skif-ops/rs-zs-bpla/hardware/PCB_MAIN_IPC_CANDIDATE_FOOTPRINTS_REV_A.md

# PCB-MAIN project-controlled IPC candidates — Rev.A

Status: `ROUTING CANDIDATE CONTROLLED / ASSEMBLY DFM REQUIRED / NOT FOR MANUFACTURE`

This control removes workstation-library drift from the three package-only
PCB-MAIN instances. It does not claim that a component manufacturer supplied a
land pattern and it does not waive assembly-house DFM, stencil adaptation,
Review B, DRC or physical process validation.

## U2 — W25Q512JVFIQ package F

Winbond W25Q512JV Rev B is the package authority for the 16-pin 300 mil SOIC
with 1.27 mm pitch. Winbond does not publish a complete PCB/stencil pattern for
package F. The project therefore freezes the KiCad IPC gullwing candidate used
by the reviewed placement snapshot:

- project footprint: `Winbond_W25Q512JV_PackageF_IPC_Candidate`;
- pads 1–8 at X = -4.65 mm and pads 9–16 at X = +4.65 mm;
- pad pitch 1.27 mm, pad size 2.05 x 0.60 mm, R0.15 corners;
- copper, mask and nominal paste are coextensive in the candidate;
- source disposition: `PROJECT_IPC_W25Q512JV_F_KICAD_GULLWING_ASSEMBLER_DFM_REQUIRED`.

Before fabrication release, the selected assembler must check heel/toe/side
allowance against the ordered package tolerance, choose solder-mask expansion
and approve the stencil aperture for the actual paste and stencil thickness.

## U25/U26 — TPD2EUSB30DRTR package DRT0003A

TI `MPDS340` is the package-outline authority. The official TPD2EUSB30 product
data identifies the active-production DRT/SOT-9X3 orderable and requires a
low-stub flow-through USB layout, but the package drawing does not publish a
complete PCB/stencil pattern. The project freezes the reviewed KiCad DRT-3
candidate:

- project footprint: `TI_DRT0003A_IPC_Candidate`;
- pads 1/2 at (-0.35, +0.425)/(+0.35, +0.425) mm;
- ground pad 3 at (0, -0.425) mm;
- all three pads 0.30 x 0.30 mm with R0.075 corners;
- copper, mask and nominal paste are coextensive in the candidate;
- source disposition: `PROJECT_IPC_TI_DRT0003A_KICAD_DRT3_ASSEMBLER_DFM_REQUIRED`.

Before fabrication release, the selected assembler must approve mask and
stencil rules at its minimum feature capability. Review B must additionally
confirm direct flow-through placement, no branch stub, continuous reference
plane and post-route USB differential-impedance/SI evidence.

## Reproducibility and release interlock

The two project files are generated by
`tools/generate_pcb_main_manufacturer_footprints_rev_a.py` and materialized into
the native board by
`tools/materialize_pcb_main_manufacturer_footprints_rev_a.py`. The independent
layout audit checks every pad coordinate, size, layer and status. Any geometry,
MPN, assembler process or USB routing change reopens this control.
