skif-ops/rs-zs-bpla/hardware/PCB_PWR_FOOTPRINT_AUTHORITY_REV_A.md

# Дионея EVT-PRE-20 Rev.A — PCB-PWR footprint authority

Status: `J1/U1/U2/Q1/RSH1/U3/U4/L1/L2/U5 MANUFACTURER LAND/HOLE/STENCIL VERIFIED / TP1-TP10 PROJECT DFT GEOMETRY VERIFIED / LAYOUT USE AUTHORIZED / NOT FOR MANUFACTURE`
Date: 2026-09-12
Board: `PCB-PWR`

## Q1 — Texas Instruments CSD18540Q5B

Controlled footprint: `DioneyaPWR:CSD18540Q5B_DNK`

Primary source: TI CSD18540Q5B data sheet SLPS488B Rev.B,
`https://www.ti.com/lit/ds/symlink/csd18540q5b.pdf`, retrieved SHA-256
`2e43c4a2ac82af8a089be0a9e413282326f8d7857254ac07390b458deca854e0`.

The footprint implements section 7.2 Recommended PCB Pattern and section 7.3
Recommended Stencil Pattern. The drawing is interpreted as the PCB copper view shown
by TI: pins 1–4 are the four right-side pads and pins 5–8 are the contiguous drain
land on the left. This agrees with the data-sheet top-view electrical diagram:
pins 1–3 SOURCE, pin 4 GATE, and pins 5–8 DRAIN.

### Copper authority

| Feature | Frozen geometry, mm |
|---|---:|
| Overall X extent | `-3.456 … +3.456` |
| Overall Y extent | `-2.260 … +2.260` |
| Pads 1–4 | `1.372 × 0.710`, pitch `1.270`, center X `+2.770` |
| Drain land overall | `4.440 × 4.520` envelope |
| Drain base | X `-2.866 … +0.984` |
| Drain lead tabs | `0.590 × 0.710`, pitch `1.270`, left edge `-3.456` |

The contiguous drain land is partitioned into touching same-net KiCad pads so all four
electrical numbers 5–8 remain present without changing the manufacturer copper union.

### Stencil authority

| Aperture group | Count | Size, mm | Placement |
|---|---:|---:|---|
| Drain lead edge | 4 | `0.766 × 0.508` | pitch `1.270` |
| Drain center | 8 | `1.294 × 0.746` | two columns; X gap `0.350`, Y gap `0.300` |
| Pins 1–4 | 4 | `1.072 × 0.562` | pitch `1.270` |

All sixteen paste apertures are explicit paste-only pads. Electrical copper pads carry
no implicit full-area paste opening, preventing accidental loss of TI's segmented
stencil pattern.

## U1 - Texas Instruments LM74700QDBVRQ1

Controlled footprint: `DioneyaPWR:TI_DBV0006A_SOT23-6`

Primary source: TI LM74700-Q1 data sheet SNOSD17G Rev.G, package drawing
DBV0006A `4214840/G` dated 08/2024, PDF pages 33-35,
`https://www.ti.com/lit/ds/symlink/lm74700-q1.pdf`, retrieved SHA-256
`e16b3a8c0023201fafa5825436f5f2dd6f885b92b84e65602b3f50d741c58b6f`.

The six copper lands are `1.10 x 0.60 mm` roundrects with `R0.05`, `0.95 mm`
pitch within each three-pad side and `2.60 mm` row-center separation. The preferred
non-solder-mask-defined treatment is implemented with `0.07 mm` mask expansion.
The drawing's stencil design uses the same `1.10 x 0.60 mm` apertures for a
`0.125 mm` stencil, so copper pads retain `F.Paste` directly.

## U2 - Texas Instruments INA226AIDGSR

Controlled footprint: `DioneyaPWR:TI_DGS0010A_VSSOP10`

Primary source: TI INA226 data sheet SBOS547C Rev.C, package drawing DGS0010A
`4221984/A` dated 05/2015, PDF pages 38-40,
`https://www.ti.com/lit/ds/symlink/ina226.pdf`, retrieved SHA-256
`c9b67f886d4a5241a5e070723f7b61867409eeb27eed768b9cdd9cb17e03ca2d`.

The ten copper lands are `1.45 x 0.30 mm` roundrects with `R0.05`, `0.50 mm`
pitch and `4.40 mm` row-center separation. The preferred non-solder-mask-defined
treatment is implemented with `0.05 mm` mask expansion. The drawing's stencil
design uses equal `1.45 x 0.30 mm` apertures for a `0.125 mm` stencil.

## U5 - Texas Instruments TPS7A2018PDBVR

Controlled footprint: `DioneyaMain:TI_DBV0005A_SOT23-5` (shared audited library)

Primary source: TI TPS7A20 data sheet SBVS338H Rev.H, package drawing DBV0005A
`4214839/K` dated 08/2024, PDF pages 56-58,
`https://www.ti.com/lit/ds/symlink/tps7a20.pdf`, retrieved SHA-256
`663a9ff5bca608643e711652cba00e7b8bf955c0993a9b86fa108d24d58b8ddc`.

The five lands use the same `1.10 x 0.60 mm`, `R0.05`, `0.95 mm` pitch and
`2.60 mm` row-center geometry already controlled for PCB-MAIN. PCB-PWR reuses that
single project footprint and independently audits its geometry and U5 binding.

## U3/U4 — Texas Instruments LMR604403SRAKR

Controlled footprint: `DioneyaPWR:LMR60440_RAK0009A`

Primary source: TI LMR60440 data sheet SNAS877, package drawing RAK0009A
`4229353/J` dated 04/2025, pages 35–37,
`https://www.ti.com/lit/ds/symlink/lmr60440.pdf`, retrieved SHA-256
`d2feebeb32432de6f7d7da1e45d0d7dcad01f0ddd14fc1a403941efb2c0387db`.

The footprint implements the drawing's `EXAMPLE BOARD LAYOUT` and `EXAMPLE
STENCIL DESIGN`. Repeated touching KiCad pads with the same electrical number form
the asymmetric L-shaped lands for pins 1, 3, 5 and 8 without altering the specified
copper union. Pin 2 uses the drawing's solder-mask-defined thermal-land treatment.

### Copper and solder-mask authority

| Feature | Frozen geometry, mm |
|---|---:|
| Pin 1 / pin 3 L-land | `0.600 × 0.345` plus `0.250 × 0.695`; centers X `-0.900/-0.725`, Y `±0.9275/±1.1025` |
| Pin 9 / pin 4 | `0.250 × 0.650`; center X `-0.075`, Y `-1.125/+1.125` |
| Pin 8 / pin 5 L-land | `0.300 × 0.550` plus `0.700 × 0.200`; centers X `+0.700/+0.900`, Y `∓1.175/∓1.000` |
| Pin 7 / pin 6 | `0.650 × 0.250`; center X `+0.875`, Y `-0.525/+0.525` |
| Pin 2 metal under mask | `2.500 × 0.550`; center `0,0` |
| Pin 2 mask opening | controlled stepped polygon, X `-1.200 … +1.200`; left height `0.450`, right height `0.300` |
| Other mask openings | explicit `0.050` expansion around copper |

### Stencil authority

| Aperture group | Count | Geometry, mm |
|---|---:|---:|
| Pin 1 / pin 3 L-land | 4 | `0.560 × 0.345` and `0.210 × 0.695` per L-land |
| Pin 2 thermal land | 2 | `1.100 × 0.410` and `1.100 × 0.300` |
| Pins 4–9 other than L-land split portions | implicit per the TI stencil outline | same as controlled copper pad |

The controlled footprint contains 13 numbered copper primitives, one explicit
paste-free thermal copper land, one custom mask aperture and six explicit paste-only
apertures: 20 KiCad pad/aperture objects in total. Optional thermal vias shown by TI
are deliberately excluded until placement and stack-up are fixed in PCB-PWR Review B.

## J1 - Molex 43045-0213

Controlled footprint: `DioneyaPWR:Molex_43045-0213_MicroFit-2_Vertical`

Primary source: Molex customer drawing SD-43045-005 Rev.G1 dated 2016-08-23,
`https://www.molex.com/content/dam/molex/molex-dot-com/products/automated/en-us/salesdrawingpdf/430/43045/430450213_sd.pdf`,
retrieved SHA-256
`85db6fbcbbd05643bfebded1b14e02911930151d0234b130d3711ee5fde78ec7`.

The exact orderable 43045-0213 is the two-circuit, vertical, through-hole,
gold-contact member of finish column B. The component-side hole field is:

| Feature | Frozen geometry, mm |
|---|---:|
| Circuit 1 | center `(0, 3.00)`, drill `1.02` |
| Circuit 2 | center `(0, 0)`, drill `1.02` |
| Possible polarization pegs | centers `(-3.00, 0)` and `(+3.00, 0)`, NPTH drill `0.94` |
| Contact copper lands | project annulus `1.50` diameter around the manufacturer drill |

Both peg holes are mandatory because Molex note 2 permits assemblies with either one
or both pegs. The manufacturer drawing controls the hole field and 1.57 mm recommended
board thickness. The 1.50 mm contact land diameter is the project fabrication rule,
not a Molex-specified annulus. Final connector orientation, service clearance and
pull/thermal test remain under `DIM-003` and Review B.

## RSH1 - Vishay Dale WSK2512R0100FEA

Controlled footprint: `DioneyaPWR:Vishay_WSK2512_4T_T1.19mm`

Primary source: Vishay WSK2512 data sheet document 30108 Rev. 11-Dec-2023,
`https://www.vishay.com/doc/?30108=`, retrieved SHA-256
`2ee8a9067539bd2cabb08845219bac55d506b1ca892a2dbaeed343dd1ed10cff`.

The selected 10 mOhm part is a true four-terminal, 1 W, 1%, +/-35 ppm/C
Power Metal Strip shunt. The footprint implements the current land-pattern row for
0.005...0.2 Ohm: `a=2.29`, `b=3.30`, `c=0.76`, `d=0.51`, `e=1.70`, `l=3.68 mm`.

| Project pad | Role | Center, mm | Size, mm |
|---|---|---:|---:|
| 1 | source current | `(-2.985, -0.635)` | `2.29 x 2.03` |
| 2 | load current | `(+2.985, +0.635)` | `2.29 x 2.03` |
| 3 | source Kelvin sense | `(-3.280, +1.270)` | `1.70 x 0.76` |
| 4 | load Kelvin sense | `(+3.280, -1.270)` | `1.70 x 0.76` |

At 5 A the shunt produces 50 mV and dissipates 0.25 W, so the 1 W rating provides
the required 4x nominal power margin. Sense traces must leave pads 3/4 independently;
Kelvin routing, copper current density, +70 C temperature rise and reference-meter
calibration remain Review-B controls.

## L1/L2 - Coilcraft XAL7030-472MEC

Controlled footprint: `DioneyaPWR:Coilcraft_XAL7030_472`

Primary source: Coilcraft XAL7030 data sheet document 863, document 863-2 revised
02/25/26, `https://www.coilcraft.com/pdfs/xal7030.pdf`, retrieved SHA-256
`c323552b4c1acd5ad94d13c32783d1d7db3f86ab70a1c58431673aebb96be9f6`.

The selected AEC-Q200 shielded inductor is 4.7 uH +/-20%, DCR 26.1 mOhm typical /
30.0 mOhm maximum, Isat 10.1 A and Irms 6.9 A for 20 C rise. For dash number
`-472`, Coilcraft specifies a 1.40 mm terminal and a 1.58 mm land-pattern width.
The recommended land pattern is two `1.58 x 6.50 mm` pads with `2.94 mm` inner gap,
giving centers at `x=+/-2.26 mm`.

Project pad 1 is the marked start/short lead and is bound to each LMR60440 SW node,
following Coilcraft's lowest-EMI orientation guidance. At 14.6 V / 400 kHz, the
calculated 4 A full-load peaks are about 4.75 A (3.8 V rail) and 4.68 A (3.3 V rail),
both below the 10.1 A saturation rating. Maximum-DCR winding loss is 0.48 W at 4 A;
placement, hot-loop geometry, +70 C thermal evidence, load-step and EMI remain open.

## TP1-TP10 - project DFT probe target

Controlled footprint: `DioneyaPWR:TestPoint_DFT_1.7mm_NoPaste`

Primary source: project PCB-PWR DFT authority. The footprint contains one circular
`1.70 mm` copper target with `0.20 mm` radial solder-mask expansion, producing a
`2.10 mm` opening. It deliberately has no paste aperture and is excluded from BOM and
pick-and-place outputs. The ten schematic instances and their nets are controlled by
`hardware/PCB_PWR_PASSIVE_AUTHORITY_REV_A.csv`; final coordinates, fixture access and
probe-wear validation remain layout/Review-B controls.

## Remaining controls

- TI does not define a Q1 solder-mask expansion in the cited figures; its final mask
  rule remains an assembly-house/DFM control. U3/U4 mask geometry is controlled by
  drawing `4229353/J`.
- U1/U2/U5 use the preferred NSMD option at the maximum expansion shown by their TI
  package drawings. Final solder-mask registration and stencil process capability
  remain assembly-house/DFM controls.
- Drain thermal spreading, via field, current density, gate-loop placement and SOA are
  PCB-PWR layout/Review-B controls.
- J1/U1/U2/Q1/RSH1/U3/U4/L1/L2/U5 and TP1-TP10 placement is not authorized until
  `PCB-PWR.kicad_pcb` is created from the reviewed board outline and mechanical authority.
- Manufacturing release remains blocked until layout DRC, thermal/fault evidence, DFM
  and both review gates pass.
