skif-ops/rs-zs-bpla/hardware/ENVIRONMENT_REV_A.md

# Дионея EVT-PRE-20 Rev.A — environmental baseline

Статус: `LOCKED OPERATING RANGE / TEST EVIDENCE PENDING`
Основание: `DEC-019`.

## 1. Температурный диапазон

- Рабочая температура окружающей среды станции: **−40…+70 °C**.
- Проектный минимальный диапазон хранения изделия: **−40…+70 °C** до уточнения паспортных ограничений конкретной батареи, герметиков, мембран и литейного материала.
- Электронные компоненты, разъёмы и кабельные сборки, находящиеся в температуре корпуса, должны иметь паспортный рабочий диапазон не уже **−40…+85 °C**.
- Компонент с нижней границей выше −40 °C или верхней границей ниже +85 °C не допускается в Rev.A без формального waiver с тепловым/изоляционным обоснованием и отдельным решением.

## 2. Горячий режим +70 °C

Испытание проводится на собранной станции в репрезентативном корпусе при +70 °C ambient. Проверяется worst-case realistic load:

- BG95 передача данных и reconnect/burst;
- GNSS/PPS;
- LoRa профиль RU868;
- BLE service/OTA window;
- запись/чтение NOR и microSD;
- четыре акустических канала, DSP и классификация;
- работа DC/DC PCB-PWR.

Для каждого тепловыделяющего узла фиксируются ambient, case/board temperature, ток, напряжение и оценка junction temperature. Нельзя считать компонент прошедшим только потому, что его datasheet имеет +85 °C предел: необходимо доказать отсутствие превышения внутреннего температурного предела с учетом self-heating.

## 3. Холодный режим −40 °C

После стабилизации изделия при −40 °C проверяются:

- cold boot и повторные power cycles;
- программирование T5838 AAD через `AAD_CFG/THSEL`, AAD wake и переход в полный PDM capture;
- GNSS cold start/PPS и time-trust;
- cellular attach/recovery, если RF fixture позволяет;
- LoRa;
- BLE commissioning;
- NOR/microSD;
- USB service/recovery;
- разъёмы, кабели и отсутствие хрупкого разрушения/потери контакта.

## 4. LiFePO4

Рабочий диапазон станции −40…+70 °C **не означает разрешение заряда LiFePO4 при отрицательной температуре**.

- При температуре элемента ниже 0 °C заряд запрещен по baseline EVT-PRE-20.
- Исключение допускается только для утвержденной батарейной системы с документированным heater/low-temperature charging algorithm и отдельным EVT.
- Разряд/питание станции при низкой температуре допускается только в пределах datasheet выбранной батареи/BMS.
- Температура для charge inhibit должна относиться к элементу/батарейному пакету, а не только к воздуху внутри корпуса.

## 5. Разъемы и кабели

- JST GH MIC connector исключен из Rev.A из-за несоответствия нижней температурной границе проекта.
- Первоначальный 5-contact Pico-Lock также superseded после выявления обязательного T5838 `THSEL` one-wire AAD configuration input.
- MIC Rev.A: Molex Pico-Lock 1.50 mm, **6 circuits**: header `5040500691`, housing `5040510601`, terminal `5040520098`, nominal operating range −40…+105 °C.
- MIC pin 5 = `MIC_WAKE`; pin 6 = shared `AAD_CFG/THSEL`.
- MAIN↔PWR Micro-Fit 3.0 остается допустимым по температуре, но требует pull/current/thermal validation.
- U.FL и готовые coax assemblies выпускаются только после проверки температурного диапазона **всей кабельной сборки**, не только board receptacle.

## 6. Механика и корпуса

Для vacuum casting, 3D-print fallback и будущего injection-molding source package отдельно подтверждаются при −40/+70 °C:

- отсутствие растрескивания, коробления и потери preload;
- работоспособность резьбовых вставок и крепежа;
- сохранение IP-уплотнения и вентиляционной мембраны;
- отсутствие блокировки акустических портов/мембран;
- отсутствие недопустимого изменения RF characteristics;
- кабельные вводы и strain relief.

Материал корпуса нельзя выпустить по одной комнатной FAI-проверке.

## 7. Release gate

Environmental gate считается закрытым только когда:

1. BOM/AVL не содержит деталей с неподходящим температурным диапазоном;
2. `EVT-ENV-COLD`, `EVT-ENV-HOT`, `EVT-ENV-CYCLE`, `EVT-ENV-BATT-COLD` имеют PASS;
3. thermal report содержит реальные температуры и режимы нагрузки;
4. холодный отчет содержит cold-start, `AAD_CFG/THSEL`, WAKE и connector/harness evidence;
5. выбранная батарея/BMS/MPPT имеет подтвержденные температурные правила;
6. изменение компонента, корпуса, кабеля или firmware power profile, влияющее на температуру, инициирует соответствующий retest.
