skif-ops/rs-zs-bpla/hardware/reviews/PCB_MAIN_HIERARCHY_REVIEW_REV_A.md

# PCB-MAIN Rev.A human-readable hierarchy review

Status: `ACCEPTED HIERARCHY ONLY / NOT FOR ROUTING OR MANUFACTURE`

## 1. Scope

This subgate reviews schematic presentation and exact electrical equivalence only.
It does not reopen the signed PCB-MAIN Review A pin/net decision and cannot
authorize PCB routing, fabrication, assembly, Review B or manufacturing release.

Permitted reviewer decision: `ACCEPT_HIERARCHY_ONLY` or `REJECT_HIERARCHY`.

## 2. Controlled candidate

- Pages: 10 A2 landscape sheets — one system overview and nine functional sheets.
- Symbols: 248 total; 247 have physical PCB footprints and `U12` is the logical card.
- PCB pads: 1,066 logical pad numbers and 1,077 physical pad occurrences; seven
  repeated shell-pad numbers on `J6` through `J12` account for 11 additional
  physical occurrences.
- Authority pins: 1,074 total; 905 connected and 169 explicit NC.
- Explicit child-sheet wire stubs: 905.
- Cross-sheet nets: 75 with 168 hierarchical-label participations.
- Root-sheet connection wires: 168.
- Total controlled wire segments: 1,073.
- Pin/net semantic SHA-256:
  `d320bdd98712a65f9736bd520a8f9197d4f53fedb4be3b798086810e7a8f4bf6`.
- Reviewed source commit:
  `9aceca9531f0b9c18679bee1a8050ae7cd94308a` (tree
  `f77848562f0f2c0ff4965ff8474b582cf49b6885`).
- PCB Native Gate
  [#35136239933](https://github.com/skif-ops/rs-zs-bpla/actions/runs/35136239933):
  KiCad `9.0.9`, zero ERC violations on all 10 sheets. Evidence artifact
  [10462359549](https://github.com/skif-ops/rs-zs-bpla/actions/runs/35136239933/artifacts/10462359549),
  ZIP SHA-256
  `8839e26a79f17da3deb342e9e4c5009f4b7eb365a0f04c4cb526f7e5051bc697`.
- ERC JSON SHA-256:
  `d4dc32aa136be917106a4211734ec9ff0e5db903a268a30b4cd4babb004df5c8`.
- Ten-page A2 landscape PDF SHA-256:
  `7e6ef20a989ec66c55b3e1a32de0a914b9e37a6e70cc5835d36f3260b65ff8d9`;
  pages `1/10` through `10/10` were visually checked in order with no clipping
  or visible duplicate root labels.
- CI [#35136240003](https://github.com/skif-ops/rs-zs-bpla/actions/runs/35136240003):
  `PASS` for the reviewed source commit.
- Routing authorized: `false`.
- Manufacturing release: `false`.

## 3. Functional sheets

1. Power entry and rail interface.
2. MCU clocks, reset and straps.
3. PDM audio, AAD and microphone harnesses.
4. GNSS timing, antenna and supervisor.
5. Cellular modem, dual SIM and recovery.
6. LoRa radio control and conducted RF.
7. BLE module, reset, DFU and SWD.
8. Storage, sensors, microSD and tamper.
9. USB service, debug and EOL fixture.

## 4. Machine controls

- [x] Deterministic regeneration of root and all nine child sheets.
- [x] Root-sheet spatial traversal controls KiCad PDF order as pages 1 through 10,
  with short title-block labels bounded inside the printable frame.
- [x] Exact RefDes allocation: every symbol appears once and only once.
- [x] Exact authority pin/net equivalence and explicit NC preservation.
- [x] Exact schematic-to-PCB pad/net comparison for every physical pad, including
  all 11 duplicated shell solder occurrences.
- [x] Release boundary keeps routing and manufacture prohibited.
- [x] Commit-bound KiCad 9 ERC: zero violations on all 10 sheets.
- [x] Commit-bound 10-page A2 schematic PDF archived and visually inspected.
- [x] Source commit SHA, tree SHA, artifact digest, ERC SHA-256 and PDF SHA-256 recorded.
- [x] Independent human hierarchy decision recorded.

## 5. Human review

Reviewer: `Скиф`

Date: `2026-09-16`

Source commit SHA: `9aceca9531f0b9c18679bee1a8050ae7cd94308a`

Reviewed PDF SHA-256: `7e6ef20a989ec66c55b3e1a32de0a914b9e37a6e70cc5835d36f3260b65ff8d9`

Decision: `ACCEPT_HIERARCHY_ONLY`

The decision accepts only the human-readable hierarchy and its exact electrical
equivalence to the retained Review-A pin/net authority. It does not authorize
routing, fabrication, assembly, Review B or manufacturing release.

## 6. Retained blockers

Routing, planes, numeric impedance geometry, native board DRC, STEP/enclosure
clearance, CAM comparison, fabricator stackup acceptance, assembler DFM/stencil
acceptance, Review B and physical EVT remain open.
