skif-ops/rs-zs-bpla/hardware/reviews/PCB_MIC_REVIEW_B_COPPER_RETURN_REV_A.md

# PCB-MIC Rev.A Review B copper-return and decoupling packet

Status: `ECO REQUIRED HISTORY PRESERVED / COPPER RETURN ACCEPTED / REVIEW B OPEN / NOT FOR MANUFACTURE`

This packet records the independent copper-return decision, preserves the baseline
evidence that caused the hold, and defines the bounded PCB-MIC copper ECO. Repeat
Review A is signed against the controlled ECO source and evidence, and the independent
copper-return subgate is accepted. This does not complete Review B or grant
manufacturing release.

## Controlled decision binding

| Item | Controlled value |
|---|---|
| Superseded signed Review-A commit | `3e215e26e0d4cb160b309de3d3fd5a3145a756bf` |
| Superseded native PCB SHA-256 | `aecd1a374b5f66d32a5ae056eb4ad452d68e2a2391e65f6068acc8cad37f2295` |
| Copper decision evidence commit | `cb69c0bbc1457b498ee4f44ee7da1d566033c23f` |
| PCB Native Gate | [run #158](https://github.com/skif-ops/rs-zs-bpla/actions/runs/34840246015) |
| CI | [run #428](https://github.com/skif-ops/rs-zs-bpla/actions/runs/34840245983) |
| Artifact | ID `10345408977`, SHA-256 `f535c183a3feda6b4e2d38a636987b30aacaa0767103bec39379fbf042d95664` |
| Independent measurement | `tools/audit_pcb_mic_copper_return_rev_a.py` |
| Reviewer | `Скиф` |
| Date | `14.09.2026` |
| Decision | `ECO_REQUIRED` |

The decision evidence verified all 62 manifest entries, 10 controlled source hashes
and 27 PCB-MIC output hashes. The vector F.Cu and B.Cu drawings were board-sized,
distinct and bound to the source hash above.

## Baseline blocking finding PCB-MIC-RB-CU-001

The signed baseline source contained a B.Cu GND zone named
`PCB_MIC_BCU_GND_REFERENCE` with zero cached filled polygons. Its KiCad 9.0.9 B.Cu
Gerber contained zero GND regions and only the five explicit GND conductor draws.
The emitted fabrication copper therefore used the long explicit backbone, not the
named zone.

| Baseline routed path | Trace length | Vias | Minimum width |
|---|---:|---:|---:|
| C1.1 to MK1.7 local VDD leg | 1.658011 mm | 0 | 0.300 mm |
| C1.2 to MK1.2 explicit GND return | 22.248973 mm | 2 | 0.160 mm |
| Complete decoupling loop | 23.906984 mm | 2 return vias | 0.160 mm |

Disposition recorded by the reviewer: `ECO_REQUIRED`.

- [x] Inspect the commit-bound F.Cu/B.Cu drawings and machine topology report.
- [x] Confirm that the absent B.Cu region is not intended fabrication copper.
- [x] Reject implicit acceptance based only on zero DRC or connectivity.
- [x] Select `ECO_REQUIRED` and reopen Review A for changed PCB bytes.

## Bounded ECO candidate

The ECO preserves placement, schematic, mechanical outline, holes, component set,
net assignments, via count and signal routing. It changes only the controlled GND
copper model:

1. Remove the non-materialized B.Cu zone from the native board and production generator.
2. Remove the remote B.Cu C1 branch from `(15.25, 13.25)` to `(9.00, 13.25)`.
3. Add one explicit 0.50 mm B.Cu local return from the C1 GND via at
   `(15.25, 13.25)` directly to the microphone-return via at `(15.00, 16.65)`.
4. Generate the board directly with `tools/generate_pcb_mic_clean_rev_a.py`; the
   obsolete zone-fill bypass wrapper is removed.

The local standard-library audit produces these candidate measurements before the
commit-bound KiCad run:

| ECO candidate routed path | Trace length | Vias | Layer length |
|---|---:|---:|---|
| J1.1 to C1.1 supply feed | 15.369931 mm | 2 | F.Cu 3.984774 mm; B.Cu 11.385157 mm |
| C1.1 to MK1.7 local VDD leg | 1.658011 mm | 0 | F.Cu 1.658011 mm |
| C1.2 to MK1.2 explicit GND return | 7.108150 mm | 2 | F.Cu 3.698972 mm; B.Cu 3.409178 mm |
| Complete decoupling loop | 8.766161 mm | 2 return vias | Reduction 15.140823 mm |
| J1.2 to MK1.2 connector return | 28.303419 mm | 2 | F.Cu 3.953418 mm; B.Cu 24.350001 mm |

Geometry checks calculate at least `0.802865 mm` copper-edge clearance from the new
segment to other-net B.Cu copper, against the project `0.2 mm` clearance, and
`2.35 mm` from the new segment edge to the acoustic-hole edge. KiCad 9 DRC and CAM
remain mandatory independent controls.

The project still has no frozen normative maximum for the decoupling loop. These
measurements prove the bounded topology change and regression, but cannot self-sign
Review A or Review B.

## ECO candidate commit-bound evidence

| Item | Controlled value |
|---|---|
| Design commit | `159068f2743904fc366a4a65ede5fee829797ed2` |
| Native PCB SHA-256 | `a292a6ec2be555519a4fcc44f3d6cfdf0bc38a7f214caff6e71786942e3e4031` |
| PCB Native Gate | [run #160](https://github.com/skif-ops/rs-zs-bpla/actions/runs/34850294515), `success` |
| CI | [run #430](https://github.com/skif-ops/rs-zs-bpla/actions/runs/34850294478), `success` |
| Artifact | [ID 10350416547](https://github.com/skif-ops/rs-zs-bpla/actions/runs/34850294515/artifacts/10350416547) |
| Artifact SHA-256 | `cc32b9f7327d9c1c8870c68f70419f96aa83b412973b2d7cde9ded711fb9f31d` |
| KiCad 9.0.9 | ERC `0`; DRC `0`; unrouted `0`; schematic parity `0` |
| Archive verification | 62 manifest entries; 12 controlled source hashes; 27 PCB-MIC output hashes |
| Review-B preflight SHA-256 | `5b5b392aa2c16c731d51a04531d82205e2bb83e12d73b43e8dacf58c647502b6` |
| Copper audit SHA-256 | `05fd68dcfe1f7f65df306e30772ffb253ee4f0cb5b56df00e03020d9e4d1c6b9` |
| F.Cu / B.Cu SVG SHA-256 | `49d0cc972078861b5e790788bc9c36c6c84cf1ab98eec70e93949be74253a20c` / `71f6100685f32c91a9eff8ff784ce6a5e1735044282ce4d80691b32101bfe3ed` |

Independent archive verification matched the GitHub artifact digest, all manifest
entries and both nested source/output hash sets. Regenerating the Review-B preflight
from the extracted artifact produced byte-identical JSON. The B.Cu Gerber contains
zero GND regions and five explicit GND draws, matching the explicit-routing-only
source model.

## Repeat Review A signature

| Item | Controlled value |
|---|---|
| Reviewer | `Скиф` |
| Date | `14.09.2026` |
| Decision | `PASS` |
| Reviewed controlled evidence commit | `e17a86bc78ba979f74c5549b378e94f7f3447fe4` |
| Approved native PCB SHA-256 | `a292a6ec2be555519a4fcc44f3d6cfdf0bc38a7f214caff6e71786942e3e4031` |
| PCB Native Gate | [run #161](https://github.com/skif-ops/rs-zs-bpla/actions/runs/34851983013), `success` |
| CI | [run #431](https://github.com/skif-ops/rs-zs-bpla/actions/runs/34851982915), `success` |
| Artifact | [ID 10350269024](https://github.com/skif-ops/rs-zs-bpla/actions/runs/34851983013/artifacts/10350269024) |
| Artifact SHA-256 | `c54b6669b40fa4de3cd3b0515e4bdb742d90f4ab6f40a789eb1f7bb82dfd19ba` |

The repeat signature accepts the bounded PCB source for Review A. The independent
Review-B copper-return acceptance is recorded below; all other Review-B and external
manufacturing gates remain open.

## Copper-return decision-input evidence

| Item | Controlled value |
|---|---|
| Decision-input evidence commit | `7aeec13aa0c7ba1b3cd9095b800c6d08755912a3` |
| PCB Native Gate | [run #163](https://github.com/skif-ops/rs-zs-bpla/actions/runs/34873892890), `success` |
| CI | [run #433](https://github.com/skif-ops/rs-zs-bpla/actions/runs/34873892866), `success` |
| Artifact | [ID 10360925100](https://github.com/skif-ops/rs-zs-bpla/actions/runs/34873892890/artifacts/10360925100) |
| Artifact SHA-256 | `1986effdd10fdef86d97ffecb139dd7beea13ff699adeff8f481440e74630321` |
| Manifest / source / output verification | `62 / 12 / 27`, no mismatch |
| Review-B preflight | `PASS_INTERNAL_CAM_PREFLIGHT_REVIEW_B_REMAINS_OPEN` |
| Copper disposition | `READY_FOR_INDEPENDENT_HUMAN_COPPER_RETURN_REVIEW` |
| Review-B preflight SHA-256 | `48eb46975dfb5d474332aed3348eb48a001e6d828eb451316673cd1c9e584173` |
| Copper audit SHA-256 | `1641b5eb173698febd57b074d6e2f9dfc85418dadbdae6ca5e59e67e500befd7` |
| Manifest SHA-256 | `696fc45c6982c45780912e2e310882e21d863ff3624d6b2304b74b03a4b7e635` |
| F.Cu / B.Cu SVG SHA-256 | `5e4116ccb976c16d610fbf0d4dc0488836e7b5f91157bdb6560fd55c259f4994` / `3967d710d9523a33bd513ce7bef4799289ddbecda6d2663deedfce7a3cef1f07` |

The direct return is explicit in both source and CAM, the return is reduced by
`15.140823 mm`, the local B.Cu segment is `0.50 mm` wide, other-net copper-edge
clearance is `0.802865 mm` against the `0.2 mm` project rule, and KiCad 9.0.9 reports
zero ERC, DRC, unrouted or schematic-parity findings. Reviewer `Скиф` accepted this
bounded copper-return subgate on `14.09.2026` with decision `ACCEPT_COPPER_RETURN`.

## Post-acceptance commit-bound evidence

| Item | Controlled value |
|---|---|
| Acceptance-state commit | `8aa4a3d21b55956625db643e22436f248f75b258` |
| PCB Native Gate | [run #164](https://github.com/skif-ops/rs-zs-bpla/actions/runs/34878120514), `success` |
| CI | [run #434](https://github.com/skif-ops/rs-zs-bpla/actions/runs/34878120579), `success` |
| Artifact | [ID 10361911939](https://github.com/skif-ops/rs-zs-bpla/actions/runs/34878120514/artifacts/10361911939) |
| Artifact SHA-256 | `960f84ff068ddf881f01008a6844bfbbf7ed8b7f3e1720b73e6dadae11ee863e` |
| Manifest / source / output verification | `62 / 12 / 27`, no mismatch |
| Manifest SHA-256 | `9f8e9c59d60970419370eeb29c2a9d4bb9549a43d2e8a1ea2db28ce482950e59` |
| Review-B preflight SHA-256 | `808779c6957ed8599d5226a94c48a54991806264392509fa1938b48f27056de6` |
| Copper audit SHA-256 | `9fee77cc7ac5f697f32234072cdc74a2e7c9cda5ccd954bd53ed64ea386e6ab0` |
| F.Cu / B.Cu SVG SHA-256 | `a77ce3b8b3cf09f771284acd68c3accc9b9744e5720af8447927fa128c4e0cc1` / `0020c178abf814ec712cd40bb7dfd7e1e30db928ae6ad373153649b8905830ac` |
| Copper disposition | `PASS_HUMAN_ACCEPTED_COPPER_RETURN_SUBGATE_REVIEW_B_REMAINS_OPEN` |

The extracted archive was independently hashed, and regenerating both JSON audits
from it produced byte-identical results. This evidence confirms the recorded copper
acceptance state only. Panelization, DFM, acoustic-stack, physical-EVT, final Review B
and manufacturing release remain open.

## Required next gates

- [x] Commit and push the ECO candidate as one controlled source set.
- [x] KiCad 9 ERC and DRC pass with zero violations and zero unrouted items.
- [x] Commit-bound Gerber confirms explicit-routing-only B.Cu copper with zero GND regions.
- [x] Updated copper SVGs, topology JSON, CAM reports and SHA-256 manifest are archived.
- [x] Repeat Review A is signed against the ECO candidate commit and its archived evidence.
- [x] Repeat the independent copper-return decision within Review B after Review A closes.
- [ ] Complete the remaining panelization, DFM, acoustic-stack and physical-EVT gates.

## Initial ECO decision signature

- Reviewer: `Скиф`
- Date: `14.09.2026`
- Reviewed evidence commit: `cb69c0bbc1457b498ee4f44ee7da1d566033c23f`
- Workflow and artifact: PCB Native Gate `34840246015`, artifact `10345408977`
- Disposition: `ECO_REQUIRED`
- New Review A complete: `true`, signed separately against commit `e17a86bc78ba979f74c5549b378e94f7f3447fe4`
- Review B complete: `false`
- Manufacturing release: `false`

## Copper-return subgate acceptance signature

- Reviewer: `Скиф`
- Date: `14.09.2026`
- Reviewed evidence commit: `7aeec13aa0c7ba1b3cd9095b800c6d08755912a3`
- Approved native PCB SHA-256: `a292a6ec2be555519a4fcc44f3d6cfdf0bc38a7f214caff6e71786942e3e4031`
- Workflow and artifact: PCB Native Gate `34873892890`, artifact `10360925100`
- Disposition: `ACCEPT_COPPER_RETURN`
- Approval scope: `PCB_MIC_REVIEW_B_COPPER_RETURN_SUBGATE_ONLY`
- Copper-return subgate complete: `true`
- Review B complete: `false`
- Manufacturing release: `false`
