skif-ops/rs-zs-bpla/mechanics/3d_print/DESIGN_RULES.md

# Корпус 3D-print - правила проектирования

Статус: `DRAFT / CAD BLOCKED BY OPEN DIMENSIONS`

- Материал-кандидат: ASA или подтверждённый UV-stable PC/ASA; PLA/PETG не являются автоматическим outdoor release.
- Детали должны помещаться в утверждённый профиль FlashForge Adventurer 5M Pro без неуправляемого масштабирования.
- Стенки-кандидаты 3.0 мм, локально усиливаются рёбрами; окончательно после печати, падения и IP test.
- Наружные резьбы не печатаются как единственное сервисное соединение: применяются термовставки/закладные и нержавеющий крепёж.
- Уплотнение service cover выполняется сменной EPDM/silicone gasket в непрерывном пазу.
- Ориентация печати, supports, seam и shrink compensation фиксируются в 3MF/profile и не остаются на усмотрение оператора.
- Mic pod имеет сменную мембрану, water trap и одинаковый акустический путь для всех четырёх каналов.
- Каждая деталь получает part number, material, revision, mass, print time, orientation и post-processing.

Поставочный комплект: parametric source, STEP, STL, 3MF, printer profile, drawing, assembly BOM, print matrix, inspection form и контрольный STL mesh report.
