skif-ops/rs-zs-bpla/mechanics/injection_molding/DESIGN_RULES.md

# Корпус injection molding - правила проектирования

Статус: `DRAFT / TOOLING NOT AUTHORIZED`

- Конструкция отдельна от 3D-print/vacuum casting и выпускается только после DFM производителя пресс-формы.
- Материал-кандидат: UV-stabilized PC/ASA; exact grade, shrink и colour masterbatch замораживаются вместе.
- Номинальная стенка-кандидат 2.5-3.0 мм, по возможности равномерная; ribs и bosses проектируются как доля основной стенки для снижения sink/warp.
- Draft-кандидат не менее 1.5 degree на нетекстурированных поверхностях; texture требует дополнительного draft по DFM.
- Parting line, gates, ejectors, slides, replaceable inserts и steel-safe dimensions явно показаны в tool drawing.
- Gasket land и acoustic membrane seats не располагаются на неконтролируемой parting flash.
- Tool ownership, cavity count, tool steel, guaranteed shots, maintenance, sampling и change control включаются в контракт.
- T0/T1 samples проходят CMM, material confirmation, assembly, IP, UV/climate, RF и acoustic verification до запуска партии.

Поставочный комплект: parametric CAD, STEP, 2D drawing with GD&T, mold-flow/DFM report, tool specification, control plan, first article report и отдельный корпусной BOM.
