skif-ops/rs-zs-bpla/mechanics/vacuum_casting/DESIGN_RULES.md

# Корпус vacuum casting - правила проектирования

Статус: `DRAFT / CAD BLOCKED BY OPEN DIMENSIONS`

- Конструкция отдельна от FDM и injection molding; master и parting line проектируются под силиконовую форму.
- Материал-кандидат: outdoor polyurethane с подтверждёнными UV, temperature, water absorption и dielectric properties.
- Усадка, draft, feed gates, vents и допустимое число отливок задаются конкретным поставщиком и вносятся в drawing.
- Резьбовые и силовые зоны используют закладные; их фиксация и pull-out проверяются на образце.
- Gasket land, sealing pressure и flatness контролируются после полной post-cure.
- Pigment/coating не должен закрывать маркировку, акустические порты и RF зоны.
- Первый master и первые три отливки проходят размерный отчёт, сборку, IP и acoustic channel match.

Поставочный комплект: master STEP, split/parting drawing, material datasheet, shrink table, inserts, trimming jig, inspection drawing, sample report и отдельный корпусной BOM.
