skif-ops/rs-zs-bpla/releases/evt-pre-20/2026-10-02-rev-d5/Заказ_плат_и_монтаж/03_PCB_MAIN_заказ_с_DFM/01_Изготовление_платы/Сверловка_Excellon/drill_report.txt

Drill report for PCB-MAIN_8L_COMPLETE_105_CANDIDATE_REV_B.kicad_pcb
Created on 2026-09-29T22:29:41

Copper Layer Stackup:
    =============================================================
    L1 :  F.Cu                      front
    L2 :  In1.Cu                    in1
    L3 :  In2.Cu                    in2
    L4 :  In3.Cu                    in3
    L5 :  In4.Cu                    in4
    L6 :  In5.Cu                    in5
    L7 :  In6.Cu                    in6
    L8 :  B.Cu                      back

Drill file 'PCB-MAIN_8L_COMPLETE_105_CANDIDATE_REV_B-PTH.drl' contains
    plated through holes:
    =============================================================
    T1  0.150mm  0.0059"  (274 holes))
    T2  0.300mm  0.0118"  (579 holes))
    T3  0.600mm  0.0236"  (4 holes)  (with 4 slots)
    T4  1.020mm  0.0402"  (12 holes))

    Total plated holes count 869

Drill file 'PCB-MAIN_8L_COMPLETE_105_CANDIDATE_REV_B-NPTH.drl' contains
    unplated through holes:
    =============================================================
    T1  0.650mm  0.0256"  (2 holes))
    T2  1.200mm  0.0472"  (12 holes))
    T3  3.000mm  0.1181"  (2 holes))
    T4  3.200mm  0.1260"  (4 holes))

    Total unplated holes count 20
