skif-ops/rs-zs-bpla/docs/evt-mb/РКД_07_Карта_выводов_WeAct_STM32U585CIU6_v0_7.docx

КАРТА ВЫВОДОВ И ИНТЕРФЕЙСОВ

ЗС-БПЛА.007
Редакция 0.7

Статус: OPEN
РС «Дионея» - EVT-MB
2026

Управляемая копия. Аппаратные результаты не считаются выполненными до заполнения протоколов.

# 1 Область действия

Карта относится только к WeAct STM32U585CIU6 для EVT-MB. Серийная STM32U585VIT6Q получает отдельный BSP и отдельную карту после EVT.

# 2 Выводы MCU

Сигнал | Периферия | Pin | AF | Назначение | Условие
MIC_BCLK | SAI1_A | PA8 | AF13 | 4× I2S BCLK | 22–33 Ω у MCU; общий такт
MIC_WS | SAI1_A | PA9 | AF13 | 4× I2S WS | общая кадровая синхронизация
MIC_PAIR_A | SAI1_A | PA10 | AF13 | MIC1+MIC2 DATA | L/R противоположны
MIC_PAIR_B | SAI1_B | PB5 | AF13 | MIC3+MIC4 DATA | L/R противоположны
BG95_TX | USART1_TX | PB6 | AF7 | BG95 MAIN_RXD | через 3,3/1,8 В translator, если EVB не согласует
BG95_RX | USART1_RX | PB7 | AF7 | BG95 MAIN_TXD | через translator
BG95_PWRKEY | GPIO out | PB1 | OD | BG95 PWRKEY | транзистор/open-drain
BG95_RESET_N | GPIO out | PB4 | OD | BG95 RESET | транзистор/open-drain
BG95_STATUS | GPIO in | PB15 | input | BG95 STATUS | проверить домен уровня
BG95_DTR | GPIO out | PB12 | output | BG95 DTR | сон/пробуждение
GNSS_TX | USART2_TX | PA2 | AF7 | GNSS RXD | 3,3 В
GNSS_RX | USART2_RX | PA3 | AF7 | GNSS TXD | 3,3 В
GNSS_PPS | TIM2_CH2 | PB3 | AF1 | GNSS 1PPS | аппаратный input capture
BLE_TX | USART3_TX | PB10 | AF7 | BLE RXD | 3,3 В
BLE_RX | USART3_RX | PB11 | AF7 | BLE TXD | 3,3 В
SPI1_SCK | SPI1 | PA5 | AF5 | SX1262+microSD | ≤8 МГц EVT; общий bus
SPI1_MISO | SPI1 | PA6 | AF5 | SX1262+microSD | общий bus
SPI1_MOSI | SPI1 | PA7 | AF5 | SX1262+microSD | общий bus
LORA_NSS | GPIO out | PB0 | output | SX1262 NSS | отдельный CS
LORA_DIO1 | GPIO EXTI | PB2 | input | SX1262 DIO1 | IRQ
LORA_BUSY | GPIO in | PB8 | input | SX1262 BUSY | timeout обязателен
LORA_RESET | GPIO out | PB9 | output | SX1262 NRESET | активный 0
SD_NSS | GPIO out | PA4 | output | microSD CS | FAT32, карта 32 ГБ
I2C_SCL | I2C2 | PB13 | AF4 | INA226+температура | pull-up 3,3 В
I2C_SDA | I2C2 | PB14 | AF4 | INA226+температура | pull-up 3,3 В
SWDIO | SWD | PA13 | AF0 | ST-Link | не переназначать
SWCLK | SWD | PA14 | AF0 | ST-Link | не переназначать

# 3 Зарезервированные выводы

- PA0 - USER KEY платы; PC13 - USER LED.
- PA11/PA12 - USB FS service/DFU.
- PA13/PA14 - SWD; NRST и VTref всегда доступны.
- USART1 hardware flow control не используется; modem получает AT+IFC=0.

# 4 CubeMX freeze

Периферия | Режим | Параметры
SAI1_A | Master RX | 32 kHz; stereo; 32-bit slot; 24-bit data; DMA circular
SAI1_B | Synchronous Slave RX | sync SAI1_A; identical frame; DMA circular
TIM2 CH2 | Input capture | PB3 rising edge; 32-bit counter
USART1 | Async | 115200 8N1; no flow control; RX circular/IDLE
USART2 | Async | 9600 8N1; RX circular/IDLE
USART3 | Async | 115200 8N1
SPI1 | Full duplex master | mode 0; ≤8 MHz; DMA optional
I2C2 | I2C | 400 kHz; external pull-ups

# Источники и проверка

STM32U585 datasheet AF tables: https://www.st.com/resource/en/datasheet/stm32u585ai.pdf

WeAct board files: https://github.com/WeActStudio/WeActStudio.STM32U585Cx_CoreBoard

ЗС-БПЛА.007 · 0.7 · OPEN
