skif-ops/rs-zs-bpla/releases/evt-pre-20/2026-10-02-rev-d5/Программа_EVT_и_Мухоед/01_Программы_и_формы/Форма_сводного_отчета_EVT.docx

# Форма сводного отчета EVT PRE 20

Дионея · EVT-PRE-20 · 30 сентября 2026 года · Rev D · комплект для закупки, производства и EVT

Форма заполняется после фактических испытаний первого лота. Поля без первичного измерения остаются NOT RUN. Никакие приведённые в программе планы не переносятся в итоговый PASS автоматически.

## Конфигурация

Номер лота: __________. Дата начала и окончания: __________. Ответственный: __________. Ревизии PCB-MAIN, PCB-PWR, PCB-MIC и печатного корпуса: __________. Фактические стеки и ответ фабрики по 76/76 POFV: __________. Хеши firmware, серверной модели и манифеста файлов: __________.

Серийные номера 20 изделий и назначения опытных/разрушающих образцов приводятся в электронном реестре. Любое отступление от BOM, жгута, корпуса и профиля RU868 указывается отдельной записью ECO или deviation.

## Результаты

Сводка EOL: проверено ___ из 20; PASS ___; FAIL ___; NOT RUN ___. Сводка EVT по P0: проверено ___; PASS ___; CONDITIONAL ___; FAIL ___; NOT RUN ___. Ссылки на сырые логи и SHA-256: __________.

Питание, RB40, MPPT и солнечная панель: __________. Четыре PDM канала и порт PCB-MIC: __________. Три антенных тракта и PCB-MAIN RF без контролируемого импеданса: __________. GNSS/PPS и локализация: __________. LTE/TLS, RU868, BLE и store-and-forward: __________. Температура, влажность, IP, вибрация и акустика: __________.

## Отклонения и решение

Открытые blocker/critical: __________. Принятые CONDITIONAL отклонения, владелец и срок: __________. Нерешённые входные данные заказчика: __________. Повтор критических проверок после стресса: __________.

Итоговое решение независимого проверяющего: PASS / CONDITIONAL / FAIL / NOT RUN. Имя, дата, подпись и ссылка на полный evidence manifest: __________.
