skif-ops/rs-zs-bpla/releases/evt-pre-20/2026-10-02-rev-d5/Заказ_плат_и_монтаж/00_Условия_передачи/Опись_и_статус_комплекта.docx

# Опись и статус производственного комплекта EVT-PRE-20

Дионея · EVT-PRE-20 · 30 сентября 2026 года · Rev D

Финальный комплект Rev D для закупки, изготовления плат, монтажа и сборки опытной партии.

## Статус плат

PCB-MAIN: разводка завершена, DRC 0, unconnected 0, ERC 0; выпуск зависит от DFM и подтверждения фабричного stack ID.

PCB-PWR: заказ разрешён заказчиком с обязательной заводской проверкой стека и переходных отверстий.

PCB-MIC Rev B: плата технически принята Review B, DRC/ERC/unconnected 0/0/0, SHA-256 c57cebbb3886247166551fd242fa51350bc9be7fee6299e63e7eaac60518d518. По требованию заказчика все 80 PCBA изготавливаются без паузы; образец выбирается из готовой партии для контроля порта и PDM.

## Состав

Архив плат содержит Gerber, отдельную сверловку, IPC-356, координаты, BOM, KiCad-исходники, PDF схемы/сборки и задания. Полный архив дополнительно содержит закупочную книгу для 41 станции, документы сборки, предварительные модели корпусов, технический проект и отдельные архивы.

Программа EVT и материалы дообучения «Мухоеда» находятся в отдельном архиве. Полный пакет Review B PCB-MIC находится в отдельном архиве и не входит в производственный архив.

## Ограничения первого выпуска

Первая партия корпусов – 20 комплектов 3D-печати; модели предварительные и требуют примерки. Литьевые файлы являются исходными кандидатами для DFM оснастки.

Оценочные цены взяты из ведомости v.02 и не являются коммерческим предложением. Недетализированная сумма около 4 млн ₽ исключена. Перед закупкой получить текущие котировки.

Физические акустические, климатические, RF и корпусные проверки выполняются на собранных изделиях по программе EVT и не блокируют передачу утверждённых файлов фабрике.
