skif-ops/rs-zs-bpla/releases/evt-pre-20/2026-10-02-rev-d5/Заказ_плат_и_монтаж/01_PCB_PWR_заводская_проверка_и_заказ/PCB-PWR_parity_disposition.docx

# PCB-PWR Rev E – диспозиция диагностики схемы

Дионея · EVT-PRE-20 · 30 сентября 2026 года · Rev D

Документ фиксирует разбор 251 диагностического сообщения и производственную трактовку BOM/DNP для Rev D. Физических расхождений связности не обнаружено.

## Итог проверки

171 сообщение относится к разной записи иерархических имён одной и той же цепи; одно сообщение относится к ожидаемому NC выводу U5. Эти записи не меняют связность.

62 сообщения относятся к пустому полю Datasheet на плате; 10 – к различию подробного Value схемы и короткого значения платы. Точные производственные MPN заданы в PCB-PWR_BOM_PCBA.csv и книге BOM XLSX.

Семь сообщений exclude_from_BOM относятся к пяти DNP резисторам и трём медным net tie; часть сообщений объединена по группам. Их производственная диспозиция дана отдельным CSV.

## Правила монтажа

Установить 44 позиции из PCB-PWR_BOM_PCBA.csv по PCB-PWR_pos.csv и двуязычной сборочной схеме. R5, R9, R13, R14 и R15 не устанавливать и не закупать как детали.

NT1, NT2 и NT3 являются рисунком меди платы; отдельные перемычки или компоненты не устанавливаются и не закупаются. TP1–TP10 и H1–H4 также являются элементами печатной платы.

D1 применять как Littelfuse SMBJ18A, однонаправленный TVS. Физическая проверка импульсного режима выполняется в EVT и не разрешает замену MPN без ECO.

## Статус

Диагностика schematic parity закрыта диспозицией для передачи в производство. Фабричный DFM, фактический stack ID, контроль первого изделия и последующие электрические/тепловые испытания выполняются по заданию на платы.

EN: schematic parity diagnostics are dispositioned for manufacturing handoff. Use the exact PCBA BOM, DNP list, position file and bilingual assembly drawing. Fabricator DFM, stack confirmation and post-lot sample tests remain mandatory production controls.
