skif-ops/rs-zs-bpla/releases/evt-pre-20/2026-10-02-rev-d5/Основной_пакет/00_Опись_и_статус/Контроль_финального_выпуска.docx

# Контроль финального выпуска EVT-PRE-20 Rev D

Дионея · EVT-PRE-20 · 30 сентября 2026 года · Rev D

Контрольный лист фиксирует состояние перед передачей закупке и производству.

## Выполнено

PCB-MAIN: DRC 0, незавершённые соединения 0, ERC 0; машинные файлы и исходники включены.

PCB-MIC Rev B: исправлены метки сверления и кольцо MK1, DRC/ERC/unconnected 0/0/0, точные MPN, отдельные PTH/NPTH. Техническое решение Review B подписано; его условие о паузе после первого изделия изменено заказчиком в извещении о единой партии.

PCB-PWR: файлы заказа и DFM включены. Производственный BOM в XLSX/CSV и закупочная сводка для 41 станции включены. Документы и PDF-инструкции для людей выпущены на русском и английском, где это требуется для фабрики.

## Контроль заказа

PCB-MAIN 22, PCB-PWR 22 и PCB-MIC 80 PCBA заказываются и изготавливаются полными партиями без паузы. После изготовления выбрать образцы для углублённого контроля в соответствии с извещением. До панели получить официальный stack ID, DFM и подтверждение 76 POFV PCB-MAIN. Любое изменение файлов оформить ECO.

Корпуса и литьевые модели предварительные; выполнить first article fit, проверку прочности, герметизации и акустики до размножения.

## Решение

Комплект Rev D разрешён к передаче на закупку и производство в указанных управляемых границах. Rev C изъять из обращения.
