skif-ops/rs-zs-bpla/releases/evt-pre-20/2026-10-02-rev-d5/Заказ_плат_и_монтаж/03_PCB_MAIN_заказ_с_DFM/01_Изготовление_платы/PCB-MAIN_Официальная_проверка_JLCPCB_RU_EN.docx

# PCB-MAIN Rev B – проверка по официальным данным JLCPCB

EVT-PRE-20 · 30.09.2026 · плата SHA-256 f828fc6b30afbd64ed67afbee9ed7a5f5cdb9c47c1112722c5a0fe315268665f

# Вывод

Опубликованные возможности JLCPCB покрывают заказной базис: 8 слоёв, 1,6 мм, FR-4, ENIG, 1 oz наружной и 0,5 oz внутренней меди, переходы 0,15/0,25 мм, эпоксидное заполнение с медной крышкой. Это проверка возможностей, а не утверждённый производственный файл конкретного заказа.

# Переходы

На плате 853 перехода. В исходном KiCad 74 помечены filling=yes и capping=yes: 57 внутри SMD-площадок и 17 вне их. Заказной CSV содержит 76 точек: к этим 74 добавлены C6.1 (X41,75 Y30,40) и D11.1 (X80,01 Y20,50), частично попадающие в окна пасты. Для двух добавленных точек также требуется заполнение эпоксидом и медное закрытие. Сверло этих двух переходов 0,15 мм, диаметр 0,25 мм. Выбирать обработку только по диаметру нельзя.

# Порядок заказа

Выбрать 8 слоёв, 1,6 мм, ENIG, наружная медь 1 oz, внутренняя 0,5 oz.

Выбрать опцию минимального перехода 0,15/0,25 мм и процесс POFV: эпоксидное заполнение с медной крышкой.

Передать фабрике заказные CSV и карту 76 переходов. Из них 74 имеют признаки в исходной плате, а C6.1 и D11.1 заданы как CAM-дополнение. Фабрика подтверждает обработку 76 из 76 точек до запуска панели; одно лишь закрытие маской не допускается. При невозможности выборочного POFV изменение согласовать через ECO.

Выбрать стек JLC08161H-3313, если он доступен в заказе, и проверить его действующие толщины/параметры в карточке заказа; при замене стека фиксировать ECO.

Запросить подтверждение производственных файлов до запуска панели и оформить замечания DFM через ECO.

# Границы заключения

JLC08161H-3313 является примером, а не утверждённым стеком заказа. Для EVT сохраняется текущая трассировка без заказа контролируемого импеданса и цели 50 Ом. Фактический стек записывается при DFM. Все 22 PCBA изготавливаются без паузы; два образца из партии проходят ВЧ-испытания. Файлы фабрики проверяются до запуска панели.

EN: JLCPCB publishes the required board and filled-via capabilities. Confirm 76/76 vias before panel release. The EVT PCB stays as routed; controlled impedance and a 50-ohm target are not ordered. Record the chosen stack. Make all 22 PCBAs without a pause; sample two from the completed lot for RF tests. Deviations require lot disposition and ECO.

# Официальные источники / Official sources

Возможности плат (https://jlcpcb.com/capabilities/pcb-capabilities/) | Стек (https://jlcpcb.com/help/article/multi-layer-pcb-standard-laminated-structures) | Переходные отверстия (https://jlcpcb.com/help/article/pcb-via-covering) | 8 слоёв (https://jlcpcb.com/blog/multilayer-pcb-design-guidelines)
