skif-ops/rs-zs-bpla/releases/evt-pre-20/2026-10-02-rev-d5/Заказ_жгутов_и_кабелей/Антенные_тракты_RU_EN.pdf

# Антенные тракты EVT-PRE-20 Rev D / Antenna paths

22 комплекта / sets · 66 CAB.0243 · по 22 антенны каждого типа / 22 antennas of each type

AA.166.A.301111 · SMA(M) · active GNSS · IP67

TI.89.B.2111W · SMA(M) · 860–930 MHz · IP67

### Не менять местами J8/J9/J10 · Do not interchange J8/J9/J10

100%: continuity, no short, connector retention, bulkhead seal, labels, bend radius; then installed VSWR/sensitivity/coexistence tests.

100%: проводимость, отсутствие КЗ, фиксация разъёмов, уплотнение bulkhead, маркировка, радиус изгиба; затем VSWR/чувствительность/coexistence.
