skif-ops/rs-zs-bpla/releases/evt-pre-20/2026-10-02-rev-d5/Заказ_жгутов_и_кабелей/Чертеж_и_распайка_жгутов_RU_EN.pdf

# EVT-PRE-20 Rev D — чертёж и заказ жгутов / Harness drawing and order

Заказ / Order: 22 полных комплекта / complete sets · 30.09.2026 · DIO-HARNESS-SET-EVT-D

# 1. Состав заказа / Order scope

Жгут / Harness | Кол-во / Qty | Цепей / Circuits | Нарезка / Cut | Окончание A / End A | Окончание B / End B
H-MIC1…H-MIC4 | 88 | 6 | 275 ±5 мм | Molex 5040510601 + 5040520098 | Molex 5040510601 + 5040520098
H-MAIN-PWR | 22 | 12 | 440 ±5 мм | Molex 430251200 | Molex 430251200
H-BAT-PWR | 22 | 2 | 330 ±5 мм | TE 8-34114-1 M8 | Molex 430250200 + 430300038

# 2. Обязательные правила / Mandatory rules

Собрать один полный первый комплект, зафиксировать высоту обжима и разрушающее усилие для каждого типа контакта, выполнить 100% проверку распайки, полярности, отсутствия межцепных коротких замыканий и сопротивления. Остальные 21 комплект выпускать после PASS первого комплекта. Build one complete first article, record crimp height and destructive pull for each terminal type, then perform 100% pin-to-pin, polarity, cross-short and resistance testing. Release the remaining 21 sets after first-article PASS.

Предел сопротивления: MIC и MAIN-PWR ≤0,15 Ом на проводник; BAT-PWR ≤0,10 Ом. Маркировать оба конца уникальным Harness_ID и обозначением стороны. Замена провода, контакта, корпуса, цвета или перестановка полостей допускается только по ECO. Resistance limit: MIC and MAIN-PWR ≤0.15 ohm per conductor; BAT-PWR ≤0.10 ohm. Label both ends with Harness_ID and end designation. Wire, terminal, housing, colour or cavity changes require an ECO.

В комплект поставки включить: протокол первого изделия, ведомость партий провода и контактов, применённую оснастку, результаты 100% теста и упаковочный лист. Delivery records: first-article report, wire/terminal lots, tooling identification, 100% test results and packing list.

# 3. MIC: распайка 24 цепей / 24-circuit pinout

ID | Откуда / From | Куда / To | Цепь / Net | Провод / Wire | Цвет / Colour | L, мм | Контакты / Terminals
MIC1-01 | PCB-MAIN J_MIC1_MATING_5040510601:1 | PCB-MIC1 J1_MATING_5040510601:1 | 1V8_MIC | AWG24_TE_55A0111-24_OD0P94MM | RED | 275 ±5 | 5040520098 / 5040520098
MIC1-02 | PCB-MAIN J_MIC1_MATING_5040510601:2 | PCB-MIC1 J1_MATING_5040510601:2 | GND | AWG24_TE_55A0111-24_OD0P94MM | BLACK | 275 ±5 | 5040520098 / 5040520098
MIC1-03 | PCB-MAIN J_MIC1_MATING_5040510601:3 | PCB-MIC1 J1_MATING_5040510601:3 | PDM_CLK | AWG24_TE_55A0111-24_OD0P94MM | WHITE | 275 ±5 | 5040520098 / 5040520098
MIC1-04 | PCB-MAIN J_MIC1_MATING_5040510601:4 | PCB-MIC1 J1_MATING_5040510601:4 | PDM_DATA1 | AWG24_TE_55A0111-24_OD0P94MM | BLUE | 275 ±5 | 5040520098 / 5040520098
MIC1-05 | PCB-MAIN J_MIC1_MATING_5040510601:5 | PCB-MIC1 J1_MATING_5040510601:5 | MIC_WAKE1 | AWG24_TE_55A0111-24_OD0P94MM | VIOLET | 275 ±5 | 5040520098 / 5040520098
MIC1-06 | PCB-MAIN J_MIC1_MATING_5040510601:6 | PCB-MIC1 J1_MATING_5040510601:6 | AAD_CFG | AWG24_TE_55A0111-24_OD0P94MM | GREY | 275 ±5 | 5040520098 / 5040520098
MIC2-01 | PCB-MAIN J_MIC2_MATING_5040510601:1 | PCB-MIC2 J1_MATING_5040510601:1 | 1V8_MIC | AWG24_TE_55A0111-24_OD0P94MM | RED | 275 ±5 | 5040520098 / 5040520098
MIC2-02 | PCB-MAIN J_MIC2_MATING_5040510601:2 | PCB-MIC2 J1_MATING_5040510601:2 | GND | AWG24_TE_55A0111-24_OD0P94MM | BLACK | 275 ±5 | 5040520098 / 5040520098
MIC2-03 | PCB-MAIN J_MIC2_MATING_5040510601:3 | PCB-MIC2 J1_MATING_5040510601:3 | PDM_CLK | AWG24_TE_55A0111-24_OD0P94MM | WHITE | 275 ±5 | 5040520098 / 5040520098
MIC2-04 | PCB-MAIN J_MIC2_MATING_5040510601:4 | PCB-MIC2 J1_MATING_5040510601:4 | PDM_DATA2 | AWG24_TE_55A0111-24_OD0P94MM | YELLOW | 275 ±5 | 5040520098 / 5040520098
MIC2-05 | PCB-MAIN J_MIC2_MATING_5040510601:5 | PCB-MIC2 J1_MATING_5040510601:5 | MIC_WAKE2 | AWG24_TE_55A0111-24_OD0P94MM | VIOLET | 275 ±5 | 5040520098 / 5040520098
MIC2-06 | PCB-MAIN J_MIC2_MATING_5040510601:6 | PCB-MIC2 J1_MATING_5040510601:6 | AAD_CFG | AWG24_TE_55A0111-24_OD0P94MM | GREY | 275 ±5 | 5040520098 / 5040520098
MIC3-01 | PCB-MAIN J_MIC3_MATING_5040510601:1 | PCB-MIC3 J1_MATING_5040510601:1 | 1V8_MIC | AWG24_TE_55A0111-24_OD0P94MM | RED | 275 ±5 | 5040520098 / 5040520098
MIC3-02 | PCB-MAIN J_MIC3_MATING_5040510601:2 | PCB-MIC3 J1_MATING_5040510601:2 | GND | AWG24_TE_55A0111-24_OD0P94MM | BLACK | 275 ±5 | 5040520098 / 5040520098
MIC3-03 | PCB-MAIN J_MIC3_MATING_5040510601:3 | PCB-MIC3 J1_MATING_5040510601:3 | PDM_CLK | AWG24_TE_55A0111-24_OD0P94MM | WHITE | 275 ±5 | 5040520098 / 5040520098
MIC3-04 | PCB-MAIN J_MIC3_MATING_5040510601:4 | PCB-MIC3 J1_MATING_5040510601:4 | PDM_DATA3 | AWG24_TE_55A0111-24_OD0P94MM | GREEN | 275 ±5 | 5040520098 / 5040520098
MIC3-05 | PCB-MAIN J_MIC3_MATING_5040510601:5 | PCB-MIC3 J1_MATING_5040510601:5 | MIC_WAKE3 | AWG24_TE_55A0111-24_OD0P94MM | VIOLET | 275 ±5 | 5040520098 / 5040520098
MIC3-06 | PCB-MAIN J_MIC3_MATING_5040510601:6 | PCB-MIC3 J1_MATING_5040510601:6 | AAD_CFG | AWG24_TE_55A0111-24_OD0P94MM | GREY | 275 ±5 | 5040520098 / 5040520098
MIC4-01 | PCB-MAIN J_MIC4_MATING_5040510601:1 | PCB-MIC4 J1_MATING_5040510601:1 | 1V8_MIC | AWG24_TE_55A0111-24_OD0P94MM | RED | 275 ±5 | 5040520098 / 5040520098
MIC4-02 | PCB-MAIN J_MIC4_MATING_5040510601:2 | PCB-MIC4 J1_MATING_5040510601:2 | GND | AWG24_TE_55A0111-24_OD0P94MM | BLACK | 275 ±5 | 5040520098 / 5040520098
MIC4-03 | PCB-MAIN J_MIC4_MATING_5040510601:3 | PCB-MIC4 J1_MATING_5040510601:3 | PDM_CLK | AWG24_TE_55A0111-24_OD0P94MM | WHITE | 275 ±5 | 5040520098 / 5040520098
MIC4-04 | PCB-MAIN J_MIC4_MATING_5040510601:4 | PCB-MIC4 J1_MATING_5040510601:4 | PDM_DATA4 | AWG24_TE_55A0111-24_OD0P94MM | ORANGE | 275 ±5 | 5040520098 / 5040520098
MIC4-05 | PCB-MAIN J_MIC4_MATING_5040510601:5 | PCB-MIC4 J1_MATING_5040510601:5 | MIC_WAKE4 | AWG24_TE_55A0111-24_OD0P94MM | VIOLET | 275 ±5 | 5040520098 / 5040520098
MIC4-06 | PCB-MAIN J_MIC4_MATING_5040510601:6 | PCB-MIC4 J1_MATING_5040510601:6 | AAD_CFG | AWG24_TE_55A0111-24_OD0P94MM | GREY | 275 ±5 | 5040520098 / 5040520098

# 4. MAIN-PWR и BAT-PWR: распайка 14 цепей / 14-circuit pinout

ID | Откуда / From | Куда / To | Цепь / Net | Провод / Wire | Цвет / Colour | L, мм | Контакты / Terminals
PWR-01 | PCB-PWR J_MAIN_PWR_MATING_430251200:1 | PCB-MAIN J_PWR_MATING_430251200:1 | 3V8_MODEM | AWG18_TE_55A0111-18_OD1P52MM | RED | 440 ±5 | 430300038 / 430300038
PWR-02 | PCB-PWR J_MAIN_PWR_MATING_430251200:2 | PCB-MAIN J_PWR_MATING_430251200:2 | GND_MODEM | AWG18_TE_55A0111-18_OD1P52MM | BLACK | 440 ±5 | 430300038 / 430300038
PWR-03 | PCB-PWR J_MAIN_PWR_MATING_430251200:3 | PCB-MAIN J_PWR_MATING_430251200:3 | 3V3_DIGITAL | AWG18_TE_55A0111-18_OD1P52MM | ORANGE | 440 ±5 | 430300038 / 430300038
PWR-04 | PCB-PWR J_MAIN_PWR_MATING_430251200:4 | PCB-MAIN J_PWR_MATING_430251200:4 | GND_DIGITAL | AWG18_TE_55A0111-18_OD1P52MM | BLACK_WHITE | 440 ±5 | 430300038 / 430300038
PWR-05 | PCB-PWR J_MAIN_PWR_MATING_430251200:5 | PCB-MAIN J_PWR_MATING_430251200:5 | 1V8_MIC | AWG18_TE_55A0111-18_OD1P52MM | BROWN | 440 ±5 | 430300038 / 430300038
PWR-06 | PCB-PWR J_MAIN_PWR_MATING_430251200:6 | PCB-MAIN J_PWR_MATING_430251200:6 | GND_MIC | AWG18_TE_55A0111-18_OD1P52MM | BLACK_BLUE | 440 ±5 | 430300038 / 430300038
PWR-07 | PCB-PWR J_MAIN_PWR_MATING_430251200:7 | PCB-MAIN J_PWR_MATING_430251200:7 | PWR_GOOD | AWG22_ALPHA_3051_OD1P575MM | WHITE | 440 ±5 | 430300001 / 430300001
PWR-08 | PCB-PWR J_MAIN_PWR_MATING_430251200:8 | PCB-MAIN J_PWR_MATING_430251200:8 | FAULT | AWG22_ALPHA_3051_OD1P575MM | YELLOW | 440 ±5 | 430300001 / 430300001
PWR-09 | PCB-PWR J_MAIN_PWR_MATING_430251200:9 | PCB-MAIN J_PWR_MATING_430251200:9 | EN_MODEM | AWG22_ALPHA_3051_OD1P575MM | GREEN | 440 ±5 | 430300001 / 430300001
PWR-10 | PCB-PWR J_MAIN_PWR_MATING_430251200:10 | PCB-MAIN J_PWR_MATING_430251200:10 | EN_AUX | AWG22_ALPHA_3051_OD1P575MM | BLUE | 440 ±5 | 430300001 / 430300001
PWR-11 | PCB-PWR J_MAIN_PWR_MATING_430251200:11 | PCB-MAIN J_PWR_MATING_430251200:11 | I2C2_SCL | AWG22_ALPHA_3051_OD1P575MM | VIOLET | 440 ±5 | 430300001 / 430300001
PWR-12 | PCB-PWR J_MAIN_PWR_MATING_430251200:12 | PCB-MAIN J_PWR_MATING_430251200:12 | I2C2_SDA | AWG22_ALPHA_3051_OD1P575MM | GREY | 440 ±5 | 430300001 / 430300001
BAT-01 | SYSTEM-BAT1 RELION_RB40_M8_POSITIVE:+ | PCB-PWR J_PWR_IN_MATING_430250200:1 | VBAT_PLUS | AWG18_TE_55A0111-18_OD1P52MM | RED | 330 ±5 | TE_8-34114-1_M8 / 430300038
BAT-02 | SYSTEM-BAT1 RELION_RB40_M8_NEGATIVE:- | PCB-PWR J_PWR_IN_MATING_430250200:2 | VBAT_MINUS | AWG18_TE_55A0111-18_OD1P52MM | BLACK | 330 ±5 | TE_8-34114-1_M8 / 430300038

После сборки станции проверить установленную трассу, разгрузку натяжения, PDM/AAD, I²C 100 кГц, падение напряжения и нагрев. After station assembly verify installed routing, strain relief, PDM/AAD, 100 kHz I²C, voltage drop and temperature rise.
