skif-ops/rs-zs-bpla/releases/evt-pre-20/2026-10-02-rev-d5/Основной_пакет/02_Сборка_станций/Корпус_PCB_MAIN_Rev_B_сборка_RU_EN.pdf

# Корпус PCB-MAIN Rev B. Сборка и маркировка

### PCB-MAIN Rev B faceted enclosure. Assembly and marking

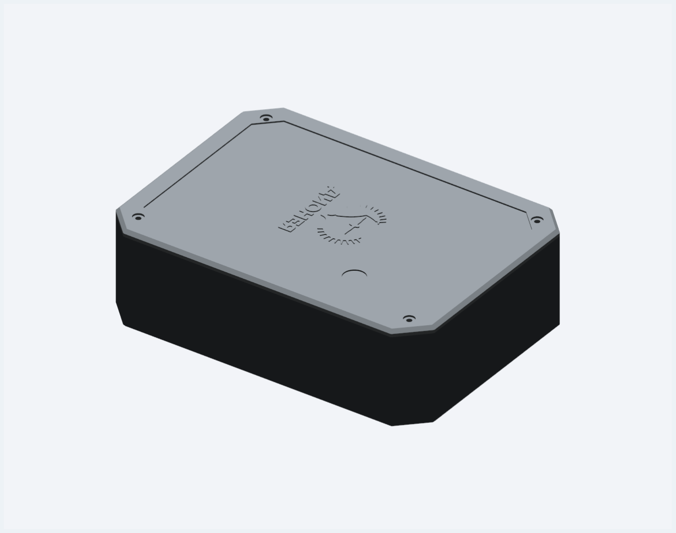
[picture p6: figure]

Фактический CAD по STEP/STL, рельеф утверждённого логотипа

Actual STEP/STL view with approved logo relief

Основание DIO-3DP-UP-001B_body, крышка DIO-3DP-UP-001B_lid.
Body DIO-3DP-UP-001B_body, cover DIO-3DP-UP-001B_lid.

Внешний габарит 200 × 145 × 59 мм. Углы срезаны на 16 мм, кромка крышки скошена на 2 мм.
Outer envelope 200 × 145 × 59 mm. Corners clipped by 16 mm; cover edge bevel is 2 mm.

Логотип из утверждённого DIONEYA_LOGO_STACKED_MONO_RELIEF_REV_A.svg: ширина 48 мм, рельеф 0,6 мм. Цветной SVG приложен для стойкой маркировки.
Approved stacked logo: 48 mm wide, 0.6 mm raised relief. Colour SVG is supplied for durable marking.

Круглая ниша Ø13 на крышке глухая и пока не является индикатором. Не сверлить её без отдельного задания.
The 13 mm circular seat is blind and is not an active indicator. Do not drill without a separate instruction.

Четыре отверстия крышки Ø3,2; резьбовые вставки и длину винтов М3 выбрать после первой примерки.

Four 3.2 mm cover clearances; select M3 inserts and screw length after first fit.

Печатать опытно из ASA или подтверждённого PC/ASA. Прокладка, кабельные вводы, антенны и мачтовый кронштейн требуют примерки.
Trial print in ASA or qualified PC/ASA. Gasket, cable glands, antennas and mast bracket require fit checks.

PCB-MAIN и жгуты сохраняют прежнюю геометрию и длины.

PCB-MAIN and harness geometry and lengths remain unchanged.

Контроль / Checks: плата и разъёмы, доступ к SIM/USB/SD, четыре винта, непрерывное уплотнение, вода/IP, кронштейн и окраска логотипа.

Check real PCBA and connectors, SIM/USB/SD access, four screws, continuous seal, water/IP, bracket and logo marking durability.

Статус: предварительная модель для опытной печати и примерки. Литьевые STEP не являются заданием на пресс-форму.

Status: trial print and fit model. Casting STEP files are not a released mold tooling specification.
