skif-ops/rs-zs-bpla/releases/evt-pre-20/2026-10-02-rev-d5/Заказ_плат_и_монтаж/00_Условия_передачи/ИЗВЕЩЕНИЕ_ПО_ЕДИНОЙ_ПАРТИИ_RU_EN.pdf

Извещение к заказу EVT-PRE-20 Rev D / Rev D order clarification
Дата: | 30.09.2026. | Документ | распространяется | на | переданный
производственный пакет Rev D и уточняет порядок заказа PCB-MAIN, PCB-PWR и PCB-MIC по требованию заказчика.
Решение по объёму и последовательности
Весь объём заказывается сразу: PCB-MAIN 22 PCBA, PCB-PWR 22 PCBA, PCB-MIC 80 PCBA. Изготовление и монтаж каждой партии выполняются без технологической паузы после первых образцов. Формулировки Rev D «сначала 2, затем 20» и «сначала 1, затем 79» в части очередности заменяются этим извещением. Количества, Gerber, сверловка, BOM и координаты не меняются. PCB-MAIN остаётся в текущей трассировке. Для этой партии не заказываются контролируемый импеданс и гарантия 50 Ом. До запуска панели фабрика подтверждает выбранный стек, DFM и эпоксидное заполнение с медным закрытием всех 76 переходов по заказному CSV, включая C6.1 и D11.1.
Невозможность | выполнить | это | требование | или | иное | изменение
производственных файлов требует остановки запуска панели и ECO.
После изготовления из партии выбирают для углублённого контроля два PCB-MAIN, два PCB-PWR и одну PCB-MIC или одну панель. Контроль не является условием запуска остальных плат: вся партия уже изготовлена. При дефекте затронутую партию изолируют, определяют объём проверки и доработки; изменение конструкции оформляют ECO. Условие подписанного Review B PCB-MIC о паузе после первого образца заменено требованием заказчика только в части очередности. Новая подпись технического Review B этим извещением не создаётся.
English order instruction
Place the full order at once: 22 PCB-MAIN, 22 PCB-PWR and 80 PCB-MIC PCBAs. Fabricate and assemble each complete lot without pausing after first articles. Earlier Rev D instructions to make 2 then 20, or 1 then 79, are superseded only for production sequencing. Quantities and manufacturing files remain unchanged. PCB-MAIN stays as routed. Do not order controlled impedance or a guaranteed 50-ohm target for this EVT lot. Before panel release, confirm the selected stack, DFM and epoxy filling with copper capping of all 76 vias in the order CSV, including C6.1 and D11.1. If this cannot be achieved, stop panel release and request an ECO.
After fabrication, select two PCB-MAIN, two PCB-PWR and one PCB-MIC or one panel for enhanced inspection and EVT tests. These checks do not gate fabrication of the rest of the lot. Quarantine and disposition any affected lot if defects are found. The signed PCB-MIC Review B first-article pause is superseded by the customer schedule only; this notice is not a new technical review signature.
