skif-ops/rs-zs-bpla/releases/evt-pre-20/2026-10-02-rev-d5/Ревью_PCB_MIC_отдельно/03_Исправленный_CAM/PCB-MIC_сборка_и_акустический_контроль_RU_EN.pdf

# PCB-MIC Rev B — сборка / assembly

EVT-PRE-20 · 30.09.2026 · управляемый выпуск первого изделия / controlled first-article release

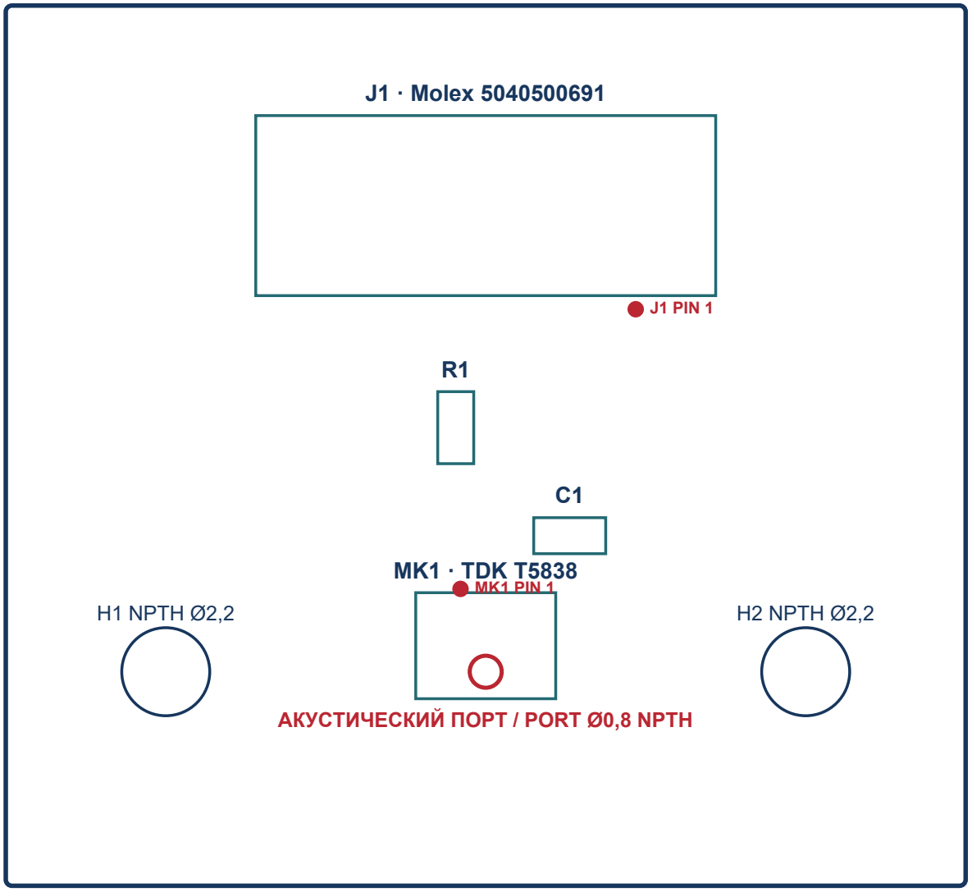
[picture p14: figure]
MK1 · TDK T5838; J1 · Molex 5040500691; H1 NPTH Ø2,2; H2 NPTH Ø2,2; АКУСТИЧЕСКИЙ ПОРТ / PORT Ø0,8 NPTH; J1 PIN 1; MK1 PIN 1

Вид сверху / Top view; Y направлена вниз / Y axis points down Плата / Board: 24 × 22 × 1,0 мм; 2 слоя / layers; 35 мкм / µm; ENIG

1. Установить MK1, J1, C1 и R1 на верхней стороне.

Fit MK1, J1, C1 and R1 on the top side.

2. Проверить pin 1 MK1 и J1 по красным меткам.

Verify MK1 and J1 pin 1 against the red marks.

3. Не наносить пасту, клей или покрытие в порт Ø0,8.

Keep paste, adhesive and coating clear of the Ø0.8 bore.

4. Трафарет MK1: четыре дуги по TDK Fig. 33.

MK1 stencil: four arcs per TDK Figure 33.

5. Первое изделие/панель: AOI или микроскоп + PDM тест.

First board/panel: AOI or microscope inspection plus PDM test.

6. Продолжить остальные 79 PCBA после приёмки первого.

Release the remaining 79 PCBAs after first-article acceptance.

7. Панелизацию выполнять без изгиба зоны MK1.

Panelize and depanel without bending the MK1 area.

СТАТУС / STATUS: REVIEW B ACCEPT · CONTROLLED FIRST ARTICLE · 80 PCBA

Плата / Board SHA-256: c57cebbb3886247166551fd242fa51350bc9be7fee6299e63e7eaac60518d518

Изменение CAM, стека, посадочных мест или трафарета только через ECO / CAM, stack, footprint or stencil changes require ECO.
