skif-ops/rs-zs-bpla/releases/evt-pre-20/2026-10-02-rev-d5/Основной_пакет/02_Сборка_станций/Машинные_таблицы/HARNESS_LOGICAL_PINOUT_REV_A.csv

Interface | Connector_Ref | Pin | Net | Direction_at_MAIN | Nominal_voltage | Current_class | Wire_rule | Shield_pair_rule | Keying_requirement | Release_status | Notes
MIC1 | J_MIC1 | 1 | 1V8_MIC | OUT | 1.8V | LOW | AWG28_or_larger | Route_with_GND | KEYED | LOGICAL_FROZEN | Same 6-pin physical order on all MIC connectors
MIC1 | J_MIC1 | 2 | GND | RETURN | 0V | LOW | AWG28_or_larger | Return_for_1V8_PDM_WAKE_CFG | KEYED | LOGICAL_FROZEN
MIC1 | J_MIC1 | 3 | PDM_CLK | OUT | 1.8V_logic | LOW | AWG28_or_larger | Twist_or_pair_with_GND_if_harness_long | KEYED | LOGICAL_FROZEN | Series damping footprint at source
MIC1 | J_MIC1 | 4 | PDM_DATA1 | IN | 1.8V_logic | LOW | AWG28_or_larger | Twist_or_pair_with_GND_if_harness_long | KEYED | LOGICAL_FROZEN
AAD_WAKE1 | J_MIC1 | 5 | MIC_WAKE1 | IN | 1.8V_logic | LOW | AWG28_or_larger | Route_with_GND_avoid_PDM_clk_crosstalk | KEYED | LOGICAL_FROZEN | T5838 AAD WAKE output preserved for low-power acoustic wake
AAD_CFG1 | J_MIC1 | 6 | AAD_CFG | OUT | 1.8V_one_wire | LOW | AWG28_or_larger | Route_with_GND_avoid_PDM_clk_crosstalk | KEYED | LOGICAL_FROZEN | Common T5838 THSEL one-wire configuration bus; same write applied to all four microphones
MIC2 | J_MIC2 | 1 | 1V8_MIC | OUT | 1.8V | LOW | AWG28_or_larger | Route_with_GND | KEYED | LOGICAL_FROZEN
MIC2 | J_MIC2 | 2 | GND | RETURN | 0V | LOW | AWG28_or_larger | Return_for_1V8_PDM_WAKE_CFG | KEYED | LOGICAL_FROZEN
MIC2 | J_MIC2 | 3 | PDM_CLK | OUT | 1.8V_logic | LOW | AWG28_or_larger | Twist_or_pair_with_GND_if_harness_long | KEYED | LOGICAL_FROZEN
MIC2 | J_MIC2 | 4 | PDM_DATA2 | IN | 1.8V_logic | LOW | AWG28_or_larger | Twist_or_pair_with_GND_if_harness_long | KEYED | LOGICAL_FROZEN
AAD_WAKE2 | J_MIC2 | 5 | MIC_WAKE2 | IN | 1.8V_logic | LOW | AWG28_or_larger | Route_with_GND_avoid_PDM_clk_crosstalk | KEYED | LOGICAL_FROZEN | T5838 AAD WAKE output
AAD_CFG2 | J_MIC2 | 6 | AAD_CFG | OUT | 1.8V_one_wire | LOW | AWG28_or_larger | Route_with_GND_avoid_PDM_clk_crosstalk | KEYED | LOGICAL_FROZEN | Common T5838 THSEL one-wire configuration bus
MIC3 | J_MIC3 | 1 | 1V8_MIC | OUT | 1.8V | LOW | AWG28_or_larger | Route_with_GND | KEYED | LOGICAL_FROZEN
MIC3 | J_MIC3 | 2 | GND | RETURN | 0V | LOW | AWG28_or_larger | Return_for_1V8_PDM_WAKE_CFG | KEYED | LOGICAL_FROZEN
MIC3 | J_MIC3 | 3 | PDM_CLK | OUT | 1.8V_logic | LOW | AWG28_or_larger | Twist_or_pair_with_GND_if_harness_long | KEYED | LOGICAL_FROZEN
MIC3 | J_MIC3 | 4 | PDM_DATA3 | IN | 1.8V_logic | LOW | AWG28_or_larger | Twist_or_pair_with_GND_if_harness_long | KEYED | LOGICAL_FROZEN
AAD_WAKE3 | J_MIC3 | 5 | MIC_WAKE3 | IN | 1.8V_logic | LOW | AWG28_or_larger | Route_with_GND_avoid_PDM_clk_crosstalk | KEYED | LOGICAL_FROZEN | T5838 AAD WAKE output
AAD_CFG3 | J_MIC3 | 6 | AAD_CFG | OUT | 1.8V_one_wire | LOW | AWG28_or_larger | Route_with_GND_avoid_PDM_clk_crosstalk | KEYED | LOGICAL_FROZEN | Common T5838 THSEL one-wire configuration bus
MIC4 | J_MIC4 | 1 | 1V8_MIC | OUT | 1.8V | LOW | AWG28_or_larger | Route_with_GND | KEYED | LOGICAL_FROZEN
MIC4 | J_MIC4 | 2 | GND | RETURN | 0V | LOW | AWG28_or_larger | Return_for_1V8_PDM_WAKE_CFG | KEYED | LOGICAL_FROZEN
MIC4 | J_MIC4 | 3 | PDM_CLK | OUT | 1.8V_logic | LOW | AWG28_or_larger | Twist_or_pair_with_GND_if_harness_long | KEYED | LOGICAL_FROZEN
MIC4 | J_MIC4 | 4 | PDM_DATA4 | IN | 1.8V_logic | LOW | AWG28_or_larger | Twist_or_pair_with_GND_if_harness_long | KEYED | LOGICAL_FROZEN
AAD_WAKE4 | J_MIC4 | 5 | MIC_WAKE4 | IN | 1.8V_logic | LOW | AWG28_or_larger | Route_with_GND_avoid_PDM_clk_crosstalk | KEYED | LOGICAL_FROZEN | T5838 AAD WAKE output
AAD_CFG4 | J_MIC4 | 6 | AAD_CFG | OUT | 1.8V_one_wire | LOW | AWG28_or_larger | Route_with_GND_avoid_PDM_clk_crosstalk | KEYED | LOGICAL_FROZEN | Common T5838 THSEL one-wire configuration bus
MAIN_PWR | J_PWR1 | 1 | 3V8_MODEM | IN | 3.8V | HIGH | AWG18_0.75mm2_Molex430300038 | Dedicated_return_pin_2 | KEYED_LATCH | LOGICAL_FROZEN | Exact selected Micro-Fit power terminal; validate burst current and harness temperature
MAIN_PWR | J_PWR1 | 2 | GND_MODEM | RETURN | 0V | HIGH | AWG18_0.75mm2_Molex430300038 | Dedicated_return_for_3V8 | KEYED_LATCH | LOGICAL_FROZEN | Exact selected Micro-Fit power terminal
MAIN_PWR | J_PWR1 | 3 | 3V3_DIGITAL | IN | 3.3V | MEDIUM | AWG18_0.75mm2_Molex430300038 | Dedicated_return_pin_4 | KEYED_LATCH | LOGICAL_FROZEN | Exact selected Micro-Fit power terminal; conservative common harness standard
MAIN_PWR | J_PWR1 | 4 | GND_DIGITAL | RETURN | 0V | MEDIUM | AWG18_0.75mm2_Molex430300038 | Dedicated_return_for_3V3 | KEYED_LATCH | LOGICAL_FROZEN | Exact selected Micro-Fit power terminal
MAIN_PWR | J_PWR1 | 5 | 1V8_MIC | IN | 1.8V | LOW | AWG18_0.75mm2_Molex430300038 | Dedicated_return_pin_6 | KEYED_LATCH | LOGICAL_FROZEN | Remain powered while T5838 AAD monitoring is armed; exact selected Micro-Fit power terminal
MAIN_PWR | J_PWR1 | 6 | GND_MIC | RETURN | 0V | LOW | AWG18_0.75mm2_Molex430300038 | Dedicated_return_for_1V8 | KEYED_LATCH | LOGICAL_FROZEN | Exact selected Micro-Fit power terminal
MAIN_PWR | J_PWR1 | 7 | PWR_GOOD | IN | 3.3V_logic | LOW | AWG20_to_24_Molex430300001 | Pair_with_logic_ground_if_needed | KEYED_LATCH | LOGICAL_FROZEN | Control terminal 430300001; power-side output to MAIN
MAIN_PWR | J_PWR1 | 8 | FAULT | IN | 3.3V_logic | LOW | AWG20_to_24_Molex430300001 | Pair_with_logic_ground_if_needed | KEYED_LATCH | LOGICAL_FROZEN | Control terminal 430300001; aggregate power-side fault/alert output to MAIN
MAIN_PWR | J_PWR1 | 9 | EN_MODEM | OUT | 3.3V_logic | LOW | AWG20_to_24_Molex430300001 | Pair_with_logic_ground_if_needed | KEYED_LATCH | LOGICAL_FROZEN | Control terminal 430300001; default safe OFF
MAIN_PWR | J_PWR1 | 10 | EN_AUX | OUT | 3.3V_logic | LOW | AWG20_to_24_Molex430300001 | Pair_with_logic_ground_if_needed | KEYED_LATCH | LOGICAL_FROZEN | Control terminal 430300001; controls auxiliary rails policy while AAD requires 1V8_MIC available
MAIN_PWR | J_PWR1 | 11 | I2C2_SCL | BIDIR_OD | 3.3V_logic | LOW | AWG20_to_24_Molex430300001 | Route_with_GND_DIGITAL_keep_short | KEYED_LATCH | LOGICAL_FROZEN | 100 kHz Rev.A power/sensor I2C; pull-ups are on PCB-MAIN; INA226 is on PCB-PWR
MAIN_PWR | J_PWR1 | 12 | I2C2_SDA | BIDIR_OD | 3.3V_logic | LOW | AWG20_to_24_Molex430300001 | Route_with_GND_DIGITAL_keep_short | KEYED_LATCH | LOGICAL_FROZEN | 100 kHz Rev.A power/sensor I2C; pull-ups are on PCB-MAIN; INA226 address 0x40
SWD | J_SWD | 1 | VTREF | IN | 3.3V | LOW | Fixture_pogo_or_AWG28 | No_shield | KEYED_OR_FIXTURE | LOGICAL_FROZEN
SWD | J_SWD | 2 | SWDIO | BIDIR | 3.3V_logic | LOW | Fixture_pogo_or_AWG28 | Short | KEYED_OR_FIXTURE | LOGICAL_FROZEN
SWD | J_SWD | 3 | SWCLK | IN | 3.3V_logic | LOW | Fixture_pogo_or_AWG28 | Short | KEYED_OR_FIXTURE | LOGICAL_FROZEN
SWD | J_SWD | 4 | NRST | IN | 3.3V_logic | LOW | Fixture_pogo_or_AWG28 | Short | KEYED_OR_FIXTURE | LOGICAL_FROZEN
SWD | J_SWD | 5 | GND | RETURN | 0V | LOW | Fixture_pogo_or_AWG28 | Reference | KEYED_OR_FIXTURE | LOGICAL_FROZEN
PWR_INPUT | J_PWR1_IN | 1 | VBAT_PLUS | IN | 10.0_to_14.6V_provisional | HIGH | AWG18_0.75mm2_Molex430300038 | Dedicated_return_pin_2 | KEYED_HIGH_CURRENT | LOGICAL_FROZEN | Selected Micro-Fit terminal is 18 AWG only; 5 A capture envelope and final thermal/fault review required
PWR_INPUT | J_PWR1_IN | 2 | VBAT_MINUS | RETURN | 0V | HIGH | AWG18_0.75mm2_Molex430300038 | Dedicated_return_for_VBAT | KEYED_HIGH_CURRENT | LOGICAL_FROZEN | Selected Micro-Fit terminal is 18 AWG only; final connector thermal test required
