skif-ops/rs-zs-bpla/releases/presentation/v0.3/README.md

# Презентация проекта «Дионея» v0.3

В презентации добавлена схема размещения станций вдоль дороги наряду с круговым объектом, применена зелёно-бирюзовая цветовая модель, добавлен утверждённый логотип и уточнён статус EVT-MB.

Восстановление файла:

```bash
../../reassemble.sh parts Дионея_презентация_проекта_v0_3.pptx
sha256sum -c PRESENTATION_SHA256.txt
```
