skif-ops/rs-zs-bpla/releases/audio/2026-09-07/README.md

# Диагностический прогон «Мухоеда», 07.09.2026

Во всех трех исходных записях присутствие БПЛА подтверждено пользователем.

- результат детекции: 3/3 TRUE_POSITIVE;
- положительные окна: 15/15;
- первое решение: не позднее 2,0 с;
- operational type: UNKNOWN во всех трех случаях;
- набор не содержит отрицательных записей, поэтому FAR по нему не оценивается.

Архив разделен на шестнадцать бинарных частей. Ожидаемый SHA-256 восстановленного ZIP: `84b9ad6cead103ce19abc94ca49f222ac863133113549e228708a70ab1364466`.
