skif-ops/rs-zs-bpla/releases/evt/v0.7/README.md

# Полный EVT, gate 3+1 v0.7

Этот комплект относится к полноценному EVT изделия и не заменяет макетный комплект EVT-MB.

- архив: `РС_ЗС-БПЛА_EVT_gate_3plus1_v0_7.zip`;
- SHA-256: `37eaee4e85e8f12f26da3fbd3a7c40d4cda19c9192dca2e5bb30963435747e6c`;
- размер: 381675 байт;
- статус: OPEN;
- аппаратный EVT не выполнен.
