skif-ops/rs-zs-bpla/android/REQUIREMENTS_v0_1.md

# Android commissioning app - требования v0.1

Статус: `DRAFT / OPEN`

## Функциональные требования

- AND-F-001: обнаруживать только станции в физически активированном service mode.
- AND-F-002: связывать BLE identity с QR/serial до чтения или изменения конфигурации.
- AND-F-003: показывать serial, station_id, HW revision, FW/bootloader version и region.
- AND-F-004: настраивать APN, порядок RAT, roaming policy, MQTT/HTTPS endpoint и CA reference.
- AND-F-005: проверять формат адресов, диапазоны и обязательные поля до записи.
- AND-F-006: применять конфигурацию атомарно, считывать обратно и сравнивать hash/version.
- AND-F-007: запускать self-test питания, GNSS/PPS, cellular attach/TLS, LoRa receive-only, storage и microphones.
- AND-F-008: импортировать offline OTA bundle, не изменяя его содержимое.
- AND-F-009: проверять совместимость HW, anti-rollback, hash и цифровую подпись до передачи.
- AND-F-010: поддерживать resume OTA после обрыва BLE и экрана/процесса приложения.
- AND-F-011: показывать A/B trial, confirmation и rollback reason.
- AND-F-012: экспортировать redacted diagnostic report и commissioning record.
- AND-F-013: не позволять пользователю менять manufacturing region RU868/EU868.
- AND-F-014: выдавать пошаговую инструкцию USB-C recovery без хранения recovery secrets.
- AND-F-015: показывать наличие SIM1/SIM2, redacted ICCID, активный слот, оператора, RAT и результат последнего attach.
- AND-F-016: настраивать упорядоченные публичные APN profiles и preferred SIM slot без экспорта PIN/PUK/APN password; private APN для EVT-PRE-20 отклонять.
- AND-F-017: разрешать ручное переключение SIM/APN только авторизованной роли, с явным предупреждением о разрыве связи и сохранением audit record.
- AND-F-018: показывать причину автоматического failover, предыдущий и новый профиль, число попыток и состояние store-and-forward.
- AND-F-019: иметь обязательный шаг `Координаты установки` до перевода EVT-PRE-20 в FIELD_READY.
- AND-F-020: поддерживать четыре источника координат установки: ручной ввод, location телефона через стандартный Android framework API, текущий GNSS fix станции и заранее известные/геодезические координаты.
- AND-F-021: не требовать Google Play Services для получения координат телефона; ручной ввод всегда доступен.
- AND-F-022: валидировать latitude, longitude, altitude MSL, declared accuracy и source до записи.
- AND-F-023: показывать одновременно устанавливаемые координаты, текущий GNSS станции и горизонтальное расхождение между ними.
- AND-F-024: записывать `installation_position` и `position_trust_policy` атомарно через authenticated BLE, затем выполнять read-back и сравнение version/hash.
- AND-F-025: после подтверждения блокировать координаты установки; изменение допускается только в новом физическом service mode авторизованной ролью и создаёт audit record.
- AND-F-026: показывать GNSS integrity: fix, satellites, HDOP/accuracy, jam, spoof detector state, position delta, position trust, time trust и PPS/holdover state.
- AND-F-027: при GNSS drift/spoofing явно показывать, что сервер и станция продолжают использовать `Установленные координаты`, а GNSS position считается диагностическим.
- AND-F-028: commissioning record должен содержать serial, installation coordinates, altitude, accuracy, source, configuration version/hash, HW/FW/app versions и факт coordinate lock без секретных данных.
- AND-F-029: не предоставлять удалённый/обычный UI-путь изменения installation coordinates вне физического service mode.
- AND-F-030: после изменения координат требовать повторный position/GNSS/PPS self-test и только затем снимать `REVALIDATION_REQUIRED`.

## Нефункциональные требования

- AND-N-001: работа без Google Play Services.
- AND-N-002: работа без интернета после загрузки APK и OTA bundle.
- AND-N-003: интерфейс на русском; английская локализация обязательна до China factory use.
- AND-N-004: поддержка arm64-v8a, кандидат minimum Android 9.
- AND-N-005: отсутствие analytics, advertising SDK и скрытой телеметрии.
- AND-N-006: reproducible release build, dependency lock, SBOM и SHA-256.
- AND-N-007: APK подписывается отдельным Android release key; firmware signing key не используется.
- AND-N-008: crash/log export не содержит PIN, APN password, TLS private key, QR secret, полного ICCID/IMSI.
- AND-N-009: critical actions требуют явного подтверждения и отображают station serial.
- AND-N-010: все ошибки имеют recoverable state или понятный переход к USB-C recovery.
- AND-N-011: приложение не должно требовать интернет-карты для commissioning координат; отображение карты может быть добавлено позже как необязательная функция.
- AND-N-012: при использовании location телефона приложение запрашивает только необходимое runtime permission и не сохраняет историю перемещений оператора.

## Не входит в первую версию

- постоянная онлайн-карта объектов и постоянный мониторинг;
- облачная учётная запись пользователя;
- изменение классификационных моделей отдельно от подписанного release bundle;
- доступ к API оператора;
- одновременная работа двух SIM;
- ручная установка RF frequency/power;
- извлечение private keys станции;
- Wi-Fi/BSSID geolocation как резерв координат станции.

## Gate

Требования получают `LOCKED` после утверждения UX двух ролей, GATT prototype, security review, проверки минимум на трёх смартфонах включая устройство Huawei без GMS и совместного теста с target firmware.

Для EVT-PRE-20 обязательны отдельные acceptance tests: manual/phone/station-GNSS coordinate commissioning, invalid-coordinate rejection, read-back/hash/lock, power-cycle retention, GNSS drift indication, spoof/jam display, revalidation after coordinate change и подтверждение того, что effective station position не изменяется вслед за GNSS drift.

## Host evidence

Для AND-F-006/022/024/025 реализован Kotlin domain contract: те же 58 bytes и
SHA-256 known-answer, что в portable firmware, uint32 version bound, monotonic
recommission, installer/default-policy и service-engineer/custom-policy,
сравнение всех read-back полей, storage generation, hash и audit committed.
QG-1/QG-2 и JVM unit tests не закрывают BLE UUID/pairing/GATT, физическое
10-минутное окно или совместный тест со станцией.
