skif-ops/rs-zs-bpla/hardware/DUAL_SIM_SINGLE_STANDBY.md

# Дионея EVT-PRE-20 - Dual SIM Single Standby

Статус: `ELECTRICAL AUTHORITY CONTROLLED / PCB REVIEW A NOT STARTED / NOT FOR MANUFACTURE`

Точная машинная карта выводов и безопасных состояний: `hardware/PCB_MAIN_DUAL_SIM_PIN_AUTHORITY_REV_A.csv`. Обоснование и первичные документы: `hardware/PCB_MAIN_DUAL_SIM_AUTHORITY_REV_A.md`.

## 1. Принятое решение

`PCB-MAIN` содержит два физических nano-SIM разъёма и один модем Quectel BG95-M3-класса. Одновременно к модему подключается только один слот. Переключение выполняется внешним 2:1 мультиплексором под управлением STM32U585.

Пилотные кандидаты: МТС, МегаФон, Билайн, T2/Tele2 и SIM, предоставленная оператором ГЛОНАСС. Для каждой установленной SIM в профиле фиксируются ICCID, фактический сотовый оператор и публичный APN. Тариф не является входом или критерием EVT.

## 2. Ограничение BG95

BG95 предоставляет один внешний 1.8 В USIM-интерфейс: `USIM_VDD`, `USIM_RST`, `USIM_CLK`, `USIM_DATA`, `USIM_GND` и `USIM_DET`. Поэтому две карты не могут работать одновременно. Режим проекта: `Dual SIM Single Standby`.

Опциональная eSIM BG95 и внешняя SIM также не используются одновременно. Для EVT-PRE-20 базовая комплектация использует два физических nano-SIM слота. Посадочное место eSIM не включается автоматически и требует отдельного ECN.

## 3. Зафиксированная электрическая схема

| Узел | Решение | Статус |
|---|---|---|
| SIM1 | J6, TE `2336582-1`, 4FF push-push, отдельный `SIM1_DET` | TECHNICALLY_SELECTED_PROCUREMENT_RISK |
| SIM2 | J7, TE `2336582-1`, 4FF push-push, отдельный `SIM2_DET` | TECHNICALLY_SELECTED_PROCUREMENT_RISK |
| U13 | TI `TS3A27518EPWR`, TSSOP-24, 6-канальный 2:1 двунаправленный мультиплексор | SELECTED_PENDING_USIM_SI_SAMPLE |
| Управление | `SIM_MUX_SEL` напрямую; `SIM_MUX_EN` через Q3 `MMBT3904,215` на active-HIGH High-Z U13 EN | ELECTRICALLY_LOCKED |
| Интерфейс | 1.8 В; три канала U13 параллельно коммутируют VDD, остальные каналы коммутируют RST, CLK и DATA | ELECTRICALLY_LOCKED |
| ESD | U14/U15 `ESDALC6V1-5P6`, по пять защищённых линий на слот | SELECTED_PENDING_ESD_SI_SAMPLE |

U13 питается от `3V3_DIGITAL`. При таком питании гарантированный максимум сопротивления одного канала равен 7.6 Ом, а трёх параллельных VDD-каналов не более 2.54 Ом. До Review A обязательны измерение напряжения на контакте C1, проверка утечки, ёмкости, фронтов CLK/DATA и поведения при сбросе и отключении модема.

U13 EN имеет 47 кОм к `3V3_DIGITAL`. Q3 только по явной команде `SIM_MUX_EN=HIGH` тянет EN в LOW и включает выбранный слот. Сброс MCU, brownout или `SIM_MUX_EN=LOW` оставляют U13 в High-Z.

## 4. Правила разводки

- оба SIM-разъёма и U13 размещаются максимально близко к BG95;
- длина каждого пути от BG95 до карты не превышает 200 мм и должна быть существенно меньше при фактической компоновке;
- CLK, DATA и RST разводятся вдали от cellular RF, LoRa, DC/DC и силовых петель;
- VDD и GND имеют ширину не менее 0.5 мм до уточнения токов и stackup;
- у каждого слота устанавливаются 100 нФ между VDD и `GND_MODEM`, U14/U15 у разъёма, заполненные 0 Ом последовательные tuning-позиции и DNP-позиции 33 пФ на RST/CLK/DATA;
- `SIM1_DET` и `SIM2_DET` идут на отдельные MCU GPIO и не объединяются;
- каждый DET имеет 10 кОм pull-up к `3V3_DIGITAL`, 10 нФ к `GND_MODEM` и firmware debounce не менее 20 ms;
- доступ к картам допускается только под сервисной крышкой;
- замена SIM при работающем изделии запрещена эксплуатационной инструкцией.

## 5. Безопасное переключение

1. Запретить новые сетевые транзакции и сохранить очередь событий.
2. Закрыть MQTT/HTTPS, выполнить detach и штатно выключить BG95.
3. Дождаться `CELL_STATUS=LOW`, установить `SIM_MUX_EN=LOW`, проверить `U13_EN_N=HIGH` и отключить `EN_MODEM`.
4. Установить `SIM_MUX_SEL` при U13 High-Z.
5. Включить `EN_MODEM`, дождаться стабильного `PWR_GOOD` и выдержать не менее 30 мс.
6. Установить `SIM_MUX_EN=HIGH`, проверить `U13_EN_N=LOW`, затем подать 700 мс PWRKEY pulse.
7. Дождаться `CELL_STATUS=HIGH`, считать ICCID и сверить его с разрешённым профилем слота.
8. Выполнить attach, DNS и TLS-проверку endpoint.
9. Возобновить передачу очереди с прежними `event_id` и sequence.

Переключение без полного штатного выключения модема является ошибкой. При brownout активный слот считается неизвестным до повторного чтения ICCID.

## 6. Public APN

В пилотной партии разрешены только профили `PUBLIC`: обычный публичный APN, исходящий MQTT/TLS или HTTPS/TLS и работа за CGNAT. Для каждой SIM хранится упорядоченный набор разрешённых публичных профилей.

Private APN не настраивается, не выбирается автоматически и не входит в испытания EVT-PRE-20. Его возможное добавление после пилота требует отдельного решения, изменения требований и регрессионных испытаний. APN-пароли, PIN/PUK и TLS private keys не хранятся в Git.

## 7. Failover

Failover допускается по причинам: attach timeout, ошибка PDP context, DNS, TLS, длительная потеря канала или команда авторизованного оператора. Циклическое переключение ограничивается числом попыток и минимальным временем удержания профиля, чтобы исключить дребезг между сетями.

Приоритет по умолчанию задаётся при provisioning отдельно для каждой станции. Автоматический выбор по имени оператора без сверки ICCID и разрешённого профиля запрещён.

Точные RefDes, заказные MPN, population и физические цепи всех пассивных компонентов dual-SIM зафиксированы `MAIN-AUTH-010`; механика и южная сервисная ориентация J6/J7 зафиксированы `MAIN-AUTH-011`. Проверка посадки крышки и карт остаётся физическим блокером.

## 8. Обязательные проверки

- ESD и signal integrity обоих слотов;
- холодный старт и 100 циклов переключения SIM1/SIM2;
- корректность ICCID и slot mapping;
- отсутствие повреждения SIM при отказе питания в каждой фазе переключения;
- attach с тестовой SIM каждого заявленного оператора;
- публичный APN каждой установленной SIM, MQTT/TLS и HTTPS/TLS;
- отклонение попытки настроить или активировать private APN;
- восстановление store-and-forward без потери и неконтролируемых дублей;
- потребление в active, sleep, PSM и при отключённом мультиплексоре;
- невозможность переключения без авторизации через BLE или сервер.

## 9. Первичные источники

- Quectel BG95 Series Hardware Design V1.6, раздел 3.9: https://forums.quectel.com/uploads/short-url/uBwfe2DevTKvtaEsvNDChHNrMER.pdf
- Quectel BG95 product page: https://www.quectel.com/product/lpwa-bg95-cat-m1-cat-nb2-egprs-series/
- TI TS3A27518E: https://www.ti.com/lit/ds/symlink/ts3a27518e.pdf
- ST ESDALC6V1-5P6: https://www.st.com/resource/en/datasheet/esdalc6v1-5p6.pdf
- TE 2336582-1: https://www.te.com/en/product-2336582-1.html
