skif-ops/rs-zs-bpla/BRANCHING.md

# Правила ветвления проекта

## main

Содержит только срез, прошедший локальные проверки и CI. Прямые экспериментальные изменения сюда не вносятся. Текущий статус аппаратной части сохраняется OPEN, пока не выполнены физические испытания.

## develop

Интеграционная ветка. В ней объединяются проверенные feature-ветки, актуальный сервер «Мухоед», целевые профили станции, аппаратные таблицы, механические исходники, манифесты и проверочные результаты.

## evt

Ветка полного EVT изделия. Она не является инструкцией по сборке макетной станции. В нее входят общая программа испытаний, методики, формы протоколов и материалы gate для архитектуры 3+1.

## evt-mb

Ветка макетного EVT. Зафиксированы WeAct STM32U585CIU6, паяная перфоплата, разъемные жгуты, одна станция и один сервер для первого стендового этапа, развертывание Windows 11 и Ubuntu 24.04, а также сопряжение с «Мухоедом».

## evt-pre-20

Ветка предсерийного EVT на 20 станций с собственными PCB, отдельной конфигурационной
базой, производственным маршрутом и доказательствами испытаний. Поставочные материалы
и runtime-маркировка `evt-mb` сюда не переносятся.

## Продвижение изменений

1. Feature-ветка проверяется самостоятельно.
2. Изменение включается в `develop`.
3. Для `develop` должны завершиться CI и проверка манифестов.
4. Проверенный SHA продвигается в `main` без изменения дерева.
5. EVT-ветки получают только материалы своей конфигурации.
6. Между `evt-pre-20` и `evt-mb` запрещены merge, cherry-pick и копирование release/evidence.
7. Общие проверенные изменения разрешено отдельно продвигать в `develop` и `main`.

Начиная с `DIONEA-INTEGRATION-v0.8`, снят временный запрет на обновление `develop` и
`main`. После двойного контроля обе ветки должны указывать на один проверенный SHA.
Это разрешение не отменяет изоляцию поставочных материалов `evt-pre-20` и `evt-mb`.
