skif-ops/rs-zs-bpla/protocols/PROTOCOL_VERSIONING.md

# Версионирование протоколов EVT-PRE-20

Статус: `DRAFT / OPEN`

Чтобы исключить прежнюю неоднозначность, используются независимые версии:

| Объект | Текущая версия | Значение |
|---|---:|---|
| Station-server interface release | 1.5 | Detection schema 4 и защищённый cellular heartbeat |
| MQTT namespace | v1 | Первый сегмент topic `zs/v1/...` |
| Detection compact CBOR `schema_ver` | 4 | Значение ключа 0 внутри detection payload |
| Message type detection | 2 | Значение ключа 1 внутри compact CBOR |
| Heartbeat compact CBOR schema | 1 | Полная LTE cellular telemetry через mTLS status topic |
| Message type heartbeat | 3 | Значение ключа 1 внутри compact heartbeat |
| LoRa regional profile | v0.1 | RU868 для всех 20 пилотных изделий; EU868 future template; TX disabled до RF gate |
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
