skif-ops/rs-zs-bpla/releases/evt-pre-20/2026-10-02-rev-d5/Основной_пакет/03_Корпуса_для_3D_печати_ПРЕДВАРИТЕЛЬНО/DIO-3DP-AH-001C_вид_сборки.png

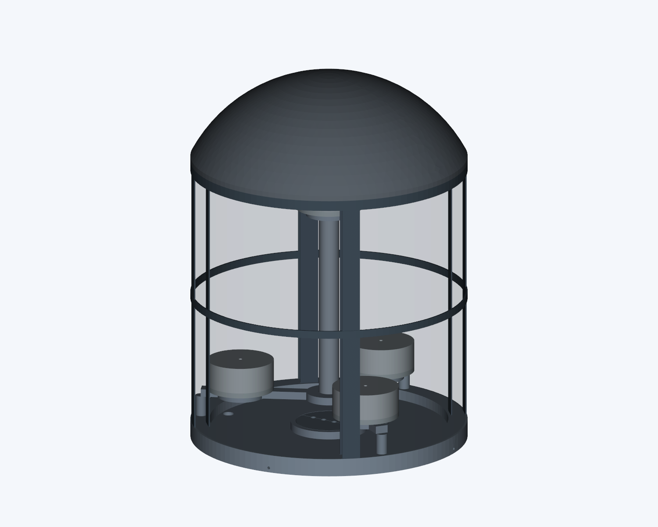
releases/evt-pre-20/2026-10-02-rev-d5/Основной_пакет/03_Корпуса_для_3D_печати_ПРЕДВАРИТЕЛЬНО/DIO-3DP-AH-001C_вид_сборки.png
