skif-ops/rs-zs-bpla/releases/evt-pre-20/2026-10-02-rev-d5/Основной_пакет/03_Корпуса_для_3D_печати_ПРЕДВАРИТЕЛЬНО/Кассета_питания_RevB/Обзор_кабельных_выходов.png

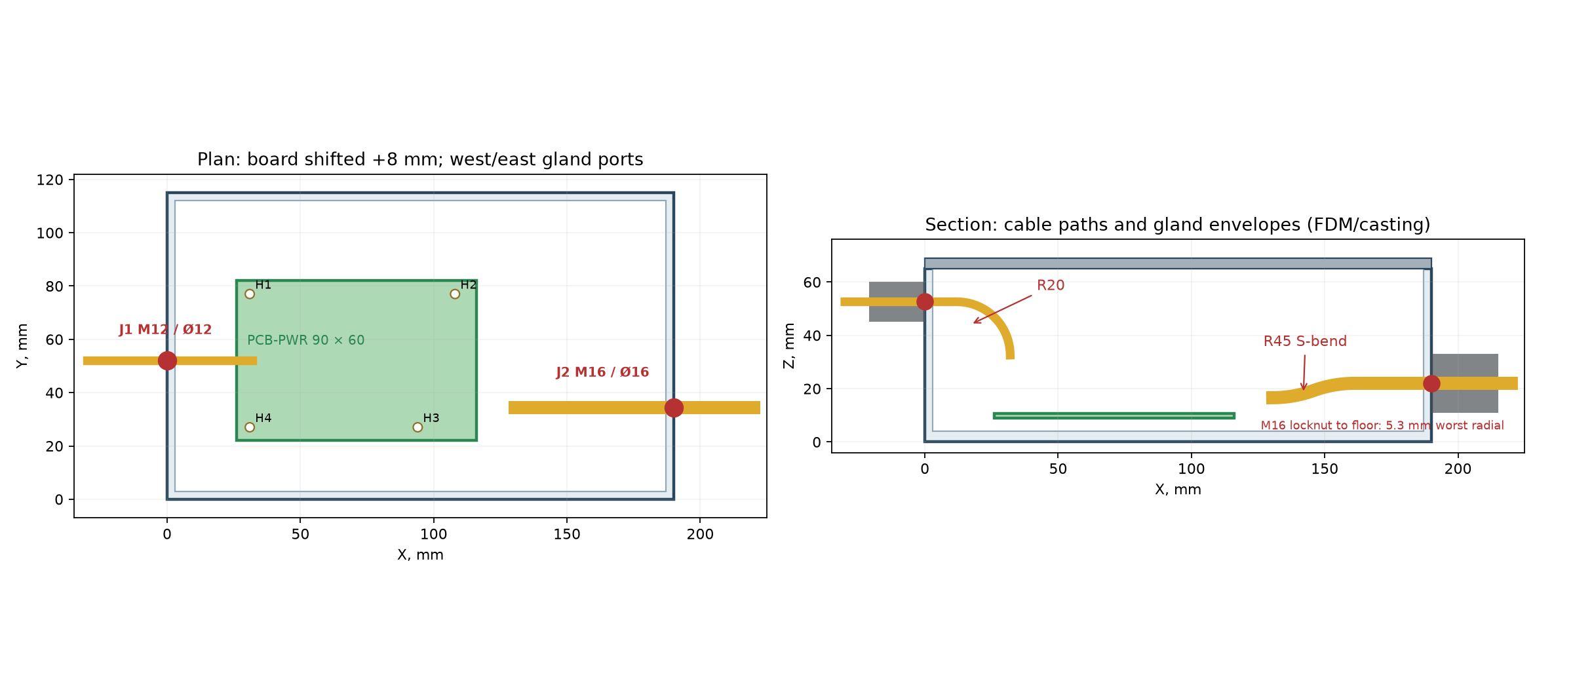
releases/evt-pre-20/2026-10-02-rev-d5/Основной_пакет/03_Корпуса_для_3D_печати_ПРЕДВАРИТЕЛЬНО/Кассета_питания_RevB/Обзор_кабельных_выходов.png
