skif-ops/rs-zs-bpla/releases/evt-pre-20/2026-10-02-rev-d5/Ревью_PCB_MIC_отдельно/02_Доказательства/codex-clipboard-370e5946-3556-494c-8a48-b7f516b0b44b.png

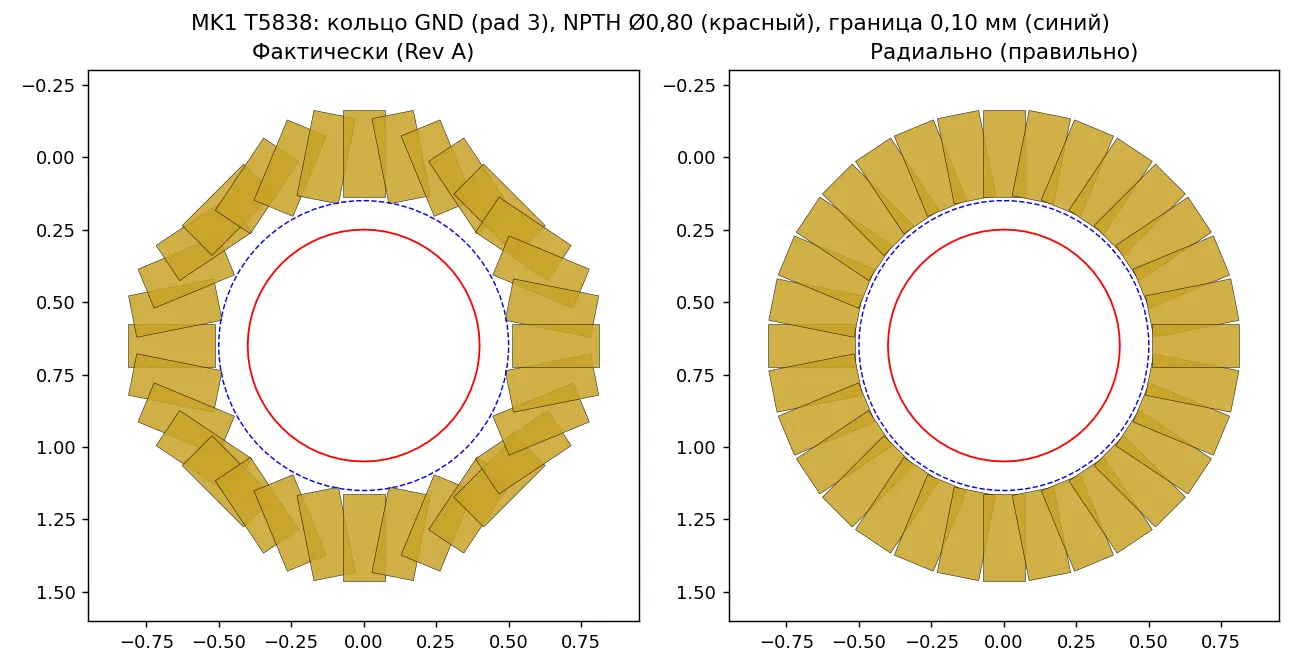
releases/evt-pre-20/2026-10-02-rev-d5/Ревью_PCB_MIC_отдельно/02_Доказательства/codex-clipboard-370e5946-3556-494c-8a48-b7f516b0b44b.png
