skif-ops/rs-zs-bpla/releases/evt-pre-20/2026-10-02-rev-d5/Ревью_PCB_MIC_отдельно/02_Доказательства/codex-clipboard-afec90b2-4388-4d98-b8fb-1a1b455c8d56.png

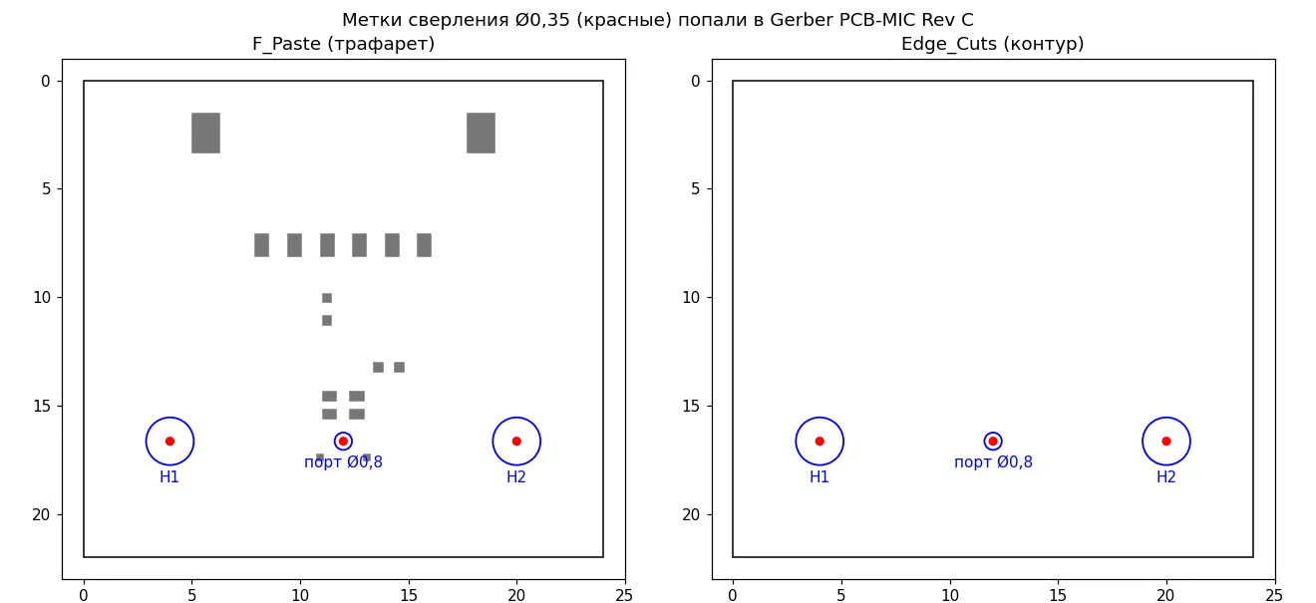
releases/evt-pre-20/2026-10-02-rev-d5/Ревью_PCB_MIC_отдельно/02_Доказательства/codex-clipboard-afec90b2-4388-4d98-b8fb-1a1b455c8d56.png
