skif-ops/rs-zs-bpla/hardware/MAIN_COMPONENT_FREEZE_REV_A.csv

RefDes | Assembly | Function | Manufacturer | MPN | Package_or_Module | Temperature_C | Qty_per_station | Status | Release_Blockers | Evidence | Notes
U1 | PCB-MAIN | Main secure MCU | STMicroelectronics | STM32U585VIT6Q | LQFP100_14x14 | -40..85 exact selected part | 1 | SELECTED_PENDING_TARGET_SAMPLE | CubeMX exact-package IOC; target build; sample verification | ST STM32U585VIT6Q exact product page + DS13086 Rev10 + project pin map | Exact orderable Q part is specified to +85 C and is compatible with DEC-019 -40..+70 C ambient; do not assume family +125 C applies to this MPN
U2 | PCB-MAIN | 64 MB QSPI NOR | Winbond | W25Q512JVFIQ | SOIC-16_300mil | -40..85 | 1 | SELECTED_PENDING_SAMPLE | availability/endurance/power-loss test | Winbond W25Q512JV product guide and datasheet; industrial I suffix | Alternative only after footprint/driver review; exact FI-package land pattern remains mandatory
U3 | PCB-MAIN | Accelerometer | STMicroelectronics | LIS2DW12TR | LGA-12_2x2mm | -40..85 | 1 | SELECTED_PENDING_SAMPLE | orientation/self-test verification | ST LIS2DW12 product page and DS11811 | Orientation marked on assembly drawing
U4 | PCB-MAIN | Temperature sensor | STMicroelectronics | STTS22HTR | UDFN-6L_2x2mm | -40..125 | 1 | SELECTED_PENDING_ASSEMBLY_REVIEW | CM UDFN yield; exposed-pad land pattern; thermal response validation | ST STTS22H product page and DS12606 | Corrects the superseded WLCSP-4 description; exact orderable tape-and-reel MPN is STTS22HTR
U7 | PCB-MAIN | T5838 PDM and AAD_CFG 1.8V/3.3V level translator | Texas Instruments | SN74AXC8T245PWR | TSSOP-24 | -40..125 | 1 | SELECTED_PENDING_SI_AAD_SAMPLE | PDM skew and final-harness SI; PDM_CLK source termination; THSEL one-wire fanout/timing; measured S0 current | TI SCES875C RevC + TDK T5838 DS-000383 v1.2 | VCCA=1V8_MIC and VCCB=3V3_DIGITAL; DIR1 high maps four PDM data channels A-to-B; DIR2 low maps PDM_CLK and AAD_CFG B-to-A; OE low; B7/B8 grounded and A7/A8 NC; exact map in PCB_MAIN_AUDIO_LOGIC_PIN_AUTHORITY_REV_A.csv
U8 | PCB-MAIN | Cellular Cat-M1/NB2/EGPRS module | Quectel | BG95-M3 | LGA-102_23.6x19.9mm | -35..75 operating; -40..85 extended | 1 | SELECTED_PENDING_INCOMING_ID_AND_POST_ASSEMBLY_EVT | ordered module marking and firmware identity at incoming inspection; operator attach; LTE and EGPRS burst; certification; cold-limit qualification | Quectel BG95 Series Hardware Design v1.6 | Exact BG95-M3 hardware identity and all 102 pads are frozen in PCB_MAIN_CELLULAR_PIN_AUTHORITY_REV_A.csv; firmware identity is recorded at incoming inspection; operator/SIM and burst PASS remain NOT_RUN until assembled-station EVT; -40 C remains an extended-range qualification item
U9 | PCB-MAIN | Independent GNSS/PPS | u-blox | MAX-M10S-00B | LCC-18_9.7x10.1mm | -40..85 | 1 | SELECTED_PENDING_GNSS_RF_TIMING_SAMPLE | active antenna and cable; SAW/coexistence; supervisor fault response; PPS and holdover | u-blox UBX-20035208 R08 + UBX-20053088 R05 | Mass-production global ordering code; 3V3 VCC/V_IO; V_BCKP NC; 18-pad and J9 electrical map in PCB_MAIN_GNSS_PIN_AUTHORITY_REV_A.csv; configured installation coordinates remain authoritative
U10 | PCB-MAIN | LoRa RU868 module | Ebyte | E22-900M22S | SMD_20x14_22P_1.27mm | -40..85 | 1 | SELECTED_PENDING_CASTELLATED_OPTION_RF_REGULATORY | supplier confirmation of castellated ANT option with no fitted module IPEX; RU868 conducted/radiated test; current; supply availability | Ebyte E22-M user manual v1.2 2026-02-06 | All 20 EVT-PRE-20 units provision RU868; separate TXEN/RXEN controls and all 22 pads are fixed in PCB_MAIN_LORA_PIN_AUTHORITY_REV_A.csv
U11 | PCB-MAIN | BLE commissioning diagnostics OTA | Raytac | MDBT50Q-P1MV2 | nRF52840_SMD_10.5x15.5_61P_PCB_antenna | -40..85 | 1 | SELECTED_PENDING_ENCLOSURE_RF | 2.4 GHz enclosure range; SWD/DFU/reset firmware and evidence | Raytac MDBT50Q-P1MV2 Version L + Footprint Design Guide 230606 | All 61 pads and dedicated four-contact nRF SWD map are fixed in PCB_MAIN_BLE_PIN_AUTHORITY_REV_A.csv; Wi-Fi intentionally absent; U1MV2 u.FL variant is RF fallback only after explicit review
U12 | PCB-MAIN | Industrial removable storage | Kingston | SDCIT2/32GB | microSD_card_8_contact | -40..85 | 1 | SELECTED_PENDING_SAMPLE_ENDURANCE | authorized-channel procurement; CID/capacity; full write/read; temperature and power-loss sample | Kingston Industrial microSD SDCIT2 official product data | Exact card contacts and J12 socket pairing are fixed in PCB_MAIN_CONNECTOR_FIXTURE_PIN_AUTHORITY_REV_A.csv; pSLC mode industrial card; consumer substitution prohibited without authority review
U13 | PCB-MAIN | Dual-SIM single-standby analog mux | Texas Instruments | TS3A27518EPWR | TSSOP-24_PW | -40..85 | 1 | SELECTED_PENDING_USIM_SI_SAMPLE | selected-card VDD minimum; CLK/DATA edge integrity; leakage and reset isolation | TI SCDS260F RevF + Quectel BG95 Hardware Design v1.6 | VCC=3V3_DIGITAL; three parallel channels switch USIM_VDD; RST CLK DATA use the remaining channels; IN1/IN2 tied; active-HIGH EN defaults disabled through Q3; exact map in PCB_MAIN_DUAL_SIM_PIN_AUTHORITY_REV_A.csv
U14 | PCB-MAIN | SIM1 five-line low-capacitance ESD | STMicroelectronics | ESDALC6V1-5P6 | SOT666_1.6x1.6mm | -40..125 | 1 | SELECTED_PENDING_SIM_ESD_SI_SAMPLE | connector-side layout; capacitance and CLK/DATA integrity; ESD sample | ST ESDALC6V1-5P6 Rev3 | Pin 2 GND; five protected lines are SIM1 VDD RST CLK DATA and DET; exact map in PCB_MAIN_DUAL_SIM_PIN_AUTHORITY_REV_A.csv
U15 | PCB-MAIN | SIM2 five-line low-capacitance ESD | STMicroelectronics | ESDALC6V1-5P6 | SOT666_1.6x1.6mm | -40..125 | 1 | SELECTED_PENDING_SIM_ESD_SI_SAMPLE | connector-side layout; capacitance and CLK/DATA integrity; ESD sample | ST ESDALC6V1-5P6 Rev3 | Pin 2 GND; five protected lines are SIM2 VDD RST CLK DATA and DET; exact map in PCB_MAIN_DUAL_SIM_PIN_AUTHORITY_REV_A.csv
U16 | PCB-MAIN | BG95 UART/status 1.8V/3.3V translator | Texas Instruments | SN74AXC8T245PWR | TSSOP-24 | -40..125 | 1 | SELECTED_PENDING_UART_POWER_SAMPLE | UART/RI/STATUS timing; partial-power isolation; burst ground-offset margin; measured current | TI SCES875C RevC + Quectel BG95 Hardware Design v1.6 | VCCA=BG95 VDD_EXT and VCCB=3V3_DIGITAL; DIR1 high maps TXD STATUS RI A-to-B; DIR2 low maps RXD DTR B-to-A; OE low; exact map in PCB_MAIN_CELLULAR_PIN_AUTHORITY_REV_A.csv
U17 | PCB-MAIN | T5838 four-channel AAD WAKE OR aggregation | Texas Instruments | SN74LVC32APWR | TSSOP-14 | -40..125 | 1 | SELECTED_PENDING_AAD_WAKE_TEST | quiescent-current measurement; individual and aggregate wake latency; false-wake and open-harness tests | TI SCAS286U RevU + TDK T5838 DS-000383 v1.2 | Powered at 1V8_MIC; gates 1 and 2 form pairwise ORs and gate 3 forms aggregate; four inputs use 100 kOhm pull-downs; gate 4 inputs grounded and output NC; exact map in PCB_MAIN_AUDIO_LOGIC_PIN_AUTHORITY_REV_A.csv
U18 | PCB-MAIN | T5838 aggregated WAKE 1.8V-to-3.3V translator | Texas Instruments | SN74AXC1T45DRLR | SOT-5X3_6 | -40..125 | 1 | SELECTED_PENDING_AAD_WAKE_TEST | wake edge and Stop-mode latency; partial-power test; quiescent-current measurement | TI SCES882E RevE | VCCA=1V8_MIC and VCCB=3V3_DIGITAL; DIR tied high for A-to-B; output drives STM32 PA8 MIC_WAKE with 100 kOhm pull-down; exact map in PCB_MAIN_AUDIO_LOGIC_PIN_AUTHORITY_REV_A.csv
Q1 | PCB-MAIN | BG95 PWRKEY open-collector driver | Nexperia | MMBT3904,215 | SOT23 | -65..150 | 1 | SELECTED_PENDING_CONTROL_TIMING_SAMPLE | 500-1000 ms pulse; collector-low margin; cold-start and shutdown timing | Nexperia MMBT3904 v5 + Quectel BG95 Hardware Design v1.6 | 4.7 kOhm base series and 47 kOhm base-emitter pull-down; collector to U8 PWRKEY; exact map in PCB_MAIN_CELLULAR_PIN_AUTHORITY_REV_A.csv
Q2 | PCB-MAIN | BG95 RESET_N open-collector driver | Nexperia | MMBT3904,215 | SOT23 | -65..150 | 1 | SELECTED_PENDING_CONTROL_TIMING_SAMPLE | 2-3.8 s reset pulse; collector-low margin; reset recovery and mutual exclusion | Nexperia MMBT3904 v5 + Quectel BG95 Hardware Design v1.6 | 4.7 kOhm base series and 47 kOhm base-emitter pull-down; collector to U8 RESET_N; exact map in PCB_MAIN_CELLULAR_PIN_AUTHORITY_REV_A.csv
Q3 | PCB-MAIN | Dual-SIM mux boot-safe enable inverter | Nexperia | MMBT3904,215 | SOT23 | -65..150 | 1 | SELECTED_PENDING_SIM_SAFE_STATE_SAMPLE | reset and brownout High-Z behavior; U13 EN low margin; 100 slot-change cycles | Nexperia MMBT3904 v5 + TI SCDS260F RevF | 10 kOhm base series and 100 kOhm base-emitter pull-down; collector drives U13 active-HIGH EN against 47 kOhm pull-up; exact map in PCB_MAIN_DUAL_SIM_PIN_AUTHORITY_REV_A.csv
X1 | PCB-MAIN | 32.768 kHz low-frequency reference | SiTime | SiT1552AI-JE-DCC-32.768D | CSP-4_1.5x0.8mm | -40..85 | 1 | SELECTED_PENDING_LSE_BYPASS_REVIEW | CubeMX LSE bypass wiring; holdover drift measurement | SiTime exact-orderable product page and SiT1552 datasheet | No external HSE in Rev.A
