skif-ops/rs-zs-bpla/releases/evt-pre-20/2026-10-02-rev-d5/Заказ_плат_и_монтаж/00_Условия_передачи/BOM_плат_без_цен_RevB.csv

Procurement_ID | Assemblies | Item_IDs | RefDes | Category | Manufacturer | MPN | Package | Value | Variant | Population | Qty_per_station | Qty_EVT20 | Spares_EVT20 | Procure_qty_EVT20 | Base_qty_program_41 | Spares_two_EVT20 | Procure_qty_program_41 | Procurement_track | Status | Incoming_control
PR-001 | PCB-MAIN | ASM-MAIN | - | PCBA | Dioneya controlled design | DIO-ASM-MAIN-REV-B | 8-layer PCB-MAIN Rev B PCBA; fab DFM stack and via-in-pad approval pending |  | COMMON | N/A | 1 | 20 | 2 | 22 | 41 | 4 | 45 | PRIMARY_FULL_PCBA | CONTROLLED_INTERNAL_ARTICLE_CUSTOMER_EMS_SELECTION_PENDING | AOI plus X-ray where hidden joints plus functional test
PR-002 | PCB-MIC | ASM-MIC | - | PCBA | Dioneya controlled design | DIO-ASM-MIC-REV-B | 2-layer PCB-MIC Rev B PCBA; 24x22x1.0 mm; ENIG; full lot 80 no pause; post-lot acoustic sample |  | COMMON | N/A | 4 | 80 | 0 | 80 | 164 | 4 | 168 | PRIMARY_FULL_PCBA | REVIEW_B_DESIGN_ACCEPT_CUSTOMER_FULL_LOT_NO_PAUSE | Order and build all 80 PCBAs without pause; post-lot sample AOI acoustic port MK1 and PDM; disposition affected lot if failed
PR-003 | PCB-PWR | ASM-PWR | - | PCBA | Dioneya controlled design | DIO-ASM-PWR-REV-A | assembled 4-layer power PCB build-to-print service scope; EVT DIM-003 Rev B 90x60x1.6 mm; H1-H4 per board datum, mechanical integration pending; outer 1 oz nominal; inner 1 oz nominal; ENIG; fab stack ID and DFM at customer checkout |  | COMMON | N/A | 1 | 20 | 2 | 22 | 41 | 4 | 45 | PRIMARY_FULL_PCBA | CONTROLLED_INTERNAL_ARTICLE_CUSTOMER_EMS_SELECTION_PENDING | AOI functional high-current thermal
PR-004 | SYSTEM | HARNESS | - | Harness | Dioneya controlled design | DIO-HARNESS-SET-REV-A | Controlled labeled station harness set Rev.A |  | COMMON | FITTED | 1 | 20 | 2 | 22 | 41 | 4 | 45 | COMMON_PROGRAM_PROCUREMENT | CONTROLLED_INTERNAL_ARTICLE_PHYSICAL_RELEASE_PENDING | 100 percent continuity polarity pull sample
PR-007 | SYSTEM | HSG-VC | HSG1 | Housing | Dioneya controlled design | DIO-HSG-VC-REV-A | Vacuum-cast polyurethane housing set build-to-print scope |  | VACUUM_CASTING_PRIMARY | N/A | 1 | 20 | 0 | 20 | 41 | 0 | 41 | COMMON_PROGRAM_PROCUREMENT | CONTROLLED_INTERNAL_ARTICLE_MECHANICAL_RELEASE_PENDING | FAI dimensions material cure finish inserts leak fit acoustic and RF checks
PR-011 | PCB-PWR | PWR-FUSE-01 | F1 | Protection | Littelfuse | 0451008.MRL | Nano2_451_6.1x2.69mm |  | COMMON | FITTED | 1 | 20 | 10 | 30 | 41 | 20 | 61 | COMMON_PROGRAM_PROCUREMENT | CANDIDATE_SELECTED_FOR_EVT_QUALIFICATION_NATIVE_VALUE_ECO_APPLIED_REPEAT_EVIDENCE_PASS_PHYSICAL_QUALIFICATION_PENDING | Marking continuity and controlled fault clearing
PR-012 | PCB-MAIN | J-SIM1 | J-SIM2 | J6 | J7 | SIM | TE Connectivity | 2336582-1 | Nano-SIM 4FF connector with DET |  | COMMON | FITTED | 2 | 40 | 10 | 50 | 82 | 20 | 102 | COMMON_PROGRAM_PROCUREMENT | TECHNICALLY_SELECTED_PROCUREMENT_RISK | Mating cycles card detect coplanarity and ESD
PR-013 | HARNESS-PWR-MAIN | H-PWR-MAIN | H_PWR_MAIN:A/B | Housing | Molex | 43025-1200 | Micro-Fit 3.0 12-circuit housing |  | COMMON | FITTED | 2 | 40 | 4 | 44 | 82 | 8 | 90 | COMMON_PROGRAM_PROCUREMENT | SELECTED_PENDING_MECHANICS_I2C_TEST | Marking MPN package orientation electrical functional sample
PR-014 | HARNESS-PWR-MAIN | T-PWR-MAIN-CTL | H_PWR_MAIN control contacts | Terminal | Molex | 43030-0001 | Micro-Fit female crimp terminal 20-24 AWG class |  | COMMON | FITTED | 12 | 240 | 12 | 252 | 492 | 24 | 516 | COMMON_PROGRAM_PROCUREMENT | SELECTED_PENDING_I2C_PULL_TEST | Marking MPN package orientation electrical functional sample
PR-015 | HARNESS-PWR-MAIN | T-PWR-MAIN-PWR | H_PWR_MAIN power contacts | Terminal | Molex | 43030-0038 | Micro-Fit female crimp terminal 18 AWG class |  | COMMON | FITTED | 12 | 240 | 12 | 252 | 492 | 24 | 516 | COMMON_PROGRAM_PROCUREMENT | SELECTED_PENDING_CURRENT_PULL_TEST | Marking MPN package orientation electrical functional sample
PR-016 | PCB-PWR | J-PWR-IN | J1 | Connector | Molex | 430450213 | 2 positions |  | COMMON | FITTED | 1 | 20 | 5 | 25 | 41 | 10 | 51 | COMMON_PROGRAM_PROCUREMENT | SELECTED_PENDING_MECHANICS | Marking MPN package orientation electrical functional sample
PR-017 | PCB-MAIN | PCB-PWR | J-PWR-MAIN | J-PWR-PWR | J2 | J_PWR1 | Connector | Molex | 430451202 | 12 positions |  | COMMON | FITTED | 2 | 40 | 10 | 50 | 82 | 20 | 102 | COMMON_PROGRAM_PROCUREMENT | MECHANICAL_AUTHORITY_FROZEN_PENDING_HARNESS_SI | SELECTED_ELECTRICAL_PENDING_MECHANICS | Marking dimensions latch mate continuity
PR-018 | PCB-MAIN | J-TAMPER | J13 | Connector | Molex | 5040500291 | Pico-Lock 1.50 mm 2-circuit right-angle SMT |  | COMMON | FITTED | 1 | 20 | 5 | 25 | 41 | 10 | 51 | COMMON_PROGRAM_PROCUREMENT | MECHANICAL_AUTHORITY_FROZEN_PENDING_PHYSICAL_TEST | Mating pull continuity cable-break and cover-open fault coverage
PR-019 | PCB-MAIN | PCB-MIC | J-MIC | J-MIC-MAIN | J_MIC1;J_MIC2;J_MIC3;J_MIC4 | PCB-MIC:J1 x4 | Connector | Molex | 5040500691 | Pico-Lock 1.50 mm 6-circuit right-angle SMT |  | COMMON | FITTED | 8 | 160 | 24 | 184 | 328 | 48 | 376 | COMMON_PROGRAM_PROCUREMENT | MECHANICAL_AUTHORITY_FROZEN_PENDING_SI_AAD | Marking MPN package orientation electrical functional sample | Mating pull test contact resistance continuity and temperature
PR-020 | HARNESS-MIC | H-MIC | H_MIC1:A/B;H_MIC2:A/B;H_MIC3:A/B;H_MIC4:A/B | Housing | Molex | 5040510601 | Pico-Lock 1.50 mm 6-circuit housing |  | COMMON | FITTED | 8 | 160 | 16 | 176 | 328 | 32 | 360 | COMMON_PROGRAM_PROCUREMENT | SELECTED_PENDING_HARNESS_LENGTH_PULL_TEST | Marking MPN package orientation electrical functional sample
PR-021 | HARNESS-MIC | T-MIC | H_MIC1..H_MIC4 contacts | Terminal | Molex | 5040520098 | Pico-Lock crimp terminal 28-24 AWG |  | COMMON | FITTED | 48 | 960 | 48 | 1008 | 1968 | 96 | 2064 | COMMON_PROGRAM_PROCUREMENT | SELECTED_PENDING_CRIMP_PULL_TEST | Marking MPN package orientation electrical functional sample
PR-022 | SYSTEM | ANT-GNSS | AE2 | Antenna | Taoglas | AA.166.A.301111 | IP67 magnetic 37.8x40.4x10 mm with 3 m RG174 SMA(M) |  | COMMON | FITTED | 1 | 20 | 2 | 22 | 41 | 4 | 45 | COMMON_PROGRAM_PROCUREMENT | CONTROLLED_EVT_PURCHASE_EXACT_MPN_VALIDATION_DURING_ASSEMBLY_EVT | Reconcile PO packing slip quantity and visible damage; verify connector cable route current at 3.3 V receiver sensitivity PPS mounting and coexistence during assembly EOL and EVT
PR-023 | PCB-MAIN | MAIN-010-FL1 | FL1 | SAW_Filter | Abracon | ABSES5AF-L100KM | 1109-5 | 1582.4 MHz wideband GNSS SAW | COMMON | FITTED | 1 | 20 | 0 | 20 | 41 | 0 | 41 | COMMON_PROGRAM_PROCUREMENT | SELECTED_PENDING_REVIEW_A | Marking MPN package orientation electrical functional sample
PR-024 | PCB-MAIN | U8 | U8 | Cellular | Quectel | BG95-M3 | LGA-102_23.6x19.9mm |  | COMMON | FITTED | 1 | 20 | 5 | 25 | 41 | 10 | 51 | COMMON_PROGRAM_PROCUREMENT | SELECTED_PENDING_INCOMING_ID_AND_POST_ASSEMBLY_EVT | IMEI label firmware RF conducted attach TLS
PR-025 | PCB-MAIN | MAIN-010-FB1 | FB1 | Ferrite_Bead | Murata | BLM31KN601SN1L | 1206 | 600 Ohm at 100 MHz | COMMON | FITTED | 1 | 20 | 0 | 20 | 41 | 0 | 41 | COMMON_PROGRAM_PROCUREMENT | SELECTED_PENDING_REVIEW_A | Marking MPN package orientation electrical functional sample
PR-026 | SYSTEM | RF-PIGTAIL | J8/J9/J10 cable | RF cable | Taoglas | CAB.0243 | 1.13 mm micro-coax 150 mm MHF I/U.FL-compatible R/A to waterproof SMA(F) bulkhead |  | COMMON | FITTED | 3 | 60 | 6 | 66 | 123 | 12 | 135 | COMMON_PROGRAM_PROCUREMENT | CONTROLLED_EVT_PURCHASE_EXACT_MPN_VALIDATION_DURING_ASSEMBLY_EVT | Reconcile PO packing slip quantity and visible damage; verify every installed cable continuity polarity length and route then mate retention bend seal torque temperature and VNA performance during assembly EOL and EVT
PR-027 | PCB-PWR | PWR-C-100N | C1;C2;C4;C6 | Passive | TDK | CGA2B3X7R1E104K050BB | 0402 | 100 nF 25 V X7R | COMMON | FITTED | 4 | 80 | 40 | 120 | 164 | 80 | 244 | COMMON_PROGRAM_PROCUREMENT | LOCKED_CANDIDATE_PENDING_DERATING | Marking MPN package orientation electrical functional sample
PR-028 | PCB-MIC | C-MIC | PCB-MIC:C1 x4 | Passive | TDK | CGA2B3X7R1E104K050BB | 0402 1005 metric | 100 nF 25 V X7R | COMMON | FITTED | 4 | 80 | 40 | 120 | 164 | 80 | 244 | COMMON_PROGRAM_PROCUREMENT | SELECTED_PENDING_SAMPLE | Value package reel label capacitance sample
PR-029 | PCB-PWR | PWR-C-LDO | C7;C8 | Passive | TDK | CGA3E1X7R1A225K080AC | 0603 | 2.2 uF 10 V X7R | COMMON | FITTED | 2 | 40 | 40 | 80 | 82 | 80 | 162 | COMMON_PROGRAM_PROCUREMENT | LOCKED_CANDIDATE_PENDING_DERATING | Marking MPN package orientation electrical functional sample
PR-030 | PCB-PWR | PWR-C-CIN-HF | C9;C20;C21 | Passive | TDK | CGA3E2X7R1H104K080AA | 0603 | 100 nF 50 V X7R | COMMON | FITTED | 3 | 60 | 40 | 100 | 123 | 80 | 203 | COMMON_PROGRAM_PROCUREMENT | CONTROLLED_CANDIDATE_PENDING_MULTIPLE_REVIEWS | Marking MPN package orientation electrical functional sample
PR-031 | PCB-PWR | PWR-COUT-3V3 | PWR-COUT-3V8 | C3;C14;C15;C16 | C5;C17;C18;C19 | Passive | TDK | CGA6P3X7R1E226M250AB | 1210 | 22 uF 25 V X7R | COMMON | FITTED | 8 | 160 | 80 | 240 | 328 | 160 | 488 | COMMON_PROGRAM_PROCUREMENT | LOCKED_CANDIDATE_PENDING_DERATING | Marking MPN package orientation electrical functional sample
PR-032 | PCB-PWR | PWR-C-INPUT | C10;C11;C12 | Passive | TDK | CGA6P3X7R1H475K250AB | 1210 | 4.7 uF 50 V X7R | COMMON | FITTED | 3 | 60 | 40 | 100 | 123 | 80 | 203 | COMMON_PROGRAM_PROCUREMENT | CONTROLLED_CANDIDATE_PENDING_MULTIPLE_REVIEWS | Marking MPN package orientation electrical functional sample
PR-033 | PCB-PWR | PWR-REV-FET | Q1 | Protection | Texas Instruments | CSD18540Q5B | VSON-CLIP 5x6 mm |  | COMMON | FITTED | 1 | 20 | 5 | 25 | 41 | 10 | 51 | COMMON_PROGRAM_PROCUREMENT | SELECTED_TECHNICALLY_PROCUREMENT_CHECK | Marking Rds thermal and reverse fault test
PR-034 | PCB-MAIN | U10 | U10 | LoRa | Ebyte | E22-900M22S | SMD_20x14_22P_1.27mm |  | RU868_PILOT | FITTED | 1 | 20 | 6 | 26 | 41 | 12 | 53 | COMMON_PROGRAM_PROCUREMENT | SELECTED_PENDING_CASTELLATED_OPTION_RF_REGULATORY | Marking antenna-interface option firmware conducted power sensitivity sleep current
PR-035 | PCB-PWR | PWR-C-BULK | C13 | Passive | Panasonic Industry | EEH-ZK1V101XP | SMD can 6.3x7.7 mm | 100 uF 35 V hybrid | COMMON | FITTED | 1 | 20 | 40 | 60 | 41 | 80 | 121 | COMMON_PROGRAM_PROCUREMENT | LOCKED_CANDIDATE_PACKAGE_REVIEW_PENDING | Marking MPN package orientation electrical functional sample
PR-036 | PCB-PWR | PWR-R-100K-01 | R1 | Passive | Panasonic Industry | ERA-2AEB104X | 0402 | 100 kOhm 0.1% | COMMON | FITTED | 1 | 20 | 40 | 60 | 41 | 80 | 121 | COMMON_PROGRAM_PROCUREMENT | LOCKED_CANDIDATE | Marking MPN package orientation electrical functional sample
PR-037 | PCB-PWR | PWR-R-35K7 | R2 | Passive | Panasonic Industry | ERA-2AEB3572X | 0402 | 35.7 kOhm 0.1% | COMMON | FITTED | 1 | 20 | 40 | 60 | 41 | 80 | 121 | COMMON_PROGRAM_PROCUREMENT | LOCKED_CANDIDATE | Marking MPN package orientation electrical functional sample
PR-038 | PCB-PWR | PWR-R-86K6 | R3;R7 | Passive | Panasonic Industry | ERA-2AEB8662X | 0402 | 86.6 kOhm 0.1% | COMMON | FITTED | 2 | 40 | 40 | 80 | 82 | 80 | 162 | COMMON_PROGRAM_PROCUREMENT | LOCKED_CANDIDATE | Marking MPN package orientation electrical functional sample
PR-040 | PCB-MAIN | MAIN-010-R103 | MAIN-010-R39 | MAIN-010-R40 | MAIN-010-R42 | MAIN-010-R43 | MAIN-010-R50 | MAIN-010-R51 | MAIN-010-R52 | MAIN-010-R53 | MAIN-010-R54 | MAIN-010-R55 | MAIN-010-R73 | R103 | R39 | R40 | R42 | R43 | R50 | R51 | R52 | R53 | R54 | R55 | R73 | Resistor | Panasonic | ERJ-2GE0R00X | 0402 | 0 Ohm | COMMON | FITTED | 12 | 240 | 0 | 240 | 492 | 0 | 492 | COMMON_PROGRAM_PROCUREMENT | SELECTED_PENDING_REVIEW_A | Marking MPN package orientation electrical functional sample
PR-042 | PCB-PWR | PWR-R-0R | R4;R8 | Passive | Panasonic Industry | ERJ-2GE0R00X | 0402 | 0 ohm | COMMON | FITTED | 2 | 40 | 40 | 80 | 82 | 80 | 162 | COMMON_PROGRAM_PROCUREMENT | LOCKED_FITTED | Marking MPN package orientation electrical functional sample
PR-043 | PCB-MIC | R-MIC | PCB-MIC:R1 x4 | Passive | Panasonic Industry | ERJ-2GE0R00X | 0402 1005 metric | 0 ohm | COMMON | FITTED | 4 | 80 | 40 | 120 | 164 | 80 | 244 | COMMON_PROGRAM_PROCUREMENT | SELECTED_POPULATED_BASELINE_PENDING_SI | Marking MPN package orientation electrical functional sample
PR-044 | PCB-MAIN | MAIN-010-R60 | MAIN-010-R61 | R60 | R61 | Resistor | Panasonic | ERJ-2GEJ104X | 0402 | 100 kOhm 5% 0.1 W | COMMON | FITTED | 2 | 40 | 0 | 40 | 82 | 0 | 82 | COMMON_PROGRAM_PROCUREMENT | SELECTED_PENDING_REVIEW_A | Marking MPN package orientation electrical functional sample
PR-045 | PCB-MAIN | MAIN-010-R59 | R59 | Resistor | Panasonic | ERJ-2GEJ561X | 0402 | 560 Ohm 5% 0.1 W | COMMON | FITTED | 1 | 20 | 0 | 20 | 41 | 0 | 41 | COMMON_PROGRAM_PROCUREMENT | SELECTED_PENDING_REVIEW_A | Marking MPN package orientation electrical functional sample
PR-046 | PCB-MAIN | MAIN-010-R100 | MAIN-010-R102 | MAIN-010-R38 | MAIN-010-R41 | MAIN-010-R95 | R100 | R102 | R38 | R41 | R95 | Resistor | Panasonic | ERJ-2RKF1001X | 0402 | 1 kOhm 1% | COMMON | FITTED | 5 | 100 | 0 | 100 | 205 | 0 | 205 | COMMON_PROGRAM_PROCUREMENT | SELECTED_PENDING_REVIEW_A | Marking MPN package orientation electrical functional sample
PR-047 | PCB-MAIN | MAIN-010-R1 | MAIN-010-R28 | MAIN-010-R30 | MAIN-010-R31 | MAIN-010-R46 | MAIN-010-R48 | MAIN-010-R49 | MAIN-010-R67 | MAIN-010-R68 | MAIN-010-R7 | MAIN-010-R76 | MAIN-010-R78 | MAIN-010-R85 | MAIN-010-R86 | MAIN-010-R87 | MAIN-010-R88 | MAIN-010-R89 | MAIN-010-R90 | MAIN-010-R99 | R1 | R28 | R30 | R31 | R46 | R48 | R49 | R67 | R68 | R7 | R76 | R78 | R85 | R86 | R87 | R88 | R89 | R90 | R99 | Resistor | Panasonic | ERJ-2RKF1002X | 0402 | 10 kOhm 1% | COMMON | FITTED | 19 | 380 | 0 | 380 | 779 | 0 | 779 | COMMON_PROGRAM_PROCUREMENT | SELECTED_PENDING_REVIEW_A | Marking MPN package orientation electrical functional sample
PR-049 | PCB-PWR | PWR-R-10K | R10;R12 | Passive | Panasonic Industry | ERJ-2RKF1002X | 0402 | 10 kOhm 1% | COMMON | FITTED | 2 | 40 | 40 | 80 | 82 | 80 | 162 | COMMON_PROGRAM_PROCUREMENT | LOCKED_FITTED | Marking MPN package orientation electrical functional sample
PR-051 | PCB-MAIN | MAIN-010-R19 | MAIN-010-R2 | MAIN-010-R20 | MAIN-010-R21 | MAIN-010-R22 | MAIN-010-R23 | MAIN-010-R29 | MAIN-010-R3 | MAIN-010-R32 | MAIN-010-R33 | MAIN-010-R34 | MAIN-010-R35 | MAIN-010-R45 | MAIN-010-R47 | MAIN-010-R5 | MAIN-010-R63 | MAIN-010-R64 | MAIN-010-R65 | MAIN-010-R66 | MAIN-010-R77 | MAIN-010-R96 | R19 | R2 | R20 | R21 | R22 | R23 | R29 | R3 | R32 | R33 | R34 | R35 | R45 | R47 | R5 | R63 | R64 | R65 | R66 | R77 | R96 | Resistor | Panasonic | ERJ-2RKF1003X | 0402 | 100 kOhm 1% | COMMON | FITTED | 21 | 420 | 0 | 420 | 861 | 0 | 861 | COMMON_PROGRAM_PROCUREMENT | SELECTED_PENDING_REVIEW_A | Marking MPN package orientation electrical functional sample
PR-052 | PCB-PWR | PWR-R-100K | R6;R11 | Passive | Panasonic Industry | ERJ-2RKF1003X | 0402 | 100 kOhm 1% | COMMON | FITTED | 2 | 40 | 40 | 80 | 82 | 80 | 162 | COMMON_PROGRAM_PROCUREMENT | LOCKED_FITTED | Marking MPN package orientation electrical functional sample
PR-053 | PCB-MAIN | MAIN-010-R97 | R97 | Resistor | Panasonic | ERJ-2RKF1004X | 0402 | 1 MOhm 1% | COMMON | FITTED | 1 | 20 | 0 | 20 | 41 | 0 | 41 | COMMON_PROGRAM_PROCUREMENT | SELECTED_PENDING_REVIEW_A | Marking MPN package orientation electrical functional sample
PR-054 | PCB-MAIN | MAIN-010-R13 | MAIN-010-R14 | R13 | R14 | Resistor | Panasonic | ERJ-2RKF2201X | 0402 | 2.2 kOhm 1% | COMMON | FITTED | 2 | 40 | 0 | 40 | 82 | 0 | 82 | COMMON_PROGRAM_PROCUREMENT | SELECTED_PENDING_REVIEW_A | Marking MPN package orientation electrical functional sample
PR-055 | PCB-MAIN | MAIN-010-R10 | MAIN-010-R101 | MAIN-010-R11 | MAIN-010-R12 | MAIN-010-R15 | MAIN-010-R16 | MAIN-010-R17 | MAIN-010-R18 | MAIN-010-R36 | MAIN-010-R37 | MAIN-010-R56 | MAIN-010-R57 | MAIN-010-R58 | MAIN-010-R69 | MAIN-010-R70 | MAIN-010-R71 | MAIN-010-R72 | MAIN-010-R74 | MAIN-010-R75 | MAIN-010-R79 | MAIN-010-R8 | MAIN-010-R80 | MAIN-010-R81 | MAIN-010-R82 | MAIN-010-R83 | MAIN-010-R84 | MAIN-010-R9 | MAIN-010-R91 | MAIN-010-R92 | R10 | R101 | R11 | R12 | R15 | R16 | R17 | R18 | R36 | R37 | R56 | R57 | R58 | R69 | R70 | R71 | R72 | R74 | R75 | R79 | R8 | R80 | R81 | R82 | R83 | R84 | R9 | R91 | R92 | Resistor | Panasonic | ERJ-2RKF22R0X | 0402 | 22 Ohm 1% | COMMON | FITTED | 29 | 580 | 0 | 580 | 1189 | 0 | 1189 | COMMON_PROGRAM_PROCUREMENT | SELECTED_PENDING_REVIEW_A | Marking MPN package orientation electrical functional sample
PR-056 | PCB-MAIN | MAIN-010-R24 | MAIN-010-R26 | R24 | R26 | Resistor | Panasonic | ERJ-2RKF4701X | 0402 | 4.7 kOhm 1% | COMMON | FITTED | 2 | 40 | 0 | 40 | 82 | 0 | 82 | COMMON_PROGRAM_PROCUREMENT | SELECTED_PENDING_REVIEW_A | Marking MPN package orientation electrical functional sample
PR-058 | PCB-MAIN | MAIN-010-R25 | MAIN-010-R27 | MAIN-010-R44 | R25 | R27 | R44 | Resistor | Panasonic | ERJ-2RKF4702X | 0402 | 47 kOhm 1% | COMMON | FITTED | 3 | 60 | 0 | 60 | 123 | 0 | 123 | COMMON_PROGRAM_PROCUREMENT | SELECTED_PENDING_REVIEW_A | Marking MPN package orientation electrical functional sample
PR-059 | PCB-MAIN | MAIN-010-R93 | MAIN-010-R94 | R93 | R94 | Resistor | Panasonic | ERJ-2RKF5101X | 0402 | 5.1 kOhm 1% | COMMON | FITTED | 2 | 40 | 0 | 40 | 82 | 0 | 82 | COMMON_PROGRAM_PROCUREMENT | SELECTED_PENDING_REVIEW_A | Marking MPN package orientation electrical functional sample
PR-060 | PCB-MAIN | MAIN-010-R62 | R62 | Resistor | Panasonic | ERJ-8GEYJ100V | 1206 | 10 Ohm 5% 0.25 W | COMMON | FITTED | 1 | 20 | 0 | 20 | 41 | 0 | 41 | COMMON_PROGRAM_PROCUREMENT | SELECTED_PENDING_REVIEW_A | Marking MPN package orientation electrical functional sample
PR-061 | PCB-MAIN | U14-U15 | U14;U15 | ESD | STMicroelectronics | ESDALC6V1-5P6 | SOT666_1.6x1.6mm |  | COMMON | FITTED | 2 | 40 | 10 | 50 | 82 | 20 | 102 | COMMON_PROGRAM_PROCUREMENT | SELECTED_PENDING_SIM_ESD_SI_SAMPLE | Capacitance leakage ESD rating marking
PR-062 | SYSTEM | ANT-CELL | AE1 | Antenna | Taoglas | G30.B.108111 | IP67 screw-mount dome with 1 m cable and SMA(M) |  | COMMON | FITTED | 1 | 20 | 2 | 22 | 41 | 4 | 45 | COMMON_PROGRAM_PROCUREMENT | CONTROLLED_EVT_PURCHASE_EXACT_MPN_VALIDATION_DURING_ASSEMBLY_EVT | Reconcile PO packing slip quantity and visible damage; verify cable length connector mate route seal installed VSWR loss attach and coexistence during assembly EOL and EVT
PR-063 | PCB-MAIN | MAIN-010-C64 | C64 | Capacitor | Murata | GRM1555C1E470JA01D | 0402 | 47 pF 25 V C0G | COMMON | FITTED | 1 | 20 | 0 | 20 | 41 | 0 | 41 | COMMON_PROGRAM_PROCUREMENT | SELECTED_PENDING_REVIEW_A | Marking MPN package orientation electrical functional sample
PR-065 | PCB-MAIN | MAIN-010-C43 | MAIN-010-C47 | C43 | C47 | Capacitor | Murata | GRM1555C1H100JA01D | 0402 | 10 pF 50 V C0G | COMMON | FITTED | 2 | 40 | 0 | 40 | 82 | 0 | 82 | COMMON_PROGRAM_PROCUREMENT | SELECTED_PENDING_REVIEW_A | Marking MPN package orientation electrical functional sample
PR-066 | PCB-MAIN | MAIN-010-C40 | C40 | Capacitor | Murata | GRM1555C1H101JA01D | 0402 | 100 pF 50 V C0G | COMMON | FITTED | 1 | 20 | 0 | 20 | 41 | 0 | 41 | COMMON_PROGRAM_PROCUREMENT | SELECTED_PENDING_REVIEW_A | Marking MPN package orientation electrical functional sample
PR-067 | PCB-MAIN | MAIN-010-C39 | C39 | Capacitor | Murata | GRM1555C1H151JA01D | 0402 | 150 pF 50 V C0G | COMMON | FITTED | 1 | 20 | 0 | 20 | 41 | 0 | 41 | COMMON_PROGRAM_PROCUREMENT | SELECTED_PENDING_REVIEW_A | Marking MPN package orientation electrical functional sample
PR-069 | PCB-MAIN | MAIN-010-C42 | MAIN-010-C46 | C42 | C46 | Capacitor | Murata | GRM1555C1H330JA01D | 0402 | 33 pF 50 V C0G | COMMON | FITTED | 2 | 40 | 0 | 40 | 82 | 0 | 82 | COMMON_PROGRAM_PROCUREMENT | SELECTED_PENDING_REVIEW_A | Marking MPN package orientation electrical functional sample
PR-070 | PCB-MAIN | MAIN-010-C41 | C41 | Capacitor | Murata | GRM1555C1H680JA01D | 0402 | 68 pF 50 V C0G | COMMON | FITTED | 1 | 20 | 0 | 20 | 41 | 0 | 41 | COMMON_PROGRAM_PROCUREMENT | SELECTED_PENDING_REVIEW_A | Marking MPN package orientation electrical functional sample
PR-071 | PCB-MAIN | MAIN-010-C14 | MAIN-010-C15 | C14 | C15 | Capacitor | Murata | GRM155R61A225KE15D | 0402 | 2.2 uF 10 V X5R | COMMON | FITTED | 2 | 40 | 0 | 40 | 82 | 0 | 82 | COMMON_PROGRAM_PROCUREMENT | SELECTED_PENDING_REVIEW_A | Marking MPN package orientation electrical functional sample
PR-072 | PCB-MAIN | MAIN-010-C11 | MAIN-010-C22 | MAIN-010-C9 | C11 | C22 | C9 | Capacitor | Murata | GRM155R61C105KA12D | 0402 | 1 uF 16 V X5R | COMMON | FITTED | 3 | 60 | 0 | 60 | 123 | 0 | 123 | COMMON_PROGRAM_PROCUREMENT | SELECTED_PENDING_REVIEW_A | Marking MPN package orientation electrical functional sample
PR-073 | PCB-MAIN | MAIN-010-C63 | C63 | Capacitor | Murata | GRM155R71C103KA01D | 0402 | 10 nF 16 V X7R | COMMON | FITTED | 1 | 20 | 0 | 20 | 41 | 0 | 41 | COMMON_PROGRAM_PROCUREMENT | SELECTED_PENDING_REVIEW_A | Marking MPN package orientation electrical functional sample
PR-074 | PCB-MAIN | MAIN-010-C48 | MAIN-010-C52 | MAIN-010-C53 | MAIN-010-C76 | MAIN-010-C78 | C48 | C52 | C53 | C76 | C78 | Capacitor | Murata | GRM155R71E103KA01D | 0402 | 10 nF 25 V X7R | COMMON | FITTED | 5 | 100 | 0 | 100 | 205 | 0 | 205 | COMMON_PROGRAM_PROCUREMENT | SELECTED_PENDING_REVIEW_A | Marking MPN package orientation electrical functional sample
PR-076 | PCB-MAIN | MAIN-010-C1 | MAIN-010-C10 | MAIN-010-C12 | MAIN-010-C18 | MAIN-010-C2 | MAIN-010-C21 | MAIN-010-C23 | MAIN-010-C25 | MAIN-010-C26 | MAIN-010-C27 | MAIN-010-C28 | MAIN-010-C29 | MAIN-010-C3 | MAIN-010-C30 | MAIN-010-C31 | MAIN-010-C32 | MAIN-010-C33 | MAIN-010-C34 | MAIN-010-C35 | MAIN-010-C4 | MAIN-010-C45 | MAIN-010-C49 | MAIN-010-C5 | MAIN-010-C50 | MAIN-010-C51 | MAIN-010-C60 | MAIN-010-C62 | MAIN-010-C65 | MAIN-010-C66 | MAIN-010-C68 | MAIN-010-C7 | MAIN-010-C71 | MAIN-010-C73 | MAIN-010-C74 | MAIN-010-C8 | C1 | C10 | C12 | C18 | C2 | C21 | C23 | C25 | C26 | C27 | C28 | C29 | C3 | C30 | C31 | C32 | C33 | C34 | C35 | C4 | C45 | C49 | C5 | C50 | C51 | C60 | C62 | C65 | C66 | C68 | C7 | C71 | C73 | C74 | C8 | Capacitor | Murata | GRM155R71E104KE14D | 0402 | 100 nF 25 V X7R | COMMON | FITTED | 35 | 700 | 0 | 700 | 1435 | 0 | 1435 | COMMON_PROGRAM_PROCUREMENT | SELECTED_PENDING_REVIEW_A | Marking MPN package orientation electrical functional sample
PR-077 | PCB-MAIN | MAIN-010-C37 | C37 | Capacitor | Murata | GRM155R71E224KE14D | 0402 | 220 nF 25 V X7R | COMMON | FITTED | 1 | 20 | 0 | 20 | 41 | 0 | 41 | COMMON_PROGRAM_PROCUREMENT | SELECTED_PENDING_REVIEW_A | Marking MPN package orientation electrical functional sample
PR-078 | PCB-MAIN | MAIN-010-C38 | C38 | Capacitor | Murata | GRM155R71E473KA01D | 0402 | 47 nF 25 V X7R | COMMON | FITTED | 1 | 20 | 0 | 20 | 41 | 0 | 41 | COMMON_PROGRAM_PROCUREMENT | SELECTED_PENDING_REVIEW_A | Marking MPN package orientation electrical functional sample
PR-079 | PCB-MAIN | MAIN-010-C77 | C77 | Capacitor | Murata | GRM155R72A472KA01D | 0402 | 4.7 nF 100 V X7R | COMMON | FITTED | 1 | 20 | 0 | 20 | 41 | 0 | 41 | COMMON_PROGRAM_PROCUREMENT | SELECTED_PENDING_REVIEW_A | Marking MPN package orientation electrical functional sample
PR-080 | PCB-MAIN | MAIN-010-C13 | MAIN-010-C20 | MAIN-010-C24 | MAIN-010-C6 | MAIN-010-C61 | MAIN-010-C67 | MAIN-010-C72 | MAIN-010-C75 | C13 | C20 | C24 | C6 | C61 | C67 | C72 | C75 | Capacitor | Murata | GRM188R61A106KE69D | 0603 | 10 uF 10 V X5R | COMMON | FITTED | 8 | 160 | 0 | 160 | 328 | 0 | 328 | COMMON_PROGRAM_PROCUREMENT | SELECTED_PENDING_REVIEW_A | Marking MPN package orientation electrical functional sample
PR-081 | PCB-MAIN | MAIN-010-C19 | C19 | Capacitor | Murata | GRM21BR61A226ME44L | 0805 | 22 uF 10 V X5R | COMMON | FITTED | 1 | 20 | 0 | 20 | 41 | 0 | 41 | COMMON_PROGRAM_PROCUREMENT | SELECTED_PENDING_REVIEW_A | Marking MPN package orientation electrical functional sample
PR-082 | PCB-PWR | U-MON-01 | U2 | Monitor | Texas Instruments | INA226AIDGSR | VSSOP-10 |  | COMMON | FITTED | 1 | 20 | 5 | 25 | 41 | 10 | 51 | COMMON_PROGRAM_PROCUREMENT | SELECTED_REV_A_12PIN_I2C | Marking I2C ID calibration and reference-meter compare
PR-083 | PCB-MAIN | U3 | U3 | Motion | STMicroelectronics | LIS2DW12TR | LGA-12_2x2mm |  | COMMON | FITTED | 1 | 20 | 5 | 25 | 41 | 10 | 51 | COMMON_PROGRAM_PROCUREMENT | SELECTED_PENDING_SAMPLE | Marking orientation WHO_AM_I and self-test
PR-084 | PCB-PWR | PWR-REV-CTL | U1 | Protection | Texas Instruments | LM74700QDBVRQ1 | SOT-23-6 |  | COMMON | FITTED | 1 | 20 | 5 | 25 | 41 | 10 | 51 | COMMON_PROGRAM_PROCUREMENT | SELECTED_PENDING_SCHEMATIC_SAMPLE | Marking reverse test and gate waveform
PR-085 | PCB-PWR | U-PWR1 | U-PWR2 | U3 | U4 | Power | Texas Instruments | LMR604403SRAKR | RAK-9 |  | COMMON | FITTED | 2 | 40 | 10 | 50 | 82 | 20 | 102 | COMMON_PROGRAM_PROCUREMENT | SELECTED_PENDING_DESIGN_CALC_SAMPLE | Load step ripple efficiency sleep current thermal and EMI | Load step ripple efficiency thermal and EMI
PR-086 | PCB-MAIN | MAIN-010-L1 | L1 | Inductor | Murata | LQH32PN2R2NN0L | 1210 | 2.2 uH 20% | COMMON | FITTED | 1 | 20 | 0 | 20 | 41 | 0 | 41 | COMMON_PROGRAM_PROCUREMENT | SELECTED_PENDING_REVIEW_A | Marking MPN package orientation electrical functional sample
PR-087 | PCB-MAIN | MAIN-010-L2 | L2 | Inductor | Murata | LQW15AN27NJ00D | 0402 | 27 nH 5% | COMMON | FITTED | 1 | 20 | 0 | 20 | 41 | 0 | 41 | COMMON_PROGRAM_PROCUREMENT | SELECTED_PENDING_REVIEW_A | Marking MPN package orientation electrical functional sample
PR-088 | PCB-MAIN | MAIN-010-U5 | U5 | Operational_Amplifier | Analog Devices | LT6000IDCB#TRMPBF | DFN-6_DCB_2x3mm | Single rail-to-rail low-power op amp | COMMON | FITTED | 1 | 20 | 0 | 20 | 41 | 0 | 41 | COMMON_PROGRAM_PROCUREMENT | SELECTED_PENDING_REVIEW_A | Marking MPN package orientation electrical functional sample
PR-089 | PCB-MAIN | U9 | U9 | GNSS | u-blox | MAX-M10S-00B | LCC-18_9.7x10.1mm |  | COMMON | FITTED | 1 | 20 | 5 | 25 | 41 | 10 | 51 | COMMON_PROGRAM_PROCUREMENT | SELECTED_PENDING_GNSS_RF_TIMING_SAMPLE | Marking firmware satellite fix PPS test
PR-090 | PCB-MAIN | U11 | U11 | BLE | Raytac | MDBT50Q-P1MV2 | nRF52840_SMD_10.5x15.5_61P_PCB_antenna |  | COMMON | FITTED | 1 | 20 | 5 | 25 | 41 | 10 | 51 | COMMON_PROGRAM_PROCUREMENT | SELECTED_PENDING_ENCLOSURE_RF | Module label firmware BLE 2M coded PHY pairing OTA current RF range and temperature test
PR-091 | PCB-MAIN | J-SD1 | J12 | Connector | GCT | MEM2052-00-195-00-A | microSD push-push SMT 1.95 mm with detect |  | COMMON | FITTED | 1 | 20 | 5 | 25 | 41 | 10 | 51 | COMMON_PROGRAM_PROCUREMENT | MECHANICAL_AUTHORITY_FROZEN_PENDING_PHYSICAL_TEST | Mating detect coplanarity and cycle sample
PR-092 | PCB-MAIN | Q-MODEM-PWRKEY | Q-MODEM-RESET | Q-SIM-MUX-EN | Q1 | Q2 | Q3 | Transistor | Nexperia | MMBT3904,215 | SOT23 |  | COMMON | FITTED | 3 | 60 | 15 | 75 | 123 | 30 | 153 | COMMON_PROGRAM_PROCUREMENT | SELECTED_PENDING_CONTROL_TIMING_SAMPLE | SELECTED_PENDING_SIM_SAFE_STATE_SAMPLE | Marking MPN package orientation electrical functional sample
PR-093 | PCB-MIC | MK1 | MK1 | Microphone | TDK InvenSense | MMICT5838-00-012 | LGA-CAV-5 3.5x2.65x0.98 mm |  | COMMON | FITTED | 4 | 80 | 16 | 96 | 164 | 32 | 196 | COMMON_PROGRAM_PROCUREMENT | SELECTED_PENDING_SAMPLE | Marking lot acoustic sensitivity noise phase and port inspection
PR-094 | PCB-PWR | PWR-NET-TIE | NT1;NT2;NT3 | PCB feature | PCB fabrication | NET_TIE_COPPER_REV_A | NetTie-2 SMD pad 0.5 mm | 2-pad copper net tie | COMMON | PCB_FEATURE | 3 | 60 | 0 | 60 | 123 | 0 | 123 | COMMON_PROGRAM_PROCUREMENT | LOCKED_LAYOUT_PENDING | Marking MPN package orientation electrical functional sample
PR-095 | PCB-MAIN | MAIN-010-D3 | MAIN-010-D5 | D3 | D5 | RF_ESD | Nexperia | PESD5V0C1BSF | SOD962-2 | 5 V bidirectional 0.2 pF RF ESD | COMMON | FITTED | 2 | 40 | 0 | 40 | 82 | 0 | 82 | COMMON_PROGRAM_PROCUREMENT | SELECTED_PENDING_REVIEW_A | Marking MPN package orientation electrical functional sample
PR-096 | PCB-MAIN | MAIN-010-D1 | MAIN-010-D2 | D1 | D2 | Supply_TVS | Nexperia | PESD5V0S1UL | SOD882 | 5 V unidirectional 150 W TVS | COMMON | FITTED | 2 | 40 | 0 | 40 | 82 | 0 | 82 | COMMON_PROGRAM_PROCUREMENT | SELECTED_PENDING_REVIEW_A | Marking MPN package orientation electrical functional sample
PR-097 | SYSTEM | BAT1 | BT1 | Battery | RELiON | RB40 | 197x166x173 mm IP66 M8 pack |  | COMMON | FITTED | 1 | 20 | 1 | 21 | 41 | 2 | 43 | COMMON_PROGRAM_PROCUREMENT | CONTROLLED_EVT_PURCHASE_EXACT_MPN_VALIDATION_DURING_ASSEMBLY_EVT | Reconcile PO packing slip quantity and visible damage; check every unit polarity and open-circuit voltage at installation; capacity DCIR BMS and cold behavior during assembly and EVT
PR-098 | SYSTEM | MPPT-TEMP | TS-BAT1 | Sensor | Victron Energy | SBS050150200 | Smart Battery Sense long range up to 10 m radio with 0.45 m leads and M10 eyelets |  | COMMON | FITTED | 1 | 20 | 1 | 21 | 41 | 2 | 43 | COMMON_PROGRAM_PROCUREMENT | CONTROLLED_EVT_PURCHASE_EXACT_MPN_VALIDATION_DURING_ASSEMBLY_EVT | Reconcile PO packing slip quantity and visible damage; verify 0.45 m lead M10 eyelets retention accuracy VE.Smart pairing cutoff reconnect and network retention during station assembly EOL and cold EVT
PR-099 | SYSTEM | MPPT1 | U-MPPT | Controller | Victron Energy | SCC075010060R | 100x113x40 mm IP43 electronics IP22 terminals |  | COMMON | FITTED | 1 | 20 | 1 | 21 | 41 | 2 | 43 | COMMON_PROGRAM_PROCUREMENT | CONTROLLED_EVT_PURCHASE_EXACT_MPN_VALIDATION_DURING_ASSEMBLY_EVT | Reconcile PO packing slip quantity and visible damage; bind article and firmware at installation; export configuration and test charge profile reverse current quiescent thermal and cutoff during assembly EOL and EVT
PR-100 | PCB-MAIN | U12 | U12 | Storage | Kingston | SDCIT2/32GB | microSD_card_8_contact |  | COMMON | FITTED | 1 | 20 | 5 | 25 | 41 | 10 | 51 | COMMON_PROGRAM_PROCUREMENT | SELECTED_PENDING_SAMPLE_ENDURANCE | CID capacity full write/read temperature and power-loss sample
PR-101 | SYSTEM | PV1 | PV1 | Solar panel | SLD Tech / Solarland | SLP080S-12M | 1475x342x40 mm framed 36-cell panel |  | COMMON | FITTED | 1 | 20 | 1 | 21 | 41 | 2 | 43 | COMMON_PROGRAM_PROCUREMENT | CONTROLLED_EVT_PURCHASE_EXACT_MPN_VALIDATION_DURING_ASSEMBLY_EVT | Reconcile PO packing slip quantity and visible transit damage; measure installed-unit Voc and perform IV insulation wet-leakage cold-Voc bracket cable and transport validation during assembly and EVT
PR-102 | PCB-PWR | PWR-TVS-01 | D1 | Protection | Littelfuse | SMBJ18A | SMB_DO-214AA |  | COMMON | FITTED | 1 | 20 | 5 | 25 | 41 | 10 | 51 | COMMON_PROGRAM_PROCUREMENT | CANDIDATE_PENDING_SURGE_PROFILE | Marking clamp pulse and thermal sample
PR-103 | PCB-MAIN | U18 | U18 | Logic | Texas Instruments | SN74AXC1T45DRLR | SOT-5X3_6 |  | COMMON | FITTED | 1 | 20 | 5 | 25 | 41 | 10 | 51 | COMMON_PROGRAM_PROCUREMENT | SELECTED_PENDING_AAD_WAKE_TEST | Marking MPN package orientation electrical functional sample
PR-104 | PCB-MAIN | U16 | U7 | U16 | U7 | Level translator | Logic | Texas Instruments | SN74AXC8T245PWR | TSSOP-24 |  | COMMON | FITTED | 2 | 40 | 10 | 50 | 82 | 20 | 102 | COMMON_PROGRAM_PROCUREMENT | SELECTED_PENDING_SI_AAD_SAMPLE | SELECTED_PENDING_UART_POWER_SAMPLE | Logic levels direction leakage sleep test | Marking MPN package orientation electrical functional sample
PR-105 | PCB-MAIN | MAIN-010-U6 | U6 | Open_Drain_Buffer | Texas Instruments | SN74LVC1G07DBVR | SOT-23-5_DBV | Single non-inverting open-drain buffer | COMMON | FITTED | 1 | 20 | 0 | 20 | 41 | 0 | 41 | COMMON_PROGRAM_PROCUREMENT | SELECTED_PENDING_REVIEW_A | Marking MPN package orientation electrical functional sample
PR-106 | PCB-MAIN | U17 | U17 | Logic | Texas Instruments | SN74LVC32APWR | TSSOP-14 |  | COMMON | FITTED | 1 | 20 | 5 | 25 | 41 | 10 | 51 | COMMON_PROGRAM_PROCUREMENT | SELECTED_PENDING_AAD_WAKE_TEST | Marking MPN package orientation electrical functional sample
PR-107 | PCB-MAIN | U1 | U1 | MCU | STMicroelectronics | STM32U585VIT6Q | LQFP100_14x14 |  | COMMON | FITTED | 1 | 20 | 5 | 25 | 41 | 10 | 51 | COMMON_PROGRAM_PROCUREMENT | SELECTED_PENDING_TARGET_SAMPLE | Label lot date code package X-ray sample ID readout
PR-108 | PCB-MAIN | U4 | U4 | Temperature | STMicroelectronics | STTS22HTR | UDFN-6L_2x2mm |  | COMMON | FITTED | 1 | 20 | 5 | 25 | 41 | 10 | 51 | COMMON_PROGRAM_PROCUREMENT | SELECTED_PENDING_ASSEMBLY_REVIEW | X-ray sample ID and temperature compare
PR-109 | PCB-MAIN | MAIN-010-Q4 | Q4 | Dual_MOSFET | Vishay | Si1016X-T1-GE3 | SOT-563_SC-89 | Complementary N and P channel 20 V | COMMON | FITTED | 1 | 20 | 0 | 20 | 41 | 0 | 41 | COMMON_PROGRAM_PROCUREMENT | SELECTED_PENDING_REVIEW_A | Marking MPN package orientation electrical functional sample
PR-110 | PCB-MAIN | X1 | X1 | Clock | SiTime | SiT1552AI-JE-DCC-32.768D | CSP-4_1.5x0.8mm | 32.768 kHz full-swing LVCMOS | COMMON | FITTED | 1 | 20 | 5 | 25 | 41 | 10 | 51 | COMMON_PROGRAM_PROCUREMENT | SELECTED_PENDING_LSE_BYPASS_REVIEW | Frequency and current sample test
PR-111 | PCB-MAIN | MAIN-010-C36 | MAIN-010-C44 | C36 | C44 | Capacitor | KEMET | T520D107M006ATE015 | 7343-31 | 100 uF 6.3 V 15 mOhm polymer | COMMON | FITTED | 2 | 40 | 0 | 40 | 82 | 0 | 82 | COMMON_PROGRAM_PROCUREMENT | SELECTED_PENDING_REVIEW_A | Marking MPN package orientation electrical functional sample
PR-112 | SYSTEM | ANT-LORA | AE3 | Antenna | Taoglas | TI.89.B.2111W | IP67 terminal antenna 180x13 mm SMA(M) |  | RU868_PILOT | FITTED | 1 | 20 | 2 | 22 | 41 | 4 | 45 | COMMON_PROGRAM_PROCUREMENT | CONTROLLED_EVT_PURCHASE_EXACT_MPN_VALIDATION_DURING_ASSEMBLY_EVT | Reconcile PO packing slip quantity and visible damage; verify connector mate installed VSWR conducted power sensitivity coexistence and RU868 radiated compliance during assembly EOL and EVT
PR-113 | PCB-MAIN | MAIN-010-D10 | MAIN-010-D11 | MAIN-010-D6 | MAIN-010-D7 | MAIN-010-D8 | MAIN-010-D9 | D10 | D11 | D6 | D7 | D8 | D9 | ESD_Diode | Texas Instruments | TPD1E05U06DYAR | SOD-523_DYA | 5.5 V 0.5 pF ESD | COMMON | FITTED | 6 | 120 | 0 | 120 | 246 | 0 | 246 | COMMON_PROGRAM_PROCUREMENT | SELECTED_PENDING_REVIEW_A | Marking MPN package orientation electrical functional sample
PR-114 | PCB-MAIN | MAIN-010-D4 | D4 | RF_ESD | Texas Instruments | TPD1E05U06DYAR | SOD-523_DYA | 5.5 V unidirectional 0.5 pF RF ESD | COMMON | FITTED | 1 | 20 | 0 | 20 | 41 | 0 | 41 | COMMON_PROGRAM_PROCUREMENT | SELECTED_PENDING_REVIEW_A | Marking MPN package orientation electrical functional sample
PR-115 | PCB-MAIN | MAIN-010-U25 | MAIN-010-U26 | U25 | U26 | USB_ESD_Array | Texas Instruments | TPD2EUSB30DRTR | SOT-9X3_DRT | 2 channel 0.7 pF USB ESD | COMMON | FITTED | 2 | 40 | 0 | 40 | 82 | 0 | 82 | COMMON_PROGRAM_PROCUREMENT | SELECTED_PENDING_REVIEW_A | Marking MPN package orientation electrical functional sample
PR-116 | PCB-MAIN | MAIN-010-U19 | MAIN-010-U20 | MAIN-010-U21 | MAIN-010-U22 | MAIN-010-U23 | MAIN-010-U24 | MAIN-010-U27 | U19 | U20 | U21 | U22 | U23 | U24 | U27 | ESD_Array | Texas Instruments | TPD4E05U06DQAR | USON-10_DQA | 4 channel 0.5 pF ESD | COMMON | FITTED | 7 | 140 | 0 | 140 | 287 | 0 | 287 | COMMON_PROGRAM_PROCUREMENT | SELECTED_PENDING_REVIEW_A | Marking MPN package orientation electrical functional sample
PR-117 | PCB-PWR | U-PWR3 | U5 | Power | Texas Instruments | TPS7A2018PDBVR | SOT-23-5 |  | COMMON | FITTED | 1 | 20 | 5 | 25 | 41 | 10 | 51 | COMMON_PROGRAM_PROCUREMENT | SELECTED_PENDING_NOISE_SAMPLE | Noise PSRR dropout thermal and AAD sleep current
PR-118 | PCB-MAIN | U13 | U13 | SIM switch | Texas Instruments | TS3A27518EPWR | TSSOP-24_PW |  | COMMON | FITTED | 1 | 20 | 5 | 25 | 41 | 10 | 51 | COMMON_PROGRAM_PROCUREMENT | SELECTED_PENDING_USIM_SI_SAMPLE | Marking supply leakage Ron capacitance and 100 switch cycles
PR-119 | PCB-MAIN | J-RF-CELL | J-RF-GNSS | J8 | J9 | RF connector | Hirose | U.FL-R-SMT-1(60) | U.FL SMT receptacle |  | COMMON | FITTED | 2 | 40 | 16 | 56 | 82 | 32 | 114 | COMMON_PROGRAM_PROCUREMENT | LAYOUT_ZONE_FROZEN_PENDING_RF_VALIDATION | Visual mate gauge continuity VNA and VSWR | Visual mate gauge continuity receiver sensitivity and active-antenna current
PR-120 | PCB-MAIN | J-RF-LORA | J10 | RF connector | Hirose | U.FL-R-SMT-1(60) | U.FL SMT receptacle |  | RU868_PILOT | FITTED | 1 | 20 | 8 | 28 | 41 | 16 | 57 | COMMON_PROGRAM_PROCUREMENT | LAYOUT_ZONE_FROZEN_PENDING_RF_VALIDATION | Visual mate gauge continuity conducted power sensitivity and VSWR
PR-121 | PCB-MAIN | J-USB | J11 | Connector | GCT | USB4105-GF-A-120 | 16 positions |  | COMMON | FITTED | 1 | 20 | 5 | 25 | 41 | 10 | 51 | COMMON_PROGRAM_PROCUREMENT | MECHANICAL_AUTHORITY_FROZEN_PENDING_PHYSICAL_TEST | Marking MPN package orientation electrical functional sample
PR-122 | PCB-MAIN | U2 | U2 | Memory | Winbond | W25Q512JVFIQ | SOIC-16_300mil |  | COMMON | FITTED | 1 | 20 | 5 | 25 | 41 | 10 | 51 | COMMON_PROGRAM_PROCUREMENT | SELECTED_PENDING_SAMPLE | Marking electrical ID read/write/erase soak
PR-123 | PCB-PWR | R-SHUNT-01 | RSH1 | Shunt | Vishay Dale | WSK2512R0100FEA | WSK2512 4-terminal 6.35x3.18 mm | 10 mOhm 1% 1 W | COMMON | FITTED | 1 | 20 | 10 | 30 | 41 | 20 | 61 | COMMON_PROGRAM_PROCUREMENT | SELECTED_PENDING_KELVIN_LAYOUT_SAMPLE | Resistance TCR marking and four-wire reference measurement
PR-124 | PCB-PWR | PWR-L | L1;L2 | Passive | Coilcraft | XAL7030-472MEC | XAL7030 | 4.7 uH +/-20% | COMMON | FITTED | 2 | 40 | 10 | 50 | 82 | 20 | 102 | COMMON_PROGRAM_PROCUREMENT | SELECTED_PENDING_LAYOUT_THERMAL_EMI | Marking MPN package orientation electrical functional sample
