skif-ops/rs-zs-bpla/releases/evt-pre-20/2026-10-02-rev-d5/Основной_пакет/01_Закупка/BOM_EVT_PRE_20_оценочные_цены.xlsx

Sheet: Сводка закупки
Дионея · EVT-PRE-20 · закупочный BOM
Первый лот: 20 станций, корпуса 3D-печать. Программа: 2 × 20 + 1 стендовый образец; отдельная колонка показывает вариант печати всех 40 опытных корпусов.
Цены v02 — исторический инженерный ориентир по 50 строкам: 561 805,89 ₽ за 20 станций; 617 986,48 ₽ с резервом 10%.
Сумма v02 относится к прежней конфигурации с литьём и не является ценой этого заказа. Для печатных корпусов и многих текущих MPN цены нет.
Rev D: платы MAIN 22, PWR 22 и MIC 80 заказываются и изготавливаются полными партиями без паузы; DFM и фактический стек подтверждаются до запуска панели.
Энергосистема в сводке: аккумулятор RB40 - PR-097, MPPT - PR-099, солнечная панель SLP080S-12M - PR-101; количества первого лота 21/21/21 с резервом.
ID | Узел | Позиция | Обозначения | Категория | Производитель | MPN | Исполнение | Монтаж | На станцию | Потребность лота 20 | План 41 | Расчёт программы | Вариант: 40 печатных | Цена ед. ₽ v02 | Строка v02 | Статус цены | Статус изделия
PR-001 | PCB-MAIN | ASM-MAIN | - | PCBA | Dioneya controlled design | DIO-ASM-MAIN-REV-B | 8-layer PCB-MAIN Rev B PCBA; fab DFM stack and via-in-pad approval pending | N/A | 1.00 | 22.00 | 41.00 | 45.00 |  | 1020.91 | 32.00 | HISTORICAL_ANALOG_NOT_QUOTE | CONTROLLED_INTERNAL_ARTICLE_CUSTOMER_EMS_SELECTION_PENDING
PR-002 | PCB-MIC | ASM-MIC | - | PCBA | Dioneya controlled design | DIO-ASM-MIC-REV-B | 2-layer PCB-MIC Rev B PCBA; 24x22x1.0 mm; ENIG; full lot 80 no pause; post-lot acoustic sample | N/A | 4.00 | 80.00 | 164.00 | 168.00 |  | 340.30 | 33.00 | HISTORICAL_ANALOG_NOT_QUOTE | REVIEW_B_DESIGN_ACCEPT_CUSTOMER_FULL_LOT_NO_PAUSE
PR-003 | PCB-PWR | ASM-PWR | - | PCBA | Dioneya controlled design | DIO-ASM-PWR-REV-A | 4-layer PCB-PWR Rev A PCBA; 90x60x1.6 mm; ENIG; 1 oz / 35 um copper on all four layers; fabricator stack ID and DFM at checkout | N/A | 1.00 | 22.00 | 41.00 | 45.00 |  | 680.61 | 34.00 | HISTORICAL_ANALOG_NOT_QUOTE | CONTROLLED_INTERNAL_ARTICLE_CUSTOMER_EMS_SELECTION_PENDING
PR-004 | SYSTEM | HARNESS | - | Harness | Dioneya controlled design | DIO-HARNESS-SET-EVT-D | 6-harness controlled set: 4x MIC 275+/-5 mm; MAIN-PWR 440+/-5 mm; BAT-PWR 330+/-5 mm; 38 conductors | FITTED | 1.00 | 22.00 | 41.00 | 45.00 |  | 1413.11 | 38.00 | HISTORICAL_ANALOG_NOT_QUOTE | RELEASED_CONTROLLED_FIRST_ARTICLE
PR-005 | SYSTEM | HSG-3D | HSG1 | Housing | Dioneya preliminary design | DIO-HSG-3D-PRELIM-001 | Upper electronics case, PCB-PWR cassette, four mic pods, preliminary RB40/MPPT lower module and mast/PV mounts; candidate CAD only. Fit, sealing, strength and acoustic acceptance pending. | N/A | 1.00 | 20.00 | 41.00 | 20.00 | 40 |  |  | UNPRICED_CURRENT_MPN | CANDIDATE_NOT_RELEASED
PR-011 | PCB-PWR | PWR-FUSE-01 | F1 | Protection | Littelfuse | 0451008.MRL | Nano2_451_6.1x2.69mm | FITTED | 1.00 | 30.00 | 41.00 | 61.00 |  | 21.27 | 10.00 | HISTORICAL_ANALOG_NOT_QUOTE | CANDIDATE_SELECTED_FOR_EVT_QUALIFICATION_NATIVE_VALUE_ECO_APPLIED_REPEAT_EVIDENCE_PASS_PHYSICAL_QUALIFICATION_PENDING
PR-012 | PCB-MAIN | J-SIM1 | J-SIM2 | J6 | J7 | SIM | TE Connectivity | 2336582-1 | Nano-SIM 4FF connector with DET | FITTED | 2.00 | 50.00 | 82.00 | 102.00 |  |  |  | UNPRICED_CURRENT_MPN | TECHNICALLY_SELECTED_PROCUREMENT_RISK
PR-013 | HARNESS-PWR-MAIN | H-PWR-MAIN | H_PWR_MAIN:A/B | Housing | Molex | 43025-1200 | Micro-Fit 3.0 12-circuit housing | FITTED | 2.00 | 44.00 | 82.00 | 90.00 |  |  |  | UNPRICED_CURRENT_MPN | SELECTED_PENDING_MECHANICS_I2C_TEST
PR-014 | HARNESS-PWR-MAIN | T-PWR-MAIN-CTL | H_PWR_MAIN control contacts | Terminal | Molex | 43030-0001 | Micro-Fit female crimp terminal 20-24 AWG class | FITTED | 12.00 | 252.00 | 492.00 | 516.00 |  |  |  | UNPRICED_CURRENT_MPN | SELECTED_PENDING_I2C_PULL_TEST
PR-015 | HARNESS-PWR-MAIN | T-PWR-MAIN-PWR | H_PWR_MAIN power contacts | Terminal | Molex | 43030-0038 | Micro-Fit female crimp terminal 18 AWG class | FITTED | 12.00 | 252.00 | 492.00 | 516.00 |  |  |  | UNPRICED_CURRENT_MPN | SELECTED_PENDING_CURRENT_PULL_TEST
PR-016 | PCB-PWR | J-PWR-IN | J1 | Connector | Molex | 430450213 | 2 positions | FITTED | 1.00 | 25.00 | 41.00 | 51.00 |  |  |  | UNPRICED_CURRENT_MPN | SELECTED_PENDING_MECHANICS
PR-017 | PCB-MAIN | PCB-PWR | J-PWR-MAIN | J-PWR-PWR | J2 | J_PWR1 | Connector | Molex | 430451202 | 12 positions | FITTED | 2.00 | 50.00 | 82.00 | 102.00 |  |  |  | UNPRICED_CURRENT_MPN | MECHANICAL_AUTHORITY_FROZEN_PENDING_HARNESS_SI | SELECTED_ELECTRICAL_PENDING_MECHANICS
PR-018 | PCB-MAIN | J-TAMPER | J13 | Connector | Molex | 5040500291 | Pico-Lock 1.50 mm 2-circuit right-angle SMT | FITTED | 1.00 | 25.00 | 41.00 | 51.00 |  |  |  | UNPRICED_CURRENT_MPN | MECHANICAL_AUTHORITY_FROZEN_PENDING_PHYSICAL_TEST
PR-019 | PCB-MAIN | PCB-MIC | J-MIC | J-MIC-MAIN | J_MIC1;J_MIC2;J_MIC3;J_MIC4 | PCB-MIC:J1 x4 | Connector | Molex | 5040500691 | Pico-Lock 1.50 mm 6-circuit right-angle SMT | FITTED | 8.00 | 184.00 | 328.00 | 376.00 |  |  |  | UNPRICED_CURRENT_MPN | MECHANICAL_AUTHORITY_FROZEN_PENDING_SI_AAD
PR-020 | HARNESS-MIC | H-MIC | H_MIC1:A/B;H_MIC2:A/B;H_MIC3:A/B;H_MIC4:A/B | Housing | Molex | 5040510601 | Pico-Lock 1.50 mm 6-circuit housing | FITTED | 8.00 | 176.00 | 328.00 | 360.00 |  |  |  | UNPRICED_CURRENT_MPN | SELECTED_PENDING_HARNESS_LENGTH_PULL_TEST
PR-021 | HARNESS-MIC | T-MIC | H_MIC1..H_MIC4 contacts | Terminal | Molex | 5040520098 | Pico-Lock crimp terminal 28-24 AWG | FITTED | 48.00 | 1008.00 | 1968.00 | 2064.00 |  |  |  | UNPRICED_CURRENT_MPN | SELECTED_PENDING_CRIMP_PULL_TEST
PR-022 | SYSTEM | ANT-GNSS | AE2 | Antenna | Taoglas | AA.166.A.301111 | IP67 magnetic 37.8x40.4x10 mm with 3 m RG174 SMA(M) | FITTED | 1.00 | 22.00 | 41.00 | 45.00 |  | 255.23 | 49.00 | HISTORICAL_ANALOG_NOT_QUOTE | CONTROLLED_EVT_PURCHASE_EXACT_MPN_VALIDATION_DURING_ASSEMBLY_EVT
PR-023 | PCB-MAIN | MAIN-010-FL1 | FL1 | SAW_Filter | Abracon | ABSES5AF-L100KM | 1109-5 | FITTED | 1.00 | 20.00 | 41.00 | 41.00 |  |  |  | UNPRICED_CURRENT_MPN | SELECTED_PENDING_REVIEW_A
PR-024 | PCB-MAIN | U8 | U8 | Cellular | Quectel | BG95-M3 | LGA-102_23.6x19.9mm | FITTED | 1.00 | 25.00 | 41.00 | 51.00 |  | 793.76 | 29.00 | HISTORICAL_ANALOG_NOT_QUOTE | SELECTED_PENDING_INCOMING_ID_AND_POST_ASSEMBLY_EVT
PR-025 | PCB-MAIN | MAIN-010-FB1 | FB1 | Ferrite_Bead | Murata | BLM31KN601SN1L | 1206 | FITTED | 1.00 | 20.00 | 41.00 | 41.00 |  |  |  | UNPRICED_CURRENT_MPN | SELECTED_PENDING_REVIEW_A
PR-026 | SYSTEM | RF-PIGTAIL | J8/J9/J10 cable | RF cable | Taoglas | CAB.0243 | 1.13 mm micro-coax 150 mm MHF I/U.FL-compatible R/A to waterproof SMA(F) bulkhead | FITTED | 3.00 | 66.00 | 123.00 | 135.00 |  |  |  | UNPRICED_CURRENT_MPN | CONTROLLED_EVT_PURCHASE_EXACT_MPN_VALIDATION_DURING_ASSEMBLY_EVT
PR-027 | PCB-PWR | PWR-C-100N | C1;C2;C4;C6 | Passive | TDK | CGA2B3X7R1E104K050BB | 0402 | FITTED | 4.00 | 120.00 | 164.00 | 244.00 |  |  |  | UNPRICED_CURRENT_MPN | LOCKED_CANDIDATE_PENDING_DERATING
PR-028 | PCB-MIC | C-MIC | PCB-MIC:C1 x4 | Passive | TDK | CGA2B3X7R1E104K050BB | 0402 1005 metric | FITTED | 4.00 | 120.00 | 164.00 | 244.00 |  | 1.70 | 7.00 | HISTORICAL_ANALOG_NOT_QUOTE | SELECTED_PENDING_SAMPLE
PR-029 | PCB-PWR | PWR-C-LDO | C7;C8 | Passive | TDK | CGA3E1X7R1A225K080AC | 0603 | FITTED | 2.00 | 80.00 | 82.00 | 162.00 |  |  |  | UNPRICED_CURRENT_MPN | LOCKED_CANDIDATE_PENDING_DERATING
PR-030 | PCB-PWR | PWR-C-CIN-HF | C9;C20;C21 | Passive | TDK | CGA3E2X7R1H104K080AA | 0603 | FITTED | 3.00 | 100.00 | 123.00 | 203.00 |  |  |  | UNPRICED_CURRENT_MPN | CONTROLLED_CANDIDATE_PENDING_MULTIPLE_REVIEWS
PR-031 | PCB-PWR | PWR-COUT-3V3 | PWR-COUT-3V8 | C3;C14;C15;C16 | C5;C17;C18;C19 | Passive | TDK | CGA6P3X7R1E226M250AB | 1210 | FITTED | 8.00 | 240.00 | 328.00 | 488.00 |  |  |  | UNPRICED_CURRENT_MPN | LOCKED_CANDIDATE_PENDING_DERATING
PR-032 | PCB-PWR | PWR-C-INPUT | C10;C11;C12 | Passive | TDK | CGA6P3X7R1H475K250AB | 1210 | FITTED | 3.00 | 100.00 | 123.00 | 203.00 |  |  |  | UNPRICED_CURRENT_MPN | CONTROLLED_CANDIDATE_PENDING_MULTIPLE_REVIEWS
PR-033 | PCB-PWR | PWR-REV-FET | Q1 | Protection | Texas Instruments | CSD18540Q5B | VSON-CLIP 5x6 mm | FITTED | 1.00 | 25.00 | 41.00 | 51.00 |  | 127.61 | 12.00 | HISTORICAL_ANALOG_NOT_QUOTE | SELECTED_TECHNICALLY_PROCUREMENT_CHECK
PR-034 | PCB-MAIN | U10 | U10 | LoRa | Ebyte | E22-900M22S | SMD_20x14_22P_1.27mm | FITTED | 1.00 | 26.00 | 41.00 | 53.00 |  | 391.35 | 20.00 | HISTORICAL_ANALOG_NOT_QUOTE | SELECTED_PENDING_CASTELLATED_OPTION_RF_REGULATORY
PR-035 | PCB-PWR | PWR-C-BULK | C13 | Passive | Panasonic Industry | EEH-ZK1V101XP | SMD can 6.3x7.7 mm | FITTED | 1.00 | 60.00 | 41.00 | 121.00 |  |  |  | UNPRICED_CURRENT_MPN | LOCKED_CANDIDATE_PACKAGE_REVIEW_PENDING
PR-036 | PCB-PWR | PWR-R-100K-01 | R1 | Passive | Panasonic Industry | ERA-2AEB104X | 0402 | FITTED | 1.00 | 60.00 | 41.00 | 121.00 |  |  |  | UNPRICED_CURRENT_MPN | LOCKED_CANDIDATE
PR-037 | PCB-PWR | PWR-R-35K7 | R2 | Passive | Panasonic Industry | ERA-2AEB3572X | 0402 | FITTED | 1.00 | 60.00 | 41.00 | 121.00 |  |  |  | UNPRICED_CURRENT_MPN | LOCKED_CANDIDATE
PR-038 | PCB-PWR | PWR-R-86K6 | R3;R7 | Passive | Panasonic Industry | ERA-2AEB8662X | 0402 | FITTED | 2.00 | 80.00 | 82.00 | 162.00 |  |  |  | UNPRICED_CURRENT_MPN | LOCKED_CANDIDATE
PR-040 | PCB-MAIN | MAIN-010-R103 | MAIN-010-R39 | MAIN-010-R40 | MAIN-010-R42 | MAIN-010-R43 | MAIN-010-R50 | MAIN-010-R51 | MAIN-010-R52 | MAIN-010-R53 | MAIN-010-R54 | MAIN-010-R55 | MAIN-010-R73 | R103 | R39 | R40 | R42 | R43 | R50 | R51 | R52 | R53 | R54 | R55 | R73 | Resistor | Panasonic | ERJ-2GE0R00X | 0402 | FITTED | 12.00 | 240.00 | 492.00 | 492.00 |  |  |  | UNPRICED_CURRENT_MPN | SELECTED_PENDING_REVIEW_A
PR-042 | PCB-PWR | PWR-R-0R | R4;R8 | Passive | Panasonic Industry | ERJ-2GE0R00X | 0402 | FITTED | 2.00 | 80.00 | 82.00 | 162.00 |  |  |  | UNPRICED_CURRENT_MPN | LOCKED_FITTED
PR-043 | PCB-MIC | R-MIC | PCB-MIC:R1 x4 | Passive | Panasonic Industry | ERJ-2GE0R00X | 0402 1005 metric | FITTED | 4.00 | 120.00 | 164.00 | 244.00 |  |  |  | UNPRICED_CURRENT_MPN | SELECTED_POPULATED_BASELINE_PENDING_SI
PR-044 | PCB-MAIN | MAIN-010-R60 | MAIN-010-R61 | R60 | R61 | Resistor | Panasonic | ERJ-2GEJ104X | 0402 | FITTED | 2.00 | 40.00 | 82.00 | 82.00 |  |  |  | UNPRICED_CURRENT_MPN | SELECTED_PENDING_REVIEW_A
PR-045 | PCB-MAIN | MAIN-010-R59 | R59 | Resistor | Panasonic | ERJ-2GEJ561X | 0402 | FITTED | 1.00 | 20.00 | 41.00 | 41.00 |  |  |  | UNPRICED_CURRENT_MPN | SELECTED_PENDING_REVIEW_A
PR-046 | PCB-MAIN | MAIN-010-R100 | MAIN-010-R102 | MAIN-010-R38 | MAIN-010-R41 | MAIN-010-R95 | R100 | R102 | R38 | R41 | R95 | Resistor | Panasonic | ERJ-2RKF1001X | 0402 | FITTED | 5.00 | 100.00 | 205.00 | 205.00 |  |  |  | UNPRICED_CURRENT_MPN | SELECTED_PENDING_REVIEW_A
PR-047 | PCB-MAIN | MAIN-010-R1 | MAIN-010-R28 | MAIN-010-R30 | MAIN-010-R31 | MAIN-010-R46 | MAIN-010-R48 | MAIN-010-R49 | MAIN-010-R67 | MAIN-010-R68 | MAIN-010-R7 | MAIN-010-R76 | MAIN-010-R78 | MAIN-010-R85 | MAIN-010-R86 | MAIN-010-R87 | MAIN-010-R88 | MAIN-010-R89 | MAIN-010-R90 | MAIN-010-R99 | R1 | R28 | R30 | R31 | R46 | R48 | R49 | R67 | R68 | R7 | R76 | R78 | R85 | R86 | R87 | R88 | R89 | R90 | R99 | Resistor | Panasonic | ERJ-2RKF1002X | 0402 | FITTED | 19.00 | 380.00 | 779.00 | 779.00 |  |  |  | UNPRICED_CURRENT_MPN | SELECTED_PENDING_REVIEW_A
PR-049 | PCB-PWR | PWR-R-10K | R10;R12 | Passive | Panasonic Industry | ERJ-2RKF1002X | 0402 | FITTED | 2.00 | 80.00 | 82.00 | 162.00 |  |  |  | UNPRICED_CURRENT_MPN | LOCKED_FITTED
PR-051 | PCB-MAIN | MAIN-010-R19 | MAIN-010-R2 | MAIN-010-R20 | MAIN-010-R21 | MAIN-010-R22 | MAIN-010-R23 | MAIN-010-R29 | MAIN-010-R3 | MAIN-010-R32 | MAIN-010-R33 | MAIN-010-R34 | MAIN-010-R35 | MAIN-010-R45 | MAIN-010-R47 | MAIN-010-R5 | MAIN-010-R63 | MAIN-010-R64 | MAIN-010-R65 | MAIN-010-R66 | MAIN-010-R77 | MAIN-010-R96 | R19 | R2 | R20 | R21 | R22 | R23 | R29 | R3 | R32 | R33 | R34 | R35 | R45 | R47 | R5 | R63 | R64 | R65 | R66 | R77 | R96 | Resistor | Panasonic | ERJ-2RKF1003X | 0402 | FITTED | 21.00 | 420.00 | 861.00 | 861.00 |  |  |  | UNPRICED_CURRENT_MPN | SELECTED_PENDING_REVIEW_A
PR-052 | PCB-PWR | PWR-R-100K | R6;R11 | Passive | Panasonic Industry | ERJ-2RKF1003X | 0402 | FITTED | 2.00 | 80.00 | 82.00 | 162.00 |  |  |  | UNPRICED_CURRENT_MPN | LOCKED_FITTED
PR-053 | PCB-MAIN | MAIN-010-R97 | R97 | Resistor | Panasonic | ERJ-2RKF1004X | 0402 | FITTED | 1.00 | 20.00 | 41.00 | 41.00 |  |  |  | UNPRICED_CURRENT_MPN | SELECTED_PENDING_REVIEW_A
PR-054 | PCB-MAIN | MAIN-010-R13 | MAIN-010-R14 | R13 | R14 | Resistor | Panasonic | ERJ-2RKF2201X | 0402 | FITTED | 2.00 | 40.00 | 82.00 | 82.00 |  |  |  | UNPRICED_CURRENT_MPN | SELECTED_PENDING_REVIEW_A
PR-055 | PCB-MAIN | MAIN-010-R10 | MAIN-010-R101 | MAIN-010-R11 | MAIN-010-R12 | MAIN-010-R15 | MAIN-010-R16 | MAIN-010-R17 | MAIN-010-R18 | MAIN-010-R36 | MAIN-010-R37 | MAIN-010-R56 | MAIN-010-R57 | MAIN-010-R58 | MAIN-010-R69 | MAIN-010-R70 | MAIN-010-R71 | MAIN-010-R72 | MAIN-010-R74 | MAIN-010-R75 | MAIN-010-R79 | MAIN-010-R8 | MAIN-010-R80 | MAIN-010-R81 | MAIN-010-R82 | MAIN-010-R83 | MAIN-010-R84 | MAIN-010-R9 | MAIN-010-R91 | MAIN-010-R92 | R10 | R101 | R11 | R12 | R15 | R16 | R17 | R18 | R36 | R37 | R56 | R57 | R58 | R69 | R70 | R71 | R72 | R74 | R75 | R79 | R8 | R80 | R81 | R82 | R83 | R84 | R9 | R91 | R92 | Resistor | Panasonic | ERJ-2RKF22R0X | 0402 | FITTED | 29.00 | 580.00 | 1189.00 | 1189.00 |  |  |  | UNPRICED_CURRENT_MPN | SELECTED_PENDING_REVIEW_A
PR-056 | PCB-MAIN | MAIN-010-R24 | MAIN-010-R26 | R24 | R26 | Resistor | Panasonic | ERJ-2RKF4701X | 0402 | FITTED | 2.00 | 40.00 | 82.00 | 82.00 |  |  |  | UNPRICED_CURRENT_MPN | SELECTED_PENDING_REVIEW_A
PR-058 | PCB-MAIN | MAIN-010-R25 | MAIN-010-R27 | MAIN-010-R44 | R25 | R27 | R44 | Resistor | Panasonic | ERJ-2RKF4702X | 0402 | FITTED | 3.00 | 60.00 | 123.00 | 123.00 |  |  |  | UNPRICED_CURRENT_MPN | SELECTED_PENDING_REVIEW_A
PR-059 | PCB-MAIN | MAIN-010-R93 | MAIN-010-R94 | R93 | R94 | Resistor | Panasonic | ERJ-2RKF5101X | 0402 | FITTED | 2.00 | 40.00 | 82.00 | 82.00 |  |  |  | UNPRICED_CURRENT_MPN | SELECTED_PENDING_REVIEW_A
PR-060 | PCB-MAIN | MAIN-010-R62 | R62 | Resistor | Panasonic | ERJ-8GEYJ100V | 1206 | FITTED | 1.00 | 20.00 | 41.00 | 41.00 |  |  |  | UNPRICED_CURRENT_MPN | SELECTED_PENDING_REVIEW_A
PR-061 | PCB-MAIN | U14-U15 | U14;U15 | ESD | STMicroelectronics | ESDALC6V1-5P6 | SOT666_1.6x1.6mm | FITTED | 2.00 | 50.00 | 82.00 | 102.00 |  | 12.76 | 24.00 | HISTORICAL_ANALOG_NOT_QUOTE | SELECTED_PENDING_SIM_ESD_SI_SAMPLE
PR-062 | SYSTEM | ANT-CELL | AE1 | Antenna | Taoglas | G30.B.108111 | IP67 screw-mount dome with 1 m cable and SMA(M) | FITTED | 1.00 | 22.00 | 41.00 | 45.00 |  | 595.53 | 48.00 | HISTORICAL_ANALOG_NOT_QUOTE | CONTROLLED_EVT_PURCHASE_EXACT_MPN_VALIDATION_DURING_ASSEMBLY_EVT
PR-063 | PCB-MAIN | MAIN-010-C64 | C64 | Capacitor | Murata | GRM1555C1E470JA01D | 0402 | FITTED | 1.00 | 20.00 | 41.00 | 41.00 |  |  |  | UNPRICED_CURRENT_MPN | SELECTED_PENDING_REVIEW_A
PR-065 | PCB-MAIN | MAIN-010-C43 | MAIN-010-C47 | C43 | C47 | Capacitor | Murata | GRM1555C1H100JA01D | 0402 | FITTED | 2.00 | 40.00 | 82.00 | 82.00 |  |  |  | UNPRICED_CURRENT_MPN | SELECTED_PENDING_REVIEW_A
PR-066 | PCB-MAIN | MAIN-010-C40 | C40 | Capacitor | Murata | GRM1555C1H101JA01D | 0402 | FITTED | 1.00 | 20.00 | 41.00 | 41.00 |  |  |  | UNPRICED_CURRENT_MPN | SELECTED_PENDING_REVIEW_A
PR-067 | PCB-MAIN | MAIN-010-C39 | C39 | Capacitor | Murata | GRM1555C1H151JA01D | 0402 | FITTED | 1.00 | 20.00 | 41.00 | 41.00 |  |  |  | UNPRICED_CURRENT_MPN | SELECTED_PENDING_REVIEW_A
PR-069 | PCB-MAIN | MAIN-010-C42 | MAIN-010-C46 | C42 | C46 | Capacitor | Murata | GRM1555C1H330JA01D | 0402 | FITTED | 2.00 | 40.00 | 82.00 | 82.00 |  |  |  | UNPRICED_CURRENT_MPN | SELECTED_PENDING_REVIEW_A
PR-070 | PCB-MAIN | MAIN-010-C41 | C41 | Capacitor | Murata | GRM1555C1H680JA01D | 0402 | FITTED | 1.00 | 20.00 | 41.00 | 41.00 |  |  |  | UNPRICED_CURRENT_MPN | SELECTED_PENDING_REVIEW_A
PR-071 | PCB-MAIN | MAIN-010-C14 | MAIN-010-C15 | C14 | C15 | Capacitor | Murata | GRM155R61A225KE15D | 0402 | FITTED | 2.00 | 40.00 | 82.00 | 82.00 |  |  |  | UNPRICED_CURRENT_MPN | SELECTED_PENDING_REVIEW_A
PR-072 | PCB-MAIN | MAIN-010-C11 | MAIN-010-C22 | MAIN-010-C9 | C11 | C22 | C9 | Capacitor | Murata | GRM155R61C105KA12D | 0402 | FITTED | 3.00 | 60.00 | 123.00 | 123.00 |  |  |  | UNPRICED_CURRENT_MPN | SELECTED_PENDING_REVIEW_A
PR-073 | PCB-MAIN | MAIN-010-C63 | C63 | Capacitor | Murata | GRM155R71C103KA01D | 0402 | FITTED | 1.00 | 20.00 | 41.00 | 41.00 |  |  |  | UNPRICED_CURRENT_MPN | SELECTED_PENDING_REVIEW_A
PR-074 | PCB-MAIN | MAIN-010-C48 | MAIN-010-C52 | MAIN-010-C53 | MAIN-010-C76 | MAIN-010-C78 | C48 | C52 | C53 | C76 | C78 | Capacitor | Murata | GRM155R71E103KA01D | 0402 | FITTED | 5.00 | 100.00 | 205.00 | 205.00 |  |  |  | UNPRICED_CURRENT_MPN | SELECTED_PENDING_REVIEW_A
PR-076 | PCB-MAIN | MAIN-010-C1 | MAIN-010-C10 | MAIN-010-C12 | MAIN-010-C18 | MAIN-010-C2 | MAIN-010-C21 | MAIN-010-C23 | MAIN-010-C25 | MAIN-010-C26 | MAIN-010-C27 | MAIN-010-C28 | MAIN-010-C29 | MAIN-010-C3 | MAIN-010-C30 | MAIN-010-C31 | MAIN-010-C32 | MAIN-010-C33 | MAIN-010-C34 | MAIN-010-C35 | MAIN-010-C4 | MAIN-010-C45 | MAIN-010-C49 | MAIN-010-C5 | MAIN-010-C50 | MAIN-010-C51 | MAIN-010-C60 | MAIN-010-C62 | MAIN-010-C65 | MAIN-010-C66 | MAIN-010-C68 | MAIN-010-C7 | MAIN-010-C71 | MAIN-010-C73 | MAIN-010-C74 | MAIN-010-C8 | C1 | C10 | C12 | C18 | C2 | C21 | C23 | C25 | C26 | C27 | C28 | C29 | C3 | C30 | C31 | C32 | C33 | C34 | C35 | C4 | C45 | C49 | C5 | C50 | C51 | C60 | C62 | C65 | C66 | C68 | C7 | C71 | C73 | C74 | C8 | Capacitor | Murata | GRM155R71E104KE14D | 0402 | FITTED | 35.00 | 700.00 | 1435.00 | 1435.00 |  |  |  | UNPRICED_CURRENT_MPN | SELECTED_PENDING_REVIEW_A
PR-077 | PCB-MAIN | MAIN-010-C37 | C37 | Capacitor | Murata | GRM155R71E224KE14D | 0402 | FITTED | 1.00 | 20.00 | 41.00 | 41.00 |  |  |  | UNPRICED_CURRENT_MPN | SELECTED_PENDING_REVIEW_A
PR-078 | PCB-MAIN | MAIN-010-C38 | C38 | Capacitor | Murata | GRM155R71E473KA01D | 0402 | FITTED | 1.00 | 20.00 | 41.00 | 41.00 |  |  |  | UNPRICED_CURRENT_MPN | SELECTED_PENDING_REVIEW_A
PR-079 | PCB-MAIN | MAIN-010-C77 | C77 | Capacitor | Murata | GRM155R72A472KA01D | 0402 | FITTED | 1.00 | 20.00 | 41.00 | 41.00 |  |  |  | UNPRICED_CURRENT_MPN | SELECTED_PENDING_REVIEW_A
PR-080 | PCB-MAIN | MAIN-010-C13 | MAIN-010-C20 | MAIN-010-C24 | MAIN-010-C6 | MAIN-010-C61 | MAIN-010-C67 | MAIN-010-C72 | MAIN-010-C75 | C13 | C20 | C24 | C6 | C61 | C67 | C72 | C75 | Capacitor | Murata | GRM188R61A106KE69D | 0603 | FITTED | 8.00 | 160.00 | 328.00 | 328.00 |  |  |  | UNPRICED_CURRENT_MPN | SELECTED_PENDING_REVIEW_A
PR-081 | PCB-MAIN | MAIN-010-C19 | C19 | Capacitor | Murata | GRM21BR61A226ME44L | 0805 | FITTED | 1.00 | 20.00 | 41.00 | 41.00 |  |  |  | UNPRICED_CURRENT_MPN | SELECTED_PENDING_REVIEW_A
PR-082 | PCB-PWR | U-MON-01 | U2 | Monitor | Texas Instruments | INA226AIDGSR | VSSOP-10 | FITTED | 1.00 | 25.00 | 41.00 | 51.00 |  | 51.90 | 15.00 | HISTORICAL_ANALOG_NOT_QUOTE | SELECTED_REV_A_12PIN_I2C
PR-083 | PCB-MAIN | U3 | U3 | Motion | STMicroelectronics | LIS2DW12TR | LGA-12_2x2mm | FITTED | 1.00 | 25.00 | 41.00 | 51.00 |  | 77.42 | 26.00 | HISTORICAL_ANALOG_NOT_QUOTE | SELECTED_PENDING_SAMPLE
PR-084 | PCB-PWR | PWR-REV-CTL | U1 | Protection | Texas Instruments | LM74700QDBVRQ1 | SOT-23-6 | FITTED | 1.00 | 25.00 | 41.00 | 51.00 |  | 1131.51 | 11.00 | HISTORICAL_ANALOG_NOT_QUOTE | SELECTED_PENDING_SCHEMATIC_SAMPLE
PR-085 | PCB-PWR | U-PWR1 | U-PWR2 | U3 | U4 | Power | Texas Instruments | LMR604403SRAKR | RAK-9 | FITTED | 2.00 | 50.00 | 82.00 | 102.00 |  |  |  | UNPRICED_CURRENT_MPN | SELECTED_PENDING_DESIGN_CALC_SAMPLE
PR-086 | PCB-MAIN | MAIN-010-L1 | L1 | Inductor | Murata | LQH32PN2R2NN0L | 1210 | FITTED | 1.00 | 20.00 | 41.00 | 41.00 |  |  |  | UNPRICED_CURRENT_MPN | SELECTED_PENDING_REVIEW_A
PR-087 | PCB-MAIN | MAIN-010-L2 | L2 | Inductor | Murata | LQW15AN27NJ00D | 0402 | FITTED | 1.00 | 20.00 | 41.00 | 41.00 |  |  |  | UNPRICED_CURRENT_MPN | SELECTED_PENDING_REVIEW_A
PR-088 | PCB-MAIN | MAIN-010-U5 | U5 | Operational_Amplifier | Analog Devices | LT6000IDCB#TRMPBF | DFN-6_DCB_2x3mm | FITTED | 1.00 | 20.00 | 41.00 | 41.00 |  |  |  | UNPRICED_CURRENT_MPN | SELECTED_PENDING_REVIEW_A
PR-089 | PCB-MAIN | U9 | U9 | GNSS | u-blox | MAX-M10S-00B | LCC-18_9.7x10.1mm | FITTED | 1.00 | 25.00 | 41.00 | 51.00 |  | 901.80 | 30.00 | HISTORICAL_ANALOG_NOT_QUOTE | SELECTED_PENDING_GNSS_RF_TIMING_SAMPLE
PR-090 | PCB-MAIN | U11 | U11 | BLE | Raytac | MDBT50Q-P1MV2 | nRF52840_SMD_10.5x15.5_61P_PCB_antenna | FITTED | 1.00 | 25.00 | 41.00 | 51.00 |  | 583.62 | 21.00 | HISTORICAL_ANALOG_NOT_QUOTE | SELECTED_PENDING_ENCLOSURE_RF
PR-091 | PCB-MAIN | J-SD1 | J12 | Connector | GCT | MEM2052-00-195-00-A | microSD push-push SMT 1.95 mm with detect | FITTED | 1.00 | 25.00 | 41.00 | 51.00 |  | 29.78 | 45.00 | HISTORICAL_ANALOG_NOT_QUOTE | MECHANICAL_AUTHORITY_FROZEN_PENDING_PHYSICAL_TEST
PR-092 | PCB-MAIN | Q-MODEM-PWRKEY | Q-MODEM-RESET | Q-SIM-MUX-EN | Q1 | Q2 | Q3 | Transistor | Nexperia | MMBT3904,215 | SOT23 | FITTED | 3.00 | 75.00 | 123.00 | 153.00 |  |  |  | UNPRICED_CURRENT_MPN | SELECTED_PENDING_CONTROL_TIMING_SAMPLE | SELECTED_PENDING_SIM_SAFE_STATE_SAMPLE
PR-093 | PCB-MIC | MK1 | MK1 | Microphone | TDK InvenSense | MMICT5838-00-012 | LGA-CAV-5 3.5x2.65x0.98 mm | FITTED | 4.00 | 96.00 | 164.00 | 196.00 |  | 133.57 | 8.00 | HISTORICAL_ANALOG_NOT_QUOTE | SELECTED_PENDING_SAMPLE
PR-094 | PCB-PWR | PWR-NET-TIE | NT1;NT2;NT3 | PCB feature | PCB fabrication | NET_TIE_COPPER_REV_A | NetTie-2 SMD pad 0.5 mm | PCB_FEATURE | 3.00 | 60.00 | 123.00 | 123.00 |  |  |  | UNPRICED_CURRENT_MPN | LOCKED_LAYOUT_PENDING
PR-095 | PCB-MAIN | MAIN-010-D3 | MAIN-010-D5 | D3 | D5 | RF_ESD | Nexperia | PESD5V0C1BSF | SOD962-2 | FITTED | 2.00 | 40.00 | 82.00 | 82.00 |  |  |  | UNPRICED_CURRENT_MPN | SELECTED_PENDING_REVIEW_A
PR-096 | PCB-MAIN | MAIN-010-D1 | MAIN-010-D2 | D1 | D2 | Supply_TVS | Nexperia | PESD5V0S1UL | SOD882 | FITTED | 2.00 | 40.00 | 82.00 | 82.00 |  |  |  | UNPRICED_CURRENT_MPN | SELECTED_PENDING_REVIEW_A
PR-097 | SYSTEM | BAT1 | BT1 | Battery | RELiON | RB40 | 197x166x173 mm IP66 M8 pack | FITTED | 1.00 | 21.00 | 41.00 | 43.00 |  | 5529.92 | 51.00 | HISTORICAL_ANALOG_NOT_QUOTE | CONTROLLED_EVT_PURCHASE_EXACT_MPN_VALIDATION_DURING_ASSEMBLY_EVT
PR-098 | SYSTEM | MPPT-TEMP | TS-BAT1 | Sensor | Victron Energy | SBS050150200 | Smart Battery Sense long range up to 10 m radio with 0.45 m leads and M10 eyelets | FITTED | 1.00 | 21.00 | 41.00 | 43.00 |  |  |  | UNPRICED_CURRENT_MPN | CONTROLLED_EVT_PURCHASE_EXACT_MPN_VALIDATION_DURING_ASSEMBLY_EVT
PR-099 | SYSTEM | MPPT1 | U-MPPT | Controller | Victron Energy | SCC075010060R | 100x113x40 mm IP43 electronics IP22 terminals | FITTED | 1.00 | 21.00 | 41.00 | 43.00 |  | 1701.51 | 55.00 | HISTORICAL_ANALOG_NOT_QUOTE | CONTROLLED_EVT_PURCHASE_EXACT_MPN_VALIDATION_DURING_ASSEMBLY_EVT
PR-100 | PCB-MAIN | U12 | U12 | Storage | Kingston | SDCIT2/32GB | microSD_card_8_contact | FITTED | 1.00 | 25.00 | 41.00 | 51.00 |  | 425.38 | 22.00 | HISTORICAL_ANALOG_NOT_QUOTE | SELECTED_PENDING_SAMPLE_ENDURANCE
PR-101 | SYSTEM | PV1 | PV1 | Solar panel | SLD Tech / Solarland | SLP080S-12M | 1475x342x40 mm framed 36-cell panel | FITTED | 1.00 | 21.00 | 41.00 | 43.00 |  | 1063.45 | 56.00 | HISTORICAL_ANALOG_NOT_QUOTE | CONTROLLED_EVT_PURCHASE_EXACT_MPN_VALIDATION_DURING_ASSEMBLY_EVT
PR-102 | PCB-PWR | PWR-TVS-01 | D1 | Protection | Littelfuse | SMBJ18A | SMB_DO-214AA | FITTED | 1.00 | 25.00 | 41.00 | 51.00 |  | 8.51 | 13.00 | HISTORICAL_ANALOG_NOT_QUOTE | CANDIDATE_PENDING_SURGE_PROFILE
PR-103 | PCB-MAIN | U18 | U18 | Logic | Texas Instruments | SN74AXC1T45DRLR | SOT-5X3_6 | FITTED | 1.00 | 25.00 | 41.00 | 51.00 |  |  |  | UNPRICED_CURRENT_MPN | SELECTED_PENDING_AAD_WAKE_TEST
PR-104 | PCB-MAIN | U16 | U7 | U16 | U7 | Level translator | Logic | Texas Instruments | SN74AXC8T245PWR | TSSOP-24 | FITTED | 2.00 | 50.00 | 82.00 | 102.00 |  |  |  | UNPRICED_CURRENT_MPN | SELECTED_PENDING_SI_AAD_SAMPLE | SELECTED_PENDING_UART_POWER_SAMPLE
PR-105 | PCB-MAIN | MAIN-010-U6 | U6 | Open_Drain_Buffer | Texas Instruments | SN74LVC1G07DBVR | SOT-23-5_DBV | FITTED | 1.00 | 20.00 | 41.00 | 41.00 |  |  |  | UNPRICED_CURRENT_MPN | SELECTED_PENDING_REVIEW_A
PR-106 | PCB-MAIN | U17 | U17 | Logic | Texas Instruments | SN74LVC32APWR | TSSOP-14 | FITTED | 1.00 | 25.00 | 41.00 | 51.00 |  |  |  | UNPRICED_CURRENT_MPN | SELECTED_PENDING_AAD_WAKE_TEST
PR-107 | PCB-MAIN | U1 | U1 | MCU | STMicroelectronics | STM32U585VIT6Q | LQFP100_14x14 | FITTED | 1.00 | 25.00 | 41.00 | 51.00 |  | 1229.34 | 19.00 | HISTORICAL_ANALOG_NOT_QUOTE | SELECTED_PENDING_TARGET_SAMPLE
PR-108 | PCB-MAIN | U4 | U4 | Temperature | STMicroelectronics | STTS22HTR | UDFN-6L_2x2mm | FITTED | 1.00 | 25.00 | 41.00 | 51.00 |  | 130.17 | 27.00 | HISTORICAL_ANALOG_NOT_QUOTE | SELECTED_PENDING_ASSEMBLY_REVIEW
PR-109 | PCB-MAIN | MAIN-010-Q4 | Q4 | Dual_MOSFET | Vishay | Si1016X-T1-GE3 | SOT-563_SC-89 | FITTED | 1.00 | 20.00 | 41.00 | 41.00 |  |  |  | UNPRICED_CURRENT_MPN | SELECTED_PENDING_REVIEW_A
PR-110 | PCB-MAIN | X1 | X1 | Clock | SiTime | SiT1552AI-JE-DCC-32.768D | CSP-4_1.5x0.8mm | FITTED | 1.00 | 25.00 | 41.00 | 51.00 |  | 95.28 | 31.00 | HISTORICAL_ANALOG_NOT_QUOTE | SELECTED_PENDING_LSE_BYPASS_REVIEW
PR-111 | PCB-MAIN | MAIN-010-C36 | MAIN-010-C44 | C36 | C44 | Capacitor | KEMET | T520D107M006ATE015 | 7343-31 | FITTED | 2.00 | 40.00 | 82.00 | 82.00 |  |  |  | UNPRICED_CURRENT_MPN | SELECTED_PENDING_REVIEW_A
PR-112 | SYSTEM | ANT-LORA | AE3 | Antenna | Taoglas | TI.89.B.2111W | IP67 terminal antenna 180x13 mm SMA(M) | FITTED | 1.00 | 22.00 | 41.00 | 45.00 |  | 1020.91 | 50.00 | HISTORICAL_ANALOG_NOT_QUOTE | CONTROLLED_EVT_PURCHASE_EXACT_MPN_VALIDATION_DURING_ASSEMBLY_EVT
PR-113 | PCB-MAIN | MAIN-010-D10 | MAIN-010-D11 | MAIN-010-D6 | MAIN-010-D7 | MAIN-010-D8 | MAIN-010-D9 | D10 | D11 | D6 | D7 | D8 | D9 | ESD_Diode | Texas Instruments | TPD1E05U06DYAR | SOD-523_DYA | FITTED | 6.00 | 120.00 | 246.00 | 246.00 |  |  |  | UNPRICED_CURRENT_MPN | SELECTED_PENDING_REVIEW_A
PR-114 | PCB-MAIN | MAIN-010-D4 | D4 | RF_ESD | Texas Instruments | TPD1E05U06DYAR | SOD-523_DYA | FITTED | 1.00 | 20.00 | 41.00 | 41.00 |  |  |  | UNPRICED_CURRENT_MPN | SELECTED_PENDING_REVIEW_A
PR-115 | PCB-MAIN | MAIN-010-U25 | MAIN-010-U26 | U25 | U26 | USB_ESD_Array | Texas Instruments | TPD2EUSB30DRTR | SOT-9X3_DRT | FITTED | 2.00 | 40.00 | 82.00 | 82.00 |  |  |  | UNPRICED_CURRENT_MPN | SELECTED_PENDING_REVIEW_A
PR-116 | PCB-MAIN | MAIN-010-U19 | MAIN-010-U20 | MAIN-010-U21 | MAIN-010-U22 | MAIN-010-U23 | MAIN-010-U24 | MAIN-010-U27 | U19 | U20 | U21 | U22 | U23 | U24 | U27 | ESD_Array | Texas Instruments | TPD4E05U06DQAR | USON-10_DQA | FITTED | 7.00 | 140.00 | 287.00 | 287.00 |  |  |  | UNPRICED_CURRENT_MPN | SELECTED_PENDING_REVIEW_A
PR-117 | PCB-PWR | U-PWR3 | U5 | Power | Texas Instruments | TPS7A2018PDBVR | SOT-23-5 | FITTED | 1.00 | 25.00 | 41.00 | 51.00 |  | 17.87 | 18.00 | HISTORICAL_ANALOG_NOT_QUOTE | SELECTED_PENDING_NOISE_SAMPLE
PR-118 | PCB-MAIN | U13 | U13 | SIM switch | Texas Instruments | TS3A27518EPWR | TSSOP-24_PW | FITTED | 1.00 | 25.00 | 41.00 | 51.00 |  | 57.85 | 23.00 | HISTORICAL_ANALOG_NOT_QUOTE | SELECTED_PENDING_USIM_SI_SAMPLE
PR-119 | PCB-MAIN | J-RF-CELL | J-RF-GNSS | J8 | J9 | RF connector | Hirose | U.FL-R-SMT-1(60) | U.FL SMT receptacle | FITTED | 2.00 | 56.00 | 82.00 | 114.00 |  |  |  | UNPRICED_CURRENT_MPN | LAYOUT_ZONE_FROZEN_PENDING_RF_VALIDATION
PR-120 | PCB-MAIN | J-RF-LORA | J10 | RF connector | Hirose | U.FL-R-SMT-1(60) | U.FL SMT receptacle | FITTED | 1.00 | 28.00 | 41.00 | 57.00 |  | 42.54 | 44.00 | HISTORICAL_ANALOG_NOT_QUOTE | LAYOUT_ZONE_FROZEN_PENDING_RF_VALIDATION
PR-121 | PCB-MAIN | J-USB | J11 | Connector | GCT | USB4105-GF-A-120 | 16 positions | FITTED | 1.00 | 25.00 | 41.00 | 51.00 |  |  |  | UNPRICED_CURRENT_MPN | MECHANICAL_AUTHORITY_FROZEN_PENDING_PHYSICAL_TEST
PR-122 | PCB-MAIN | U2 | U2 | Memory | Winbond | W25Q512JVFIQ | SOIC-16_300mil | FITTED | 1.00 | 25.00 | 41.00 | 51.00 |  | 745.26 | 25.00 | HISTORICAL_ANALOG_NOT_QUOTE | SELECTED_PENDING_SAMPLE
PR-123 | PCB-PWR | R-SHUNT-01 | RSH1 | Shunt | Vishay Dale | WSK2512R0100FEA | WSK2512 4-terminal 6.35x3.18 mm | FITTED | 1.00 | 30.00 | 41.00 | 61.00 |  | 42.54 | 14.00 | HISTORICAL_ANALOG_NOT_QUOTE | SELECTED_PENDING_KELVIN_LAYOUT_SAMPLE
PR-124 | PCB-PWR | PWR-L | L1;L2 | Passive | Coilcraft | XAL7030-472MEC | XAL7030 | FITTED | 2.00 | 50.00 | 82.00 | 102.00 |  |  |  | UNPRICED_CURRENT_MPN | SELECTED_PENDING_LAYOUT_THERMAL_EMI

Sheet: Цены v02
Исходные ориентировочные цены v.02
Источник: Закупочная ведомость_Дионея_v.02.xlsx · 09.09.2026 · SHA-256 730b0d3e3f47644cc091f141e689a40cbf9a2c9da8718ab8b4cbd8d530a91156
Строки сохранены без замены MPN, цены и количества; это сопоставительный слой, а не расчёт нового заказа.
Группа | Item ID | Наименование | На станцию | На 20 | Цена ед. ₽ | Стоимость 20 ₽ | Основание | Источник | Строка
Электронная компонентная база | C-MIC | Локальные развязывающие конденсаторы микрофона | 8 | 160 | 1.70 | 272.24 | Инженерная оценка КНР | https://www.lcsc.com/ | 7
Электронная компонентная база | MK1 | Цифровой PDM MEMS-микрофон T5838 | 4 | 80 | 133.57 | 10685.51 | Текущий прайс/бенчмарк MPN | https://www.digikey.cn/en/products/detail/tdk-invensense/MMICT5838-00-012/16903860 | 8
Электронная компонентная база | PCB-MISC | Прочая элементная база PCB: R/C/L, ESD, развязка, мелкие пассивы | 1 | 20 | 680.61 | 13612.11 | Инженерный резерв для ещё не разложенных по MPN позиций Rev.A | https://www.lcsc.com/ | 9
Электронная компонентная база | PWR-FUSE-01 | Предохранитель входной цепи PCB-PWR | 1 | 20 | 21.27 | 425.38 | Инженерная оценка КНР | https://www.lcsc.com/ | 10
Электронная компонентная база | PWR-REV-CTL | Контроллер защиты от переполюсовки и обратного тока | 1 | 20 | 1131.51 | 22630.14 | Текущий прайс/бенчмарк MPN | https://www.lcsc.com/product-image/C2941042.html | 11
Электронная компонентная база | PWR-REV-FET | Силовой N-MOSFET 60 В, низкое Rds(on) | 1 | 20 | 127.61 | 2552.27 | Текущий прайс/бенчмарк MPN | https://lcsc.com/product-detail/MOSFET_Texas-Instruments-CSD18540Q5B_C86513.html | 12
Электронная компонентная база | PWR-TVS-01 | TVS-защита силовой шины | 1 | 20 | 8.51 | 170.15 | Инженерная оценка КНР | https://www.lcsc.com/ | 13
Электронная компонентная база | R-SHUNT-01 | Шунт 10 мОм, 4-выводный Kelvin | 1 | 20 | 42.54 | 850.76 | Инженерная оценка КНР | https://www.lcsc.com/ | 14
Электронная компонентная база | U-MON-01 | Монитор тока, напряжения и мощности батареи INA226 | 1 | 20 | 51.90 | 1037.92 | Текущий прайс/бенчмарк MPN | https://www.lcsc.com/product-detail/C49851.html | 15
Электронная компонентная база | U-PWR1 | DC/DC 3,8 В / 4 А для сотового модема | 1 | 20 | 224.60 | 4492.00 | Текущий прайс/бенчмарк MPN | https://www.lcsc.com/product-detail/C43351623.html | 16
Электронная компонентная база | U-PWR2 | DC/DC 3,3 В / 4 А цифрового питания | 1 | 20 | 224.60 | 4492.00 | Текущий прайс/бенчмарк MPN | https://www.lcsc.com/product-detail/C43351623.html | 17
Электронная компонентная база | U-PWR3 | Малошумящий LDO 1,8 В микрофонного тракта | 1 | 20 | 17.87 | 357.32 | Текущий прайс/бенчмарк MPN | https://www.lcsc.com/product-detail/Voltage-Regulators-Linear-Low-Drop-Out-LDO-Regulators_Texas-Instruments-TPS7A2018PDBVR_C963430.html | 18
Электронная компонентная база | U1 | Микроконтроллер STM32U585, защищённая low-power платформа | 1 | 20 | 1229.34 | 24586.88 | Текущий прайс/бенчмарк MPN | https://www.lcsc.com/product-detail/C5270986.html | 19
Электронная компонентная база | U10 | LoRa-модуль SX1262 для RU868 | 1 | 20 | 391.35 | 7826.96 | Текущий прайс/бенчмарк MPN | https://www.alibaba.com/p/ebyte-e22-900m22s-tcxo-7km-long_62443474220.html | 20
Электронная компонентная база | U11 | BLE/OTA сопроцессор nRF52840 | 1 | 20 | 583.62 | 11672.39 | Текущий прайс/бенчмарк MPN | https://www.tme.com/us/en-us/details/mdbt50q-p1mv2/iot-wifi-bluetooth-modules/raytac/ | 21
Электронная компонентная база | U12 | Промышленная microSD, 32 ГБ | 1 | 20 | 425.38 | 8507.57 | Инженерная оценка КНР | https://www.alibaba.com/ | 22
Электронная компонентная база | U13 | Коммутатор интерфейса двух SIM-карт | 1 | 20 | 57.85 | 1157.03 | Текущий прайс/бенчмарк MPN | https://www.lcsc.com/product-detail/Analog-Switches-Multiplexers_Texas-Instruments-TS3A27518EPWR_C443721.html | 23
Электронная компонентная база | U14-U15 | Малoёмкостная ESD/TVS-защита линий SIM | 2 | 40 | 12.76 | 510.45 | Инженерная оценка КНР | https://www.lcsc.com/ | 24
Электронная компонентная база | U2 | QSPI NOR Flash 64 МБ | 1 | 20 | 745.26 | 14905.26 | Текущий прайс/бенчмарк MPN | https://www.lcsc.com/product-image/C2962011.html | 25
Электронная компонентная база | U3 | Малопотребляющий акселерометр | 1 | 20 | 77.42 | 1548.38 | Текущий прайс/бенчмарк MPN | https://www.lcsc.com/product-detail/Motion-Sensors-Accelerometers_STMicroelectronics_C189624.html | 26
Электронная компонентная база | U4 | Цифровой датчик температуры | 1 | 20 | 130.17 | 2603.32 | Текущий прайс/бенчмарк MPN | https://www.lcsc.com/product-detail/temperature-and-humidity-sensor_stmicroelectronics-stts22htr_C2969838.html | 27
Электронная компонентная база | U7 | Преобразователь логических уровней 1,8/3,3 В | 1 | 20 | 29.78 | 595.53 | Инженерная оценка КНР | https://www.lcsc.com/ | 28
Электронная компонентная база | U8 | Сотовый модем LTE Cat-M1 / NB2 / EGPRS | 1 | 20 | 793.76 | 15875.13 | Рыночный диапазон КНР / инженерная оценка | https://www.alibaba.com/showroom/bg95-m3-module.html | 29
Электронная компонентная база | U9 | GNSS-модуль с выходом TIMEPULSE/PPS | 1 | 20 | 901.80 | 18036.05 | Текущий прайс/бенчмарк MPN | https://www.lcsc.com/product-image/C4153167.html | 30
Электронная компонентная база | X1 | Низкодрейфовый генератор 32,768 кГц | 1 | 20 | 95.28 | 1905.70 | Текущий прайс/бенчмарк MPN | https://www.lcsc.com/product-detail/Programmable-Oscillators_SiTime-SIT1552AI-JE-DCC-32-768D_C367054.html | 31
Производство плат | ASM-MAIN | Собранная основная плата контроллера PCB-MAIN | 1 | 20 | 1020.91 | 20418.17 | Инженерная оценка JLCPCB/China PCBA | https://jlcpcb.com/help/article/pcb-assembly-price | 32
Производство плат | ASM-MIC | Собранная микрофонная плата PCB-MIC | 4 | 80 | 340.30 | 27224.22 | Инженерная оценка JLCPCB/China PCBA | https://jlcpcb.com/help/article/pcb-assembly-price | 33
Производство плат | ASM-PWR | Собранная плата питания и защиты PCB-PWR | 1 | 20 | 680.61 | 13612.11 | Инженерная оценка JLCPCB/China PCBA | https://jlcpcb.com/help/article/pcb-assembly-price | 34
Производство плат | PCB-MAIN | Печатная плата PCB-MAIN, 4 слоя | 1 | 20 | 425.38 | 8507.57 | Инженерная оценка JLCPCB/China PCBA | https://jlcpcb.com/help/article/pcb-assembly-price | 35
Производство плат | PCB-MIC | Печатная плата микрофонного лепестка PCB-MIC | 4 | 80 | 127.61 | 10209.08 | Инженерная оценка JLCPCB/China PCBA | https://jlcpcb.com/help/article/pcb-assembly-price | 36
Производство плат | PCB-PWR | Печатная плата PCB-PWR, 2 слоя, повышенная медь | 1 | 20 | 255.23 | 5104.54 | Инженерная оценка JLCPCB/China PCBA | https://jlcpcb.com/help/article/pcb-assembly-price | 37
Кабели и разъёмы | HARNESS | Комплект маркированных кабельных жгутов станции | 1 | 20 | 1413.11 | 28262.15 | Инженерная оценка КНР | https://www.lcsc.com/product-detail/Housings-Wire-To-Board-Wire-To-Wire_MOLEX-5040510601_C505129.html | 38
Кабели и разъёмы | J-MIC | 6-контактный разъём микрофонного жгута Pico-Lock | 4 | 80 | 22.12 | 1769.57 | Текущий прайс/бенчмарк MPN | https://www.lcsc.com/product-detail/wire-to-board-connector_molex-5040500691_C563981.html | 39
Кабели и разъёмы | J-PWR-MAIN | 12-контактный межплатный разъём MAIN-PWR, сторона MAIN | 1 | 20 | 212.69 | 4253.78 | Инженерная оценка КНР | https://www.lcsc.com/ | 40
Кабели и разъёмы | J-PWR-PWR | 12-контактный межплатный разъём MAIN-PWR, сторона PWR | 1 | 20 | 212.69 | 4253.78 | Инженерная оценка КНР | https://www.lcsc.com/ | 41
Кабели и разъёмы | J-RF-CELL | RF-разъём сотовой антенны | 1 | 20 | 42.54 | 850.76 | Инженерная оценка КНР | https://www.alibaba.com/ | 42
Кабели и разъёмы | J-RF-GNSS | RF-разъём GNSS-антенны | 1 | 20 | 42.54 | 850.76 | Инженерная оценка КНР | https://www.alibaba.com/ | 43
Кабели и разъёмы | J-RF-LORA | RF-разъём LoRa-антенны | 1 | 20 | 42.54 | 850.76 | Инженерная оценка КНР | https://www.alibaba.com/ | 44
Кабели и разъёмы | J-SD1 | Разъём microSD с детектированием карты | 1 | 20 | 29.78 | 595.53 | Инженерная оценка КНР | https://www.lcsc.com/ | 45
Кабели и разъёмы | J-SIM1 | Разъём Nano-SIM, канал SIM1 | 1 | 20 | 21.27 | 425.38 | Инженерная оценка КНР | https://www.lcsc.com/ | 46
Кабели и разъёмы | J-SIM2 | Разъём Nano-SIM, канал SIM2 | 1 | 20 | 21.27 | 425.38 | Инженерная оценка КНР | https://www.lcsc.com/ | 47
Системная комплектация | ANT-CELL | Наружная антенна сотовой связи с кабелем | 1 | 20 | 595.53 | 11910.60 | Рыночный диапазон КНР / инженерная оценка | https://www.alibaba.com/wholesale/external-antenna-outdoor.html | 48
Системная комплектация | ANT-GNSS | Активная наружная GNSS-антенна с кабелем | 1 | 20 | 255.23 | 5104.54 | Рыночный диапазон КНР / инженерная оценка | https://www.alibaba.com/countrysearch/CN/gps-antenna-active.html | 49
Системная комплектация | ANT-LORA | Наружная антенна LoRa 868 МГц с кабелем | 1 | 20 | 1020.91 | 20418.17 | Рыночный диапазон КНР / инженерная оценка | https://www.alibaba.com/countrysearch/CN/antenna-cables.html | 50
Системная комплектация | BAT1 | LiFePO4 аккумулятор 12,8 В, 40–60 А·ч, BMS | 1 | 20 | 5529.92 | 110598.41 | Рыночный диапазон КНР / инженерная оценка | https://spanish.alibaba.com/g/12v-5.5ah-solar-lifepo4-battery.html | 51
Системная комплектация | HSG-3D | Резервный комплект корпуса, 3D-печать | 0 | 0 | 0.00 | 0.00 | Инженерная оценка КНР | https://www.alibaba.com/ | 52
Системная комплектация | HSG-IM | Пакет исходных данных/DFM под литьё под давлением | 0 | 0 | 0.00 | 0.00 | Инженерная оценка КНР | https://www.alibaba.com/ | 53
Системная комплектация | HSG-VC | Комплект корпуса, вакуумное литьё полиуретана | 1 | 20 | 2977.65 | 59552.99 | Рыночный диапазон КНР / инженерная оценка | https://www.alibaba.com/countrysearch/CN/vacuum-casting.html | 54
Системная комплектация | MPPT1 | Внешний MPPT-контроллер LiFePO4, 10 А | 1 | 20 | 1701.51 | 34030.28 | Рыночный диапазон КНР / инженерная оценка | https://www.alibaba.com/wholesale/solar-regulator-mppt-10.html | 55
Системная комплектация | PV1 | Солнечная панель наружного исполнения 60–80 Вт | 1 | 20 | 1063.45 | 21268.92 | Рыночный диапазон КНР / инженерная оценка | https://www.alibaba.com/wholesale/monocrystalline-panel-solar-80w.html | 56

Sheet: DNP
Не устанавливать
Пять резисторов DNP и три медные перемычки net tie не закупаются как устанавливаемые детали.
ID | Узел | Обозначение | MPN | Состояние | Количество
PR-039 | PCB-MAIN | R98 | ERJ-2GE0R00X | DNP | 0
PR-041 | PCB-PWR | R5;R9 | ERJ-2GE0R00X | DNP | 0
PR-048 | PCB-PWR | R15 | ERJ-2RKF1002X | DNP | 0
PR-050 | PCB-MAIN | R4 | R6 | ERJ-2RKF1003X | DNP | 0
PR-057 | PCB-PWR | R13;R14 | ERJ-2RKF4701X | DNP | 0
PR-064 | PCB-MAIN | C69 | C70 | C79 | C80 | GRM1555C1H100JA01D | DNP | 0
PR-068 | PCB-MAIN | C54 | C55 | C56 | C57 | C58 | C59 | GRM1555C1H330JA01D | DNP | 0
PR-075 | PCB-MAIN | C16 | C17 | GRM155R71E104KE14D | DNP | 0
