skif-ops/rs-zs-bpla/releases/evt-pre-20/2026-10-02-rev-d5/Заказ_плат_и_монтаж/02_PCB_MIC_управляемый_заказ_и_монтаж/02_Монтаж_платы/PCB-MIC_kicad_bom.csv

Reference | Value | Footprint | Quantity
C1 | 100nF X7R | Capacitor_SMD:C_0402_1005Metric | 1
J1 | 5040500691 | Dioneya:Molex_5040500691 | 1
MK1 | MMICT5838-00-012 | Dioneya:T5838_RevA | 1
R1 | 0R EVT_SI_TUNE | Resistor_SMD:R_0402_1005Metric | 1
