skif-ops/rs-zs-bpla/releases/evt-pre-20/2026-10-02-rev-d5/Заказ_плат_и_монтаж/02_PCB_MIC_управляемый_заказ_и_монтаж/02_Монтаж_платы/PCB-MIC_производственный_BOM.xlsx

Sheet: Производственный BOM
PCB-MIC Rev B — производственный BOM / Manufacturing BOM
Дата / Date | 30.09.2026 | Review B | ACCEPT CONTROLLED FIRST ARTICLE
Плата / Board SHA-256 | c57cebbb3886247166551fd242fa51350bc9be7fee6299e63e7eaac60518d518
Поз. | Описание / Description | Изготовитель | MPN | Корпус | На плату | На 80 PCBA | На 164 PCBA (41 станция) | Монтаж | Примечание / Note
C1 | Конденсатор 100 нФ 25 В X7R | TDK | CGA2B3X7R1E104K050BB | 0402 | 1 | 80 | 164 | Установить / Fit | Развязка MK1
J1 | Разъём 6 контактов 1,5 мм | Molex | 5040500691 | Micro-Lock PLUS | 1 | 80 | 164 | Установить / Fit | Pin 1 по сборочному PDF
MK1 | MEMS PDM микрофон | TDK InvenSense | MMICT5838-00-012 | Bottom port LGA | 1 | 80 | 164 | Установить / Fit | Порт Ø0,8 NPTH; паста в отверстии запрещена
R1 | Резистор 0 Ом | Panasonic | ERJ-2GE0R00X | 0402 | 1 | 80 | 164 | Установить / Fit | PDM data series link

Sheet: Контроль заказа
PCB-MIC — контроль заказа / Order control
Параметр / Parameter | Значение / Value | Контроль / Check | Статус / Status
Партия первого лота | 80 PCBA | 4 платы × 20 станций | RELEASED
Последовательность | 1 плата/панель → 79 PCBA | Продолжить после AOI/микроскопии и PDM | MANDATORY
Стек | 2 слоя, FR-4, 1,0 мм, 35 мкм, ENIG | Подтвердить stack ID фабрики | DFM
Сверловка | PTH и NPTH отдельными файлами | Порт Ø0,8 и H1/H2 Ø2,2 только NPTH | PASS
Трафарет MK1 | 4 дуги OD1,525 / ID1,025 / gap0,10 мм | Без пасты в центре порта | PASS
DRC / unconnected / ERC | 0 / 0 / 0 | KiCad 10.0.6 | PASS
Изменения | Только ECO | CAM/stack/drill/stencil/footprint/MPN | MANDATORY
