skif-ops/rs-zs-bpla/releases/evt-pre-20/2026-10-02-rev-d5/Заказ_плат_и_монтаж/03_PCB_MAIN_заказ_с_DFM/02_Монтаж_платы/PCB-MAIN_BOM_SCHEMATIC.csv

Ref | Value | Footprint | Qty | DNP
C1 | 100 nF 25 V X7R | Capacitor_SMD:C_0402_1005Metric | 1
C2 | 100 nF 25 V X7R | Capacitor_SMD:C_0402_1005Metric | 1
C3 | 100 nF 25 V X7R | Capacitor_SMD:C_0402_1005Metric | 1
C4 | 100 nF 25 V X7R | Capacitor_SMD:C_0402_1005Metric | 1
C5 | 100 nF 25 V X7R | Capacitor_SMD:C_0402_1005Metric | 1
C6 | 10 uF 10 V X5R | Capacitor_SMD:C_0603_1608Metric | 1
C7 | 100 nF 25 V X7R | Capacitor_SMD:C_0402_1005Metric | 1
C8 | 100 nF 25 V X7R | Capacitor_SMD:C_0402_1005Metric | 1
C9 | 1 uF 16 V X5R | Capacitor_SMD:C_0402_1005Metric | 1
C10 | 100 nF 25 V X7R | Capacitor_SMD:C_0402_1005Metric | 1
C11 | 1 uF 16 V X5R | Capacitor_SMD:C_0402_1005Metric | 1
C12 | 100 nF 25 V X7R | Capacitor_SMD:C_0402_1005Metric | 1
C13 | 10 uF 10 V X5R | Capacitor_SMD:C_0603_1608Metric | 1
C14 | 2.2 uF 10 V X5R | Capacitor_SMD:C_0402_1005Metric | 1
C15 | 2.2 uF 10 V X5R | Capacitor_SMD:C_0402_1005Metric | 1
C16 | 100 nF 25 V X7R | Capacitor_SMD:C_0402_1005Metric | 1 | DNP
C17 | 100 nF 25 V X7R | Capacitor_SMD:C_0402_1005Metric | 1 | DNP
C18 | 100 nF 25 V X7R | Capacitor_SMD:C_0402_1005Metric | 1
C19 | 22 uF 10 V X5R | Capacitor_SMD:C_0805_2012Metric | 1
C20 | 10 uF 10 V X5R | Capacitor_SMD:C_0603_1608Metric | 1
C21 | 100 nF 25 V X7R | Capacitor_SMD:C_0402_1005Metric | 1
C22 | 1 uF 16 V X5R | Capacitor_SMD:C_0402_1005Metric | 1
C23 | 100 nF 25 V X7R | Capacitor_SMD:C_0402_1005Metric | 1
C24 | 10 uF 10 V X5R | Capacitor_SMD:C_0603_1608Metric | 1
C25 | 100 nF 25 V X7R | Capacitor_SMD:C_0402_1005Metric | 1
C26 | 100 nF 25 V X7R | Capacitor_SMD:C_0402_1005Metric | 1
C27 | 100 nF 25 V X7R | Capacitor_SMD:C_0402_1005Metric | 1
C28 | 100 nF 25 V X7R | Capacitor_SMD:C_0402_1005Metric | 1
C29 | 100 nF 25 V X7R | Capacitor_SMD:C_0402_1005Metric | 1
C30 | 100 nF 25 V X7R | Capacitor_SMD:C_0402_1005Metric | 1
C31 | 100 nF 25 V X7R | Capacitor_SMD:C_0402_1005Metric | 1
C32 | 100 nF 25 V X7R | Capacitor_SMD:C_0402_1005Metric | 1
C33 | 100 nF 25 V X7R | Capacitor_SMD:C_0402_1005Metric | 1
C34 | 100 nF 25 V X7R | Capacitor_SMD:C_0402_1005Metric | 1
C35 | 100 nF 25 V X7R | Capacitor_SMD:C_0402_1005Metric | 1
C36 | 100 uF 6.3 V 15 mOhm polymer |  | 1
C37 | 220 nF 25 V X7R | Capacitor_SMD:C_0402_1005Metric | 1
C38 | 47 nF 25 V X7R | Capacitor_SMD:C_0402_1005Metric | 1
C39 | 150 pF 50 V C0G | Capacitor_SMD:C_0402_1005Metric | 1
C40 | 100 pF 50 V C0G | Capacitor_SMD:C_0402_1005Metric | 1
C41 | 68 pF 50 V C0G | Capacitor_SMD:C_0402_1005Metric | 1
C42 | 33 pF 50 V C0G | Capacitor_SMD:C_0402_1005Metric | 1
C43 | 10 pF 50 V C0G | Capacitor_SMD:C_0402_1005Metric | 1
C44 | 100 uF 6.3 V 15 mOhm polymer |  | 1
C45 | 100 nF 25 V X7R | Capacitor_SMD:C_0402_1005Metric | 1
C46 | 33 pF 50 V C0G | Capacitor_SMD:C_0402_1005Metric | 1
C47 | 10 pF 50 V C0G | Capacitor_SMD:C_0402_1005Metric | 1
C48 | 10 nF 25 V X7R | Capacitor_SMD:C_0402_1005Metric | 1
C49 | 100 nF 25 V X7R | Capacitor_SMD:C_0402_1005Metric | 1
C50 | 100 nF 25 V X7R | Capacitor_SMD:C_0402_1005Metric | 1
C51 | 100 nF 25 V X7R | Capacitor_SMD:C_0402_1005Metric | 1
C52 | 10 nF 25 V X7R | Capacitor_SMD:C_0402_1005Metric | 1
C53 | 10 nF 25 V X7R | Capacitor_SMD:C_0402_1005Metric | 1
C54 | 33 pF 50 V C0G | Capacitor_SMD:C_0402_1005Metric | 1 | DNP
C55 | 33 pF 50 V C0G | Capacitor_SMD:C_0402_1005Metric | 1 | DNP
C56 | 33 pF 50 V C0G | Capacitor_SMD:C_0402_1005Metric | 1 | DNP
C57 | 33 pF 50 V C0G | Capacitor_SMD:C_0402_1005Metric | 1 | DNP
C58 | 33 pF 50 V C0G | Capacitor_SMD:C_0402_1005Metric | 1 | DNP
C59 | 33 pF 50 V C0G | Capacitor_SMD:C_0402_1005Metric | 1 | DNP
C60 | 100 nF 25 V X7R | Capacitor_SMD:C_0402_1005Metric | 1
C61 | 10 uF 10 V X5R | Capacitor_SMD:C_0603_1608Metric | 1
C62 | 100 nF 25 V X7R | Capacitor_SMD:C_0402_1005Metric | 1
C63 | 10 nF 16 V X7R | Capacitor_SMD:C_0402_1005Metric | 1
C64 | 47 pF 25 V C0G | Capacitor_SMD:C_0402_1005Metric | 1
C65 | 100 nF 25 V X7R | Capacitor_SMD:C_0402_1005Metric | 1
C66 | 100 nF 25 V X7R | Capacitor_SMD:C_0402_1005Metric | 1
C67 | 10 uF 10 V X5R | Capacitor_SMD:C_0603_1608Metric | 1
C68 | 100 nF 25 V X7R | Capacitor_SMD:C_0402_1005Metric | 1
C69 | 10 pF 50 V C0G | Capacitor_SMD:C_0402_1005Metric | 1 | DNP
C70 | 10 pF 50 V C0G | Capacitor_SMD:C_0402_1005Metric | 1 | DNP
C71 | 100 nF 25 V X7R | Capacitor_SMD:C_0402_1005Metric | 1
C72 | 10 uF 10 V X5R | Capacitor_SMD:C_0603_1608Metric | 1
C73 | 100 nF 25 V X7R | Capacitor_SMD:C_0402_1005Metric | 1
C74 | 100 nF 25 V X7R | Capacitor_SMD:C_0402_1005Metric | 1
C75 | 10 uF 10 V X5R | Capacitor_SMD:C_0603_1608Metric | 1
C76 | 10 nF 25 V X7R | Capacitor_SMD:C_0402_1005Metric | 1
C77 | 4.7 nF 100 V X7R | Capacitor_SMD:C_0402_1005Metric | 1
C78 | 10 nF 25 V X7R | Capacitor_SMD:C_0402_1005Metric | 1
C79 | 10 pF 50 V C0G | Capacitor_SMD:C_0402_1005Metric | 1 | DNP
C80 | 10 pF 50 V C0G | Capacitor_SMD:C_0402_1005Metric | 1 | DNP
D1 | 5 V unidirectional 150 W TVS |  | 1
D2 | 5 V unidirectional 150 W TVS |  | 1
D3 | 5 V bidirectional 0.2 pF RF ESD |  | 1
D4 | 5.5 V unidirectional 0.5 pF RF ESD |  | 1
D5 | 5 V bidirectional 0.2 pF RF ESD |  | 1
D6 | 5.5 V 0.5 pF ESD |  | 1
D7 | 5.5 V 0.5 pF ESD |  | 1
D8 | 5.5 V 0.5 pF ESD |  | 1
D9 | 5.5 V 0.5 pF ESD |  | 1
D10 | 5.5 V 0.5 pF ESD |  | 1
D11 | 5.5 V 0.5 pF ESD |  | 1
FB1 | 600 Ohm at 100 MHz | Inductor_SMD:L_1206_3216Metric | 1
FL1 | 1582.4 MHz wideband GNSS SAW |  | 1
J6 | 2336582-1 |  | 1
J7 | 2336582-1 |  | 1
J8 | U.FL-R-SMT-1(60) |  | 1
J9 | U.FL-R-SMT-1(60) |  | 1
J10 | U.FL-R-SMT-1(60) |  | 1
J11 | USB4105-GF-A-120 |  | 1
J12 | MEM2052-00-195-00-A |  | 1
J13 | 504050-0291 |  | 1
J_MIC1 | 504050-0691 |  | 1
J_MIC2 | 504050-0691 |  | 1
J_MIC3 | 504050-0691 |  | 1
J_MIC4 | 504050-0691 |  | 1
J_PWR1 | 43045-1202 |  | 1
L1 | 2.2 uH 20% | Inductor_SMD:L_1210_3225Metric | 1
L2 | 27 nH 5% | Inductor_SMD:L_0402_1005Metric | 1
Q1 | MMBT3904,215 |  | 1
Q2 | MMBT3904,215 |  | 1
Q3 | MMBT3904,215 |  | 1
Q4 | Complementary N and P channel 20 V |  | 1
R1 | 10 kOhm 1% | Resistor_SMD:R_0402_1005Metric | 1
R2 | 100 kOhm 1% | Resistor_SMD:R_0402_1005Metric | 1
R3 | 100 kOhm 1% | Resistor_SMD:R_0402_1005Metric | 1
R4 | 100 kOhm 1% | Resistor_SMD:R_0402_1005Metric | 1 | DNP
R5 | 100 kOhm 1% | Resistor_SMD:R_0402_1005Metric | 1
R6 | 100 kOhm 1% | Resistor_SMD:R_0402_1005Metric | 1 | DNP
R7 | 10 kOhm 1% | Resistor_SMD:R_0402_1005Metric | 1
R8 | 22 Ohm 1% | Resistor_SMD:R_0402_1005Metric | 1
R9 | 22 Ohm 1% | Resistor_SMD:R_0402_1005Metric | 1
R10 | 22 Ohm 1% | Resistor_SMD:R_0402_1005Metric | 1
R11 | 22 Ohm 1% | Resistor_SMD:R_0402_1005Metric | 1
R12 | 22 Ohm 1% | Resistor_SMD:R_0402_1005Metric | 1
R13 | 2.2 kOhm 1% | Resistor_SMD:R_0402_1005Metric | 1
R14 | 2.2 kOhm 1% | Resistor_SMD:R_0402_1005Metric | 1
R15 | 22 Ohm 1% | Resistor_SMD:R_0402_1005Metric | 1
R16 | 22 Ohm 1% | Resistor_SMD:R_0402_1005Metric | 1
R17 | 22 Ohm 1% | Resistor_SMD:R_0402_1005Metric | 1
R18 | 22 Ohm 1% | Resistor_SMD:R_0402_1005Metric | 1
R19 | 100 kOhm 1% | Resistor_SMD:R_0402_1005Metric | 1
R20 | 100 kOhm 1% | Resistor_SMD:R_0402_1005Metric | 1
R21 | 100 kOhm 1% | Resistor_SMD:R_0402_1005Metric | 1
R22 | 100 kOhm 1% | Resistor_SMD:R_0402_1005Metric | 1
R23 | 100 kOhm 1% | Resistor_SMD:R_0402_1005Metric | 1
R24 | 4.7 kOhm 1% | Resistor_SMD:R_0402_1005Metric | 1
R25 | 47 kOhm 1% | Resistor_SMD:R_0402_1005Metric | 1
R26 | 4.7 kOhm 1% | Resistor_SMD:R_0402_1005Metric | 1
R27 | 47 kOhm 1% | Resistor_SMD:R_0402_1005Metric | 1
R28 | 10 kOhm 1% | Resistor_SMD:R_0402_1005Metric | 1
R29 | 100 kOhm 1% | Resistor_SMD:R_0402_1005Metric | 1
R30 | 10 kOhm 1% | Resistor_SMD:R_0402_1005Metric | 1
R31 | 10 kOhm 1% | Resistor_SMD:R_0402_1005Metric | 1
R32 | 100 kOhm 1% | Resistor_SMD:R_0402_1005Metric | 1
R33 | 100 kOhm 1% | Resistor_SMD:R_0402_1005Metric | 1
R34 | 100 kOhm 1% | Resistor_SMD:R_0402_1005Metric | 1
R35 | 100 kOhm 1% | Resistor_SMD:R_0402_1005Metric | 1
R36 | 22 Ohm 1% | Resistor_SMD:R_0402_1005Metric | 1
R37 | 22 Ohm 1% | Resistor_SMD:R_0402_1005Metric | 1
R38 | 1 kOhm 1% | Resistor_SMD:R_0402_1005Metric | 1
R39 | 0 Ohm | Resistor_SMD:R_0402_1005Metric | 1
R40 | 0 Ohm | Resistor_SMD:R_0402_1005Metric | 1
R41 | 1 kOhm 1% | Resistor_SMD:R_0402_1005Metric | 1
R42 | 0 Ohm | Resistor_SMD:R_0402_1005Metric | 1
R43 | 0 Ohm | Resistor_SMD:R_0402_1005Metric | 1
R44 | 47 kOhm 1% | Resistor_SMD:R_0402_1005Metric | 1
R45 | 100 kOhm 1% | Resistor_SMD:R_0402_1005Metric | 1
R46 | 10 kOhm 1% | Resistor_SMD:R_0402_1005Metric | 1
R47 | 100 kOhm 1% | Resistor_SMD:R_0402_1005Metric | 1
R48 | 10 kOhm 1% | Resistor_SMD:R_0402_1005Metric | 1
R49 | 10 kOhm 1% | Resistor_SMD:R_0402_1005Metric | 1
R50 | 0 Ohm | Resistor_SMD:R_0402_1005Metric | 1
R51 | 0 Ohm | Resistor_SMD:R_0402_1005Metric | 1
R52 | 0 Ohm | Resistor_SMD:R_0402_1005Metric | 1
R53 | 0 Ohm | Resistor_SMD:R_0402_1005Metric | 1
R54 | 0 Ohm | Resistor_SMD:R_0402_1005Metric | 1
R55 | 0 Ohm | Resistor_SMD:R_0402_1005Metric | 1
R56 | 22 Ohm 1% | Resistor_SMD:R_0402_1005Metric | 1
R57 | 22 Ohm 1% | Resistor_SMD:R_0402_1005Metric | 1
R58 | 22 Ohm 1% | Resistor_SMD:R_0402_1005Metric | 1
R59 | 560 Ohm 5% 0.1 W | Resistor_SMD:R_0402_1005Metric | 1
R60 | 100 kOhm 5% 0.1 W | Resistor_SMD:R_0402_1005Metric | 1
R61 | 100 kOhm 5% 0.1 W | Resistor_SMD:R_0402_1005Metric | 1
R62 | 10 Ohm 5% 0.25 W | Resistor_SMD:R_1206_3216Metric | 1
R63 | 100 kOhm 1% | Resistor_SMD:R_0402_1005Metric | 1
R64 | 100 kOhm 1% | Resistor_SMD:R_0402_1005Metric | 1
R65 | 100 kOhm 1% | Resistor_SMD:R_0402_1005Metric | 1
R66 | 100 kOhm 1% | Resistor_SMD:R_0402_1005Metric | 1
R67 | 10 kOhm 1% | Resistor_SMD:R_0402_1005Metric | 1
R68 | 10 kOhm 1% | Resistor_SMD:R_0402_1005Metric | 1
R69 | 22 Ohm 1% | Resistor_SMD:R_0402_1005Metric | 1
R70 | 22 Ohm 1% | Resistor_SMD:R_0402_1005Metric | 1
R71 | 22 Ohm 1% | Resistor_SMD:R_0402_1005Metric | 1
R72 | 22 Ohm 1% | Resistor_SMD:R_0402_1005Metric | 1
R73 | 0 Ohm | Resistor_SMD:R_0402_1005Metric | 1
R74 | 22 Ohm 1% | Resistor_SMD:R_0402_1005Metric | 1
R75 | 22 Ohm 1% | Resistor_SMD:R_0402_1005Metric | 1
R76 | 10 kOhm 1% | Resistor_SMD:R_0402_1005Metric | 1
R77 | 100 kOhm 1% | Resistor_SMD:R_0402_1005Metric | 1
R78 | 10 kOhm 1% | Resistor_SMD:R_0402_1005Metric | 1
R79 | 22 Ohm 1% | Resistor_SMD:R_0402_1005Metric | 1
R80 | 22 Ohm 1% | Resistor_SMD:R_0402_1005Metric | 1
R81 | 22 Ohm 1% | Resistor_SMD:R_0402_1005Metric | 1
R82 | 22 Ohm 1% | Resistor_SMD:R_0402_1005Metric | 1
R83 | 22 Ohm 1% | Resistor_SMD:R_0402_1005Metric | 1
R84 | 22 Ohm 1% | Resistor_SMD:R_0402_1005Metric | 1
R85 | 10 kOhm 1% | Resistor_SMD:R_0402_1005Metric | 1
R86 | 10 kOhm 1% | Resistor_SMD:R_0402_1005Metric | 1
R87 | 10 kOhm 1% | Resistor_SMD:R_0402_1005Metric | 1
R88 | 10 kOhm 1% | Resistor_SMD:R_0402_1005Metric | 1
R89 | 10 kOhm 1% | Resistor_SMD:R_0402_1005Metric | 1
R90 | 10 kOhm 1% | Resistor_SMD:R_0402_1005Metric | 1
R91 | 22 Ohm 1% | Resistor_SMD:R_0402_1005Metric | 1
R92 | 22 Ohm 1% | Resistor_SMD:R_0402_1005Metric | 1
R93 | 5.1 kOhm 1% | Resistor_SMD:R_0402_1005Metric | 1
R94 | 5.1 kOhm 1% | Resistor_SMD:R_0402_1005Metric | 1
R95 | 1 kOhm 1% | Resistor_SMD:R_0402_1005Metric | 1
R96 | 100 kOhm 1% | Resistor_SMD:R_0402_1005Metric | 1
R97 | 1 MOhm 1% | Resistor_SMD:R_0402_1005Metric | 1
R98 | 0 Ohm | Resistor_SMD:R_0402_1005Metric | 1 | DNP
R99 | 10 kOhm 1% | Resistor_SMD:R_0402_1005Metric | 1
R100 | 1 kOhm 1% | Resistor_SMD:R_0402_1005Metric | 1
R101 | 22 Ohm 1% | Resistor_SMD:R_0402_1005Metric | 1
R102 | 1 kOhm 1% | Resistor_SMD:R_0402_1005Metric | 1
R103 | 0 Ohm | Resistor_SMD:R_0402_1005Metric | 1
TP_BLE_SWD1 | TEST_PADS |  | 1
TP_CELL_DBG1 | TEST_PADS |  | 1
TP_CELL_USB1 | TEST_PADS |  | 1
TP_EOL1 | TEST_PADS |  | 1
TP_MCU_SWD1 | TEST_PADS |  | 1
U1 | STM32U585VIT6Q |  | 1
U2 | W25Q512JVFIQ |  | 1
U3 | LIS2DW12TR |  | 1
U4 | STTS22HTR |  | 1
U5 | Single rail-to-rail low-power op amp |  | 1
U6 | Single non-inverting open-drain buffer |  | 1
U7 | SN74AXC8T245PWR |  | 1
U8 | BG95-M3 |  | 1
U9 | MAX-M10S-00B |  | 1
U10 | E22-900M22S |  | 1
U11 | MDBT50Q-P1MV2 |  | 1
U12 | SDCIT2/32GB |  | 1
U13 | TS3A27518EPWR |  | 1
U14 | ESDALC6V1-5P6 |  | 1
U15 | ESDALC6V1-5P6 |  | 1
U16 | SN74AXC8T245PWR |  | 1
U17 | SN74LVC32APWR |  | 1
U18 | SN74AXC1T45DRLR |  | 1
U19 | 4 channel 0.5 pF ESD |  | 1
U20 | 4 channel 0.5 pF ESD |  | 1
U21 | 4 channel 0.5 pF ESD |  | 1
U22 | 4 channel 0.5 pF ESD |  | 1
U23 | 4 channel 0.5 pF ESD |  | 1
U24 | 4 channel 0.5 pF ESD |  | 1
U25 | 2 channel 0.7 pF USB ESD |  | 1
U26 | 2 channel 0.7 pF USB ESD |  | 1
U27 | 4 channel 0.5 pF ESD |  | 1
X1 | 32.768 kHz full-swing LVCMOS |  | 1
