skif-ops/rs-zs-bpla/releases/evt-pre-20/2026-10-02-rev-d5/Заказ_жгутов_и_кабелей/Заказ_и_распайка_жгутов.xlsx

Sheet: Сводка заказа
EVT-PRE-20 Rev D — заказ жгутов / Harness order
Заказ / Order | DIO-HARNESS-SET-EVT-D | Дата / Date | 30.09.2026 | Комплектов / Sets | 22 | Первый образец / First article | 1 set → 21 sets
Жгут / Harness | На комплект / Per set | Заказ / Order qty | Цепей / Circuits | Нарезка / Cut length | Провод / Wire | Окончание A / End A | Окончание B / End B
H-MIC1…H-MIC4 | 4 | 88 | 6 | 275 ±5 мм | TE 55A0111-24, 24 AWG | Molex 5040510601 + 5040520098 | Molex 5040510601 + 5040520098
H-MAIN-PWR | 1 | 22 | 12 | 440 ±5 мм | TE 55A0111-18 pins 1–6; Alpha 3051 pins 7–12 | Molex 430251200 | Molex 430251200
H-BAT-PWR | 1 | 22 | 2 | 330 ±5 мм | TE 55A0111-18, 18 AWG | TE 8-34114-1 M8 | Molex 430250200 + 430300038
ИТОГО / TOTAL | 6 | 132 | 38 | — | — | — | —

Sheet: Распайка 38 цепей
Жгуты — проводник за проводником / Wire-by-wire schedule
Жгут | ID | Откуда | Разъём A | Pin A | Куда | Разъём B | Pin B | Цепь | Провод | Цвет | Длина, мм
H-MIC1 | MIC1-01 | PCB-MAIN | J_MIC1_MATING_5040510601 | 1 | PCB-MIC1 | J1_MATING_5040510601 | 1 | 1V8_MIC | AWG24_TE_55A0111-24_OD0P94MM | RED | 275 ±5
H-MIC1 | MIC1-02 | PCB-MAIN | J_MIC1_MATING_5040510601 | 2 | PCB-MIC1 | J1_MATING_5040510601 | 2 | GND | AWG24_TE_55A0111-24_OD0P94MM | BLACK | 275 ±5
H-MIC1 | MIC1-03 | PCB-MAIN | J_MIC1_MATING_5040510601 | 3 | PCB-MIC1 | J1_MATING_5040510601 | 3 | PDM_CLK | AWG24_TE_55A0111-24_OD0P94MM | WHITE | 275 ±5
H-MIC1 | MIC1-04 | PCB-MAIN | J_MIC1_MATING_5040510601 | 4 | PCB-MIC1 | J1_MATING_5040510601 | 4 | PDM_DATA1 | AWG24_TE_55A0111-24_OD0P94MM | BLUE | 275 ±5
H-MIC1 | MIC1-05 | PCB-MAIN | J_MIC1_MATING_5040510601 | 5 | PCB-MIC1 | J1_MATING_5040510601 | 5 | MIC_WAKE1 | AWG24_TE_55A0111-24_OD0P94MM | VIOLET | 275 ±5
H-MIC1 | MIC1-06 | PCB-MAIN | J_MIC1_MATING_5040510601 | 6 | PCB-MIC1 | J1_MATING_5040510601 | 6 | AAD_CFG | AWG24_TE_55A0111-24_OD0P94MM | GREY | 275 ±5
H-MIC2 | MIC2-01 | PCB-MAIN | J_MIC2_MATING_5040510601 | 1 | PCB-MIC2 | J1_MATING_5040510601 | 1 | 1V8_MIC | AWG24_TE_55A0111-24_OD0P94MM | RED | 275 ±5
H-MIC2 | MIC2-02 | PCB-MAIN | J_MIC2_MATING_5040510601 | 2 | PCB-MIC2 | J1_MATING_5040510601 | 2 | GND | AWG24_TE_55A0111-24_OD0P94MM | BLACK | 275 ±5
H-MIC2 | MIC2-03 | PCB-MAIN | J_MIC2_MATING_5040510601 | 3 | PCB-MIC2 | J1_MATING_5040510601 | 3 | PDM_CLK | AWG24_TE_55A0111-24_OD0P94MM | WHITE | 275 ±5
H-MIC2 | MIC2-04 | PCB-MAIN | J_MIC2_MATING_5040510601 | 4 | PCB-MIC2 | J1_MATING_5040510601 | 4 | PDM_DATA2 | AWG24_TE_55A0111-24_OD0P94MM | YELLOW | 275 ±5
H-MIC2 | MIC2-05 | PCB-MAIN | J_MIC2_MATING_5040510601 | 5 | PCB-MIC2 | J1_MATING_5040510601 | 5 | MIC_WAKE2 | AWG24_TE_55A0111-24_OD0P94MM | VIOLET | 275 ±5
H-MIC2 | MIC2-06 | PCB-MAIN | J_MIC2_MATING_5040510601 | 6 | PCB-MIC2 | J1_MATING_5040510601 | 6 | AAD_CFG | AWG24_TE_55A0111-24_OD0P94MM | GREY | 275 ±5
H-MIC3 | MIC3-01 | PCB-MAIN | J_MIC3_MATING_5040510601 | 1 | PCB-MIC3 | J1_MATING_5040510601 | 1 | 1V8_MIC | AWG24_TE_55A0111-24_OD0P94MM | RED | 275 ±5
H-MIC3 | MIC3-02 | PCB-MAIN | J_MIC3_MATING_5040510601 | 2 | PCB-MIC3 | J1_MATING_5040510601 | 2 | GND | AWG24_TE_55A0111-24_OD0P94MM | BLACK | 275 ±5
H-MIC3 | MIC3-03 | PCB-MAIN | J_MIC3_MATING_5040510601 | 3 | PCB-MIC3 | J1_MATING_5040510601 | 3 | PDM_CLK | AWG24_TE_55A0111-24_OD0P94MM | WHITE | 275 ±5
H-MIC3 | MIC3-04 | PCB-MAIN | J_MIC3_MATING_5040510601 | 4 | PCB-MIC3 | J1_MATING_5040510601 | 4 | PDM_DATA3 | AWG24_TE_55A0111-24_OD0P94MM | GREEN | 275 ±5
H-MIC3 | MIC3-05 | PCB-MAIN | J_MIC3_MATING_5040510601 | 5 | PCB-MIC3 | J1_MATING_5040510601 | 5 | MIC_WAKE3 | AWG24_TE_55A0111-24_OD0P94MM | VIOLET | 275 ±5
H-MIC3 | MIC3-06 | PCB-MAIN | J_MIC3_MATING_5040510601 | 6 | PCB-MIC3 | J1_MATING_5040510601 | 6 | AAD_CFG | AWG24_TE_55A0111-24_OD0P94MM | GREY | 275 ±5
H-MIC4 | MIC4-01 | PCB-MAIN | J_MIC4_MATING_5040510601 | 1 | PCB-MIC4 | J1_MATING_5040510601 | 1 | 1V8_MIC | AWG24_TE_55A0111-24_OD0P94MM | RED | 275 ±5
H-MIC4 | MIC4-02 | PCB-MAIN | J_MIC4_MATING_5040510601 | 2 | PCB-MIC4 | J1_MATING_5040510601 | 2 | GND | AWG24_TE_55A0111-24_OD0P94MM | BLACK | 275 ±5
H-MIC4 | MIC4-03 | PCB-MAIN | J_MIC4_MATING_5040510601 | 3 | PCB-MIC4 | J1_MATING_5040510601 | 3 | PDM_CLK | AWG24_TE_55A0111-24_OD0P94MM | WHITE | 275 ±5
H-MIC4 | MIC4-04 | PCB-MAIN | J_MIC4_MATING_5040510601 | 4 | PCB-MIC4 | J1_MATING_5040510601 | 4 | PDM_DATA4 | AWG24_TE_55A0111-24_OD0P94MM | ORANGE | 275 ±5
H-MIC4 | MIC4-05 | PCB-MAIN | J_MIC4_MATING_5040510601 | 5 | PCB-MIC4 | J1_MATING_5040510601 | 5 | MIC_WAKE4 | AWG24_TE_55A0111-24_OD0P94MM | VIOLET | 275 ±5
H-MIC4 | MIC4-06 | PCB-MAIN | J_MIC4_MATING_5040510601 | 6 | PCB-MIC4 | J1_MATING_5040510601 | 6 | AAD_CFG | AWG24_TE_55A0111-24_OD0P94MM | GREY | 275 ±5
H-MAIN-PWR | PWR-01 | PCB-PWR | J_MAIN_PWR_MATING_430251200 | 1 | PCB-MAIN | J_PWR_MATING_430251200 | 1 | 3V8_MODEM | AWG18_TE_55A0111-18_OD1P52MM | RED | 440 ±5
H-MAIN-PWR | PWR-02 | PCB-PWR | J_MAIN_PWR_MATING_430251200 | 2 | PCB-MAIN | J_PWR_MATING_430251200 | 2 | GND_MODEM | AWG18_TE_55A0111-18_OD1P52MM | BLACK | 440 ±5
H-MAIN-PWR | PWR-03 | PCB-PWR | J_MAIN_PWR_MATING_430251200 | 3 | PCB-MAIN | J_PWR_MATING_430251200 | 3 | 3V3_DIGITAL | AWG18_TE_55A0111-18_OD1P52MM | ORANGE | 440 ±5
H-MAIN-PWR | PWR-04 | PCB-PWR | J_MAIN_PWR_MATING_430251200 | 4 | PCB-MAIN | J_PWR_MATING_430251200 | 4 | GND_DIGITAL | AWG18_TE_55A0111-18_OD1P52MM | BLACK_WHITE | 440 ±5
H-MAIN-PWR | PWR-05 | PCB-PWR | J_MAIN_PWR_MATING_430251200 | 5 | PCB-MAIN | J_PWR_MATING_430251200 | 5 | 1V8_MIC | AWG18_TE_55A0111-18_OD1P52MM | BROWN | 440 ±5
H-MAIN-PWR | PWR-06 | PCB-PWR | J_MAIN_PWR_MATING_430251200 | 6 | PCB-MAIN | J_PWR_MATING_430251200 | 6 | GND_MIC | AWG18_TE_55A0111-18_OD1P52MM | BLACK_BLUE | 440 ±5
H-MAIN-PWR | PWR-07 | PCB-PWR | J_MAIN_PWR_MATING_430251200 | 7 | PCB-MAIN | J_PWR_MATING_430251200 | 7 | PWR_GOOD | AWG22_ALPHA_3051_OD1P575MM | WHITE | 440 ±5
H-MAIN-PWR | PWR-08 | PCB-PWR | J_MAIN_PWR_MATING_430251200 | 8 | PCB-MAIN | J_PWR_MATING_430251200 | 8 | FAULT | AWG22_ALPHA_3051_OD1P575MM | YELLOW | 440 ±5
H-MAIN-PWR | PWR-09 | PCB-PWR | J_MAIN_PWR_MATING_430251200 | 9 | PCB-MAIN | J_PWR_MATING_430251200 | 9 | EN_MODEM | AWG22_ALPHA_3051_OD1P575MM | GREEN | 440 ±5
H-MAIN-PWR | PWR-10 | PCB-PWR | J_MAIN_PWR_MATING_430251200 | 10 | PCB-MAIN | J_PWR_MATING_430251200 | 10 | EN_AUX | AWG22_ALPHA_3051_OD1P575MM | BLUE | 440 ±5
H-MAIN-PWR | PWR-11 | PCB-PWR | J_MAIN_PWR_MATING_430251200 | 11 | PCB-MAIN | J_PWR_MATING_430251200 | 11 | I2C2_SCL | AWG22_ALPHA_3051_OD1P575MM | VIOLET | 440 ±5
H-MAIN-PWR | PWR-12 | PCB-PWR | J_MAIN_PWR_MATING_430251200 | 12 | PCB-MAIN | J_PWR_MATING_430251200 | 12 | I2C2_SDA | AWG22_ALPHA_3051_OD1P575MM | GREY | 440 ±5
H-BAT-PWR | BAT-01 | SYSTEM-BAT1 | RELION_RB40_M8_POSITIVE | + | PCB-PWR | J_PWR_IN_MATING_430250200 | 1 | VBAT_PLUS | AWG18_TE_55A0111-18_OD1P52MM | RED | 330 ±5
H-BAT-PWR | BAT-02 | SYSTEM-BAT1 | RELION_RB40_M8_NEGATIVE | - | PCB-PWR | J_PWR_IN_MATING_430250200 | 2 | VBAT_MINUS | AWG18_TE_55A0111-18_OD1P52MM | BLACK | 330 ±5

Sheet: Материалы
Материалы на 22 комплекта / Materials for 22 sets
MPN | Описание / Description | Точное кол-во / Net qty | Рекомендуемый заказ / Buy qty | Ед. | Применение / Use | Примечание / Note
Molex 5040510601 | Корпус 6 pin | 176 | 176 | шт. | H-MIC оба конца | Без замены
Molex 5040520098 | Контакт Pico-Lock | 1056 | 1162 | шт. | H-MIC | 10% технологический резерв
Molex 430251200 | Корпус 12 pin | 44 | 44 | шт. | H-MAIN-PWR оба конца | Без замены
Molex 430300038 | Контакт 18 AWG | 308 | 339 | шт. | MAIN pins 1–6; BAT board end | 10% технологический резерв
Molex 430300001 | Контакт 20–24 AWG | 264 | 291 | шт. | MAIN pins 7–12 | 10% технологический резерв
Molex 430250200 | Корпус 2 pin | 22 | 22 | шт. | H-BAT-PWR board end | Без замены
TE 8-34114-1 | Кольцевой наконечник M8 | 44 | 49 | шт. | H-BAT-PWR battery end | 10% технологический резерв
TE 55A0111-24 | Провод 24 AWG | 145.2 | 159.72 | м | Все MIC цепи | 10% технологический резерв
TE 55A0111-18 | Провод 18 AWG | 72.6 | 79.86 | м | MAIN 1–6 + BAT | 10% технологический резерв
Alpha Wire 3051 | Провод 22 AWG | 58.08 | 63.89 | м | MAIN 7–12 | 10% технологический резерв

Sheet: Контроль
Контроль производства и приёмки / Manufacturing and acceptance control
Этап / Step | Требование / Requirement | Запись / Record | Критерий / Criterion
Первый комплект | Оснастка, crimp height, destructive pull каждого типа | First article report | PASS до запуска остальных 21
100% электрический тест | Pin-to-pin, полярность, обрыв, cross-short | Реестр по Harness_ID | Без дефектов
Сопротивление | MIC и MAIN-PWR ≤0,15 Ом; BAT-PWR ≤0,10 Ом | Измерение каждого проводника | В пределах допуска
Внешний вид | Жилы, изоляция, защёлки, маркировка, strain relief | Визуальный протокол | Без повреждений
Сборка станции | PDM/AAD, I²C 100 кГц, rail drop/thermal, BAT 5 A | EVT station record | PASS по ПМИ

Sheet: Антенны и RF
EVT-PRE-20 Rev D — антенны и RF-кабели / Antennas and RF cables
Тракт | PCB-MAIN | Функция | Пигтейл | Длина | Сторона платы | Bulkhead | Антенна | Антенна, описание | Заказ пигтейлов | Заказ антенн
RF-CELL | J8 | CELL/LTE | Taoglas CAB.0243 | 150 мм | MHF I/U.FL-compatible R/A | SMA(F), normal polarity | Taoglas G30.B.108111 | SMA(M), LTE, IP67, 1 m cable | 66 | 22
RF-GNSS | J9 | GNSS L1 active | Taoglas CAB.0243 | 150 мм | MHF I/U.FL-compatible R/A | SMA(F), normal polarity | Taoglas AA.166.A.301111 | SMA(M), active GNSS, IP67, 3 m RG174 | 66 | 22
RF-RU868 | J10 | LoRa RU868 | Taoglas CAB.0243 | 150 мм | MHF I/U.FL-compatible R/A | SMA(F), normal polarity | Taoglas TI.89.B.2111W | SMA(M), 860–930 MHz, IP67 | 66 | 22
