skif-ops/rs-zs-bpla/releases/evt-pre-20/2026-10-02-rev-d5/Основной_пакет/03_Корпуса_для_3D_печати_ПРЕДВАРИТЕЛЬНО/Ведомость_печатных_деталей_акустической_головы.xlsx

Акустическая голова 3+1: детали и уплотнение
PCB-MIC Rev B заказана; конструкция платы не меняется. Геометрия корпуса предварительная.
 |  | 20 | 40 | 41
Артикул | На 1 станцию | На 20 | На 40 | На 41 | Наименование
DIO-3DP-MC-001B_body | 4 | 80 | 160 | 164 | Корпус микрофона / microphone body
DIO-3DP-MC-001B_lid | 4 | 80 | 160 | 164 | Крышка микрофона / microphone lid
DIO-3DP-AH-001C_sealed_floor_carrier | 1 | 20 | 40 | 41 | Закрытое основание с дренажом / closed drained floor
DIO-3DP-AH-001C_cable_hatch_north | 1 | 20 | 40 | 41 | Первая половина кабельного лючка / cable hatch half A
DIO-3DP-AH-001C_cable_hatch_south | 1 | 20 | 40 | 41 | Вторая половина кабельного лючка / cable hatch half B
DIO-3DP-AH-001C_central_mast | 1 | 20 | 40 | 41 | Центральная стойка / central mast
DIO-3DP-AH-001C_upper_carrier | 1 | 20 | 40 | 41 | Верхняя траверса / upper carrier
DIO-3DP-AH-001C_integral_upper_cage | 1 | 20 | 40 | 41 | Цельная клетка: верхнее кольцо, пояс и 8 пластин / integral cage
DIO-3DP-AH-001C_dome | 1 | 20 | 40 | 41 | Высокий купол / taller dome
FOAM-OPEN-CELL-10MM-TRIAL | 1 | 20 | 40 | 41 | Раскройный цилиндр 10 мм; MPN после испытаний / foam trial cut
ELASTOMER-HATCH-SEAL-TRIAL | 1 | 20 | 40 | 41 | Уплотнение периметра, шва и 4 жгутов; MPN после испытаний / hatch seal
Статус: опытная печать; примерка и акустические испытания обязательны.
Поролон и уплотнитель: пробные материалы, MPN и цены не утверждены.
