skif-ops/rs-zs-bpla/releases/evt-pre-20/2026-10-02-rev-d5/Программа_EVT_и_Мухоед/02_Таблицы_испытаний_и_отчетов/EVT_матрица_и_отчеты.xlsx

Sheet: Матрица EVT
Матрица EVT-PRE-20
План испытаний; не означает, что испытания выполнены.
Test_ID | Area | Population | Precondition | Method | Primary_Metric | Acceptance | Retest | Required_Evidence | Status
EVT-CM-01 | Configuration | SELECTED_EVT_LOT_ALL_UNITS | Released manifest | Automated and independent manual verify | Hash and identity consistency | 100 percent exact match | After any configuration change | Verifier logs and signed review | NOT_RUN
EVT-ELEC-01 | Electrical safety | SELECTED_EVT_LOT_ALL_UNITS | EOL ready | Polarity insulation protection and fault injection within safe fixture | No unsafe condition | Limits per released power specification | After power rework | Waveforms thermal images logs | NOT_RUN
EVT-PWR-01 | PCB-PWR rail integrity | 3_ENGINEERING_SAMPLES_THEN_SELECTED_EVT_LOT_EOL | PCB-PWR and PCB-MAIN connected by released-length 18 AWG harness | Apply 3V8 and 3V3 load steps plus representative LTE/EGPRS burst at nominal min/max input and +70 C; probe all U8 VBAT pads and connector ends | Rail undershoot recovery stability harness drop and RF path resistance | All U8 VBAT pads remain >=3.3 V; RF path <=100 mOhm at 25 C; no unintended current limit oscillation or brownout | After power component harness connector placement routing or modem change | Scope waveforms four-wire resistance thermal data setup photos and raw load profile | NOT_RUN
EVT-PWR-02 | PCB-PWR conducted emissions | 3_ENGINEERING_SAMPLES | Representative battery MPPT and final-length external harness | Measure differential and common-mode current/voltage on battery and MPPT harness using LISN and calibrated current probe in worst 3V8 3V3 LTE and switching modes | Conducted spectrum and time-domain harness current | Limits frozen in EMC test plan before execution; no unmitigated dominant converter emissions | After input filter buck frequency layout harness or enclosure change | LISN/current-probe calibration spectrum plots operating-mode logs and setup photos | NOT_RUN
EVT-PWR-03 | PCB-PWR RF coexistence | 3_ENGINEERING_SAMPLES | Conducted-emissions setup and representative antennas available | Near-field scan both buck hot loops then exercise GNSS LoRa LTE and BLE separately and concurrently at worst converter loads | Receiver desense packet error GNSS C/N0 cellular margin and near-field hotspots | Frozen RF coexistence limits met with no destructive or persistent service loss | After buck layout frequency filter antenna enclosure or RF profile change | Near-field maps RF logs spectrum captures and synchronized power traces | NOT_RUN
EVT-PWR-04 | PCB-PWR input-filter decision | ENGINEERING_SAMPLE | EVT-PWR-01 through EVT-PWR-03 evidence available | Document no-filter acceptance or populate a simulated damped filter candidate; repeat startup load-step transient and conducted-emissions tests | Stability margin ringing startup rail recovery and emissions improvement | As-built no-filter disposition recorded; any populated filter requires ECO and repeat stability/emissions evidence | After filter value topology source impedance or PCB placement change | Impedance/simulation file BOM state waveforms spectra and signed disposition | NOT_RUN
EVT-ENE-01 | Energy states | SELECTED_EVT_LOT_ALL_UNITS | Representative firmware and battery | Measure S0-S4 at min nominal max supply | Current power transition latency | Limits frozen from energy budget before test | After firmware or power change | Raw CSV and setup photos | NOT_RUN
EVT-ENE-02 | Solar charge | At_least_3_per_battery_MPPT_variant | Selected production samples | PV simulator sweep cold Voc and thermal test | Charge profile efficiency reverse current temperature | Released battery and MPPT limits | After power or supplier change | IV curves thermal logs | NOT_RUN
EVT-ENE-03 | No-sun autonomy | Instrumented_sample_then_model_all | EVT-ENE-01 passed | Measured duty cycle plus conservative calculation and long soak | Days and energy margin | 30 days target with declared assumptions | After duty cycle change | Calculation source and soak logs | NOT_RUN
EVT-AAD-01 | T5838 AAD configuration and wake | 3_ENGINEERING_SAMPLES_THEN_SELECTED_EVT_LOT_EOL | Rev.A 6-wire MIC harness and firmware target available | Enable 1V8_MIC; start PDM CLK above 50 kHz; transmit THSEL one-wire configuration; complete stop symbol; disable PDM CLK for AAD D2; arm PA8 EXTI; inject calibrated acoustic events and negative background; repeat at nominal min/max supply and -40/+70 C subsets | THSEL timing WAKE latency false-wake rate S0 current transition-to-PDM success | All four microphones accept the programmed profile under common AAD_CFG; no stuck bus or false electrical wake; every valid WAKE reaches PA8 and transitions to PDM capture; timing conforms to T5838 protocol; S0 current and false-wake limits meet frozen EVT thresholds | After microphone translator harness firmware clock or threshold change | Oscilloscope captures PDM_CLK THSEL MIC_WAKE1..4 aggregated MIC_WAKE; current traces; event logs; acoustic stimulus records | NOT_RUN
EVT-ENV-COLD | Environment cold | 3_ENGINEERING_SAMPLES_THEN_SELECTED_EVT_LOT_EOL_COLD_SCREEN | Released Rev.A hardware and representative battery | Stabilize chamber at -40 C; cold boot; AAD wake; PDM capture; GNSS; BLE commissioning; cellular attach where network fixture supports; LoRa RX/TX profile test; storage read/write; repeated power cycle | Startup success rail margins oscillator/PPS behavior audio integrity RF service operation | No destructive failure or unsafe reset loop; mandatory station functions recover and operate at -40 C; component case/junction estimates remain within released limits | After component PCB enclosure firmware or battery change | Chamber log scope captures current traces station logs audio RF evidence | NOT_RUN
EVT-ENV-HOT | Environment hot | 3_ENGINEERING_SAMPLES_THEN_SELECTED_EVT_LOT_EOL_HOT_SCREEN | Released Rev.A hardware and representative enclosure | Stabilize chamber at +70 C; run worst-case realistic concurrent load including BG95 traffic GNSS LoRa activity BLE service window storage and acoustic DSP; soak then restart | Component/PCB temperatures brownout errors RF/audio degradation watchdog resets | No thermal shutdown/brownout/data corruption outside designed protective behavior; all measured/estimated junction temperatures remain below datasheet limits with documented margin | After component PCB enclosure firmware or thermal-layout change | Thermocouple/IR data current traces logs RF/audio evidence | NOT_RUN
EVT-ENV-CYCLE | Environment temperature cycling | 3_engineering_samples | Cold/hot tests passed | Cycle -40 to +70 C with powered and unpowered segments; inspect connectors seals solder joints oscillator timing and calibrated acoustic response before/after | Mechanical/electrical drift intermittent faults calibration change | No intermittent connector/solder failure; no permanent functional degradation; acoustic/RF/timing deltas within frozen EVT limits | After material connector PCB or enclosure change | Chamber profile continuity logs inspection photos before/after calibration | NOT_RUN
EVT-ENV-BATT-COLD | Power low-temperature charge inhibit | At_least_3_per_battery_MPPT_variant | Selected battery/BMS/MPPT samples | Cool battery cell sensor below 0 C while station load remains operational; present valid PV/input; attempt charge through normal controller | Battery current charge inhibit state fault/recovery | No LiFePO4 charging below 0 C unless the selected released battery system has an approved heater/low-temperature charging method; normal discharge operation follows battery datasheet | After battery BMS MPPT firmware or temperature-sensor change | Cell temperature battery current controller logs scope capture | NOT_RUN
EVT-AUD-01 | Audio channels | SELECTED_EVT_LOT_ALL_UNITS | Calibrated fixture | Four-channel sweep noise clipping dropout phase test | Sensitivity mismatch phase delay SNR dropout | Frozen acoustic limits and delay no more than 1 sample where required | After mic or mechanical rework | WAV CSV calibration certificates | NOT_RUN
EVT-AUD-02 | Detection | Approved_positive_and_negative_dataset | Server and station release frozen | Blind replay and field capture | Pd FAR latency and UNKNOWN rate | Thresholds approved in test specification | After model DSP geometry change | Dataset manifest predictions report | NOT_RUN
EVT-TIM-01 | GNSS PPS | SELECTED_EVT_LOT_ALL_UNITS | GNSS RF setup | Cold warm start PPS offset holdover and cellular concurrent use | Fix time PPS error holdover error | Frozen timing limits | After GNSS clock or firmware rework | GNSS logs oscilloscope CSV | NOT_RUN
EVT-CELL-01 | Cellular attach | SELECTED_EVT_LOT_ALL_UNITS | Approved ordinary and or M2M SIM profiles | Power cycle weak signal outage and recovery | Attach success recovery time data use | Approved operator profile limits | After modem antenna SIM or firmware change | Modem logs network conditions | NOT_RUN
EVT-CELL-02 | MQTT TLS | SELECTED_EVT_LOT_ALL_UNITS | Server test environment | Publish ACK duplicate reconnect expired CA wrong hostname | TLS validation integrity dedup | All negative security tests rejected and valid traffic delivered once | After protocol credential or server change | Packet capture server and station logs | NOT_RUN
EVT-CELL-03 | Store forward | SELECTED_EVT_LOT_ALL_UNITS | Cellular outage fixture | Generate events offline then restore link | No loss no uncontrolled duplicate bounded storage | Limits frozen in ICD | After storage or protocol change | Event IDs hashes logs | NOT_RUN
EVT-CELL-04 | Dual SIM and APN failover | SELECTED_EVT_LOT_ALL_UNITS | Two approved public SIM profiles and safe-switch firmware | Run 100 slot switches; attach approved public APN profiles; reject private APN; inject power loss and link failures | ICCID mapping safe power sequence recovery time and event integrity | No SIM damage or identity mismatch; queue preserved; private APN rejected | After SIM mux modem public profile PCB or firmware change | Scope traces modem logs ICCID references server event IDs | NOT_RUN
EVT-LORA-RU | LoRa RU868 | All_RU868_units | Profile approved and locked | Conducted then authorized radiated test | Frequency power timing sensitivity packet integrity | Approved regional and RF specification | After RF or profile change | Spectrum plots packet logs profile hash | NOT_RUN
EVT-LORA-EU | LoRa EU868 future compatibility | Not_in_EVT_PRE_20 | Disabled template only | Static configuration and hardware compatibility review | No EU868 transmission in pilot | Template remains TX disabled and unprovisioned | After future EU pilot authorization | Future campaign evidence | NOT_APPLICABLE
EVT-BLE-01 | BLE security config | SELECTED_EVT_LOT_ALL_UNITS | Android build and service mode | Pair authorize read write invalid command timeout | Unauthorized access rejected valid config audited | All acceptance tests PASS | After BLE app or firmware change | Android station logs video optional | NOT_RUN
EVT-OTA-01 | Signed OTA | SELECTED_EVT_LOT_ALL_UNITS_PLUS_FAULT_INJECTION_SUBSET | Released signed images | A B update resume power loss bad signature downgrade rollback | Bootability authenticity recovery | All failure injections recover without unsigned boot | After bootloader image or Android change | Power trace logs slot hashes | NOT_RUN
EVT-SRV-01 | Mukhoyed functional | Released_server_build | Lockfile and assets available | Full pytest compileall protocol e2e | Automated tests | 100 percent pass | Every server change | CI logs and commit SHA | NOT_RUN
EVT-SRV-02 | Mukhoyed 20 station soak | 20_station_simulation_then_live_units | Ingress hardened and authenticated | Reconnect burst load dedup backup restore and 72h soak | Loss duplicates latency resources recovery | Limits approved before run | After deployment or protocol change | Metrics logs backup restore evidence | NOT_RUN
EVT-MECH-3D | 3D printed primary first-lot housing | FIRST_20_PRINTED_HOUSINGS_ALL_UNITS_PLUS_STRESS_SAMPLES | Controlled preliminary print files material profile and fit fixture | Inspect all 20 printed housings for board battery MPPT mic pod antenna and harness fit; measure dimensions and torque; stress assigned samples for vibration UV ingress and acoustics | Dimensions damage seal acoustic and RF delta | Customer-approved dimensional structural acoustic and IP limits; preliminary CAD alone is not acceptance | After CAD material print profile fixture or installed-route change | Print lot/material log FAI serial photos fit torque acoustic RF and ingress reports | NOT_RUN
EVT-MECH-VC | Vacuum cast housing if separately selected | NOT_IN_FIRST_20_PRINTED_LOT_CONDITIONAL_FUTURE_CAST | Separate customer casting decision released master material process and accepted FAI | Dimensional fit post-cure drop vibration UV and ingress | Dimensions warp seal acoustic and RF delta | Not applicable to first 20 printed housings; apply frozen casting limits only if casting is selected | After CAD material or supplier change | FAI material cert photos reports | NOT_APPLICABLE
EVT-MECH-IM | Injection molding source-data audit | Source_package_only | Released CAD drawings DFM request and tool specification | Audit draft ribs bosses wall thickness parting ejector inserts and material | Source package completeness and manufacturer DFM readiness | All required source artifacts complete; no pilot tool or molded part required | After CAD material or tooling concept change | Source audit DFM report and checklist | NOT_RUN
EVT-SYS-01 | Field system | Approved_site_allocation | Bench EVT passed | Install operate outage maintenance update and recovery | Availability false alarm service time data continuity | Customer-approved operational thresholds | After blocking system change | Site map weather logs events service records | NOT_RUN
EVT-MFG-01 | Full PCB lots receiving and process identity | ALL_22_MAIN_ALL_22_PWR_ALL_80_MIC_PCBA_LOTS | Selected factory stack IDs DFM and MAIN 76/76 POFV confirmed before panel | Reconcile lot quantities SHA Gerber drill BOM placement AOI polarity DNP and serials; match MAIN 76 POFV and PWR four 35 um copper layers to order | Configuration identity board count AOI defects and POFV completeness | 22 MAIN 22 PWR 80 MIC traceable PCBAs; 76/76 MAIN POFV and no unresolved factory deviation | After factory process file or component substitution change | Fab DFM stack IDs 76-map signoff AOI reports photos and SHA manifest | NOT_RUN
EVT-MIC-PORT-01 | PCB-MIC acoustic port and PDM | ALL_80_MIC_AOI_PLUS_ONE_BOARD_OR_PANEL_POST_LOT_FUNCTIONAL | Complete 80-PCBA lot fabricated without first-article pause | AOI all MK1 ports for obstruction paste and drill artifacts; microscope post-lot sample; stimulate MK1 and capture PDM | Open 0.80 mm port solder/adhesive clearance and PDM response | Port conforms to accepted fab drawing; no obstruction or misplaced paste; sampled PDM response valid | After stencil drill assembly process or mic substitution change | AOI image set microscope images sampled PDM waveform and affected-lot disposition | NOT_RUN
EVT-MAIN-RF-01 | As-routed PCB-MAIN RF validation | TWO_POST_LOT_MAIN_SAMPLES_PLUS_ALL_20_STATION_EOL | Full 22-PCBA lot complete; no controlled impedance or 50 ohm guarantee ordered | VNA path response and installed cellular GNSS LoRa sensitivity/coexistence on two samples; basic RF function on every station | S parameters VSWR insertion loss sensitivity and coexistence | Customer-approved RF limits met on actual routing; do not infer 50 ohm from geometry | After PCB stack RF component antenna or cable change | VNA calibration S parameters RF logs spectra sample serials and approved limits | NOT_RUN
EVT-RF-ANT-01 | Three external antenna and RF cable chains | ALL_20_STATION_EOL_PLUS_STRESS_SAMPLES | Controlled Taoglas antenna identities and CAB.0243 installed | Verify three separate antenna MPNs three CAB.0243 pigtails U.FL/SMA mate route bend radius at least 6.8 mm and sealed bulkhead; measure installed VNA response | Identity continuity retention bend route seal VSWR and installed sensitivity | Exact controlled identities and no physical defect; approved RF and seal limits met | After antenna pigtail enclosure bulkhead or routing change | Serial photos cable route measurements VNA calibration S parameters and RF logs | NOT_RUN

Sheet: Реестр EOL
Реестр выходного контроля
Пустые результаты заполняются после проверки каждой станции.
Serial | Attempt | Timestamp_UTC | HW_Rev | FW_Release | LoRa_Profile | Fixture_ID | Fixture_SW | Power_Result | Audio_Result | Timing_Result | Cellular_Result | LoRa_Result | BLE_Result | Mechanics_Result | Record_Result | Overall | Evidence_Directory_SHA256 | Deviation_ID | Operator | Reviewer
DIO-EVT-001 | 1 |  |  |  |  |  |  |  |  |  |  |  |  |  |  | NOT_RUN
DIO-EVT-002 | 1 |  |  |  |  |  |  |  |  |  |  |  |  |  |  | NOT_RUN
DIO-EVT-003 | 1 |  |  |  |  |  |  |  |  |  |  |  |  |  |  | NOT_RUN
DIO-EVT-004 | 1 |  |  |  |  |  |  |  |  |  |  |  |  |  |  | NOT_RUN
DIO-EVT-005 | 1 |  |  |  |  |  |  |  |  |  |  |  |  |  |  | NOT_RUN
DIO-EVT-006 | 1 |  |  |  |  |  |  |  |  |  |  |  |  |  |  | NOT_RUN
DIO-EVT-007 | 1 |  |  |  |  |  |  |  |  |  |  |  |  |  |  | NOT_RUN
DIO-EVT-008 | 1 |  |  |  |  |  |  |  |  |  |  |  |  |  |  | NOT_RUN
DIO-EVT-009 | 1 |  |  |  |  |  |  |  |  |  |  |  |  |  |  | NOT_RUN
DIO-EVT-010 | 1 |  |  |  |  |  |  |  |  |  |  |  |  |  |  | NOT_RUN
DIO-EVT-011 | 1 |  |  |  |  |  |  |  |  |  |  |  |  |  |  | NOT_RUN
DIO-EVT-012 | 1 |  |  |  |  |  |  |  |  |  |  |  |  |  |  | NOT_RUN
DIO-EVT-013 | 1 |  |  |  |  |  |  |  |  |  |  |  |  |  |  | NOT_RUN
DIO-EVT-014 | 1 |  |  |  |  |  |  |  |  |  |  |  |  |  |  | NOT_RUN
DIO-EVT-015 | 1 |  |  |  |  |  |  |  |  |  |  |  |  |  |  | NOT_RUN
DIO-EVT-016 | 1 |  |  |  |  |  |  |  |  |  |  |  |  |  |  | NOT_RUN
DIO-EVT-017 | 1 |  |  |  |  |  |  |  |  |  |  |  |  |  |  | NOT_RUN
DIO-EVT-018 | 1 |  |  |  |  |  |  |  |  |  |  |  |  |  |  | NOT_RUN
DIO-EVT-019 | 1 |  |  |  |  |  |  |  |  |  |  |  |  |  |  | NOT_RUN
DIO-EVT-020 | 1 |  |  |  |  |  |  |  |  |  |  |  |  |  |  | NOT_RUN

Sheet: Отклонения
Журнал отклонений
Открытые отклонения учитываются в решении о выпуске.
Deviation_ID | Opened_UTC | Serials_or_Lot | Requirement_or_Test | Description | Severity | Containment | Root_Cause | Corrective_Action | Verification | Owner | Due_UTC | Disposition | Status | Evidence
DEV-TEMPLATE |  |  |  |  | UNASSESSED |  |  |  |  |  |  |  | OPEN

Sheet: Трассировка
Трассировка требований
Связь требований с проверками и evidence.
Requirement_ID | Requirement | Source | Implementation | Verification | Population | Status | Evidence
REQ-CONF-001 | Two traceable EVT-20 production sets plus one bench station with each set retaining the 4 10 or 20 controlled lot model | Customer | EVT-20 selection plus both serial registers and individual travellers | EVT-CM-01 | PROGRAM_2X20_PLUS_1 | PARTIAL_PASS_CONFIGURATION | DIO-EVT-001 through DIO-EVT-040 plus DIO-EVT-B01 are assigned without overlap; build travellers remain unpopulated until hardware release
REQ-HW-001 | Station uses custom PCB not WeAct | Customer | PCB_MAIN PCB_MIC PCB_PWR released design | ERC DRC DFM plus inspection and EVT-MFG-01 | All_revisions | OPEN
REQ-AUD-001 | Four matched microphones in 3 plus 1 geometry | Project baseline | PCB_MIC and acoustic head | EVT-AUD-01 | SELECTED_EVT_LOT_ALL_UNITS | OPEN
REQ-AUD-002 | Lower triangle side is 120 mm and MIC4 is plus 150 mm | Project baseline | ACOUSTIC_GEOMETRY.csv | Dimensional measurement | SELECTED_EVT_LOT_ALL_UNITS | OPEN
REQ-PWR-001 | EVT-20 uses one 12.8 V 40 Ah LiFePO4 pack per station and 60 Ah is post-EVT only | Customer 2026-09-17 | RELiON RB40 exact EVT purchase identity plus PCB-PWR and measured power-state control | Assembly and EVT capacity DCIR BMS cold-system plus EVT-ENE-01/03 | SELECTED_EVT_LOT_ALL_UNITS | PARTIAL_DOCUMENTARY_PURCHASE_CONTROLLED | Exact MPN and 512 Wh nominal energy are purchase-controlled with no substitution; cold enclosure transport and autonomy evidence remain open for assembly and EVT
REQ-PWR-002 | EVT solar panel is 80 W within the 60-80 W class | Customer | SLD Tech SLP080S-12M plus Victron SCC075010060R exact EVT purchase identities | Assembly and EVT IV insulation cold-Voc mechanical plus EVT-ENE-02 | SELECTED_EVT_LOT_ALL_UNITS | PARTIAL_DOCUMENTARY_PURCHASE_CONTROLLED | Exact panel and controller MPNs are purchase-controlled with no substitution; physical interface and system evidence remain open for assembly and EVT
REQ-PWR-003 | Target no-sun autonomy is 30 days | Project baseline | Power states and duty-cycle control | EVT-ENE-03 | Representative_plus_model | OPEN
REQ-CELL-001 | Primary communications use GSM LTE outbound only | Customer and baseline | BG95 class modem and public APN profile | EVT-CELL-01/02 | SELECTED_EVT_LOT_ALL_UNITS | OPEN
REQ-CELL-002 | Pilot supports ordinary SIM without operator API | Customer clarification | Local SIM register and outbound MQTT TLS HTTPS | EVT-CELL-01/03 | Approved_SIM_profiles | OPEN
REQ-CELL-003 | Offline events are retained and delivered after recovery | Baseline | Portable atomic SHA-256 event outbox erase-isolated NOR adapter exact W25Q512JV JEDEC/SFDP/QE boot gate shared non-overlap archive/command/outbox binding fixed-length binary BG95 event uplink length-delimited BG95 receipt binding bounded raw-UART session canonical server/firmware application receipt and target bindings | Host fault-injection receipt NOR identity/QE and three-consumer layout BG95 session uplink/receipt runtime audits plus EVT-CELL-03 | SELECTED_EVT_LOT_ALL_UNITS | PARTIAL_PASS_HOST_OUTBOX_RECEIPT | Priority FIFO durable attempts duplicate conflict retry exhaustion torn writes per-slot erase isolation exact JEDEC/SFDP density QE restore/read-back shared fail-closed three-consumer non-overlap exact binary QMTPUB length-delimited QMTRECV single TX owner exact-payload receipt restart lookup and retry idempotency PASS; production command/outbox slot counts target memory-map OCTOSPI/sample USART-DMA/ISR/cache modem framing retain-policy verification endurance and assembled-station recovery remain open
REQ-CELL-004 | Two physical SIM cards use Dual SIM Single Standby and safe failover | Customer | Dual nano-SIM external mux plus portable audited action controller explicit modem-off/mux-High-Z/rail-off fault recovery BG95 QPOWD/status/full-ICCID/exact-pending-profile/online bridge and exact Rev.A GPIO polarity/interlock adapter with DET debounce bounded retry hold authenticated manual override and queue preservation | Strict host controller/bridge/profile-match/target-GPIO runtime QG-1/QG-2 plus STM32 HAL physical U13 and modem-power fault evidence and assembled-station EVT-CELL-04 | SELECTED_EVT_LOT_ALL_UNITS | PARTIAL_PASS_HOST_SAFE_FAILOVER_PROFILE_AND_GPIO_CONTRACT | Portable controller BG95 bridge and generated-pin adapter reject hot-switch order premature rail cut early fallback non-OFF power-on missing physical status wrong APN profile index unauthenticated change slot absence hold violation ICCID mismatch invalid link and brownout; production APN catalog durable audit STM32 HAL U13 fixture read-back measured 3V8 100 switch cycles operator and 24-hour evidence remain open
REQ-CELL-005 | Each pilot SIM uses only provisioned public APN profiles | Customer | Versioned public APN profile set; private APN rejected | EVT-CELL-01/02/04 | Approved_operator_profiles | OPEN
REQ-CELL-006 | Remote station commands are authenticated bounded and idempotent | Security baseline | Server Ed25519 canonical CBOR plus portable firmware BG95 bounded raw-UART single-owner length-delimited command/fixed-length ACK binding application channel bounded public-key trust adapter TTL atomic accepted/completed journal erase-isolated NOR adapter exact W25Q512JV boot gate and shared archive/command/outbox layout | Python runtime audit deterministic server-to-firmware vector C fragmented binary URC serialization NOR identity/QE restart/torn-commit shared-layout ACK retry/fault-injection tests plus target and EVT test | SELECTED_EVT_LOT_ALL_UNITS | PARTIAL_PASS_HOST_CODEC | Server codec trust journal erase-isolated NOR adapter exact JEDEC/SFDP/QE gate shared three-consumer non-overlap application channel and BG95 raw-UART session host binding QG PASS; target crypto USART-DMA/ISR/cache retain policy command slot count OCTOSPI/sample/endurance and hardware evidence open
REQ-LORA-001 | Every assembled station in the selected EVT lot uses RU868; common hardware retains future EU868 compatibility | Customer | Locked RU868 pilot profile and disabled EU868 future template | EVT-LORA-RU | SELECTED_EVT_LOT_ALL_UNITS | OPEN
REQ-LORA-002 | LoRa TX is disabled until regional approval | Engineering safety | tx_enabled false profiles | Configuration audit | All_units_before_release | OPEN
REQ-RF-001 | Cellular GNSS and LoRa use separate external SMA male antennas on housing SMA female bulkheads with internal U.FL-compatible pigtails | Customer 2026-09-17 | Taoglas G30.B.108111 AA.166.A.301111 TI.89.B.2111W and three CAB.0243 per station | EVT-RF-ANT-01 mating retention route fit VNA installed VSWR sensitivity coexistence seal and RU868 campaign | SELECTED_EVT_LOT_ALL_UNITS | PARTIAL_DOCUMENTARY_PURCHASE_CONTROLLED | Exact EVT RF-chain MPNs are purchase-controlled with no substitution; CAB.0243 has published -60..200 C and 6.8 mm minimum bend while cross-mate route fit numeric seal/IP and installed RF evidence remain open for assembly EOL and EVT
REQ-BLE-001 | BLE supports local configuration and diagnostics | Customer | Portable authenticated local commissioning guard plus pending nRF52840 service GATT | Portable strict C and independent hash/auth audit plus EVT-BLE-01 | SELECTED_EVT_LOT_ALL_UNITS | PARTIAL_PASS_HOST | Remote-origin rejection; 10-minute physical window; role gate; station SHA-256; audit intent/commit and read-back pass; nRF GATT hardware open
REQ-OTA-001 | Station supports signed resumable A B update and rollback | Customer | Secure boot OTA service and Android client | EVT-OTA-01 | SELECTED_EVT_LOT_ALL_UNITS_PLUS_FAULT_SUBSET | OPEN
REQ-REC-001 | USB-C provides controlled service recovery | Project baseline | Boot recovery interface | Recovery test | SELECTED_EVT_LOT_ALL_UNITS | OPEN
REQ-SRV-001 | Latest compatible Mukhoyed release is included | Customer | Server source release and lockfile | EVT-SRV-01 | Every_release | OPEN
REQ-SRV-002 | Mukhoyed deploys on Windows 11 and Ubuntu 24.04 | Customer | Deployment bundles | Fresh-install and restore tests | Each_platform | OPEN
REQ-SRV-003 | Server handles 20 stations | Project need | Authenticated ingress registry and storage | EVT-SRV-02 | Simulation_plus_live | OPEN
REQ-CLS-001 | Hierarchical family and type decisions use 4 to 8 unique feature windows | Customer | Portable firmware consensus plus bounded live server consensus and 4/6/8 temporal model | C unit API replay and field classification tests | Every_detection_series | PARTIAL_PASS_HOST | Host regression only; field validation remains open
REQ-POS-001 | Locked installation coordinates survive power loss and reject unauthorized or rollback writes | DEC-018 | Portable atomic dual-slot record with CRC commit marker read-back monotonic version and station-computed canonical SHA-256 | C fault-injection plus commissioning authorization/hash audit plus STM32 Flash and assembled-station tests | SELECTED_EVT_LOT_ALL_UNITS | PARTIAL_PASS_HOST | Portable store and local BLE guard QG passed; STM32 Flash nRF GATT durable audit and hardware evidence remain open
REQ-MECH-001 | First 20 EVT housings use preliminary controlled 3D-print files with physical fit and strength validation | Customer | Preliminary 3D-print CAD release with actual material process and lot record | EVT-MECH-3D all first-lot housings plus stress samples | FIRST_20_PRINTED_HOUSINGS | OPEN_PHYSICAL_FIT_IP_ACCEPTANCE
REQ-MECH-002 | Vacuum-cast and injection-mold source packages remain preliminary; casting is not used for the first 20 printed housings | Customer | Independent casting and injection CAD source packages for future DFM | EVT-MECH-IM source audit; EVT-MECH-VC only after separate casting decision | SOURCE_PACKAGE_AND_CONDITIONAL_FUTURE_CAST | NOT_APPLICABLE_FIRST_20_CASTING
REQ-MECH-003 | Enclosure minimum IP65 target IP67 | Project baseline | Seals membranes vents and process control | Leak plus ingress campaign | SELECTED_EVT_LOT_PRIMARY_OR_APPROVED_FALLBACK | OPEN
REQ-APP-001 | Android application configures station offline | Customer | No-GMS Android baseline with position validation canonical hash and read-back gate plus pending BLE transport | Android QG-1/QG-2 JVM tests and EVT-BLE-01 | Supported_devices | PARTIAL_PASS_HOST | Position commissioning domain contract implemented; BLE UUID pairing GATT device matrix and hardware evidence open
REQ-APP-002 | Android application updates station firmware securely | Customer | Signed OTA client with resume | Android acceptance plus EVT-OTA-01 | Supported_devices | OPEN
REQ-MFG-001 | Every assembled station in the selected 4 10 or 20-unit lot receives 100 percent EOL | Quality policy | EOL fixture and register | EOL_TEST_SPEC | SELECTED_EVT_LOT_ALL_UNITS | OPEN
REQ-MFG-002 | China procurement is traceable and substitutions controlled | Customer procurement intent | RFQ AVL incoming control ECN | Receiving audit | All_lots | OPEN
REQ-SEC-001 | Secrets and private signing keys are absent from Git and CM bundle | Security policy | Provisioning trust separation | Secret scan plus provisioning audit | Every_release | OPEN
REQ-CM-001 | All deliverables have QG1 and QG2 gates | Project baseline | Deliverable register and manifests | Independent release audit | Every_release | OPEN
REQ-MFG-003 | Full 22 MAIN 22 PWR 80 MIC PCBA lots are ordered without first-article pause; factory DFM stack and MAIN 76/76 POFV are confirmed before panel | Customer full-lot decision 2026-09-30 and Rev D order clarification | Controlled Rev D board order and factory acceptance record | EVT-MFG-01 | ALL_BOARD_LOTS | DOCUMENTARY_ORDER_SET_PHYSICAL_EVIDENCE_OPEN
REQ-MIC-001 | PCB-MIC MK1 acoustic port 0.80 mm remains open and PDM functional after full-lot assembly | PCB-MIC Review B and customer full-lot decision | Rev B PCB-MIC Gerber stencil and assembled microphone | EVT-MIC-PORT-01 and EVT-AUD-01 | ALL_80_MIC_AOI_PLUS_POST_LOT_SAMPLE | OPEN_PHYSICAL_EVIDENCE
REQ-RF-002 | As-routed PCB-MAIN RF path is validated on installed stations without a controlled-impedance or 50 ohm fabrication guarantee | Customer Rev D as-routed EVT decision | Current PCB-MAIN Rev B routing with exact antenna and pigtail set | EVT-MAIN-RF-01 and EVT-RF-ANT-01 | POST_LOT_SAMPLES_AND_ALL_20_STATIONS | OPEN_RF_LIMITS_AND_MEASUREMENTS

Sheet: Открытые входы
Открытые входные данные
Пункты OPEN не преобразуются автоматически в PASS.
Input_ID | Area | Required_Input | Why_Required | Blocks | Recommended_Default | Owner | Status
IN-001 | Pilot | Country and exact site type per unit | Determines radio operator environment and mechanical loads | RF_PROFILE_AND_EVT_PLAN | Russia as primary pilot if customer confirms | CUSTOMER | OPEN
IN-002 | Cellular | Exact public APN RAT and underlying carrier per supplied ICCID | Public-only policy is locked but technical profiles are still required at provisioning | BG_MODEM_SKU_AND_CELLULAR_EVT | MTS MegaFon Beeline T2 Tele2 and GLONASS supplied SIM; tariff is not an EVT input | INTEGRATION | PARTIALLY_RESOLVED
IN-003 | LoRa | Every station in the first 20-unit EVT lot uses RU868 windows 864-865 and 868.7-869.2 MHz | Required for labels provisioning and RF evidence | LOT_CONFIGURATION | EU868 retained only as future compatibility | CUSTOMER | LOCKED
IN-004 | Mechanics | Independent source packages are required for 3D printing vacuum casting and injection molding | Each process requires independent CAD DFM BOM and evidence | HOUSING_BOM_CAD | TPA is source data and DFM only unless separately authorized | CUSTOMER | LOCKED
IN-005 | Mechanics | First 20 station housings are 3D printed from preliminary controlled CAD; second 20 may also be printed; casting files remain future DFM source | Controls printed material process sample assignment and the conditional casting test | PRINTED_HOUSING_EVT_AND_CASTING_TEST_SCOPE | Use 20 printed housing sets in the first lot; require physical fit strength ingress acoustic and RF validation | CUSTOMER | LOCKED
IN-006 | Environment | Operating ambient -40..+70 C; project minimum storage -40..+70 C; electronic parts minimum rating -40..+85 C; selected battery/material datasheets may impose tighter storage/charge rules | Controls components battery charging materials and tests | COMPONENT_AND_TEST_LIMITS | Full-load hot test +70 C; cold start/operation -40 C; LiFePO4 charge inhibited below 0 C unless approved low-temperature system | CUSTOMER | LOCKED
IN-007 | Environment | Humidity UV salt fog dust chemical and icing exposure | Controls enclosure material coating and environmental EVT | MECHANICAL_RELEASE | TBD by customer site | CUSTOMER | OPEN
IN-008 | Installation | Mast diameter height attachment orientation and service access | Controls brackets wind load cable lengths and RF placement | MECHANICAL_RELEASE | TBD by customer installation | CUSTOMER | OPEN
IN-009 | Installation | Maximum wind and ice load | Required for structural and solar bracket calculation | MECHANICAL_RELEASE | TBD by customer site | CUSTOMER | OPEN
IN-010 | Power | RELiON RB40 is the controlled exact 12.8 V 40 Ah EVT purchase identity; freeze measured BMS cold enclosure dimensions and transport route | Required for enclosure safety BMS charge transport and 30-day model | POWER_AND_MECHANICAL_RELEASE | Order the exact 21-piece EVT quantity after quote and destination delivery confirmation with no substitution; validate capacity DCIR BMS thresholds and cold behavior during station assembly and EVT rather than through a separate pre-order unit | PROCUREMENT_CUSTOMER | DOCUMENTARY_PURCHASE_IDENTITY_COMPLETE_ENVIRONMENTAL_RELEASE_OPEN
IN-011 | Power | Victron SCC075010060R plus SBS050150200 are the controlled exact EVT MPPT and battery-temperature purchase identities; freeze configuration terminal stack and environmental proof | Required for interfaces charge profile quiescent current and 0 C charge inhibit | POWER_RELEASE | Order the exact EVT quantity after quote and destination delivery confirmation with no substitution; validate M10-eyelet to RB40-M8 retention VE.Smart configuration cold cutoff reverse current quiescent and transient behavior during assembly EOL and EVT | PROCUREMENT | DOCUMENTARY_PURCHASE_IDENTITY_COMPLETE_ENVIRONMENTAL_RELEASE_OPEN
IN-012 | Power | SLD Tech SLP080S-12M is the controlled exact 80 W EVT panel purchase identity; freeze mounting and cable interfaces | Required for cold Voc cable bracket and transport | POWER_AND_MECHANICAL_RELEASE | Order the exact 21-piece EVT quantity after quote and destination delivery confirmation with no substitution; close IV insulation wet leakage cold Voc bracket connector and transport evidence during assembly and EVT | PROCUREMENT_CUSTOMER | DOCUMENTARY_PURCHASE_IDENTITY_COMPLETE_MECHANICAL_RELEASE_OPEN
IN-013 | RF | Three separate exact SMA(M) external antenna identities mate to housing SMA(F) bulkheads through common exact Taoglas CAB.0243 pigtails; freeze physical placement and validation | Required for connectors coax enclosure and coexistence | PCB_AND_MECHANICAL_RELEASE | Order G30.B.108111 AA.166.A.301111 TI.89.B.2111W and CAB.0243 with no substitution after quote and destination delivery confirmation; close mate route seal and installed RF evidence during assembly EOL and EVT | RF_CUSTOMER | DOCUMENTARY_PURCHASE_IDENTITY_COMPLETE_PHYSICAL_RF_RELEASE_OPEN
IN-014 | Server | Hosting owner OS FQDN certificates backup destination and network boundary | Required for hardened Mukhoyed deployment | SERVER_RELEASE | Ubuntu 24.04 primary and Windows 11 service copy | CUSTOMER_IT | OPEN
IN-015 | Security | Device certificate authority owner and credential lifecycle | Required for provisioning revocation and TLS auth | PROVISIONING_AND_DEPLOYMENT | Project-owned offline CA or approved enterprise PKI | CUSTOMER_IT_SECURITY | OPEN
IN-016 | Operations | Station identifiers tenant names and commissioning roles | Required for registry QR ACL and Android workflow | PROVISIONING_AND_ANDROID | One pilot tenant and two roles as baseline | CUSTOMER | OPEN
IN-017 | Acceptance | Detection targets distances Pd FAR latency and negative set | Required for objective audio EVT result | ACOUSTIC_EVT_PASS | TBD by customer mission | CUSTOMER_ACOUSTICS | OPEN
IN-018 | Acceptance | Timing localization accuracy and station geometry at site | Required for GNSS PPS TDOA criteria | TIMING_AND_SYSTEM_EVT_PASS | TBD by customer deployment | CUSTOMER_SYSTEM | OPEN
IN-019 | Data | Retention privacy export and ownership rules | Required for server storage diagnostics and field evidence | SERVER_AND_ANDROID_RELEASE | No analytics and minimal redacted export | CUSTOMER_LEGAL_IT | OPEN
IN-020 | Logistics | China supplier restrictions destination carrier and desired build date | Required only for customer purchase execution transport documents and schedule | CUSTOMER_COMMERCIAL_PROCUREMENT | TBD by customer; does not block engineering or manufacturing-data release | PROCUREMENT_CUSTOMER | NON_BLOCKING_CUSTOMER_ACTION
IN-021 | RF | Approve installed-antenna VSWR loss sensitivity and coexistence limits for PCB-MAIN as-routed without controlled impedance | Needed for objective EVT-MAIN-RF-01 and EVT-RF-ANT-01 PASS | RF_EVT_PASS | Do not claim 50 ohm; freeze measured limits before execution | CUSTOMER_RF | OPEN
IN-022 | Fabrication | Selected fab stack IDs and DFM for PCB-MAIN/PWR plus signed MAIN 76/76 POFV map including C6.1 and D11.1 | Mandatory before full-lot panel release | PCB_PANEL_RELEASE | Record factory response and any ECO before panel | FABRICATOR | OPEN
IN-023 | Mechanics | Printed housing material process installed fit IP wind and ice acceptance limits for first 20 | Preliminary CAD cannot establish physical pass | HOUSING_EVT_PASS | Measure actual print lot and approve site-specific limits | CUSTOMER_MECHANICS | OPEN
