skif-ops/rs-zs-bpla/releases/evt-pre-20/2026-10-02-rev-d5/Основной_пакет/01_Закупка/Исходная_ведомость_цен_v02.xlsx

Sheet: Цены_КНР
ДИОНЕЯ · Плановые закупочные цены КНР · EVT-PRE-20
Параметр | Значение | Параметр | Значение
Дата оценки | 2026-09-09 | USD/RUB | 85.0757
Группа | Item ID | Наименование | Кол-во/станцию | Кол-во 20 | Цена/ед. USD | Стоимость 1 USD | Стоимость 20 USD | Цена/ед. ₽ | Стоимость 1 ₽ | Стоимость 20 ₽ | Основание цены | Источник
Электронная компонентная база | C-MIC | Локальные развязывающие конденсаторы микрофона | 8 | 160 | $0.02 | $0.16 | $3.20 | 1.701514 ₽ | 13.612112 ₽ | 272.24224 ₽ | Инженерная оценка КНР | https://www.lcsc.com/
Электронная компонентная база | MK1 | Цифровой PDM MEMS-микрофон T5838 | 4 | 80 | $1.57 | $6.28 | $125.60 | 133.568849 ₽ | 534.275396 ₽ | 10685.50792 ₽ | Текущий прайс/бенчмарк MPN | https://www.digikey.cn/en/products/detail/tdk-invensense/MMICT5838-00-012/16903860
Электронная компонентная база | PCB-MISC | Прочая элементная база PCB: R/C/L, ESD, развязка, мелкие пассивы | 1 | 20 | $8.00 | $8.00 | $160.00 | 680.6056 ₽ | 680.6056 ₽ | 13612.112 ₽ | Инженерный резерв для ещё не разложенных по MPN позиций Rev.A | https://www.lcsc.com/
Электронная компонентная база | PWR-FUSE-01 | Предохранитель входной цепи PCB-PWR | 1 | 20 | $0.25 | $0.25 | $5.00 | 21.268925 ₽ | 21.268925 ₽ | 425.3785 ₽ | Инженерная оценка КНР | https://www.lcsc.com/
Электронная компонентная база | PWR-REV-CTL | Контроллер защиты от переполюсовки и обратного тока | 1 | 20 | $13.30 | $13.30 | $266.00 | 1131.50681 ₽ | 1131.50681 ₽ | 22630.1362 ₽ | Текущий прайс/бенчмарк MPN | https://www.lcsc.com/product-image/C2941042.html
Электронная компонентная база | PWR-REV-FET | Силовой N-MOSFET 60 В, низкое Rds(on) | 1 | 20 | $1.50 | $1.50 | $30.00 | 127.61355 ₽ | 127.61355 ₽ | 2552.271 ₽ | Текущий прайс/бенчмарк MPN | https://lcsc.com/product-detail/MOSFET_Texas-Instruments-CSD18540Q5B_C86513.html
Электронная компонентная база | PWR-TVS-01 | TVS-защита силовой шины | 1 | 20 | $0.10 | $0.10 | $2.00 | 8.50757 ₽ | 8.50757 ₽ | 170.1514 ₽ | Инженерная оценка КНР | https://www.lcsc.com/
Электронная компонентная база | R-SHUNT-01 | Шунт 10 мОм, 4-выводный Kelvin | 1 | 20 | $0.50 | $0.50 | $10.00 | 42.53785 ₽ | 42.53785 ₽ | 850.757 ₽ | Инженерная оценка КНР | https://www.lcsc.com/
Электронная компонентная база | U-MON-01 | Монитор тока, напряжения и мощности батареи INA226 | 1 | 20 | $0.61 | $0.61 | $12.20 | 51.896177 ₽ | 51.896177 ₽ | 1037.92354 ₽ | Текущий прайс/бенчмарк MPN | https://www.lcsc.com/product-detail/C49851.html
Электронная компонентная база | U-PWR1 | DC/DC 3,8 В / 4 А для сотового модема | 1 | 20 | $2.64 | $2.64 | $52.80 | 224.599848 ₽ | 224.599848 ₽ | 4491.99696 ₽ | Текущий прайс/бенчмарк MPN | https://www.lcsc.com/product-detail/C43351623.html
Электронная компонентная база | U-PWR2 | DC/DC 3,3 В / 4 А цифрового питания | 1 | 20 | $2.64 | $2.64 | $52.80 | 224.599848 ₽ | 224.599848 ₽ | 4491.99696 ₽ | Текущий прайс/бенчмарк MPN | https://www.lcsc.com/product-detail/C43351623.html
Электронная компонентная база | U-PWR3 | Малошумящий LDO 1,8 В микрофонного тракта | 1 | 20 | $0.21 | $0.21 | $4.20 | 17.865897 ₽ | 17.865897 ₽ | 357.31794 ₽ | Текущий прайс/бенчмарк MPN | https://www.lcsc.com/product-detail/Voltage-Regulators-Linear-Low-Drop-Out-LDO-Regulators_Texas-Instruments-TPS7A2018PDBVR_C963430.html
Электронная компонентная база | U1 | Микроконтроллер STM32U585, защищённая low-power платформа | 1 | 20 | $14.45 | $14.45 | $289.00 | 1229.343865 ₽ | 1229.343865 ₽ | 24586.8773 ₽ | Текущий прайс/бенчмарк MPN | https://www.lcsc.com/product-detail/C5270986.html
Электронная компонентная база | U10 | LoRa-модуль SX1262 для RU868 | 1 | 20 | $4.60 | $4.60 | $92.00 | 391.34822 ₽ | 391.34822 ₽ | 7826.9644 ₽ | Текущий прайс/бенчмарк MPN | https://www.alibaba.com/p/ebyte-e22-900m22s-tcxo-7km-long_62443474220.html
Электронная компонентная база | U11 | BLE/OTA сопроцессор nRF52840 | 1 | 20 | $6.86 | $6.86 | $137.20 | 583.619302 ₽ | 583.619302 ₽ | 11672.38604 ₽ | Текущий прайс/бенчмарк MPN | https://www.tme.com/us/en-us/details/mdbt50q-p1mv2/iot-wifi-bluetooth-modules/raytac/
Электронная компонентная база | U12 | Промышленная microSD, 32 ГБ | 1 | 20 | $5.00 | $5.00 | $100.00 | 425.3785 ₽ | 425.3785 ₽ | 8507.57 ₽ | Инженерная оценка КНР | https://www.alibaba.com/
Электронная компонентная база | U13 | Коммутатор интерфейса двух SIM-карт | 1 | 20 | $0.68 | $0.68 | $13.60 | 57.851476 ₽ | 57.851476 ₽ | 1157.02952 ₽ | Текущий прайс/бенчмарк MPN | https://www.lcsc.com/product-detail/Analog-Switches-Multiplexers_Texas-Instruments-TS3A27518EPWR_C443721.html
Электронная компонентная база | U14-U15 | Малoёмкостная ESD/TVS-защита линий SIM | 2 | 40 | $0.15 | $0.30 | $6.00 | 12.761355 ₽ | 25.52271 ₽ | 510.4542 ₽ | Инженерная оценка КНР | https://www.lcsc.com/
Электронная компонентная база | U2 | QSPI NOR Flash 64 МБ | 1 | 20 | $8.76 | $8.76 | $175.20 | 745.263132 ₽ | 745.263132 ₽ | 14905.26264 ₽ | Текущий прайс/бенчмарк MPN | https://www.lcsc.com/product-image/C2962011.html
Электронная компонентная база | U3 | Малопотребляющий акселерометр | 1 | 20 | $0.91 | $0.91 | $18.20 | 77.418887 ₽ | 77.418887 ₽ | 1548.37774 ₽ | Текущий прайс/бенчмарк MPN | https://www.lcsc.com/product-detail/Motion-Sensors-Accelerometers_STMicroelectronics_C189624.html
Электронная компонентная база | U4 | Цифровой датчик температуры | 1 | 20 | $1.53 | $1.53 | $30.60 | 130.165821 ₽ | 130.165821 ₽ | 2603.31642 ₽ | Текущий прайс/бенчмарк MPN | https://www.lcsc.com/product-detail/temperature-and-humidity-sensor_stmicroelectronics-stts22htr_C2969838.html
Электронная компонентная база | U7 | Преобразователь логических уровней 1,8/3,3 В | 1 | 20 | $0.35 | $0.35 | $7.00 | 29.776495 ₽ | 29.776495 ₽ | 595.5299 ₽ | Инженерная оценка КНР | https://www.lcsc.com/
Электронная компонентная база | U8 | Сотовый модем LTE Cat-M1 / NB2 / EGPRS | 1 | 20 | $9.33 | $9.33 | $186.60 | 793.756281 ₽ | 793.756281 ₽ | 15875.12562 ₽ | Рыночный диапазон КНР / инженерная оценка | https://www.alibaba.com/showroom/bg95-m3-module.html
Электронная компонентная база | U9 | GNSS-модуль с выходом TIMEPULSE/PPS | 1 | 20 | $10.60 | $10.60 | $212.00 | 901.80242 ₽ | 901.80242 ₽ | 18036.0484 ₽ | Текущий прайс/бенчмарк MPN | https://www.lcsc.com/product-image/C4153167.html
Электронная компонентная база | X1 | Низкодрейфовый генератор 32,768 кГц | 1 | 20 | $1.12 | $1.12 | $22.40 | 95.284784 ₽ | 95.284784 ₽ | 1905.69568 ₽ | Текущий прайс/бенчмарк MPN | https://www.lcsc.com/product-detail/Programmable-Oscillators_SiTime-SIT1552AI-JE-DCC-32-768D_C367054.html
Производство плат | ASM-MAIN | Собранная основная плата контроллера PCB-MAIN | 1 | 20 | $12.00 | $12.00 | $240.00 | 1020.9084 ₽ | 1020.9084 ₽ | 20418.168 ₽ | Инженерная оценка JLCPCB/China PCBA | https://jlcpcb.com/help/article/pcb-assembly-price
Производство плат | ASM-MIC | Собранная микрофонная плата PCB-MIC | 4 | 80 | $4.00 | $16.00 | $320.00 | 340.3028 ₽ | 1361.2112 ₽ | 27224.224 ₽ | Инженерная оценка JLCPCB/China PCBA | https://jlcpcb.com/help/article/pcb-assembly-price
Производство плат | ASM-PWR | Собранная плата питания и защиты PCB-PWR | 1 | 20 | $8.00 | $8.00 | $160.00 | 680.6056 ₽ | 680.6056 ₽ | 13612.112 ₽ | Инженерная оценка JLCPCB/China PCBA | https://jlcpcb.com/help/article/pcb-assembly-price
Производство плат | PCB-MAIN | Печатная плата PCB-MAIN, 4 слоя | 1 | 20 | $5.00 | $5.00 | $100.00 | 425.3785 ₽ | 425.3785 ₽ | 8507.57 ₽ | Инженерная оценка JLCPCB/China PCBA | https://jlcpcb.com/help/article/pcb-assembly-price
Производство плат | PCB-MIC | Печатная плата микрофонного лепестка PCB-MIC | 4 | 80 | $1.50 | $6.00 | $120.00 | 127.61355 ₽ | 510.4542 ₽ | 10209.084 ₽ | Инженерная оценка JLCPCB/China PCBA | https://jlcpcb.com/help/article/pcb-assembly-price
Производство плат | PCB-PWR | Печатная плата PCB-PWR, 2 слоя, повышенная медь | 1 | 20 | $3.00 | $3.00 | $60.00 | 255.2271 ₽ | 255.2271 ₽ | 5104.542 ₽ | Инженерная оценка JLCPCB/China PCBA | https://jlcpcb.com/help/article/pcb-assembly-price
Кабели и разъёмы | HARNESS | Комплект маркированных кабельных жгутов станции | 1 | 20 | $16.61 | $16.61 | $332.20 | 1413.107377 ₽ | 1413.107377 ₽ | 28262.14754 ₽ | Инженерная оценка КНР | https://www.lcsc.com/product-detail/Housings-Wire-To-Board-Wire-To-Wire_MOLEX-5040510601_C505129.html
Кабели и разъёмы | J-MIC | 6-контактный разъём микрофонного жгута Pico-Lock | 4 | 80 | $0.26 | $1.04 | $20.80 | 22.119682 ₽ | 88.478728 ₽ | 1769.57456 ₽ | Текущий прайс/бенчмарк MPN | https://www.lcsc.com/product-detail/wire-to-board-connector_molex-5040500691_C563981.html
Кабели и разъёмы | J-PWR-MAIN | 12-контактный межплатный разъём MAIN-PWR, сторона MAIN | 1 | 20 | $2.50 | $2.50 | $50.00 | 212.68925 ₽ | 212.68925 ₽ | 4253.785 ₽ | Инженерная оценка КНР | https://www.lcsc.com/
Кабели и разъёмы | J-PWR-PWR | 12-контактный межплатный разъём MAIN-PWR, сторона PWR | 1 | 20 | $2.50 | $2.50 | $50.00 | 212.68925 ₽ | 212.68925 ₽ | 4253.785 ₽ | Инженерная оценка КНР | https://www.lcsc.com/
Кабели и разъёмы | J-RF-CELL | RF-разъём сотовой антенны | 1 | 20 | $0.50 | $0.50 | $10.00 | 42.53785 ₽ | 42.53785 ₽ | 850.757 ₽ | Инженерная оценка КНР | https://www.alibaba.com/
Кабели и разъёмы | J-RF-GNSS | RF-разъём GNSS-антенны | 1 | 20 | $0.50 | $0.50 | $10.00 | 42.53785 ₽ | 42.53785 ₽ | 850.757 ₽ | Инженерная оценка КНР | https://www.alibaba.com/
Кабели и разъёмы | J-RF-LORA | RF-разъём LoRa-антенны | 1 | 20 | $0.50 | $0.50 | $10.00 | 42.53785 ₽ | 42.53785 ₽ | 850.757 ₽ | Инженерная оценка КНР | https://www.alibaba.com/
Кабели и разъёмы | J-SD1 | Разъём microSD с детектированием карты | 1 | 20 | $0.35 | $0.35 | $7.00 | 29.776495 ₽ | 29.776495 ₽ | 595.5299 ₽ | Инженерная оценка КНР | https://www.lcsc.com/
Кабели и разъёмы | J-SIM1 | Разъём Nano-SIM, канал SIM1 | 1 | 20 | $0.25 | $0.25 | $5.00 | 21.268925 ₽ | 21.268925 ₽ | 425.3785 ₽ | Инженерная оценка КНР | https://www.lcsc.com/
Кабели и разъёмы | J-SIM2 | Разъём Nano-SIM, канал SIM2 | 1 | 20 | $0.25 | $0.25 | $5.00 | 21.268925 ₽ | 21.268925 ₽ | 425.3785 ₽ | Инженерная оценка КНР | https://www.lcsc.com/
Системная комплектация | ANT-CELL | Наружная антенна сотовой связи с кабелем | 1 | 20 | $7.00 | $7.00 | $140.00 | 595.5299 ₽ | 595.5299 ₽ | 11910.598 ₽ | Рыночный диапазон КНР / инженерная оценка | https://www.alibaba.com/wholesale/external-antenna-outdoor.html
Системная комплектация | ANT-GNSS | Активная наружная GNSS-антенна с кабелем | 1 | 20 | $3.00 | $3.00 | $60.00 | 255.2271 ₽ | 255.2271 ₽ | 5104.542 ₽ | Рыночный диапазон КНР / инженерная оценка | https://www.alibaba.com/countrysearch/CN/gps-antenna-active.html
Системная комплектация | ANT-LORA | Наружная антенна LoRa 868 МГц с кабелем | 1 | 20 | $12.00 | $12.00 | $240.00 | 1020.9084 ₽ | 1020.9084 ₽ | 20418.168 ₽ | Рыночный диапазон КНР / инженерная оценка | https://www.alibaba.com/countrysearch/CN/antenna-cables.html
Системная комплектация | BAT1 | LiFePO4 аккумулятор 12,8 В, 40–60 А·ч, BMS | 1 | 20 | $65.00 | $65.00 | $1300.00 | 5529.9205 ₽ | 5529.9205 ₽ | 110598.41 ₽ | Рыночный диапазон КНР / инженерная оценка | https://spanish.alibaba.com/g/12v-5.5ah-solar-lifepo4-battery.html
Системная комплектация | HSG-3D | Резервный комплект корпуса, 3D-печать | 0 | 0 | $0.00 | $0.00 | $0.00 | 0 ₽ | 0 ₽ | 0 ₽ | Инженерная оценка КНР | https://www.alibaba.com/
Системная комплектация | HSG-IM | Пакет исходных данных/DFM под литьё под давлением | 0 | 0 | $0.00 | $0.00 | $0.00 | 0 ₽ | 0 ₽ | 0 ₽ | Инженерная оценка КНР | https://www.alibaba.com/
Системная комплектация | HSG-VC | Комплект корпуса, вакуумное литьё полиуретана | 1 | 20 | $35.00 | $35.00 | $700.00 | 2977.6495 ₽ | 2977.6495 ₽ | 59552.99 ₽ | Рыночный диапазон КНР / инженерная оценка | https://www.alibaba.com/countrysearch/CN/vacuum-casting.html
Системная комплектация | MPPT1 | Внешний MPPT-контроллер LiFePO4, 10 А | 1 | 20 | $20.00 | $20.00 | $400.00 | 1701.514 ₽ | 1701.514 ₽ | 34030.28 ₽ | Рыночный диапазон КНР / инженерная оценка | https://www.alibaba.com/wholesale/solar-regulator-mppt-10.html
Системная комплектация | PV1 | Солнечная панель наружного исполнения 60–80 Вт | 1 | 20 | $12.50 | $12.50 | $250.00 | 1063.44625 ₽ | 1063.44625 ₽ | 21268.925 ₽ | Рыночный диапазон КНР / инженерная оценка | https://www.alibaba.com/wholesale/monocrystalline-panel-solar-80w.html
ИТОГО |  |  |  |  |  | $330.18 | $6603.60 |  | 28090.29463 ₽ | 561805.8925 ₽

Sheet: Сводка
ДИОНЕЯ — инженерный BOM для первичного представления заказчику
EVT-PRE-20 / Rev.A · предварительный инженерный состав изделия · НЕ производственный release
 |  |  |  |  |  |  |  | Сводный статус | Кол-во
Параметр | Значение |  | Строк BOM | PCB-MAIN | PCB-PWR | PCB-MIC | SYSTEM | Выбран / верификация | 18
Источник | ветка evt-pre-20, только чтение |  | 49 | 22 | 12 | 5 | 10 | RFQ / выбор поставщика | 14
Commit snapshot | c678a728501bea75f170d9b8989cfbf8b3112b77 |  |  |  |  |  |  | Открытая позиция | 10
Исходный BOM | hardware/EVT_PRE_20_BOM_DRAFT.csv |  | Станция | PCB-MAIN | PCB-PWR | PCB-MIC | Пилот | Кандидат / уточнение | 5
Статус | ENGINEERING / PRELIMINARY |  | 1 комплект | 1 | 1 | 4 | 20 станций | Исходные данные / DFM | 2
Производственный BOM | BLOCKED до закрытия QG-2 / финализации проекта
Назначение файла: показать заказчику инженерный состав EVT-PRE-20 до завершения производственного BOM. Позиции TBD / OPEN / RFQ сохранены как есть и не заменены предположениями. Цены не выдумывались: в листе «BOM_заказчику» оставлены поля для RFQ и автоматического расчёта суммы после ввода цены.
Ключевые зафиксированные решения
MCU | STM32U585VIT6Q | LTE | Quectel BG95-M3 | LoRa | E22-900M22S / RU868 | BLE | MDBT50Q-P1MV2
GNSS | MAX-M10S-00B | Микрофоны | 4 × T5838 | Память | W25Q512JVFIQ + microSD | Корпус | вакуумное литьё
Питание | LiFePO4 + solar + MPPT | Телеметрия | INA226 по I²C | MAIN-PWR | 12-pin Micro-Fit | Пилот | 20 станций
Примечание | Точные MPN для открытых позиций уточняются производственным BOM
Источники | URL
BOM draft | https://github.com/skif-ops/rs-zs-bpla/blob/evt-pre-20/hardware/EVT_PRE_20_BOM_DRAFT.csv
BOM policy Rev.A | https://github.com/skif-ops/rs-zs-bpla/blob/evt-pre-20/hardware/EVT_PRE_20_BOM_POLICY_REV_A.md
Commit snapshot | https://github.com/skif-ops/rs-zs-bpla/commit/c678a728501bea75f170d9b8989cfbf8b3112b77
Обновление v0.2: добавлены плановые цены закупки из КНР и лист «Сводная_стоимость». Для представления заказчику производство всех плат сведено в одну статью, кабели и разъёмы — в одну статью. Финальный производственный BOM по-прежнему не заменён этим документом.

Sheet: BOM_заказчику
ДИОНЕЯ · Инженерный BOM EVT-PRE-20 · представление заказчику
Снимок ветки evt-pre-20 @ c678a728501b · инженерный документ · цены заполняются после RFQ
№ | Узел | Категория | Item ID | RefDes | Наименование | Производитель | MPN | Корпус / исполнение | Кол-во / станцию | Кол-во 20 | Запас | К закупке | Сводный статус | Техн. статус | Примечание | План. цена/ед., ₽ (КНР) | Сумма закупки с запасом, ₽ | Источник
1 | PCB-MAIN | Плата в сборе | ASM-MAIN | - | Собранная основная плата контроллера PCB-MAIN | Contract manufacturer | TBD | 4-layer PCBA | 1 | 20 | 2 | 22 | RFQ / выбор поставщика | RFQ_REQUIRED | Not released before schematic and DFM gates | 1020.9084 ₽ | 22459.9848 ₽ | https://jlcpcb.com/help/article/pcb-assembly-price
2 | PCB-MAIN | Печатная плата | PCB-MAIN | - | Печатная плата PCB-MAIN, 4 слоя | Qualified PCB fab | TBD | 4-layer FR-4 | 1 | 20 | 5 | 25 | RFQ / выбор поставщика | RFQ_REQUIRED | Final outline pending mechanics | 425.3785 ₽ | 10634.4625 ₽ | https://jlcpcb.com/help/article/pcb-assembly-price
3 | PCB-MAIN | МК | U1 | U1 | Микроконтроллер STM32U585, защищённая low-power платформа | STMicroelectronics | STM32U585VIT6Q | LQFP100 14x14 mm | 1 | 20 | 5 | 25 | Выбран / верификация | SELECTED_PENDING_SAMPLE | Active official product | 1229.343865 ₽ | 30733.59662 ₽ | https://www.lcsc.com/product-detail/C5270986.html
4 | PCB-MAIN | Память | U2 | U2 | QSPI NOR Flash 64 МБ | Winbond | W25Q512JVFIQ | SOIC-16 300 mil | 1 | 20 | 5 | 25 | Выбран / верификация | SELECTED_PENDING_SAMPLE | Alternate MT25QL512 only after firmware and footprint review | 745.263132 ₽ | 18631.5783 ₽ | https://www.lcsc.com/product-image/C2962011.html
5 | PCB-MAIN | Датчик движения | U3 | U3 | Малопотребляющий акселерометр | STMicroelectronics | LIS2DW12TR | LGA-12 | 1 | 20 | 5 | 25 | Выбран / верификация | SELECTED_PENDING_SAMPLE | Exact mounting orientation in assembly drawing | 77.418887 ₽ | 1935.472175 ₽ | https://www.lcsc.com/product-detail/Motion-Sensors-Accelerometers_STMicroelectronics_C189624.html
6 | PCB-MAIN | Температура | U4 | U4 | Цифровой датчик температуры | STMicroelectronics | STTS22HTR | UDFN-6L 2x2 mm | 1 | 20 | 5 | 25 | Выбран / верификация | SELECTED_PENDING_ASSEMBLY_REVIEW | Exposed-pad assembly and thermal response to be reviewed | 130.165821 ₽ | 3254.145525 ₽ | https://www.lcsc.com/product-detail/temperature-and-humidity-sensor_stmicroelectronics-stts22htr_C2969838.html
7 | PCB-MAIN | Логика | U7 | U7 | Преобразователь логических уровней 1,8/3,3 В | TBD | TBD | TBD | 1 | 20 | 5 | 25 | Открытая позиция | OPEN_SCHEMATIC | Old TXB0104 not automatically approved | 29.776495 ₽ | 744.412375 ₽ | https://www.lcsc.com/
8 | PCB-MAIN | Сотовая связь | U8 | U8 | Сотовый модем LTE Cat-M1 / NB2 / EGPRS | Quectel | BG95-M3 | LGA 23.6x19.9 mm | 1 | 20 | 5 | 25 | Выбран / верификация | SELECTED_PENDING_OPERATOR_AND_REGION | Exact regional variant must cover pilot operator bands | 793.756281 ₽ | 19843.90703 ₽ | https://www.alibaba.com/showroom/bg95-m3-module.html
9 | PCB-MAIN | SIM | J-SIM1 | J6 | Разъём Nano-SIM, канал SIM1 | TBD | TBD | SMD | 1 | 20 | 5 | 25 | Открытая позиция | OPEN_MECHANICAL | Under service cover with independent SIM1_DET | 21.268925 ₽ | 531.723125 ₽ | https://www.lcsc.com/
10 | PCB-MAIN | SIM | J-SIM2 | J7 | Разъём Nano-SIM, канал SIM2 | TBD | TBD | SMD | 1 | 20 | 5 | 25 | Открытая позиция | OPEN_MECHANICAL | Under service cover with independent SIM2_DET | 21.268925 ₽ | 531.723125 ₽ | https://www.lcsc.com/
11 | PCB-MAIN | SIM | U13 | U13 | Коммутатор интерфейса двух SIM-карт | Texas Instruments | TS3A27518EPWR | TSSOP-24 | 1 | 20 | 5 | 25 | Кандидат / уточнение | CANDIDATE_PENDING_SCHEMATIC_SI_SAMPLE | Switch VDD RST CLK DATA; final MPN after BG95 signal integrity test | 57.851476 ₽ | 1446.2869 ₽ | https://www.lcsc.com/product-detail/Analog-Switches-Multiplexers_Texas-Instruments-TS3A27518EPWR_C443721.html
12 | PCB-MAIN | Защита | U14-U15 | U14;U15 | Малoёмкостная ESD/TVS-защита линий SIM | TBD | TBD | TBD | 2 | 40 | 10 | 50 | Открытая позиция | OPEN_SCHEMATIC | Place at SIM connectors; exact topology after review | 12.761355 ₽ | 638.06775 ₽ | https://www.lcsc.com/
13 | PCB-MAIN | GNSS | U9 | U9 | GNSS-модуль с выходом TIMEPULSE/PPS | u-blox | MAX-M10S-00B | LGA 9.7x10.1 mm | 1 | 20 | 5 | 25 | Выбран / верификация | SELECTED_PENDING_SAMPLE | Required for concurrent timing while cellular active | 901.80242 ₽ | 22545.0605 ₽ | https://www.lcsc.com/product-image/C4153167.html
14 | PCB-MAIN | LoRa | U10 | U10 | LoRa-модуль SX1262 для RU868 | Ebyte | E22-900M22S | SMD 14x20 mm | 1 | 20 | 6 | 26 | Выбран / верификация | SELECTED_PENDING_RF_REGULATORY | All 20 pilot units RU868; common hardware may support future EU868 profile | 391.34822 ₽ | 10175.05372 ₽ | https://www.alibaba.com/p/ebyte-e22-900m22s-tcxo-7km-long_62443474220.html
15 | PCB-MAIN | BLE | U11 | U11 | BLE/OTA сопроцессор nRF52840 | Raytac | MDBT50Q-P1MV2 | nRF52840 SMD module with integrated PCB antenna 10.5x15.5 mm | 1 | 20 | 5 | 25 | Выбран / верификация | SELECTED_PENDING_SAMPLE_RF | ESP32-C3 superseded; integrated antenna requires PCB edge keepout and validation inside final housing; u.FL family variant only by RF fallback decision | 583.619302 ₽ | 14590.48255 ₽ | https://www.tme.com/us/en-us/details/mdbt50q-p1mv2/iot-wifi-bluetooth-modules/raytac/
16 | PCB-MAIN | Накопитель | U12 | U12 | Промышленная microSD, 32 ГБ | TBD | TBD | microSD card | 1 | 20 | 5 | 25 | RFQ / выбор поставщика | RFQ_REQUIRED | Consumer card not accepted without endurance test | 425.3785 ₽ | 10634.4625 ₽ | https://www.alibaba.com/
17 | PCB-MAIN | Разъём | J-SD1 | J12 | Разъём microSD с детектированием карты | TBD | TBD | SMD | 1 | 20 | 5 | 25 | Открытая позиция | OPEN_MECHANICAL | Accessible only under service cover | 29.776495 ₽ | 744.412375 ₽ | https://www.lcsc.com/
18 | PCB-MAIN | Разъём | J-PWR-MAIN | J_PWR | 12-контактный межплатный разъём MAIN-PWR, сторона MAIN | Molex | 43045-1202 | Micro-Fit 3.0 right-angle THT | 1 | 20 | 5 | 25 | Выбран / верификация | SELECTED_ELECTRICAL_PENDING_MECHANICS | Electrical pinout frozen; exact board placement remains mechanical input | 212.68925 ₽ | 5317.23125 ₽ | https://www.lcsc.com/
19 | PCB-MAIN | RF-разъём | J-RF-CELL | J8 | RF-разъём сотовой антенны | Hirose or I-PEX | TBD | U.FL-compatible | 1 | 20 | 8 | 28 | Открытая позиция | OPEN_RF_LAYOUT | Freeze mating cable as one system | 42.53785 ₽ | 1191.0598 ₽ | https://www.alibaba.com/
20 | PCB-MAIN | RF-разъём | J-RF-GNSS | J9 | RF-разъём GNSS-антенны | Hirose or I-PEX | TBD | U.FL-compatible | 1 | 20 | 8 | 28 | Открытая позиция | OPEN_RF_LAYOUT | Separate antenna from cellular | 42.53785 ₽ | 1191.0598 ₽ | https://www.alibaba.com/
21 | PCB-MAIN | RF-разъём | J-RF-LORA | J10 | RF-разъём LoRa-антенны | Hirose or I-PEX | TBD | U.FL-compatible | 1 | 20 | 8 | 28 | Открытая позиция | OPEN_RF_LAYOUT | 50 ohm path and PI matching footprint | 42.53785 ₽ | 1191.0598 ₽ | https://www.alibaba.com/
22 | PCB-MAIN | Тактирование | X1 | X1 | Низкодрейфовый генератор 32,768 кГц | SiTime | SiT1552AI-JE-DCC-32.768D | QFN | 1 | 20 | 5 | 25 | Кандидат / уточнение | CANDIDATE | Exact suffix must be frozen | 95.284784 ₽ | 2382.1196 ₽ | https://www.lcsc.com/product-detail/Programmable-Oscillators_SiTime-SIT1552AI-JE-DCC-32-768D_C367054.html
23 | PCB-PWR | Защита | PWR-REV-CTL | U_REV | Контроллер защиты от переполюсовки и обратного тока | Texas Instruments | LM74700QDBVRQ1 | SOT-23-6 | 1 | 20 | 5 | 25 | Выбран / верификация | SELECTED_PENDING_SCHEMATIC_SAMPLE | Final surge and fuse coordination still required | 1131.50681 ₽ | 28287.67025 ₽ | https://www.lcsc.com/product-image/C2941042.html
24 | PCB-PWR | Защита | PWR-REV-FET | Q_REV | Силовой N-MOSFET 60 В, низкое Rds(on) | Texas Instruments | CSD18540Q5B | VSON-CLIP 5x6 mm | 1 | 20 | 5 | 25 | Выбран / верификация | SELECTED_TECHNICALLY_PROCUREMENT_CHECK | SOA and gate transient review required | 127.61355 ₽ | 3190.33875 ₽ | https://lcsc.com/product-detail/MOSFET_Texas-Instruments-CSD18540Q5B_C86513.html
25 | PCB-PWR | Питание | U-PWR1 | U1 | DC/DC 3,8 В / 4 А для сотового модема | Texas Instruments | LMR604403SRAKR | RAK-9 | 1 | 20 | 5 | 25 | Выбран / верификация | SELECTED_PENDING_DESIGN_CALC_SAMPLE | 4 A rail; exact L C and feedback BOM freeze pending | 224.599848 ₽ | 5614.9962 ₽ | https://www.lcsc.com/product-detail/C43351623.html
26 | PCB-PWR | Питание | U-PWR2 | U2 | DC/DC 3,3 В / 4 А цифрового питания | Texas Instruments | LMR604403SRAKR | RAK-9 | 1 | 20 | 5 | 25 | Выбран / верификация | SELECTED_PENDING_DESIGN_CALC_SAMPLE | 4 A rail; exact L C BOM freeze pending | 224.599848 ₽ | 5614.9962 ₽ | https://www.lcsc.com/product-detail/C43351623.html
27 | PCB-PWR | Питание | U-PWR3 | U3 | Малошумящий LDO 1,8 В микрофонного тракта | Texas Instruments | TPS7A2018PDBVR | SOT-23-5 | 1 | 20 | 5 | 25 | Выбран / верификация | SELECTED_PENDING_NOISE_SAMPLE | Remains powered during T5838 AAD monitoring | 17.865897 ₽ | 446.647425 ₽ | https://www.lcsc.com/product-detail/Voltage-Regulators-Linear-Low-Drop-Out-LDO-Regulators_Texas-Instruments-TPS7A2018PDBVR_C963430.html
28 | PCB-PWR | Телеметрия | U-MON-01 | U4 | Монитор тока, напряжения и мощности батареи INA226 | Texas Instruments | INA226AIDGSR | VSSOP-10 | 1 | 20 | 5 | 25 | Выбран / верификация | SELECTED_REV_A_12PIN_I2C | Address 0x40 on I2C2 pins 11/12 of MAIN-PWR; ALERT may feed FAULT but does not replace I2C | 51.896177 ₽ | 1297.404425 ₽ | https://www.lcsc.com/product-detail/C49851.html
29 | PCB-PWR | Измерение | R-SHUNT-01 | R_SHUNT | Шунт 10 мОм, 4-выводный Kelvin | TBD | TBD | 4-terminal >=1 W | 1 | 20 | 10 | 30 | Кандидат / уточнение | TOPOLOGY_SELECTED_EXACT_MPN_PENDING | 10 mOhm capture value; exact low-TCR MPN is a Review A blocker | 42.53785 ₽ | 1276.1355 ₽ | https://www.lcsc.com/
30 | PCB-PWR | Разъём | J-PWR-PWR | J_MAIN_PWR | 12-контактный межплатный разъём MAIN-PWR, сторона PWR | Molex | 43045-1202 | Micro-Fit 3.0 right-angle THT | 1 | 20 | 5 | 25 | Выбран / верификация | SELECTED_ELECTRICAL_PENDING_MECHANICS | Electrical pinout frozen; pins 11/12 carry I2C2 to INA226 | 212.68925 ₽ | 5317.23125 ₽ | https://www.lcsc.com/
31 | PCB-PWR | Защита | PWR-TVS-01 | D_TVS | TVS-защита силовой шины | Littelfuse | SMBJ18A | SMB | 1 | 20 | 5 | 25 | Кандидат / уточнение | CANDIDATE_PENDING_SURGE_PROFILE | Do not release value until measured transient envelope and fuse coordination | 8.50757 ₽ | 212.68925 ₽ | https://www.lcsc.com/
32 | PCB-PWR | Защита | PWR-FUSE-01 | F1 | Предохранитель входной цепи PCB-PWR | Littelfuse | 0451005.MRL | Nano2 451 | 1 | 20 | 10 | 30 | Кандидат / уточнение | CANDIDATE_PENDING_FUSE_COORDINATION | 5 A candidate; battery-side primary fuse remains separate | 21.268925 ₽ | 638.06775 ₽ | https://www.lcsc.com/
33 | PCB-PWR | Плата в сборе | ASM-PWR | - | Собранная плата питания и защиты PCB-PWR | Contract manufacturer | TBD | 2-layer 2 oz candidate | 1 | 20 | 2 | 22 | RFQ / выбор поставщика | RFQ_REQUIRED | No MPPT function on this board | 680.6056 ₽ | 14973.3232 ₽ | https://jlcpcb.com/help/article/pcb-assembly-price
34 | PCB-PWR | Печатная плата | PCB-PWR | - | Печатная плата PCB-PWR, 2 слоя, повышенная медь | Qualified PCB fab | TBD | 2-layer 2 oz candidate | 1 | 20 | 5 | 25 | RFQ / выбор поставщика | RFQ_REQUIRED | Final copper weight by current calculation | 255.2271 ₽ | 6380.6775 ₽ | https://jlcpcb.com/help/article/pcb-assembly-price
35 | PCB-MIC | Плата в сборе | ASM-MIC | - | Собранная микрофонная плата PCB-MIC | Contract manufacturer | TBD | 2-layer PCBA | 4 | 80 | 8 | 88 | RFQ / выбор поставщика | RFQ_REQUIRED | Same PCB revision all positions | 340.3028 ₽ | 29946.6464 ₽ | https://jlcpcb.com/help/article/pcb-assembly-price
36 | PCB-MIC | Печатная плата | PCB-MIC | - | Печатная плата микрофонного лепестка PCB-MIC | Qualified PCB fab | TBD | 2-layer FR-4 | 4 | 80 | 20 | 100 | RFQ / выбор поставщика | RFQ_REQUIRED | Panelization to be approved | 127.61355 ₽ | 12761.355 ₽ | https://jlcpcb.com/help/article/pcb-assembly-price
37 | PCB-MIC | Микрофон | MK1 | MK1 | Цифровой PDM MEMS-микрофон T5838 | TDK InvenSense | MMICT5838-00-012 | LGA-CAV-5 3.5x2.65x0.98 mm | 4 | 80 | 16 | 96 | Выбран / верификация | SELECTED_PENDING_SAMPLE | Exact orderable T5838 MPN; do not mix alternate MPN within station | 133.568849 ₽ | 12822.6095 ₽ | https://www.digikey.cn/en/products/detail/tdk-invensense/MMICT5838-00-012/16903860
38 | PCB-MIC | Пассивные | C-MIC | C1;C2 | Локальные развязывающие конденсаторы микрофона | TBD | TBD | 0402 X7R | 8 | 160 | 40 | 200 | Открытая позиция | OPEN_SCHEMATIC | Final values per T5838 reference design | 1.701514 ₽ | 340.3028 ₽ | https://www.lcsc.com/
39 | PCB-MIC | Разъём | J-MIC | J1 | 6-контактный разъём микрофонного жгута Pico-Lock | Molex | 5040500691 | Pico-Lock 1.50 mm right-angle SMT | 4 | 80 | 12 | 92 | Выбран / верификация | SELECTED_PENDING_SI_MECHANICS_AAD | Pinout 1V8 GND CLK DATA WAKE AAD_CFG; 4/5-pin connectors superseded | 22.119682 ₽ | 2035.010744 ₽ | https://www.lcsc.com/product-detail/wire-to-board-connector_molex-5040500691_C563981.html
40 | SYSTEM | Аккумулятор | BAT1 | BT1 | LiFePO4 аккумулятор 12,8 В, 40–60 А·ч, BMS | TBD | TBD | Pack | 1 | 20 | 1 | 21 | RFQ / выбор поставщика | RFQ_REQUIRED | Final capacity selected after measured energy budget | 5529.9205 ₽ | 116128.3305 ₽ | https://spanish.alibaba.com/g/12v-5.5ah-solar-lifepo4-battery.html
41 | SYSTEM | Солнечная панель | PV1 | PV1 | Солнечная панель наружного исполнения 60–80 Вт | TBD | TBD | Panel | 1 | 20 | 1 | 21 | RFQ / выбор поставщика | RFQ_REQUIRED | Cold Voc must fit MPPT margin | 1063.44625 ₽ | 22332.37125 ₽ | https://www.alibaba.com/wholesale/monocrystalline-panel-solar-80w.html
42 | SYSTEM | Контроллер | MPPT1 | U-MPPT | Внешний MPPT-контроллер LiFePO4, 10 А | TBD | TBD | Sealed module | 1 | 20 | 1 | 21 | RFQ / выбор поставщика | RFQ_REQUIRED | Exact MPN only after sample and teardown review | 1701.514 ₽ | 35731.794 ₽ | https://www.alibaba.com/wholesale/solar-regulator-mppt-10.html
43 | SYSTEM | Антенна | ANT-CELL | AE1 | Наружная антенна сотовой связи с кабелем | TBD | TBD | IP-rated | 1 | 20 | 2 | 22 | RFQ / выбор поставщика | RFQ_REQUIRED | Match BG95 bands and enclosure | 595.5299 ₽ | 13101.6578 ₽ | https://www.alibaba.com/wholesale/external-antenna-outdoor.html
44 | SYSTEM | Антенна | ANT-GNSS | AE2 | Активная наружная GNSS-антенна с кабелем | TBD | TBD | IP-rated | 1 | 20 | 2 | 22 | RFQ / выбор поставщика | RFQ_REQUIRED | Separate placement from other transmitters | 255.2271 ₽ | 5614.9962 ₽ | https://www.alibaba.com/countrysearch/CN/gps-antenna-active.html
45 | SYSTEM | Антенна | ANT-LORA | AE3 | Наружная антенна LoRa 868 МГц с кабелем | TBD | TBD | IP-rated | 1 | 20 | 2 | 22 | RFQ / выбор поставщика | RFQ_REQUIRED | RU868 label and windows 864-865 plus 868.7-869.2 MHz | 1020.9084 ₽ | 22459.9848 ₽ | https://www.alibaba.com/countrysearch/CN/antenna-cables.html
46 | SYSTEM | Жгуты | HARNESS | - | Комплект маркированных кабельных жгутов станции | TBD | TBD | Assembly | 1 | 20 | 2 | 22 | Открытая позиция | OPEN_MECHANICAL_LENGTH_FREEZE | MAIN-PWR uses two 43025-1200 housings; 18 AWG 43030-0038 for pins 1-6 and 20-24 AWG 43030-0001 for pins 7-12; separate drawing required | 1413.107377 ₽ | 31088.36229 ₽ | https://www.lcsc.com/product-detail/Housings-Wire-To-Board-Wire-To-Wire_MOLEX-5040510601_C505129.html
47 | SYSTEM | Корпус | HSG-VC | HSG1 | Комплект корпуса, вакуумное литьё полиуретана | TBD | TBD | Assembly | 1 | 20 | 0 | 20 | RFQ / выбор поставщика | RFQ_REQUIRED | Primary calculation and build quantity is exactly 20 pilot housings | 2977.6495 ₽ | 59552.99 ₽ | https://www.alibaba.com/countrysearch/CN/vacuum-casting.html
48 | SYSTEM | Корпус | HSG-3D | HSG1 | Резервный комплект корпуса, 3D-печать | TBD | TBD | Assembly | 0 | 0 | 0 | 0 | Исходные данные / DFM | SOURCE_PACKAGE_REQUIRED | Conditional full-lot demand is 20 plus approved spares if vacuum casting fallback is activated | 0 ₽ | 0 ₽ | https://www.alibaba.com/
49 | SYSTEM | Корпус | HSG-IM | HSG1 | Пакет исходных данных/DFM под литьё под давлением | TBD | TBD | Source_data | 0 | 0 | 0 | 0 | Исходные данные / DFM | SOURCE_PACKAGE_REQUIRED | No tooling or physical pilot housing without separate authorization | 0 ₽ | 0 ₽ | https://www.alibaba.com/
Цены: инженерная оценка закупки из КНР для партии около 20 станций на 2026-09-09. Курс модели: 1 USD = 85.0757 RUB. Цены не являются коммерческим предложением и не включают доставку в РФ, таможенные платежи/НДС и финальную механическую сборку станции. Открытые/TBD позиции оценены по сопоставимым китайским компонентам.

Sheet: BOM_полный
EVT-PRE-20 · исходный инженерный BOM (данные ветки без смысловых изменений)
Item_ID | Assembly | RefDes | Category | Description | Manufacturer | MPN | Package | Qty_per_station | Qty_20 | Spares | Procure_qty | Variant | Status | China_source_policy | Incoming_control | Notes | Source_URL
ASM-MAIN | PCB-MAIN | - | PCBA | Assembled main controller PCB | Contract manufacturer | TBD | 4-layer PCBA | 1 | 20 | 2 | 22 | COMMON | RFQ_REQUIRED | Direct CM quotation | AOI plus X-ray where hidden joints plus functional test | Not released before schematic and DFM gates | https://github.com/skif-ops/rs-zs-bpla/blob/evt-pre-20/hardware/EVT_PRE_20_BOM_DRAFT.csv
PCB-MAIN | PCB-MAIN | - | Bare PCB | Main controller bare PCB | Qualified PCB fab | TBD | 4-layer FR-4 | 1 | 20 | 5 | 25 | COMMON | RFQ_REQUIRED | Two independent fab quotations | Coupon dimensions finish impedance and netlist test | Final outline pending mechanics | https://github.com/skif-ops/rs-zs-bpla/blob/evt-pre-20/hardware/EVT_PRE_20_BOM_DRAFT.csv
U1 | PCB-MAIN | U1 | MCU | Ultra-low-power secure MCU | STMicroelectronics | STM32U585VIT6Q | LQFP100 14x14 mm | 1 | 20 | 5 | 25 | COMMON | SELECTED_PENDING_SAMPLE | Authorized distributor or traceable tier-1 China channel | Label lot date code package X-ray sample ID readout | Active official product | https://github.com/skif-ops/rs-zs-bpla/blob/evt-pre-20/hardware/EVT_PRE_20_BOM_DRAFT.csv
U2 | PCB-MAIN | U2 | Memory | 512 Mbit 64 MB QSPI NOR | Winbond | W25Q512JVFIQ | SOIC-16 300 mil | 1 | 20 | 5 | 25 | COMMON | SELECTED_PENDING_SAMPLE | Authorized or traceable LCSC-class channel | Marking electrical ID read/write/erase soak | Alternate MT25QL512 only after firmware and footprint review | https://github.com/skif-ops/rs-zs-bpla/blob/evt-pre-20/hardware/EVT_PRE_20_BOM_DRAFT.csv
U3 | PCB-MAIN | U3 | Motion | Low-power accelerometer | STMicroelectronics | LIS2DW12TR | LGA-12 | 1 | 20 | 5 | 25 | COMMON | SELECTED_PENDING_SAMPLE | Authorized distributor | Marking orientation WHO_AM_I and self-test | Exact mounting orientation in assembly drawing | https://github.com/skif-ops/rs-zs-bpla/blob/evt-pre-20/hardware/EVT_PRE_20_BOM_DRAFT.csv
U4 | PCB-MAIN | U4 | Temperature | Digital temperature sensor | STMicroelectronics | STTS22HTR | UDFN-6L 2x2 mm | 1 | 20 | 5 | 25 | COMMON | SELECTED_PENDING_ASSEMBLY_REVIEW | Authorized distributor | X-ray sample ID and temperature compare | Exposed-pad assembly and thermal response to be reviewed | https://github.com/skif-ops/rs-zs-bpla/blob/evt-pre-20/hardware/EVT_PRE_20_BOM_DRAFT.csv
U7 | PCB-MAIN | U7 | Level translator | Directional 1.8V to 3.3V translator | TBD | TBD | TBD | 1 | 20 | 5 | 25 | COMMON | OPEN_SCHEMATIC | Do not substitute auto-direction device without review | Logic levels direction leakage sleep test | Old TXB0104 not automatically approved | https://github.com/skif-ops/rs-zs-bpla/blob/evt-pre-20/hardware/EVT_PRE_20_BOM_DRAFT.csv
U8 | PCB-MAIN | U8 | Cellular | LPWA modem Cat M1 NB2 EGPRS | Quectel | BG95-M3 | LGA 23.6x19.9 mm | 1 | 20 | 5 | 25 | COMMON | SELECTED_PENDING_OPERATOR_AND_REGION | Quectel authorized channel or CM with traceability | IMEI label firmware RF conducted attach TLS | Exact regional variant must cover pilot operator bands | https://github.com/skif-ops/rs-zs-bpla/blob/evt-pre-20/hardware/EVT_PRE_20_BOM_DRAFT.csv
J-SIM1 | PCB-MAIN | J6 | SIM | Nano-SIM push-push connector slot 1 | TBD | TBD | SMD | 1 | 20 | 5 | 25 | COMMON | OPEN_MECHANICAL | Approved connector vendor | Mating cycles card detect coplanarity and ESD | Under service cover with independent SIM1_DET | https://github.com/skif-ops/rs-zs-bpla/blob/evt-pre-20/hardware/EVT_PRE_20_BOM_DRAFT.csv
J-SIM2 | PCB-MAIN | J7 | SIM | Nano-SIM push-push connector slot 2 | TBD | TBD | SMD | 1 | 20 | 5 | 25 | COMMON | OPEN_MECHANICAL | Approved connector vendor | Mating cycles card detect coplanarity and ESD | Under service cover with independent SIM2_DET | https://github.com/skif-ops/rs-zs-bpla/blob/evt-pre-20/hardware/EVT_PRE_20_BOM_DRAFT.csv
U13 | PCB-MAIN | U13 | SIM switch | 6-channel bidirectional 2 to 1 multiplexer | Texas Instruments | TS3A27518EPWR | TSSOP-24 | 1 | 20 | 5 | 25 | COMMON | CANDIDATE_PENDING_SCHEMATIC_SI_SAMPLE | Authorized distributor or traceable tier-1 channel | Marking supply leakage Ron capacitance and 100 switch cycles | Switch VDD RST CLK DATA; final MPN after BG95 signal integrity test | https://github.com/skif-ops/rs-zs-bpla/blob/evt-pre-20/hardware/EVT_PRE_20_BOM_DRAFT.csv
U14-U15 | PCB-MAIN | U14;U15 | ESD | Low-capacitance TVS array for each SIM connector | TBD | TBD | TBD | 2 | 40 | 10 | 50 | COMMON | OPEN_SCHEMATIC | Authorized distributor | Capacitance leakage ESD rating marking | Place at SIM connectors; exact topology after review | https://github.com/skif-ops/rs-zs-bpla/blob/evt-pre-20/hardware/EVT_PRE_20_BOM_DRAFT.csv
U9 | PCB-MAIN | U9 | GNSS | Independent GNSS with TIMEPULSE | u-blox | MAX-M10S-00B | LGA 9.7x10.1 mm | 1 | 20 | 5 | 25 | COMMON | SELECTED_PENDING_SAMPLE | Authorized distributor or traceable module channel | Marking firmware satellite fix PPS test | Required for concurrent timing while cellular active | https://github.com/skif-ops/rs-zs-bpla/blob/evt-pre-20/hardware/EVT_PRE_20_BOM_DRAFT.csv
U10 | PCB-MAIN | U10 | LoRa | 850-930 MHz SX1262 UART/SPI module | Ebyte | E22-900M22S | SMD 14x20 mm | 1 | 20 | 6 | 26 | RU868_PILOT | SELECTED_PENDING_RF_REGULATORY | Ebyte official store or authorized distributor | Marking firmware conducted power sensitivity sleep current | All 20 pilot units RU868; common hardware may support future EU868 profile | https://github.com/skif-ops/rs-zs-bpla/blob/evt-pre-20/hardware/EVT_PRE_20_BOM_DRAFT.csv
U11 | PCB-MAIN | U11 | BLE | BLE commissioning diagnostics and signed OTA coprocessor | Raytac | MDBT50Q-P1MV2 | nRF52840 SMD module with integrated PCB antenna 10.5x15.5 mm | 1 | 20 | 5 | 25 | COMMON | SELECTED_PENDING_SAMPLE_RF | Raytac authorized channel or traceable distributor | Module label firmware BLE 2M coded PHY pairing OTA current RF range and temperature test | ESP32-C3 superseded; integrated antenna requires PCB edge keepout and validation inside final housing; u.FL family variant only by RF fallback decision | https://github.com/skif-ops/rs-zs-bpla/blob/evt-pre-20/hardware/EVT_PRE_20_BOM_DRAFT.csv
U12 | PCB-MAIN | U12 | Storage | Industrial microSD 32 GB | TBD | TBD | microSD card | 1 | 20 | 5 | 25 | COMMON | RFQ_REQUIRED | Industrial NAND vendor authorized channel | CID capacity full write/read temperature and power-loss sample | Consumer card not accepted without endurance test | https://github.com/skif-ops/rs-zs-bpla/blob/evt-pre-20/hardware/EVT_PRE_20_BOM_DRAFT.csv
J-SD1 | PCB-MAIN | J12 | Connector | microSD connector with detect | TBD | TBD | SMD | 1 | 20 | 5 | 25 | COMMON | OPEN_MECHANICAL | Approved connector vendor | Mating detect coplanarity | Accessible only under service cover | https://github.com/skif-ops/rs-zs-bpla/blob/evt-pre-20/hardware/EVT_PRE_20_BOM_DRAFT.csv
J-PWR-MAIN | PCB-MAIN | J_PWR | Connector | 12-position MAIN-PWR board header | Molex | 43045-1202 | Micro-Fit 3.0 right-angle THT | 1 | 20 | 5 | 25 | COMMON | SELECTED_ELECTRICAL_PENDING_MECHANICS | Authorized Molex distributor | Marking dimensions latch mate continuity | Electrical pinout frozen; exact board placement remains mechanical input | https://github.com/skif-ops/rs-zs-bpla/blob/evt-pre-20/hardware/EVT_PRE_20_BOM_DRAFT.csv
J-RF-CELL | PCB-MAIN | J8 | RF connector | Cellular RF connector | Hirose or I-PEX | TBD | U.FL-compatible | 1 | 20 | 8 | 28 | COMMON | OPEN_RF_LAYOUT | Authorized connector vendor | Visual mate gauge continuity | Freeze mating cable as one system | https://github.com/skif-ops/rs-zs-bpla/blob/evt-pre-20/hardware/EVT_PRE_20_BOM_DRAFT.csv
J-RF-GNSS | PCB-MAIN | J9 | RF connector | GNSS RF connector | Hirose or I-PEX | TBD | U.FL-compatible | 1 | 20 | 8 | 28 | COMMON | OPEN_RF_LAYOUT | Authorized connector vendor | Visual mate gauge continuity | Separate antenna from cellular | https://github.com/skif-ops/rs-zs-bpla/blob/evt-pre-20/hardware/EVT_PRE_20_BOM_DRAFT.csv
J-RF-LORA | PCB-MAIN | J10 | RF connector | LoRa RF connector | Hirose or I-PEX | TBD | U.FL-compatible | 1 | 20 | 8 | 28 | RU868_PILOT | OPEN_RF_LAYOUT | Authorized connector vendor | Visual mate gauge continuity | 50 ohm path and PI matching footprint | https://github.com/skif-ops/rs-zs-bpla/blob/evt-pre-20/hardware/EVT_PRE_20_BOM_DRAFT.csv
X1 | PCB-MAIN | X1 | Clock | 32.768 kHz low drift oscillator | SiTime | SiT1552AI-JE-DCC-32.768D | QFN | 1 | 20 | 5 | 25 | COMMON | CANDIDATE | Authorized distributor | Frequency and current sample test | Exact suffix must be frozen | https://github.com/skif-ops/rs-zs-bpla/blob/evt-pre-20/hardware/EVT_PRE_20_BOM_DRAFT.csv
PWR-REV-CTL | PCB-PWR | U_REV | Protection | Reverse polarity and reverse current controller | Texas Instruments | LM74700QDBVRQ1 | SOT-23-6 | 1 | 20 | 5 | 25 | COMMON | SELECTED_PENDING_SCHEMATIC_SAMPLE | Authorized distributor | Marking reverse test and gate waveform | Final surge and fuse coordination still required | https://github.com/skif-ops/rs-zs-bpla/blob/evt-pre-20/hardware/EVT_PRE_20_BOM_DRAFT.csv
PWR-REV-FET | PCB-PWR | Q_REV | Protection | 60 V low-Rds(on) N-MOSFET | Texas Instruments | CSD18540Q5B | VSON-CLIP 5x6 mm | 1 | 20 | 5 | 25 | COMMON | SELECTED_TECHNICALLY_PROCUREMENT_CHECK | Authorized distributor | Marking Rds thermal and reverse fault test | SOA and gate transient review required | https://github.com/skif-ops/rs-zs-bpla/blob/evt-pre-20/hardware/EVT_PRE_20_BOM_DRAFT.csv
U-PWR1 | PCB-PWR | U1 | Power | 3.8 V modem synchronous buck | Texas Instruments | LMR604403SRAKR | RAK-9 | 1 | 20 | 5 | 25 | COMMON | SELECTED_PENDING_DESIGN_CALC_SAMPLE | Authorized distributor | Load step ripple efficiency thermal and EMI | 4 A rail; exact L C and feedback BOM freeze pending | https://github.com/skif-ops/rs-zs-bpla/blob/evt-pre-20/hardware/EVT_PRE_20_BOM_DRAFT.csv
U-PWR2 | PCB-PWR | U2 | Power | 3.3 V digital synchronous buck | Texas Instruments | LMR604403SRAKR | RAK-9 | 1 | 20 | 5 | 25 | COMMON | SELECTED_PENDING_DESIGN_CALC_SAMPLE | Authorized distributor | Load step ripple efficiency sleep current thermal and EMI | 4 A rail; exact L C BOM freeze pending | https://github.com/skif-ops/rs-zs-bpla/blob/evt-pre-20/hardware/EVT_PRE_20_BOM_DRAFT.csv
U-PWR3 | PCB-PWR | U3 | Power | 1.8 V low-noise microphone LDO | Texas Instruments | TPS7A2018PDBVR | SOT-23-5 | 1 | 20 | 5 | 25 | COMMON | SELECTED_PENDING_NOISE_SAMPLE | Authorized distributor | Noise PSRR dropout thermal and AAD sleep current | Remains powered during T5838 AAD monitoring | https://github.com/skif-ops/rs-zs-bpla/blob/evt-pre-20/hardware/EVT_PRE_20_BOM_DRAFT.csv
U-MON-01 | PCB-PWR | U4 | Monitor | Total battery current voltage and power monitor | Texas Instruments | INA226AIDGSR | VSSOP-10 | 1 | 20 | 5 | 25 | COMMON | SELECTED_REV_A_12PIN_I2C | Authorized distributor | Marking I2C ID calibration and reference-meter compare | Address 0x40 on I2C2 pins 11/12 of MAIN-PWR; ALERT may feed FAULT but does not replace I2C | https://github.com/skif-ops/rs-zs-bpla/blob/evt-pre-20/hardware/EVT_PRE_20_BOM_DRAFT.csv
R-SHUNT-01 | PCB-PWR | R_SHUNT | Shunt | 10 mOhm 4-terminal Kelvin current shunt | TBD | TBD | 4-terminal >=1 W | 1 | 20 | 10 | 30 | COMMON | TOPOLOGY_SELECTED_EXACT_MPN_PENDING | Authorized current-sense resistor vendor | Resistance TCR marking and four-wire reference measurement | 10 mOhm capture value; exact low-TCR MPN is a Review A blocker | https://github.com/skif-ops/rs-zs-bpla/blob/evt-pre-20/hardware/EVT_PRE_20_BOM_DRAFT.csv
J-PWR-PWR | PCB-PWR | J_MAIN_PWR | Connector | 12-position MAIN-PWR board header | Molex | 43045-1202 | Micro-Fit 3.0 right-angle THT | 1 | 20 | 5 | 25 | COMMON | SELECTED_ELECTRICAL_PENDING_MECHANICS | Authorized Molex distributor | Marking dimensions latch mate continuity | Electrical pinout frozen; pins 11/12 carry I2C2 to INA226 | https://github.com/skif-ops/rs-zs-bpla/blob/evt-pre-20/hardware/EVT_PRE_20_BOM_DRAFT.csv
PWR-TVS-01 | PCB-PWR | D_TVS | Protection | Protected-bus transient clamp candidate | Littelfuse | SMBJ18A | SMB | 1 | 20 | 5 | 25 | COMMON | CANDIDATE_PENDING_SURGE_PROFILE | Authorized distributor | Marking clamp pulse and thermal sample | Do not release value until measured transient envelope and fuse coordination | https://github.com/skif-ops/rs-zs-bpla/blob/evt-pre-20/hardware/EVT_PRE_20_BOM_DRAFT.csv
PWR-FUSE-01 | PCB-PWR | F1 | Protection | PCB input fuse candidate | Littelfuse | 0451005.MRL | Nano2 451 | 1 | 20 | 10 | 30 | COMMON | CANDIDATE_PENDING_FUSE_COORDINATION | Authorized distributor | Marking continuity and controlled fault clearing | 5 A candidate; battery-side primary fuse remains separate | https://github.com/skif-ops/rs-zs-bpla/blob/evt-pre-20/hardware/EVT_PRE_20_BOM_DRAFT.csv
ASM-PWR | PCB-PWR | - | PCBA | Assembled protected power interface PCB | Contract manufacturer | TBD | 2-layer 2 oz candidate | 1 | 20 | 2 | 22 | COMMON | RFQ_REQUIRED | Direct CM quotation | AOI functional high-current thermal | No MPPT function on this board | https://github.com/skif-ops/rs-zs-bpla/blob/evt-pre-20/hardware/EVT_PRE_20_BOM_DRAFT.csv
PCB-PWR | PCB-PWR | - | Bare PCB | Power interface bare PCB | Qualified PCB fab | TBD | 2-layer 2 oz candidate | 1 | 20 | 5 | 25 | COMMON | RFQ_REQUIRED | Two independent fab quotations | Copper thickness netlist high-current and Kelvin review | Final copper weight by current calculation | https://github.com/skif-ops/rs-zs-bpla/blob/evt-pre-20/hardware/EVT_PRE_20_BOM_DRAFT.csv
ASM-MIC | PCB-MIC | - | PCBA | Assembled identical microphone leaf PCB | Contract manufacturer | TBD | 2-layer PCBA | 4 | 80 | 8 | 88 | COMMON | RFQ_REQUIRED | Direct CM quotation | AOI acoustic port inspection channel functional test | Same PCB revision all positions | https://github.com/skif-ops/rs-zs-bpla/blob/evt-pre-20/hardware/EVT_PRE_20_BOM_DRAFT.csv
PCB-MIC | PCB-MIC | - | Bare PCB | Microphone leaf bare PCB | Qualified PCB fab | TBD | 2-layer FR-4 | 4 | 80 | 20 | 100 | COMMON | RFQ_REQUIRED | Two independent fab quotations | Outline hole position finish netlist | Panelization to be approved | https://github.com/skif-ops/rs-zs-bpla/blob/evt-pre-20/hardware/EVT_PRE_20_BOM_DRAFT.csv
MK1 | PCB-MIC | MK1 | Microphone | Digital bottom-port PDM MEMS microphone | TDK InvenSense | MMICT5838-00-012 | LGA-CAV-5 3.5x2.65x0.98 mm | 4 | 80 | 16 | 96 | COMMON | SELECTED_PENDING_SAMPLE | TDK authorized channel and same lot requested | Marking lot acoustic sensitivity noise phase and port inspection | Exact orderable T5838 MPN; do not mix alternate MPN within station | https://github.com/skif-ops/rs-zs-bpla/blob/evt-pre-20/hardware/EVT_PRE_20_BOM_DRAFT.csv
C-MIC | PCB-MIC | C1;C2 | Passive | Local microphone decoupling capacitors | TBD | TBD | 0402 X7R | 8 | 160 | 40 | 200 | COMMON | OPEN_SCHEMATIC | Traceable passive vendor | Value package reel label capacitance sample | Final values per T5838 reference design | https://github.com/skif-ops/rs-zs-bpla/blob/evt-pre-20/hardware/EVT_PRE_20_BOM_DRAFT.csv
J-MIC | PCB-MIC | J1 | Connector | 6-position positive-lock microphone harness connector | Molex | 5040500691 | Pico-Lock 1.50 mm right-angle SMT | 4 | 80 | 12 | 92 | COMMON | SELECTED_PENDING_SI_MECHANICS_AAD | Authorized Molex distributor | Mating pull test contact resistance continuity and temperature | Pinout 1V8 GND CLK DATA WAKE AAD_CFG; 4/5-pin connectors superseded | https://github.com/skif-ops/rs-zs-bpla/blob/evt-pre-20/hardware/EVT_PRE_20_BOM_DRAFT.csv
BAT1 | SYSTEM | BT1 | Battery | 12.8 V 40-60 Ah LiFePO4 with BMS | TBD | TBD | Pack | 1 | 20 | 1 | 21 | COMMON | RFQ_REQUIRED | Cell maker traceability UN38.3 MSDS and China export capability | Capacity DCIR BMS thresholds low-temp charge inhibit | Final capacity selected after measured energy budget | https://github.com/skif-ops/rs-zs-bpla/blob/evt-pre-20/hardware/EVT_PRE_20_BOM_DRAFT.csv
PV1 | SYSTEM | PV1 | Solar panel | 60-80 W outdoor solar panel | TBD | TBD | Panel | 1 | 20 | 1 | 21 | COMMON | RFQ_REQUIRED | Factory datasheet IEC evidence and sample | Voc Isc Pmax insulation wet leakage dimensions | Cold Voc must fit MPPT margin | https://github.com/skif-ops/rs-zs-bpla/blob/evt-pre-20/hardware/EVT_PRE_20_BOM_DRAFT.csv
MPPT1 | SYSTEM | U-MPPT | Controller | External 10 A LiFePO4 MPPT controller | TBD | TBD | Sealed module | 1 | 20 | 1 | 21 | COMMON | RFQ_REQUIRED | Manufacturer not marketplace relabel only | Charge profile reverse current quiescent thermal low-temp inhibit | Exact MPN only after sample and teardown review | https://github.com/skif-ops/rs-zs-bpla/blob/evt-pre-20/hardware/EVT_PRE_20_BOM_DRAFT.csv
ANT-CELL | SYSTEM | AE1 | Antenna | Outdoor cellular antenna with cable | TBD | TBD | IP-rated | 1 | 20 | 2 | 22 | COMMON | RFQ_REQUIRED | Antenna manufacturer with reports | VSWR cable loss connector environmental | Match BG95 bands and enclosure | https://github.com/skif-ops/rs-zs-bpla/blob/evt-pre-20/hardware/EVT_PRE_20_BOM_DRAFT.csv
ANT-GNSS | SYSTEM | AE2 | Antenna | Active GNSS antenna with cable | TBD | TBD | IP-rated | 1 | 20 | 2 | 22 | COMMON | RFQ_REQUIRED | Antenna manufacturer with reports | Gain current VSWR fix PPS environmental | Separate placement from other transmitters | https://github.com/skif-ops/rs-zs-bpla/blob/evt-pre-20/hardware/EVT_PRE_20_BOM_DRAFT.csv
ANT-LORA | SYSTEM | AE3 | Antenna | 868 MHz outdoor antenna with cable | TBD | TBD | IP-rated | 1 | 20 | 2 | 22 | RU868_PILOT | RFQ_REQUIRED | Antenna manufacturer with reports | VSWR cable loss conducted and radiated test | RU868 label and windows 864-865 plus 868.7-869.2 MHz | https://github.com/skif-ops/rs-zs-bpla/blob/evt-pre-20/hardware/EVT_PRE_20_BOM_DRAFT.csv
HARNESS | SYSTEM | - | Harness | Complete labeled harness set | TBD | TBD | Assembly | 1 | 20 | 2 | 22 | COMMON | OPEN_MECHANICAL_LENGTH_FREEZE | Qualified harness factory | 100 percent continuity polarity pull sample | MAIN-PWR uses two 43025-1200 housings; 18 AWG 43030-0038 for pins 1-6 and 20-24 AWG 43030-0001 for pins 7-12; separate drawing required | https://github.com/skif-ops/rs-zs-bpla/blob/evt-pre-20/hardware/EVT_PRE_20_BOM_DRAFT.csv
HSG-VC | SYSTEM | HSG1 | Housing | Vacuum-cast polyurethane housing set | TBD | TBD | Assembly | 1 | 20 | 0 | 20 | VACUUM_CASTING_PRIMARY | RFQ_REQUIRED | Qualified vacuum casting manufacturer | FAI dimensions material cure finish inserts leak fit acoustic and RF checks | Primary calculation and build quantity is exactly 20 pilot housings | https://github.com/skif-ops/rs-zs-bpla/blob/evt-pre-20/hardware/EVT_PRE_20_BOM_DRAFT.csv
HSG-3D | SYSTEM | HSG1 | Housing | 3D-printed fallback housing set | TBD | TBD | Assembly | 0 | 0 | 0 | 0 | THREE_D_PRINT_FALLBACK | SOURCE_PACKAGE_REQUIRED | Qualified print supplier or controlled FlashForge 5M Pro process | Engineering sample dimensions material finish leak fit acoustic and RF checks | Conditional full-lot demand is 20 plus approved spares if vacuum casting fallback is activated | https://github.com/skif-ops/rs-zs-bpla/blob/evt-pre-20/hardware/EVT_PRE_20_BOM_DRAFT.csv
HSG-IM | SYSTEM | HSG1 | Housing | Injection-molding source package and DFM | TBD | TBD | Source_data | 0 | 0 | 0 | 0 | INJECTION_MOLDING_FUTURE | SOURCE_PACKAGE_REQUIRED | Qualified mold manufacturer for DFM quotation | Source audit wall draft ribs bosses parting ejector shrink material and tooling concept | No tooling or physical pilot housing without separate authorization | https://github.com/skif-ops/rs-zs-bpla/blob/evt-pre-20/hardware/EVT_PRE_20_BOM_DRAFT.csv

Sheet: Комплектация
ДИОНЕЯ · Комплектация одной станции EVT-PRE-20
Позиция | Подсистема | Кол-во / станцию | Кол-во на 20 | Назначение / состав | Статус
PCB-MAIN | Основной контроллер | 1 | 20 | 1 собранная плата; MCU, память, GNSS, LTE, LoRa, BLE, storage | RFQ / выбор поставщика
PCB-PWR | Питание и телеметрия | 1 | 20 | 1 собранная плата; 3.8/3.3/1.8 В, защита, INA226, шунт | RFQ / выбор поставщика
PCB-MIC | Микрофонная подсистема | 4 | 80 | 4 одинаковых микрофонных лепестка с T5838 | RFQ / выбор поставщика
BAT1 | Аккумулятор | 1 | 20 | LiFePO4 12,8 В, 40–60 А·ч с BMS | RFQ / выбор поставщика
PV1 | Солнечная панель | 1 | 20 | 60–80 Вт, наружное исполнение | RFQ / выбор поставщика
MPPT1 | MPPT | 1 | 20 | Внешний LiFePO4 MPPT, 10 А | RFQ / выбор поставщика
ANT-CELL | Антенна LTE | 1 | 20 | Наружная, согласованная с BG95 | RFQ / выбор поставщика
ANT-GNSS | Антенна GNSS | 1 | 20 | Активная наружная | RFQ / выбор поставщика
ANT-LORA | Антенна LoRa | 1 | 20 | RU868 | RFQ / выбор поставщика
HARNESS | Комплект жгутов | 1 | 20 | Маркированный комплект, длины уточняются механикой | Открытая позиция
HSG-VC | Корпус станции | 1 | 20 | Основной вариант EVT-PRE-20: вакуумное литьё | RFQ / выбор поставщика

Sheet: Кабели_разъемы
Кабели и разъёмы · количественные нормы из BOM Policy Rev.A
Инженерное дополнение к DRAFT: эти количества являются quantity authority политики BOM; производственные длины жгутов ещё финализируются.
Группа | MPN | Наименование | Кол-во / станцию | Кол-во 20 | Основание | Источник
MIC cable housing | 5040510601 | Корпус разъёма кабеля MIC | 8 | 160 | 4 MIC-кабеля: по два корпуса на кабель | https://github.com/skif-ops/rs-zs-bpla/blob/evt-pre-20/hardware/EVT_PRE_20_BOM_POLICY_REV_A.md
MIC terminals | 5040520098 | Контакты MIC-кабелей | 48 | 960 | 6 контактов × 8 корпусов | https://github.com/skif-ops/rs-zs-bpla/blob/evt-pre-20/hardware/EVT_PRE_20_BOM_POLICY_REV_A.md
MIC board headers | 5040500691 | Платные Pico-Lock разъёмы MIC | 8 | 160 | 4 PCB-MIC + 4 ответных на PCB-MAIN | https://github.com/skif-ops/rs-zs-bpla/blob/evt-pre-20/hardware/EVT_PRE_20_BOM_POLICY_REV_A.md
MAIN-PWR housing | 43025-1200 | Корпус Micro-Fit MAIN-PWR | 2 | 40 | Один кабель MAIN-PWR, два корпуса | https://github.com/skif-ops/rs-zs-bpla/blob/evt-pre-20/hardware/EVT_PRE_20_BOM_POLICY_REV_A.md
MAIN-PWR power terminal | 43030-0038 | Силовой контакт Micro-Fit, 18 AWG | 12 | 240 | Пины 1–6 на двух концах | https://github.com/skif-ops/rs-zs-bpla/blob/evt-pre-20/hardware/EVT_PRE_20_BOM_POLICY_REV_A.md
MAIN-PWR control terminal | 43030-0001 | Сигнальный/I²C контакт Micro-Fit, 20–24 AWG | 12 | 240 | Пины 7–12 на двух концах | https://github.com/skif-ops/rs-zs-bpla/blob/evt-pre-20/hardware/EVT_PRE_20_BOM_POLICY_REV_A.md

Sheet: Статусы_и_источники
Статусы, ограничения и источники инженерного BOM
Сводный статус | Что означает | Допустимость для показа заказчику
Выбран / верификация | MPN выбран, но остаётся sample/RF/mechanics/operator/design verification | Да, как инженерно выбранный
RFQ / выбор поставщика | Нужен официальный RFQ / выбор производителя или контрактного сборщика | Да, с отметкой RFQ
Открытая позиция | Схема, механика, RF layout или точный MPN ещё не закрыты | Да, только как открытая позиция
Кандидат / уточнение | Топология/компонент определены не полностью; требуется окончательная верификация | Да, как кандидат
Исходные данные / DFM | Вариант не закупается сейчас; готовится source/DFM package | Да, как перспективный/резервный
Production release | Разрешение заводу на серийную/пилотную закупку по закрытому BOM | НЕТ — текущий файл им не является
Ограничение / правило | Содержание | Источник
Статус production BOM | ACTIVE / PRODUCTION BOM BLOCKED | BOM Policy Rev.A
Архитектура станции | 1 × PCB-MAIN; 1 × PCB-PWR; 4 × PCB-MIC | BOM Policy Rev.A
Расчёт партии | Qty_20 = Qty_per_station × 20 | BOM Policy Rev.A
Закупка | Procure_qty = Qty_20 + Spares | BOM Policy Rev.A
Основной корпус пилота | Вакуумное литьё, 20 комплектов | BOM Draft
UWB | Не входит в EVT-PRE-20; связь LoRa RU868 | Проектный baseline
Изменение ветки | При подготовке этого XLSX ветка не изменялась; документ построен из snapshot commit | Этот XLSX
Источник | URL
BOM Draft | https://github.com/skif-ops/rs-zs-bpla/blob/evt-pre-20/hardware/EVT_PRE_20_BOM_DRAFT.csv
BOM Policy Rev.A | https://github.com/skif-ops/rs-zs-bpla/blob/evt-pre-20/hardware/EVT_PRE_20_BOM_POLICY_REV_A.md
BOM Evidence Rev.A | https://github.com/skif-ops/rs-zs-bpla/blob/evt-pre-20/hardware/EVT_PRE_20_BOM_EVIDENCE_REV_A.md
Snapshot commit | https://github.com/skif-ops/rs-zs-bpla/commit/c678a728501bea75f170d9b8989cfbf8b3112b77

Sheet: Сводная_стоимость
ДИОНЕЯ · Сводная инженерная стоимость аппаратной части EVT-PRE-20
Оценка закупки из КНР, партия 20 станций. Не является производственным BOM или коммерческим предложением.
Параметр | Значение | Параметр | Значение |  |  |  |  | 1 ИЗДЕЛИЕ
Дата оценки | 2026-09-09 | Курс USD/RUB | 85.0757
Партия | 20 станций | Источник цен | LCSC / Alibaba / JLCPCB + инженерные оценки |  |  |  |  | 30899.32409 ₽ | 30899.32409 ₽ | 30899.32409 ₽ | 30899.32409 ₽
Резерв логистика/курс | 10% | Статус | ENGINEERING ESTIMATE |  |  |  |  | 30899.32409 ₽ | 30899.32409 ₽ | 30899.32409 ₽ | 30899.32409 ₽
 |  |  |  |  |  |  |  | 30899.32409 ₽ | 30899.32409 ₽ | 30899.32409 ₽ | 30899.32409 ₽
Статья | Состав | Цена 1 изд., USD | Цена 1 изд., ₽ | Цена 20 изд., USD | Цена 20 изд., ₽ | Доля | Комментарий
Электронная компонентная база | MCU, память, LTE, GNSS, LoRa, BLE, питание, датчики, микрофоны, пассивы | $100.68 | 8565.421476 ₽ | $2013.60 | 171308.4295 ₽ | 30.5% | MPN-цены + резерв на ещё не замороженные R/C/L | 20 ИЗДЕЛИЙ
Производство плат | 1× PCB-MAIN + 1× PCB-PWR + 4× PCB-MIC: bare PCB, stencil/setup, SMT/THT, базовый контроль | $50.00 | 4253.785 ₽ | $1000.00 | 85075.7 ₽ | 15.1% | Сведено в одну позицию; компоненты считаются отдельно
Кабели и разъёмы | Все платные/кабельные разъёмы, RF pigtail, провода, контакты, обжим и сборка жгутов | $25.00 | 2126.8925 ₽ | $500.00 | 42537.85 ₽ | 7.6% | Сведено в одну позицию согласно замечанию | 617986.4818 ₽ | 617986.4818 ₽ | 617986.4818 ₽ | 617986.4818 ₽
Аккумулятор LiFePO4 | 12,8 В, 40–60 А·ч, BMS; расчёт принят по 50 А·ч | $65.00 | 5529.9205 ₽ | $1300.00 | 110598.41 ₽ | 19.7% | Китайский low-volume диапазон; точный SKU после energy budget | 617986.4818 ₽ | 617986.4818 ₽ | 617986.4818 ₽ | 617986.4818 ₽
Солнечная панель | 60–80 Вт, outdoor; расчёт принят по 80 Вт | $12.50 | 1063.44625 ₽ | $250.00 | 21268.925 ₽ | 3.8% | Китайский rigid mono panel | 617986.4818 ₽ | 617986.4818 ₽ | 617986.4818 ₽ | 617986.4818 ₽
MPPT-контроллер | 12/24 В, LiFePO4, около 10 А | $20.00 | 1701.514 ₽ | $400.00 | 34030.28 ₽ | 6.1% | Инженерная цена для нормального MPPT, не дешёвого PWM
Антенны LTE/GNSS/LoRa | Наружные антенны и кабели трёх радиоканалов | $22.00 | 1871.6654 ₽ | $440.00 | 37433.308 ₽ | 6.7% | Сведены в одну системную строку
Корпус, вакуумное литьё | Комплект корпуса пилотной станции, PU, low-volume | $35.00 | 2977.6495 ₽ | $700.00 | 59552.99 ₽ | 10.6% | Инженерная оценка комплекта, 20 шт.
ИТОГО прямой закупочный BOM |  | $330.18 | 28090.29463 ₽ | $6603.60 | 561805.8925 ₽
Резерв 10%: логистика КНР, консолидация, колебание цен/курса |  | $33.02 | 2809.029463 ₽ | $660.36 | 56180.58925 ₽
ПЛАНОВАЯ СУММА ДЛЯ ПЕРВИЧНОГО ПРЕДСТАВЛЕНИЯ |  | $363.20 | 30899.32409 ₽ | $7263.96 | 617986.4818 ₽
Важно: это инженерная оценка закупочного BOM для общения с заказчиком, а не цена серийного изделия и не финальный производственный BOM. Не включены НДС/таможня в РФ, международная доставка, финальная механическая сборка станции, EOL/приёмка готового изделия и возможная переработка корпуса/плат после EVT.
 |  |  |  |  |  |  |  | ПРЯМОЙ BOM БЕЗ РЕЗЕРВА
 |  |  |  |  |  |  |  | 28090.29463 ₽

Sheet: Источники_цен
Источники и допущения цен КНР
Группа | Позиция / MPN | Цена / ориентир | Количество/уровень | Дата | URL
Электроника | STM32U585VIT6Q | $14.447 | 30+ | 2026-09-09 | https://www.lcsc.com/product-detail/C5270986.html
Электроника | W25Q512JVFIQ | $8.7611 | 30+ | 2026-09-09 | https://www.lcsc.com/product-image/C2962011.html
Электроника | LIS2DW12TR | $0.9079 | 30+ | 2026-09-09 | https://www.lcsc.com/product-detail/Motion-Sensors-Accelerometers_STMicroelectronics_C189624.html
Электроника | STTS22HTR | $1.5348 | 30+ | 2026-09-09 | https://www.lcsc.com/product-detail/temperature-and-humidity-sensor_stmicroelectronics-stts22htr_C2969838.html
Электроника | TS3A27518EPWR | $0.6832 | 30+ | 2026-09-09 | https://www.lcsc.com/product-detail/Analog-Switches-Multiplexers_Texas-Instruments-TS3A27518EPWR_C443721.html
Электроника | MAX-M10S-00B | $10.5999 | 10+ | 2026-09-09 | https://www.lcsc.com/product-image/C4153167.html
Электроника | Quectel BG95-M3 | $7.78–9.33 | MOQ 10 | 2026-09-09 | https://www.alibaba.com/showroom/bg95-m3-module.html
Электроника | Ebyte E22-900M22S | $4.60 | 2–99 | 2026-09-09 | https://www.alibaba.com/p/ebyte-e22-900m22s-tcxo-7km-long_62443474220.html
Электроника | Raytac MDBT50Q-P1MV2 | $6.86 | 25+ benchmark | 2026-09-09 | https://www.tme.com/us/en-us/details/mdbt50q-p1mv2/iot-wifi-bluetooth-modules/raytac/
Электроника | SiT1552 32.768kHz | $1.1162 | 30+ | 2026-09-09 | https://www.lcsc.com/product-detail/Programmable-Oscillators_SiTime-SIT1552AI-JE-DCC-32-768D_C367054.html
Питание | LM74700QDBVRQ1 | $13.2983 | 30+ | 2026-09-09 | https://www.lcsc.com/product-image/C2941042.html
Питание | CSD18540Q5B | $1.4997 | 30+ | 2026-09-09 | https://lcsc.com/product-detail/MOSFET_Texas-Instruments-CSD18540Q5B_C86513.html
Питание | LMR604403SRAKR | $2.6367 | 30+ reference | 2026-09-09 | https://www.lcsc.com/product-detail/C43351623.html
Питание | TPS7A2018PDBVR | $0.2069 | 50+ | 2026-09-09 | https://www.lcsc.com/product-detail/Voltage-Regulators-Linear-Low-Drop-Out-LDO-Regulators_Texas-Instruments-TPS7A2018PDBVR_C963430.html
Питание | INA226AIDGSR | $0.6126 | 30+ | 2026-09-09 | https://www.lcsc.com/product-detail/C49851.html
Акустика | MMICT5838-00-012 | ≈$1.57 | 100+ benchmark | 2026-09-09 | https://www.digikey.cn/en/products/detail/tdk-invensense/MMICT5838-00-012/16903860
Кабели | Molex 5040500691 | $0.272 | 30+ | 2026-09-09 | https://www.lcsc.com/product-detail/wire-to-board-connector_molex-5040500691_C563981.html
Кабели | Molex 5040510601 | $0.1183 | 50+ | 2026-09-09 | https://www.lcsc.com/product-detail/Housings-Wire-To-Board-Wire-To-Wire_MOLEX-5040510601_C505129.html
Кабели | Molex 5040520098 | $0.061–0.067 | 100+ | 2026-09-09 | https://www.lcsc.com/product-detail/Housing-Contact_MOLEX-5040520098_C385104.html
Система | LiFePO4 12.8V 50Ah | $61–100 | China listings | 2026-09-09 | https://spanish.alibaba.com/g/12v-5.5ah-solar-lifepo4-battery.html
Система | 80W rigid solar panel | $10–15 | China listings | 2026-09-09 | https://www.alibaba.com/wholesale/monocrystalline-panel-solar-80w.html
Система | MPPT 10A LiFePO4 | ≈$20–24 | China listings | 2026-09-09 | https://www.alibaba.com/wholesale/solar-regulator-mppt-10.html
Система | LTE outdoor antenna | ≈$6.5–8 | MOQ ~10 | 2026-09-09 | https://www.alibaba.com/wholesale/external-antenna-outdoor.html
Система | GNSS active outdoor antenna | ≈$1.5–3 | China listings | 2026-09-09 | https://www.alibaba.com/countrysearch/CN/gps-antenna-active.html
Система | 868MHz outdoor antenna | ≈$10.5–15 | MOQ ~10 | 2026-09-09 | https://www.alibaba.com/countrysearch/CN/antenna-cables.html
Производство | JLCPCB PCBA | setup $8.18 + SMT/THT/PCB | engineering aggregation | 2026-09-09 | https://jlcpcb.com/help/article/pcb-assembly-price
Механика | Vacuum casting PU | $5–20/part typical listing; set estimate higher | low-volume China | 2026-09-09 | https://www.alibaba.com/countrysearch/CN/vacuum-casting.html
Курс | USD/RUB | 85.0757 | 1 USD | 2026-09-09 | currency market reference
