skif-ops/rs-zs-bpla/releases/evt-pre-20/2026-10-02-rev-d5/Основной_пакет/03_Корпуса_для_3D_печати_ПРЕДВАРИТЕЛЬНО/Верхний_электронный_модуль/Ведомость_корпуса_PCB_MAIN_Rev_B.xlsx

PCB-MAIN: фасочный корпус с логотипом Дионея
Корпус предварительный. PCB-MAIN, разъёмы и жгуты не меняются.
 |  | 20 | 40 | 41
Артикул | На 1 | На 20 | На 40 | На 41 | Тип | Наименование и статус
DIO-3DP-UP-001B_body | 1 | 20 | 40 | 41 | 3D-печать / 3D print | Корпус PCB-MAIN с фасочными углами / faceted body
DIO-3DP-UP-001B_lid | 1 | 20 | 40 | 41 | 3D-печать / 3D print | Крышка с рельефом логотипа / logo relief lid
M3-COVER-FASTENER-TRIAL | 4 | 80 | 160 | 164 | Крепёж / hardware | Крепёж крышки; длина и вставка после примерки / cover fasteners
COVER-GASKET-TRIAL | 1 | 20 | 40 | 41 | Уплотнение / seal | Непрерывная сменная прокладка; материал после IP-теста / gasket
DIONEYA-STACKED-COLOUR-MARK-OPTION | 1 | 20 | 40 | 41 | Операция / operation | Цветная стойкая маркировка по утверждённому SVG, если требуется / colour mark
Винты, прокладка и цветная маркировка: параметры и цены после физической примерки и IP-проверки.
Логотип в крышке: одноцветный рельеф 0,6 мм; цветной SVG приложен для стойкой маркировки.
