skif-ops/rs-zs-bpla/releases/evt-pre-20/2026-10-02-rev-d5/Заказ_плат_и_монтаж/03_PCB_MAIN_заказ_с_DFM/01_Изготовление_платы/PCB-MAIN_ИМПЕДАНС_ТРАССЫ_REV_D.csv

Group | Net | Copper_layer | As_routed_width_mm | Segment_count | Candidate_reference_layer | Factory_target_ohm | Factory_tolerance | Disposition
RF | CELL_RF | F.Cu | 0.1509 | 38 | In1.Cu split GND; verify under trace |  |  | EVT_AS_ROUTED_NO_CONTROLLED_IMPEDANCE_ORDERED
RF | CELL_RF_ANT | F.Cu | 0.1509 | 37 | In1.Cu split GND; verify under trace |  |  | EVT_AS_ROUTED_NO_CONTROLLED_IMPEDANCE_ORDERED
RF | GNSS_RF_ANT_BIASED | F.Cu | 0.1509 | 22 | In1.Cu split GND; verify under trace |  |  | EVT_AS_ROUTED_NO_CONTROLLED_IMPEDANCE_ORDERED
RF | GNSS_RF_DC_BLOCK | F.Cu | 0.1509 | 2 | In1.Cu split GND; verify under trace |  |  | EVT_AS_ROUTED_NO_CONTROLLED_IMPEDANCE_ORDERED
RF | GNSS_RF_FILTERED | F.Cu | 0.1509 | 2 | In1.Cu split GND; verify under trace |  |  | EVT_AS_ROUTED_NO_CONTROLLED_IMPEDANCE_ORDERED
RF | LORA_RF_ANT | F.Cu | 0.1509 | 26 | In1.Cu split GND; verify under trace |  |  | EVT_AS_ROUTED_NO_CONTROLLED_IMPEDANCE_ORDERED
RF | LORA_RF_MODULE | F.Cu | 0.1509 | 13 | In1.Cu split GND; verify under trace |  |  | EVT_AS_ROUTED_NO_CONTROLLED_IMPEDANCE_ORDERED
USB_FS | CELL_USB_DM_TP | B.Cu | 0.1537 | 10 | In6.Cu GND_DIGITAL; verify under trace |  |  | EVT_AS_ROUTED_NO_CONTROLLED_IMPEDANCE_ORDERED
USB_FS | CELL_USB_DM_TP | F.Cu | 0.1537 | 3 | In1.Cu split GND; verify under trace |  |  | EVT_AS_ROUTED_NO_CONTROLLED_IMPEDANCE_ORDERED
USB_FS | CELL_USB_DM_U8 | F.Cu | 0.1537 | 3 | In1.Cu split GND; verify under trace |  |  | EVT_AS_ROUTED_NO_CONTROLLED_IMPEDANCE_ORDERED
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
