skif-ops/rs-zs-bpla/releases/evt-pre-20/2026-10-02-rev-d5/Заказ_плат_и_монтаж/02_PCB_MIC_управляемый_заказ_и_монтаж/03_Исходники_и_контроль/PCB-MIC_board.step

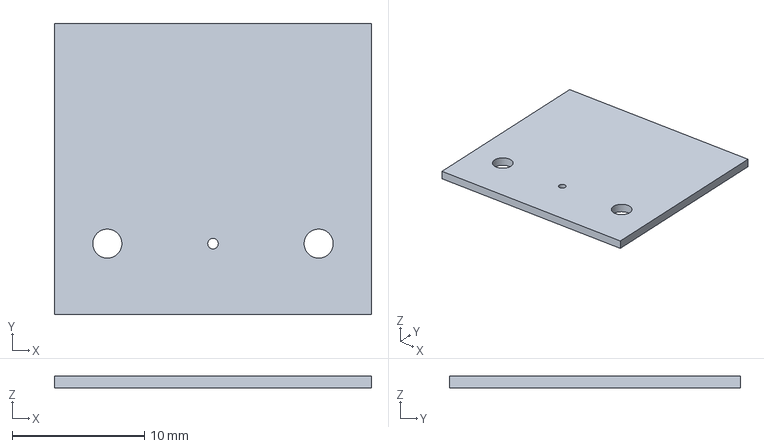
[picture p29: CAD file, 2026-09-30]
releases/evt-pre-20/2026-10-02-rev-d5/Заказ_плат_и_монтаж/02_PCB_MIC_управляемый_заказ_и_монтаж/03_Исходники_и_контроль/PCB-MIC_board.step
24.0 x 22.0 x 0.91 mm
