skif-ops/rs-zs-bpla/releases/evt-pre-20/2026-10-02-rev-d5/Основной_пакет/03_Корпуса_для_3D_печати_ПРЕДВАРИТЕЛЬНО/Верхний_электронный_модуль/DIO-3DP-UP-001B_lid.step

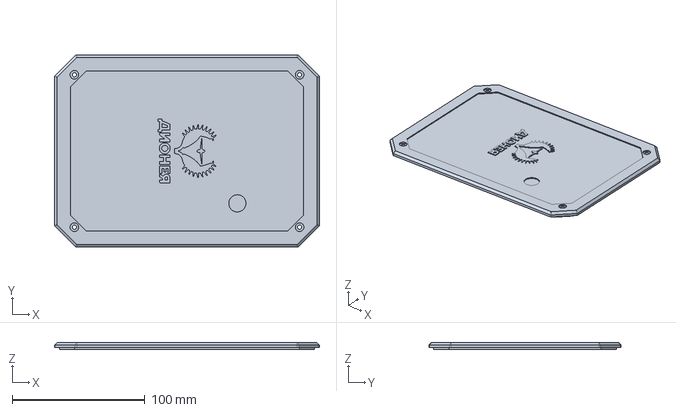
[picture p30: CAD file, 2026-10-02]
releases/evt-pre-20/2026-10-02-rev-d5/Основной_пакет/03_Корпуса_для_3D_печати_ПРЕДВАРИТЕЛЬНО/Верхний_электронный_модуль/DIO-3DP-UP-001B_lid.step
200.0 x 145.0 x 5.50 mm
