skif-ops/rs-zs-bpla/releases/evt-pre-20/2026-10-02-rev-d5/Основной_пакет/03_Корпуса_для_3D_печати_ПРЕДВАРИТЕЛЬНО/Кассета_питания_RevB/PCB_PWR_3D_PRINT_HARNESS_EXITS_REV_B_lid.step

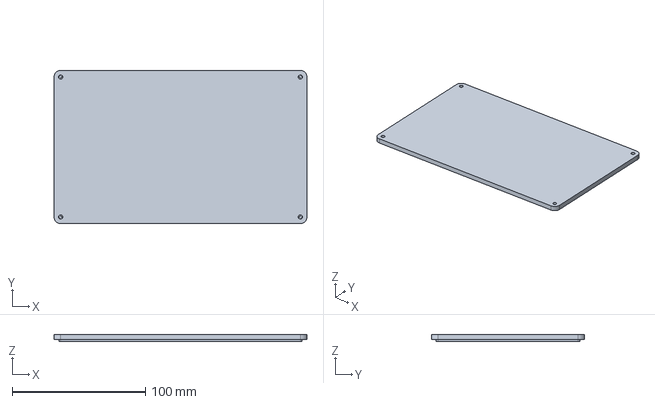
[picture p31: CAD file, 2026-09-30]
releases/evt-pre-20/2026-10-02-rev-d5/Основной_пакет/03_Корпуса_для_3D_печати_ПРЕДВАРИТЕЛЬНО/Кассета_питания_RevB/PCB_PWR_3D_PRINT_HARNESS_EXITS_REV_B_lid.step
190.0 x 115.0 x 5.50 mm
