skif-ops/rs-zs-bpla/releases/evt-pre-20/2026-10-02-rev-d5/Основной_пакет/03_Корпуса_для_3D_печати_ПРЕДВАРИТЕЛЬНО/Микрофонный_модуль/DIO-3DP-MC-001B_body.step

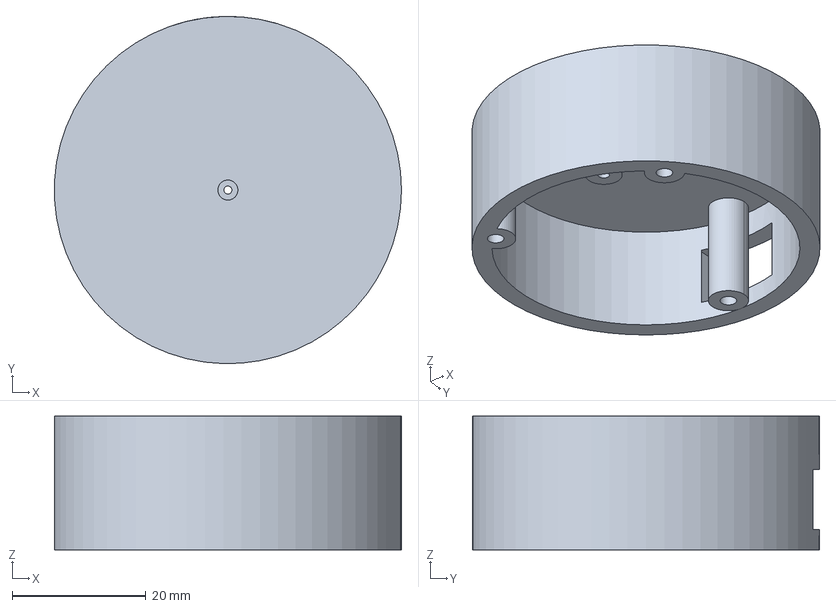
[picture p32: CAD file, 2026-10-01]
releases/evt-pre-20/2026-10-02-rev-d5/Основной_пакет/03_Корпуса_для_3D_печати_ПРЕДВАРИТЕЛЬНО/Микрофонный_модуль/DIO-3DP-MC-001B_body.step
52.0 x 52.0 x 20.0 mm
