skif-ops/rs-zs-bpla/releases/evt-pre-20/2026-10-02-rev-d5/Основной_пакет/03_Корпуса_для_3D_печати_ПРЕДВАРИТЕЛЬНО/Нижний_батарейный_модуль_и_маунты/DIO-3DP-MAST-001A_saddle.stl

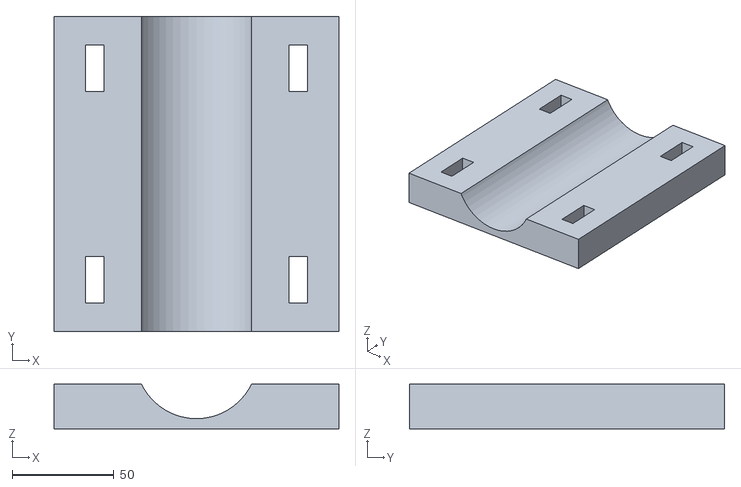
[picture p33: CAD file, 2026-09-30]
releases/evt-pre-20/2026-10-02-rev-d5/Основной_пакет/03_Корпуса_для_3D_печати_ПРЕДВАРИТЕЛЬНО/Нижний_батарейный_модуль_и_маунты/DIO-3DP-MAST-001A_saddle.stl
140.0 x 155.0 x 22.0
