skif-ops/rs-zs-bpla/releases/evt-pre-20/2026-10-02-rev-d5/Основной_пакет/04_Литье_исходные_данные_ПРЕДВАРИТЕЛЬНО/Акустическая_голова_3плюс1_макет/DIO-3DP-AH-001C_cable_hatch_north.step

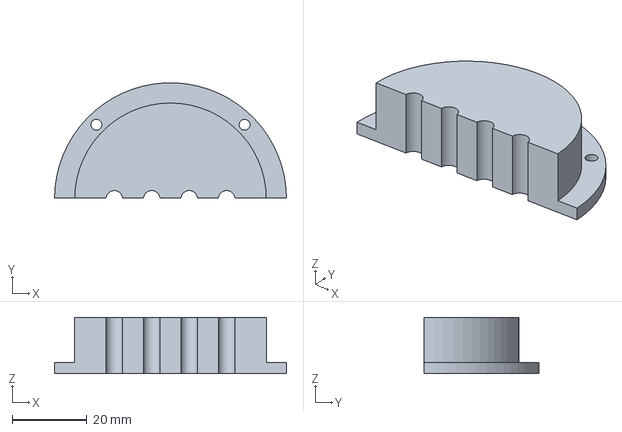
[picture p34: CAD file, 2026-10-02]
releases/evt-pre-20/2026-10-02-rev-d5/Основной_пакет/04_Литье_исходные_данные_ПРЕДВАРИТЕЛЬНО/Акустическая_голова_3плюс1_макет/DIO-3DP-AH-001C_cable_hatch_north.step
62.0 x 30.8 x 15.0 mm
