skif-ops/rs-zs-bpla/releases/evt-pre-20/2026-10-02-rev-d5/Основной_пакет/04_Литье_исходные_данные_ПРЕДВАРИТЕЛЬНО/Вакуумное_литье/Микрофонный_модуль/DIO-VAC-MC-001B_lid.step

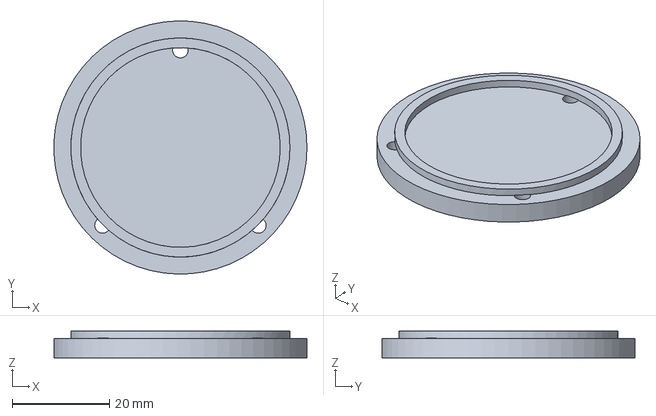
[picture p35: CAD file, 2026-10-01]
releases/evt-pre-20/2026-10-02-rev-d5/Основной_пакет/04_Литье_исходные_данные_ПРЕДВАРИТЕЛЬНО/Вакуумное_литье/Микрофонный_модуль/DIO-VAC-MC-001B_lid.step
52.0 x 52.0 x 5.50 mm
