skif-ops/rs-zs-bpla/releases/evt-pre-20/2026-10-02-rev-d5/Сборка_и_корпуса/03_Корпуса_для_3D_печати_ПРЕДВАРИТЕЛЬНО/Акустическая_голова_3плюс1/DIO-3DP-AH-001C_upper_carrier.step

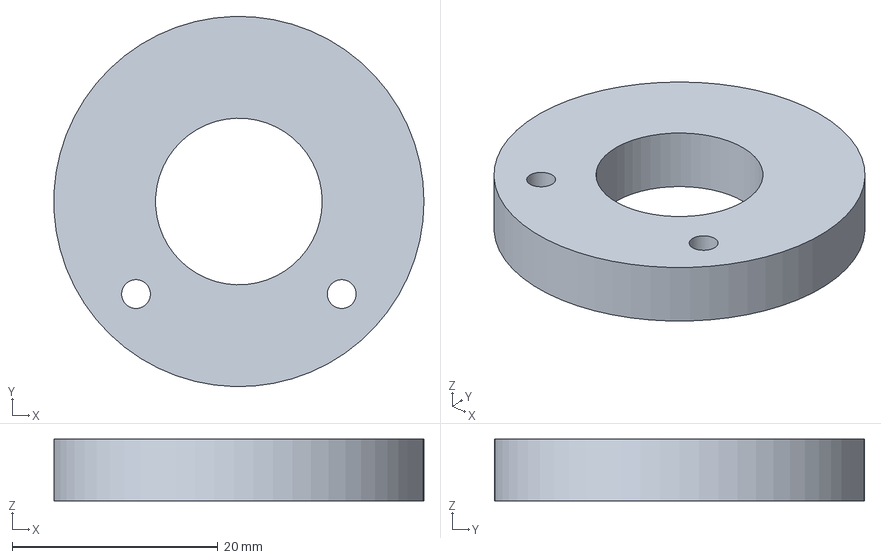
[picture p38: CAD file, 2026-10-02]
releases/evt-pre-20/2026-10-02-rev-d5/Сборка_и_корпуса/03_Корпуса_для_3D_печати_ПРЕДВАРИТЕЛЬНО/Акустическая_голова_3плюс1/DIO-3DP-AH-001C_upper_carrier.step
36.0 x 36.0 x 6.00 mm
