skif-ops/rs-zs-bpla/releases/evt-pre-20/2026-10-02-rev-d5/Сборка_и_корпуса/03_Корпуса_для_3D_печати_ПРЕДВАРИТЕЛЬНО/Нижний_батарейный_модуль_и_маунты/DIO-3DP-MPPT-001A_bracket.stl

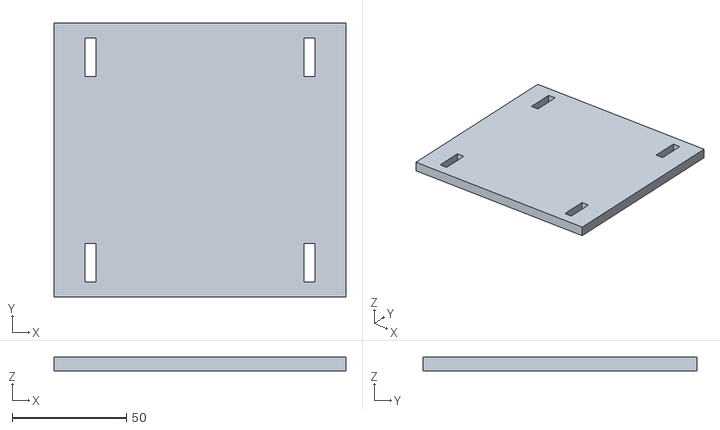
[picture p39: CAD file, 2026-09-30]
releases/evt-pre-20/2026-10-02-rev-d5/Сборка_и_корпуса/03_Корпуса_для_3D_печати_ПРЕДВАРИТЕЛЬНО/Нижний_батарейный_модуль_и_маунты/DIO-3DP-MPPT-001A_bracket.stl
128.0 x 120.0 x 6.00
