skif-ops/rs-zs-bpla/releases/evt-pre-20/2026-10-02-rev-d5/Сборка_и_корпуса/04_Литье_исходные_данные_ПРЕДВАРИТЕЛЬНО/Акустическая_голова_3плюс1_макет/DIO-3DP-AH-001C_central_mast.step

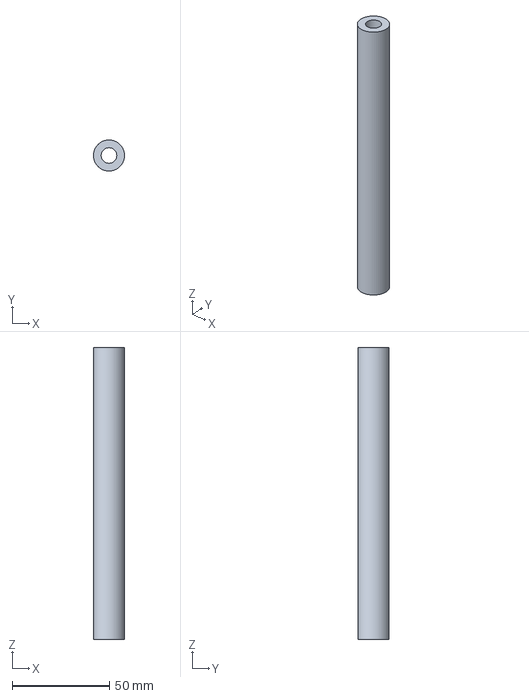
[picture p40: CAD file, 2026-10-02]
releases/evt-pre-20/2026-10-02-rev-d5/Сборка_и_корпуса/04_Литье_исходные_данные_ПРЕДВАРИТЕЛЬНО/Акустическая_голова_3плюс1_макет/DIO-3DP-AH-001C_central_mast.step
16.0 x 16.0 x 150.0 mm
