skif-ops/rs-zs-bpla/releases/evt-pre-20/2026-10-02-rev-d5/Сборка_и_корпуса/04_Литье_исходные_данные_ПРЕДВАРИТЕЛЬНО/Литье_под_давлением/Кассета_питания_RevB/PCB_PWR_INJECTION_MOLDING_HARNESS_EXITS_REV_B_body.step

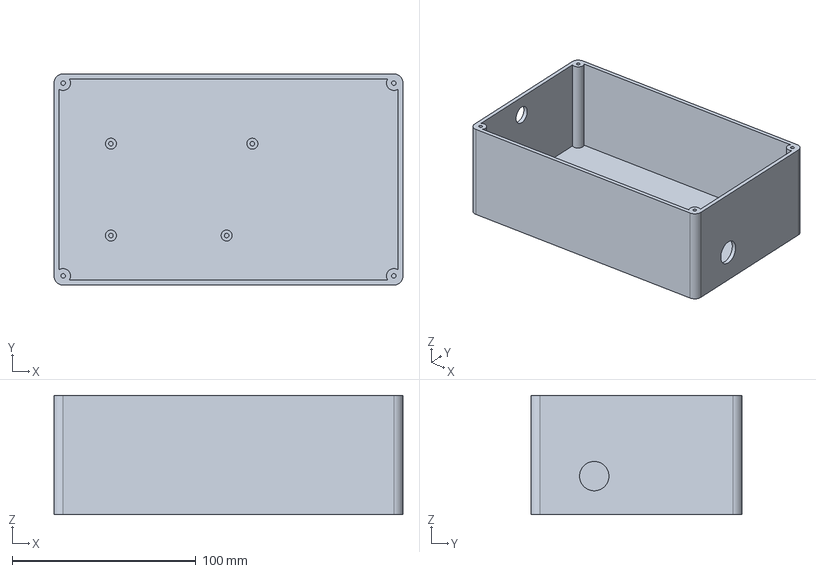
[picture p41: CAD file, 2026-09-30]
releases/evt-pre-20/2026-10-02-rev-d5/Сборка_и_корпуса/04_Литье_исходные_данные_ПРЕДВАРИТЕЛЬНО/Литье_под_давлением/Кассета_питания_RevB/PCB_PWR_INJECTION_MOLDING_HARNESS_EXITS_REV_B_body.step
190.0 x 115.0 x 65.0 mm
