skif-ops/rs-zs-bpla/releases/evt-pre-20/2026-10-02-rev-d5/Основной_пакет/03_Корпуса_для_3D_печати_ПРЕДВАРИТЕЛЬНО/Акустическая_голова_3плюс1/DIO-3DP-AH-001C_integral_upper_cage.step

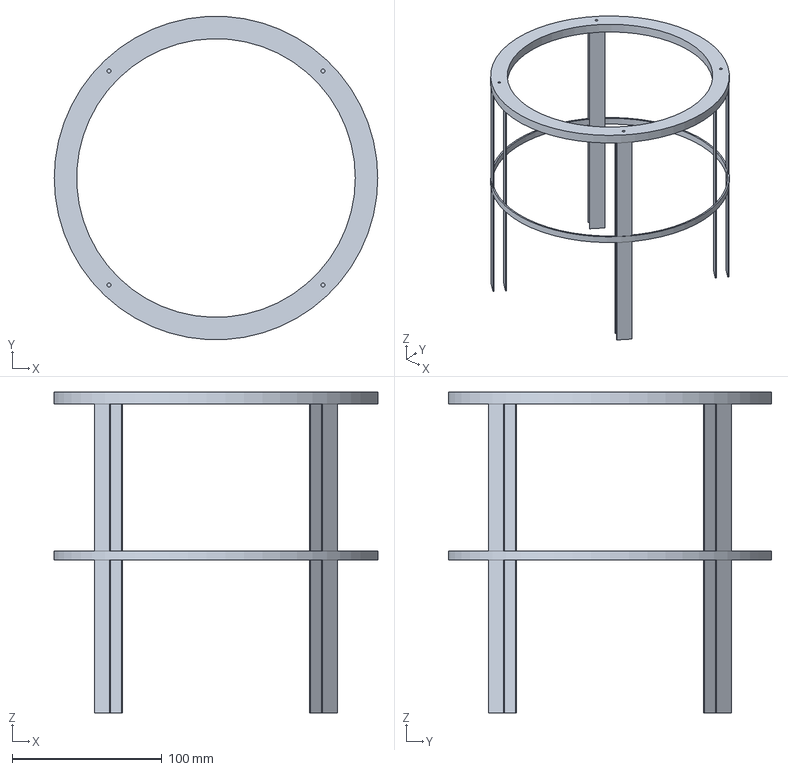
[picture p42: CAD file, 2026-10-02]
releases/evt-pre-20/2026-10-02-rev-d5/Основной_пакет/03_Корпуса_для_3D_печати_ПРЕДВАРИТЕЛЬНО/Акустическая_голова_3плюс1/DIO-3DP-AH-001C_integral_upper_cage.step
216.0 x 215.6 x 214.0 mm
