skif-ops/rs-zs-bpla/releases/evt-pre-20/2026-10-02-rev-d5/Основной_пакет/03_Корпуса_для_3D_печати_ПРЕДВАРИТЕЛЬНО/Нижний_батарейный_модуль_и_маунты/DIO-3DP-PV-001A_frame_clamp.stl

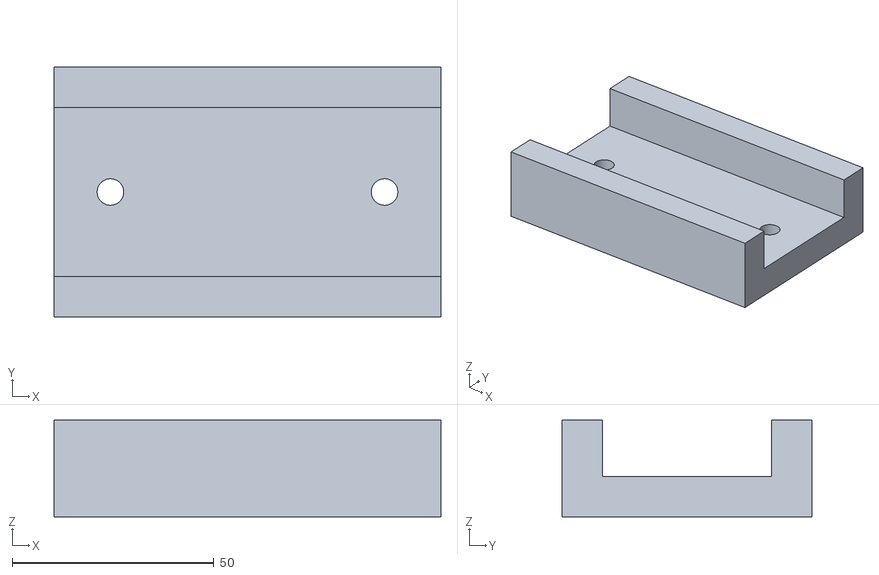
[picture p43: CAD file, 2026-09-30]
releases/evt-pre-20/2026-10-02-rev-d5/Основной_пакет/03_Корпуса_для_3D_печати_ПРЕДВАРИТЕЛЬНО/Нижний_батарейный_модуль_и_маунты/DIO-3DP-PV-001A_frame_clamp.stl
96.0 x 62.0 x 24.0
