skif-ops/rs-zs-bpla/releases/evt-pre-20/2026-10-02-rev-d5/Основной_пакет/04_Литье_исходные_данные_ПРЕДВАРИТЕЛЬНО/Акустическая_голова_3плюс1_макет/DIO-3DP-AH-001C_sealed_floor_carrier.step

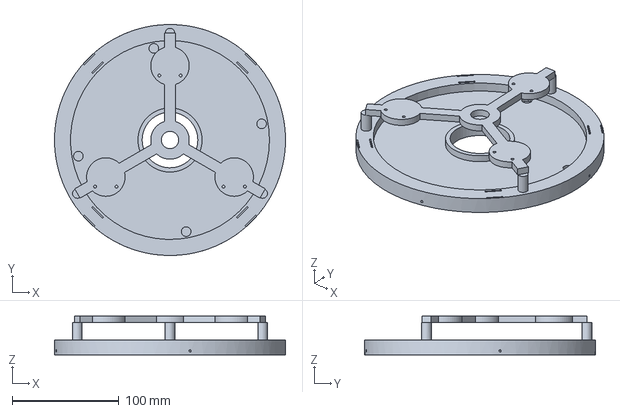
[picture p44: CAD file, 2026-10-02]
releases/evt-pre-20/2026-10-02-rev-d5/Основной_пакет/04_Литье_исходные_данные_ПРЕДВАРИТЕЛЬНО/Акустическая_голова_3плюс1_макет/DIO-3DP-AH-001C_sealed_floor_carrier.step
216.0 x 215.9 x 36.0 mm
