skif-ops/rs-zs-bpla/releases/evt-pre-20/2026-10-02-rev-d5/Основной_пакет/04_Литье_исходные_данные_ПРЕДВАРИТЕЛЬНО/Вакуумное_литье/Верхний_электронный_модуль/DIO-3DP-UP-001B_body.step

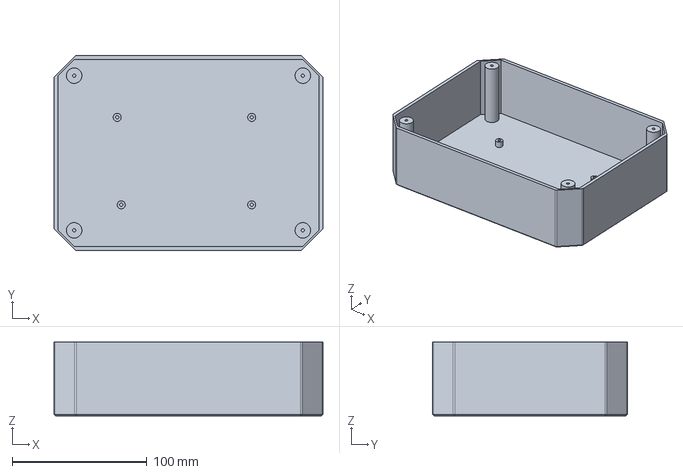
[picture p45: CAD file, 2026-10-02]
releases/evt-pre-20/2026-10-02-rev-d5/Основной_пакет/04_Литье_исходные_данные_ПРЕДВАРИТЕЛЬНО/Вакуумное_литье/Верхний_электронный_модуль/DIO-3DP-UP-001B_body.step
200.0 x 145.0 x 55.0 mm
