skif-ops/rs-zs-bpla/releases/evt-pre-20/2026-10-02-rev-d5/Основной_пакет/04_Литье_исходные_данные_ПРЕДВАРИТЕЛЬНО/Нижний_модуль_макет/DIO-CAST-LB-001A_lid.stl

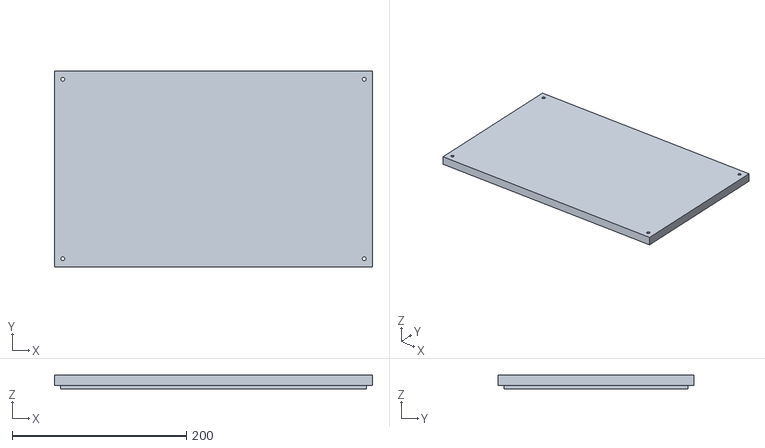
[picture p46: CAD file, 2026-09-30]
releases/evt-pre-20/2026-10-02-rev-d5/Основной_пакет/04_Литье_исходные_данные_ПРЕДВАРИТЕЛЬНО/Нижний_модуль_макет/DIO-CAST-LB-001A_lid.stl
365.0 x 225.0 x 16.0
