skif-ops/rs-zs-bpla/releases/evt-pre-20/2026-10-02-rev-d5/Сборка_и_корпуса/03_Корпуса_для_3D_печати_ПРЕДВАРИТЕЛЬНО/Акустическая_голова_3плюс1/DIO-3DP-AH-001C_foam_cut_envelope_NOT_PRINT.step

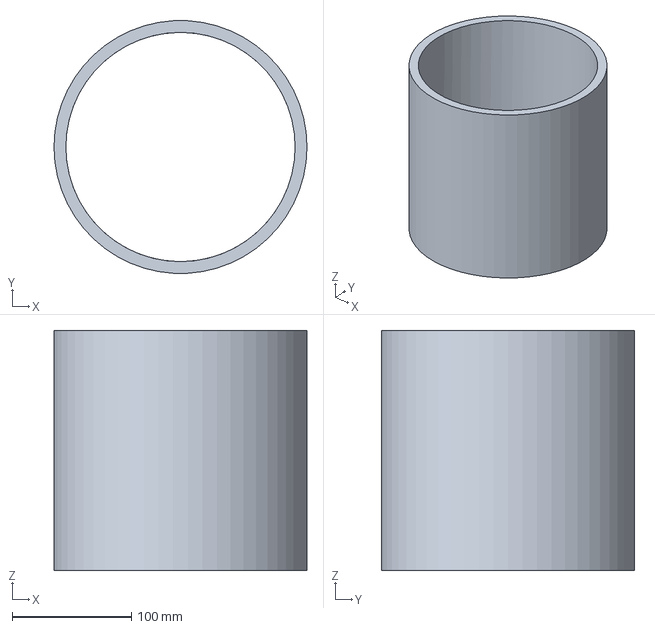
[picture p48: CAD file, 2026-10-02]
releases/evt-pre-20/2026-10-02-rev-d5/Сборка_и_корпуса/03_Корпуса_для_3D_печати_ПРЕДВАРИТЕЛЬНО/Акустическая_голова_3плюс1/DIO-3DP-AH-001C_foam_cut_envelope_NOT_PRINT.step
212.6 x 212.2 x 202.0 mm
