skif-ops/rs-zs-bpla/hardware/reviews/PCB_PWR_INPUT_PROTECTION_TEST_MATRIX_REV_A.csv

Test_ID | Gate | Required_Input | Procedure | Instrumentation | Pass_Criteria | Evidence_Required | Status | Result | Operator | Date | Artifact_SHA256 | Blocking
PWR-IPQ-001 | SOURCE_CONTROL | Current manufacturer documents and exact ordering codes | Archive controlled revisions for 0451008.MRL SMBJ18A 43045-0213 and 43030-0038; record retrieval date and file SHA-256 | Document archive and SHA-256 tool | Exact orderable identities and ratings match the qualification contract; no family-member substitution | Archived files source URLs retrieval record and hashes | PENDING_EVIDENCE |  |  |  |  | YES
PWR-IPQ-002 | SAMPLE_IDENTITY | Authorized-channel engineering samples | Inspect marking packaging labels lot codes and certificates before electrical test | Microscope camera and incoming-inspection record | All tested fuse and TVS samples are exact target MPNs with traceable lots | Photos lot record CoC and distributor invoice | PENDING_PHYSICAL_TEST |  |  |  |  | YES
PWR-IPQ-003 | NATIVE_VALUE_ECO | Approved bounded value-only ECO | Change F1 value from 0451005.MRL to 0451008.MRL in generator native schematic and PCB without topology footprint or placement change | Git diff semantic net audit and KiCad source parser | 0451008.MRL is present in all active native/generated value fields; 0451005.MRL is absent from active source; nets footprint and placement are unchanged | ECO diff source hashes and independent semantic audit | PASS | F1=0451008.MRL in all active sources; pin/net and board semantic digests retained; post-ECO ERC/PDF artifact archived | GitHub Actions run 35197150159 + Codex independent audit | 2026-09-17 | bf80f07c9b20d93d610c3e8c124887becb4209f8d688f085fe68bac53e0ad0b9 | YES
PWR-IPQ-004 | REPEAT_HIERARCHY_GATE | Committed post-ECO native source | Run KiCad 9 ERC export the five-page PDF and repeat independent hierarchy review against the new commit | KiCad 9 CI independent hierarchy audit and PDF preflight | ERC has zero violations; source and PDF hashes are commit-bound; independent decision is ACCEPT_HIERARCHY_ONLY or stronger without routing/manufacture release | CI URLs ERC JSON PDF source hashes and signed review record | PENDING_EVIDENCE |  |  |  |  | YES
PWR-IPQ-005 | FUSE_25C_CONTINUOUS | Representative assembled input path | Operate at 5.0 A DC and 25 C ambient for at least 4 h after thermal stabilization | Calibrated source load current probe DMM thermocouples and IR camera | No nuisance opening or drift; F1 body remains below 125 C; J1 housing remains below 105 C; no discoloration solder or copper damage | Current voltage and temperature time series plus before-after inspection | PENDING_PHYSICAL_TEST |  |  |  |  | YES
PWR-IPQ-006 | FUSE_70C_CONTINUOUS | Final enclosure thermal configuration and qualified wire | Operate at 5.0 A DC and 70 C ambient for at least 4 h after stabilization | Environmental chamber calibrated current probe DMM thermocouples and IR camera | No nuisance opening; F1 body remains below 125 C; J1 housing remains below 105 C; wire stays within its accepted rating; no damage or unstable resistance | Chamber log current voltage temperature map and inspection photos | PENDING_PHYSICAL_TEST |  |  |  |  | YES
PWR-IPQ-007 | COLD_START_INRUSH | Final cold-soaked battery-equivalent and loads | Cold soak to -40 C then execute controlled power-on and recovery cycles at minimum operating input | Chamber programmable source current probe and oscilloscope | All required rails start; F1 does not nuisance-open; measured inrush is captured and remains within accepted time-current margin | Waveforms cycle log and rail-status evidence | PENDING_PHYSICAL_TEST |  |  |  |  | YES
PWR-IPQ-008 | MODEM_BURST_INRUSH | Representative BG95 load profile and final bulk network | Run repeated worst-case attach and transmit bursts over the accepted input-voltage range | Electronic load or modem fixture current probe oscilloscope and rail probes | No nuisance opening; no rail falls below its accepted limit; peak and pulse duration are below the accepted fuse time-current envelope | Raw waveforms processed peak-duration table and rail logs | PENDING_PHYSICAL_TEST |  |  |  |  | YES
PWR-IPQ-009 | OVERLOAD_TIME_CURRENT | Safe current-limited fixture and sacrificial samples | Apply controlled overload points spanning expected abnormal load through 200 percent of fuse rating and record opening time | Four-wire source external current probe oscilloscope and thermal camera | Measured opening behavior is consistent with the current Littelfuse time-current curve and declared tolerance; no downstream damage | Per-sample waveform temperature and lot-indexed opening-time table | PENDING_PHYSICAL_TEST |  |  |  |  | YES
PWR-IPQ-010 | CONTROLLED_SHORT_ENERGY | Measured source impedance and protected fault fixture | Replay bounded downstream short cases with current and energy limits; never short an unprotected RB40 directly | Current-limited source external current probe differential voltage probes oscilloscope and calorimetry as needed | F1 clears before accepted downstream I2t thermal and voltage limits are exceeded; no fire ejecta or persistent conductive damage | Fault waveforms calculated I2t thermal record and post-test inspection | PENDING_PHYSICAL_TEST |  |  |  |  | YES
PWR-IPQ-011 | INTERRUPTING_AND_PRIMARY_FUSE | Measured RB40 harness and battery-side primary-fuse data | Calculate and verify maximum prospective current at F1; coordinate PCB fuse with the battery-side primary fuse and source impedance | Four-wire resistance meter current probe oscilloscope and primary-fuse data | Prospective current at F1 is below 400 A at 32 VDC and both protection stages clear in the intended order without exceeding cable connector or PCB limits | Source-impedance calculation primary-fuse curve and coordinated fault results | PENDING_PHYSICAL_TEST |  |  |  |  | YES
PWR-IPQ-012 | CONNECTOR_HARNESS_THERMAL | Final J1 housing 43030-0038 terminals exact wire and crimp process | Operate the full input interconnect at 5.0 A and 70 C ambient including mating interfaces and strain relief | Chamber four-wire milliohm meter current probe thermocouples and IR camera | J1 housing remains below 105 C; contacts wire and crimps remain within accepted ratings; voltage drop and resistance drift meet frozen limits | Temperature map voltage-drop trend crimp identity and inspection record | PENDING_PHYSICAL_TEST |  |  |  |  | YES
PWR-IPQ-013 | TVS_STEADY_STATE | Measured battery BMS and MPPT steady-state voltage limits | Sweep and dwell across the released steady-state input range with SMBJ18A fitted | Programmable source precision current meter oscilloscope and thermal camera | No avalanche or abnormal heating at any released steady-state voltage; sustained overvoltage is handled upstream and not by TVS conduction | Voltage leakage temperature sweep and upstream protection evidence | PENDING_PHYSICAL_TEST |  |  |  |  | YES
PWR-IPQ-014 | BATTERY_CONNECT_TRANSIENT | Measured RB40 and final harness source model | Capture repeated normal and worst-phase battery connect and disconnect events at cold room and hot conditions | Differential high-voltage probe external current probe oscilloscope and final harness | Protected-node peak is no more than 32.0 V and always below 36.0 V; no damage false rail start or fuse opening | Raw waveforms setup photos source impedance and event table | PENDING_PHYSICAL_TEST |  |  |  |  | YES
PWR-IPQ-015 | MPPT_TRANSIENT | Configured SCC075010060R SBS050150200 RB40 and SLP080S-12M samples | Capture panel battery controller connect disconnect recovery and BMS-transition events across the approved charge configuration | Differential probes current probes oscilloscope and exported Victron configuration | Protected-node peak is no more than 32.0 V and always below 36.0 V; no sustained TVS conduction fuse opening or control instability | Raw waveforms configuration export temperatures and event table | PENDING_PHYSICAL_TEST |  |  |  |  | YES
PWR-IPQ-016 | TVS_CLAMP_PULSE | Measured source pulse envelope and representative PCB layout | Inject bounded pulses reproducing the accepted worst transient at the PCB input and protected node | Calibrated surge fixture differential probes current probe oscilloscope and thermal camera | Protected-node maximum is no more than 32.0 V and never reaches 36.0 V; SMBJ18A pulse energy and temperature remain within accepted limits | Pulse calibration raw waveforms energy calculation and inspection | PENDING_PHYSICAL_TEST |  |  |  |  | YES
PWR-IPQ-017 | REVERSE_POLARITY | Current-limited reverse-polarity fixture | Apply the released reverse-polarity cases and recovery sequence with F1 SMBJ18A LM74700 and CSD18540 fitted | Protected source differential probes current probe oscilloscope and thermal camera | No unsafe current or downstream reverse voltage; recovery is controlled; no component or connector exceeds its accepted limit | Waveforms leakage temperature and inspection record | PENDING_PHYSICAL_TEST |  |  |  |  | YES
PWR-IPQ-018 | TVS_FAIL_SHORT_COORDINATION | Sacrificial boards and bounded fail-short injection | Force or emulate the documented TVS short failure mode and verify protective clearing | Current-limited source current probe voltage probes oscilloscope and thermal camera | F1 and battery-side protection isolate the fault before connector harness PCB or enclosure damage; fault remains detectable | Fault waveform clearing order I2t temperature and post-test inspection | PENDING_PHYSICAL_TEST |  |  |  |  | YES
PWR-IPQ-019 | INA226_MEASUREMENT_SCOPE | Reference meter and overload fixture | Verify INA226 accuracy through 5.0 A then inject currents above its 6.5534 A signed range using external instrumentation | Reference meter external current probe oscilloscope and telemetry capture | Normal range meets frozen calibration limits; overload cannot appear as plausible valid negative or low current; firmware marks out-of-range or fault state; fault energy uses external data | Calibration table raw register log telemetry and external waveform | PENDING_PHYSICAL_TEST |  |  |  |  | YES
PWR-IPQ-020 | RELEASE_EVIDENCE | All prior rows completed and accepted | Audit row status attribution artifact hashes candidate identities ECO commit and open manufacturing gates | Independent audit and release checklist | 20 of 20 rows are PASS with attributable evidence; exact target parts and post-ECO source agree; Review B remains separately required | Completed matrix audit JSON commit SHA and release decision | PENDING_EVIDENCE |  |  |  |  | YES
