skif-ops/rs-zs-bpla/releases/evt-pre-20/2026-10-02-rev-d5/Заказ_плат_и_монтаж/03_PCB_MAIN_заказ_с_DFM/01_Изготовление_платы/VIA_FILL_CAP_76_MAP_RU_EN.pdf

## PCB-MAIN Rev B: 76 переходов POFV / 76 filled and capped vias

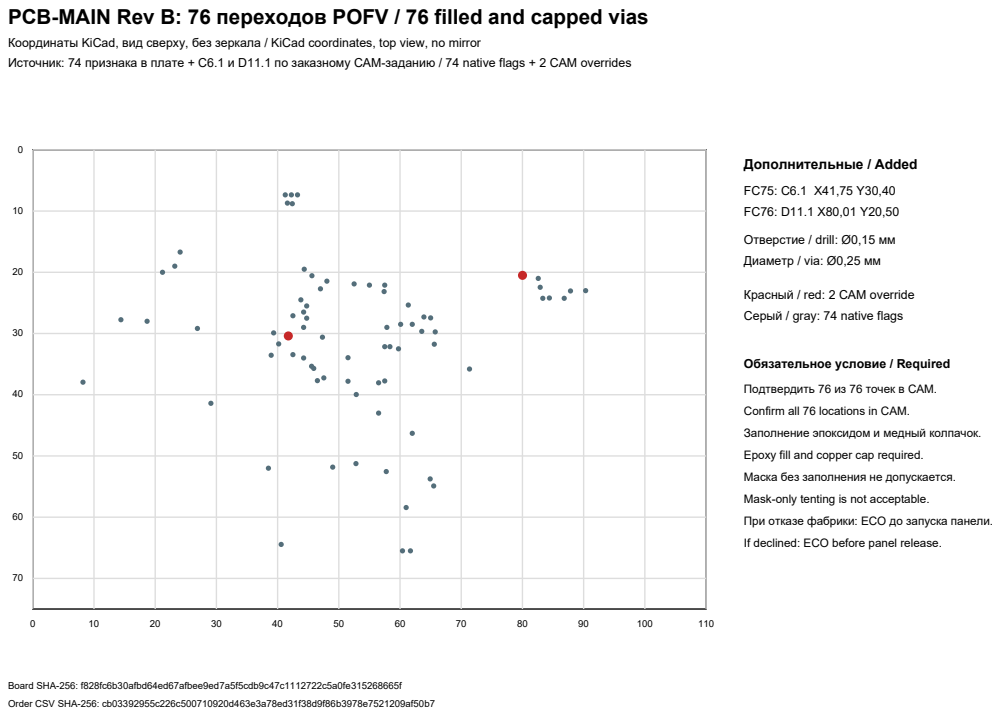
[picture p66: page 1]
Дополнительные / Added; Board SHA-256: f828fc6b30afbd64ed67afbee9ed7a5f5cdb9c47c1112722c5a0fe315268665f

Координаты KiCad, вид сверху, без зеркала / KiCad coordinates, top view, no mirror
Источник: 74 признака в плате + C6.1 и D11.1 по заказному CAM-заданию / 74 native flags + 2 CAM overrides

Отверстие / drill: Ø0,15 мм
Диаметр / via: Ø0,25 мм

Красный / red: 2 CAM override
Серый / gray: 74 native flags

Обязательное условие / Required

Подтвердить 76 из 76 точек в CAM.

Confirm all 76 locations in CAM.

Заполнение эпоксидом и медный колпачок.

Epoxy fill and copper cap required.

Маска без заполнения не допускается.

Mask-only tenting is not acceptable.

При отказе фабрики: ECO до запуска панели.

If declined: ECO before panel release.

Order CSV SHA-256: cb03392955c226c500710920d463e3a78ed31f38d9f86b3978e7521209af50b7
