skif-ops/rs-zs-bpla/releases/evt-pre-20/2026-10-02-rev-d5/Заказ_плат_и_монтаж/03_PCB_MAIN_заказ_с_DFM/02_Монтаж_платы/PCB-MAIN_Сборка_и_DFM_RU_EN.pdf

# PCB-MAIN Rev B - сборка и проверка фабрики / Assembly and fabricator review

EVT-PRE-20 · 29.09.2026 · Контрольная плата / Controlled board: SHA-256 f828fc6b30afbd64ed67afbee9ed7a5f5cdb9c47c1112722c5a0fe315268665f

Русский | English
Назначение и статус Плата PCB-MAIN Rev B предназначена для EVT-PRE-20. Трассировка завершена: DRC 0 ошибок, 0 неразведённых цепей; ERC 0. Пакет передать на заводскую DFM проверку до запуска панели. | Purpose and status PCB-MAIN Rev B is for EVT-PRE-20. Routing is complete: DRC 0 errors, 0 unconnected items; ERC 0. Submit this package for fabricator DFM review before panel release.
Плата и стек 8 слоёв, толщина 1,6 мм, финиш ENIG. Запрос на стек находится в STACKUP_REQUEST.json. Завод должен подтвердить ID стека, толщины диэлектриков, медь, импеданс и сверловку. | Board and stack 8 layers, 1.6 mm finished thickness, ENIG. STACKUP_REQUEST.json defines the request. Fabricator shall confirm stack ID, dielectrics, copper, impedance and drill capability.
Переходы в площадках 57 переходов в контактных площадках помечены для заполнения и металлизированного закрытия. Подтвердить технологию и стоимость. Проверить уменьшенные площадки J6/J7 pad 7 и J11 A1/A12/B1/B12. | Via-in-pad 57 via-in-pad locations are marked filled and capped. Confirm the process and quote. Review adjusted J6/J7 pad 7 and J11 A1/A12/B1/B12 land sizes.

Монтаж
Для монтажа использовать PCB-MAIN_BOM_PCBA.csv и PCB-MAIN_POS_TOP_PCBA.csv: 227 согласованных позиций. Пятнадцать позиций DNP не устанавливать. U12 - карта microSD, устанавливается при сборке станции, не на печатную плату. Пять групп TP снизу - только медные площадки.

Assembly
Use PCB-MAIN_BOM_PCBA.csv and PCB-MAIN_POS_TOP_PCBA.csv for the 227 matched placements. Do not populate the 15 DNP items. U12 is a microSD card for station assembly, not PCBA placement. Five bottom TP groups are copper pads only.

Первый образец и замечания
До серии сверить полярность и pin 1 по схеме, Gerber и первому образцу; сделать AOI, рентген участков со скрытыми выводами, электрический контроль и функциональный запуск. Замечания фабрики и монтажа вернуть в ECO.

First article and feedback
Before the series, confirm polarity and pin 1 against schematic, Gerber and first article; perform AOI, X-ray on hidden-joint areas, electrical check and functional bring-up. Return fab and assembly findings through ECO.

Состав листов / Sheet order: 1 - инструкция / instructions; 2 - вид сверху / top assembly; 3 - нижняя медь и контрольные площадки / bottom copper and test pads.

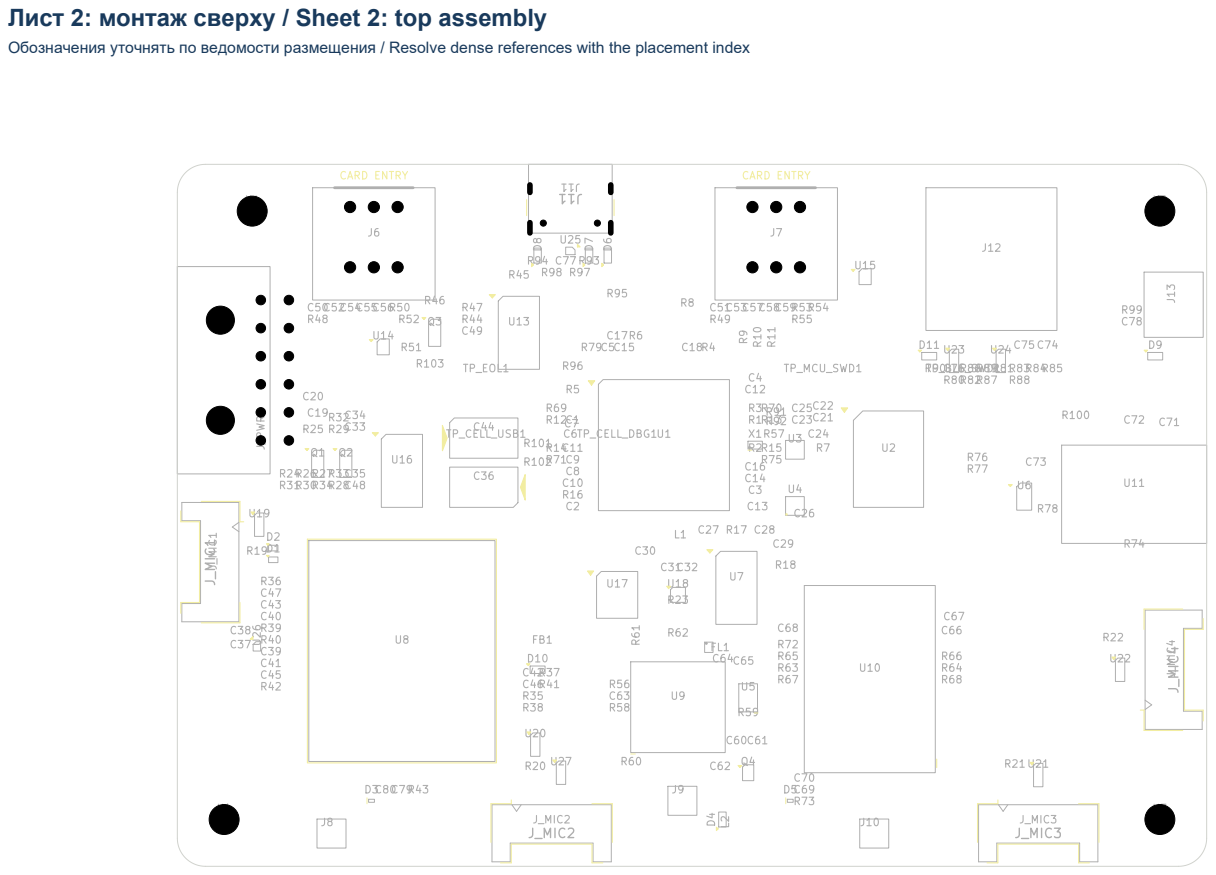
[picture p67: page 2]

Лист 2: монтаж сверху / Sheet 2: top assembly

Обозначения уточнять по ведомости размещения / Resolve dense references with the placement index

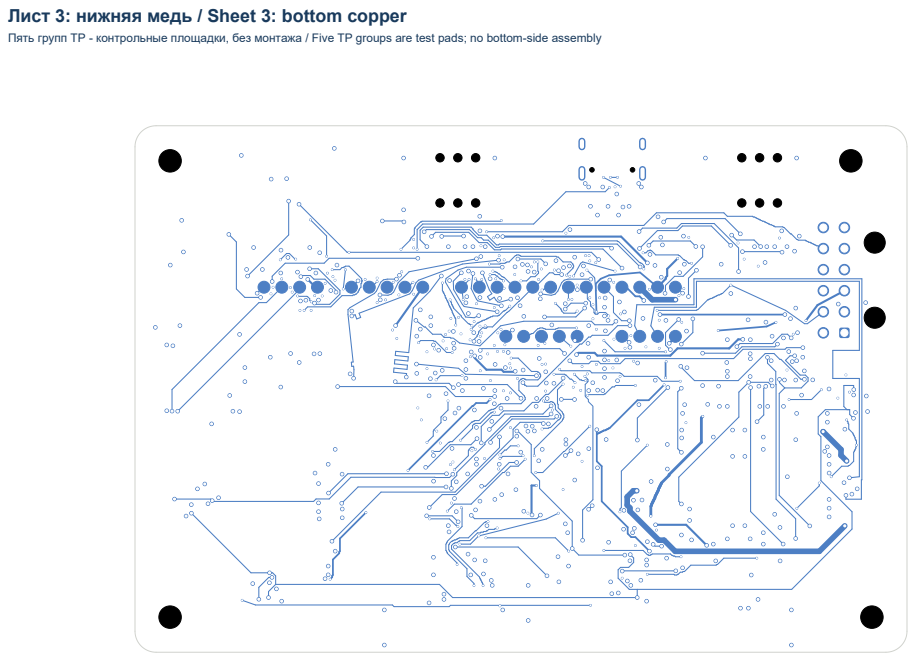
[picture p68: page 3]

Лист 3: нижняя медь / Sheet 3: bottom copper

Пять групп TP - контрольные площадки, без монтажа / Five TP groups are test pads; no bottom-side assembly
