skif-ops/rs-zs-bpla/firmware/targets/evt_pre_20/target_status.yaml

target_id: dioneya_evt_pre_20_rev_a
status: TARGET_PORT_REQUIRED
mcu: STM32U585VIT6Q
package: LQFP100_14x14
exact_pin_database_ref: STM32U585VITxQ
board: custom_pcb
host_core_source: ../..
wire_interface_release: "1.4"
detection_schema_version: 4
clocking:
  policy_id: REV_A_INTERNAL_HSI_MSI_PLL_NO_HSE
  external_hse: DISABLED_NOT_FITTED
  high_speed_sources: [MSI, HSI, PLL]
  low_speed_reference: SiT1552AI-JE-DCC-32.768D
  low_speed_reference_hz: 32768
  lse_bypass_configuration: IOC_EXTERNAL_CLOCK_SOURCE_CUBEMX_OPEN_CHECK_PENDING
  runtime_clock_profiles: TO_DEFINE_AND_MEASURE
  required_validation: [USB_CLOCK, PDM_SAMPLE_RATE, PPS_TIMESTAMPING, LOW_POWER_WAKE, PLL_SWITCH_RECOVERY]
audio:
  microphones: 4
  microphone_mpn: T5838
  sample_rate_hz: 32000
  geometry_id: 1
  base_triangle_side_mm: 120
  upper_offset_mm: 150
  low_power_detector: T5838_AAD
  aad_interface_baseline: hardware/T5838_AAD_INTERFACE_REV_A.md
  mic_harness_contacts: 6
  mic_harness_nets: [1V8_MIC, GND, PDM_CLK, PDM_DATA_N, MIC_WAKE_N, AAD_CFG]
  local_leaf_straps: [SELECT]
  aad_configuration_pin_name: THSEL
  aad_configuration_bus: AAD_CFG_SHARED_1V8
  aad_configuration_mcu_pin: PA15
  aad_configuration_lqfp100_pin: 77
  aad_configuration_direction: MCU_TO_U7_TO_1V8_TO_ALL_4_THSEL
  aad_configuration_cubemx: GPIO_OUTPUT_PENDING
  aad_configuration_clock_requirement_hz_min: 50000
  aad_configuration_sequence:
    - ENABLE_1V8_MIC
    - ENABLE_PDM_CLOCK_ABOVE_50KHZ
    - WRITE_THSEL_ONE_WIRE_PROFILE
    - COMPLETE_STOP_SYMBOL_AND_SETTLE
    - DISABLE_PDM_CLOCK_FOR_AAD_D2
    - ARM_MIC_WAKE_EXTI
  aad_configuration_profile_verify: READBACK_NOT_AVAILABLE_USE_TIMING_AND_WAKE_SELFTEST
  aad_threshold_profile: EVT_TUNE_REQUIRED
  aad_false_wake_test: REQUIRED
  aad_wake_latency_test: REQUIRED
  aad_s0_current_measurement: REQUIRED
  aad_cold_hot_test: REQUIRED_AT_MINUS40_AND_PLUS70
  aad_wake_inputs: [MIC_WAKE1, MIC_WAKE2, MIC_WAKE3, MIC_WAKE4]
  aad_wake_or: SN74LVC32APWR_at_1V8
  aad_wake_translator: SN74AXC1T45DRLR_1V8_to_3V3
  aad_wake_mcu_pin: PA8
  aad_wake_lqfp100_pin: 67
  aad_wake_cubemx: GPIO_EXTI_STOP_WAKE_PENDING
ble:
  soc: nRF52840
  module: Raytac_MDBT50Q-P1MV2
  interface: USART3_plus_enable_plus_dfu_request
  uart_map: P0.06_TX_to_PB11_RX_and_P0.08_RX_from_PB10_TX
  dfu_request: P0.15_active_low_open_drain
  reset: P0.18_nRESET_via_fail_closed_BLE_EN_buffer
  lfclk: INTERNAL_RC_CALIBRATED
  swd_map: dedicated_VTREF_NRF_SWDIO_NRF_SWCLK_GND
  wifi: NOT_REQUIRED
  required_phy: [BLE_2M, BLE_1M, BLE_CODED_LONG_RANGE]
  firmware_port: MISSING_BLOCKER
  swd_recovery: REQUIRED_ON_FIXTURE
  enclosure_rf_validation: REQUIRED
cellular:
  modem: Quectel_BG95_M3_candidate
  auto_network_settings: IMPLEMENTED_HOST_TESTED_HARDWARE_VALIDATION_PENDING
  discovery: [QCCID_FULL_RUNTIME, CIMI_FULL_RUNTIME, COPS_QUERY, CGNAPN]
  post_activation_readback: CGCONTRDP_APN_IP_GATEWAY_DNS_REQUIRED
  apn_policy: MATCHED_APPROVED_PUBLIC_PLMN_PROFILE_ONLY
  unknown_sim_or_apn_mismatch: FAIL_CLOSED
  full_imsi_iccid_telemetry: IMPLEMENTED_COMPACT_HEARTBEAT_MTLS_REQUIRED
  station_identity_storage: VOLATILE_RUNTIME_ONLY
  server_general_api_identity_view: REDACTED_ONLY
  physical_sim_operator_and_24h_evidence: DEFERRED_UNTIL_STATIONS_ASSEMBLED
  dual_sim_failover_controller: PORTABLE_SAFE_SEQUENCE_EXPLICIT_MODEM_OFF_MUX_HIGH_Z_RAIL_OFF_RECOVERY_HOLD_RETRY_ICCID_QG1_QG2_PASS_TARGET_PENDING
  dual_sim_bg95_bridge: PORTABLE_QPOWD_CELL_STATUS_FULL_ICCID_EXACT_PENDING_PROFILE_ONLINE_TLS_GATE_QG1_QG2_PASS_TARGET_PENDING
  dual_sim_gpio_binding: PORTABLE_EXACT_REV_A_GPIO_POLARITY_INTERLOCK_AND_OPTIONAL_FIXTURE_READBACK_INTERFACE_QG1_QG2_PASS_TARGET_HAL_PHYSICAL_PENDING
  mqtt_uart_session: PORTABLE_BOUNDED_RAW_UART_FRAMER_SINGLE_TX_OWNER_QG1_QG2_PASS_TARGET_USART_DMA_ISR_CACHE_AND_MODEM_PENDING
  event_store_forward_outbox: PORTABLE_ATOMIC_SHA256_PRIORITY_QG1_QG2_PASS_TARGET_STORAGE_BINDING_PENDING
  event_outbox_nor_adapter: PORTABLE_ERASE_ISOLATED_QG1_QG2_PASS_PARTITION_AND_OCTOSPI_BINDING_PENDING
  event_nor_partition_planner: PORTABLE_ARCHIVE_COMMAND_OUTBOX_NONOVERLAP_QG1_QG2_PASS_SLOT_COUNTS_AND_OCTOSPI_BINDING_PENDING
  event_nor_shared_binding: PORTABLE_FAIL_CLOSED_ARCHIVE_COMMAND_OUTBOX_QG1_QG2_PASS_TARGET_BINDING_PENDING
  event_application_receipt: PORTABLE_SERVER_FIRMWARE_BG95_SESSION_ROUTED_QG1_QG2_PASS_TARGET_USART_DMA_RETAIN_POLICY_AND_HARDWARE_PENDING
  event_mqtt_uplink_transport: PORTABLE_EXACT_TOPIC_RETRY_RECEIPT_QG1_QG2_PASS_BG95_SESSION_SERIALIZED_HOST_BINDING_TARGET_PENDING
  event_bg95_uplink_binding: PORTABLE_FIXED_LENGTH_BINARY_QMTPUB_SESSION_SERIALIZED_QG1_QG2_PASS_TARGET_USART_DMA_AND_HARDWARE_PENDING
  event_bg95_receipt_binding: PORTABLE_LENGTH_ENABLED_BINARY_QMTRECV_SESSION_ROUTED_QG1_QG2_PASS_TARGET_USART_DMA_RETAIN_POLICY_AND_HARDWARE_PENDING
  signed_command_codec: PORTABLE_CANONICAL_CBOR_QG1_QG2_PASS
  command_result_journal: PORTABLE_ATOMIC_QG1_QG2_PASS_NOR_ERASE_ISOLATED_SHARED_NONOVERLAP_BOUND_TARGET_SLOT_COUNT_ENDURANCE_PENDING
  command_journal_nor_adapter: PORTABLE_ERASE_ISOLATED_SHARED_ARCHIVE_COMMAND_OUTBOX_NONOVERLAP_QG1_QG2_PASS_TARGET_SLOT_COUNT_ENDURANCE_PENDING
  command_public_key_trust: PORTABLE_BOUNDED_ROTATION_QG1_QG2_PASS_PROVISIONING_PENDING
  command_application_channel: PORTABLE_FAIL_CLOSED_QG1_QG2_PASS_BG95_SESSION_ROUTED_TARGET_PENDING
  command_binary_mqtt_transport: PORTABLE_EXACT_TOPIC_PAYLOAD_LENGTH_QG1_QG2_PASS_BG95_SESSION_ROUTED_TARGET_PENDING
  command_bg95_binding: PORTABLE_LENGTH_ENABLED_BINARY_QMTRECV_FIXED_LENGTH_ACK_SESSION_SERIALIZED_QG1_QG2_PASS_TARGET_USART_DMA_RETAIN_POLICY_AND_HARDWARE_PENDING
  command_ed25519_backend: MISSING_BLOCKER
  command_mqtt_binding: PORTABLE_BG95_SESSION_FRAMED_SERIALIZED_QG1_QG2_PASS_TARGET_USART_DMA_RETAIN_POLICY_AND_HARDWARE_BLOCKER
storage:
  nor: Winbond_W25Q512JVFIQ
  nor_boot_probe: PORTABLE_W25Q512JV_EXACT_JEDEC_SFDP_CAPACITY_QE_RESTORE_QG1_QG2_PASS_TARGET_OCTOSPI_AND_SAMPLE_PENDING
  card: Kingston_SDCIT2_32GB
  socket: GCT_MEM2052_00_195_00_A
  interface: SDMMC1_4BIT_ONLY
  contact_order: [DAT2, CD_DAT3, CMD, VDD, CLK, VSS, DAT0, DAT1]
  card_detect: PC13_EXTI13_ACTIVE_LOW_CARD_PRESENT
  required_validation: [CID, CAPACITY, FULL_WRITE_READBACK, POWER_LOSS_RECOVERY, TEMPERATURE]
service_interfaces:
  usb_c: GCT_USB4105_GF_A_120
  usb_mode: STM32_USB2_DEVICE_ONLY_SERVICE_AND_SYSTEM_MEMORY_RECOVERY
  usb_data: PA11_DM_PA12_DP
  usb_vbus: PA9_PROTECTED_HIGH_IMPEDANCE_SENSE_ONLY
  usb_power_policy: NO_STATION_SOURCE_OR_SINK_POWER
  tamper: PC7_EXTI7_NORMALLY_CLOSED_TO_GND_OPEN_IS_ALARM
production_fixture:
  authority: hardware/PCB_MAIN_CONNECTOR_FIXTURE_PIN_AUTHORITY_REV_A.csv
  geometry_authority: hardware/PCB_MAIN_MECHANICAL_PLACEMENT_AUTHORITY_REV_A.csv
  side: BOTTOM
  pogo_pad_diameter_mm: 1.70
  pogo_pitch_mm: 2.54
  fixture_fiducials: 3
  stm32_swd: TP_MCU_SWD_5P_VTREF_SWDIO_SWCLK_NRST_GND
  eol: TP_EOL_13P_RAIL_SENSE_UART_POWER_STATE_BOOT0_REV_STRAPS_I2C2
  bg95_usb: TP_CELL_USB_4P_ISOLATED_FROM_STM32_USB
  bg95_debug: TP_CELL_DBG_5P_1V8_VREF_GATED
  nrf_swd: TP_BLE_SWD_4P_SEPARATE_AUTHORITY
  fixture_power_policy: DUT_RAILS_SENSE_ONLY_EXCEPT_CONTROLLED_BG95_USB_VBUS
pcb_main_capture:
  authority_status: MAIN_AUTH_001_THROUGH_011_CLOSED
  passive_support_authority: hardware/PCB_MAIN_PASSIVE_SUPPORT_AUTHORITY_REV_A.csv
  mechanical_placement_authority: hardware/PCB_MAIN_MECHANICAL_PLACEMENT_AUTHORITY_REV_A.csv
  outline_mm: [110, 75]
  thickness_mm: 1.6
  layer_target: 6
  mounting_holes: 4x_M3_CLEARANCE_NPTH_D3.2
  production_pogo_pads: 31
  capture_readiness: COMPLETE
  passive_support_components: 211
  fitted_components: 196
  dnp_components: 15
  native_schematic: PRESENT_ERC_PASS_REVIEW_A_PASS
  review_a: PASS_SIGNED_COMMIT_35C9ED91
  native_layout: PLACEMENT_ENGINEERING_CANDIDATE_ROUTING_ABSENT
  provisional_footprints: 0
  review_b: OPEN_PLACEMENT_CANDIDATE_ROUTING_AND_EVIDENCE_PENDING
  ra_003:
    calculation: CLOSED
    layout: OPEN
    measurement: OPEN
    overall: OPEN
  production_bom: BLOCKED
positioning:
  station_type: fixed
  authoritative_source: configured_installation_coordinates
  firmware_module: zs_position_trust
  wifi_positioning: NOT_REQUIRED
  installation_position_storage: PORTABLE_ATOMIC_DUAL_SLOT_QG1_QG2_PASS_FLASH_BINDING_PENDING
  installation_position_ble_commissioning: PORTABLE_LOCAL_BLE_GUARD_QG1_QG2_PASS_NRF_GATT_PENDING
  configured_position_required_for_field_ready: true
  default_warning_distance_m: 25
  default_suspect_distance_m: 75
  default_gross_jump_distance_m: 250
  receiver_spoof_and_jam_monitoring: REQUIRED
  accelerometer_relocation_revalidation: REQUIRED
  time_trust_independent: true
  holdover_limit: MEASURE_DURING_EVT
  distance_calculation: DOUBLE_PRECISION_FROM_INTEGER_E7
time_sync:
  rmc_utc_date_and_epoch: IMPLEMENTED_HOST_TESTED
  pps_loss_detection: IMPLEMENTED_HOST_TESTED
  holdover_error_degradation: IMPLEMENTED_HOST_TESTED_1MS_PER_SECOND_CONSERVATIVE
  holdover_to_unsynced_limit_s: 120
  target_timer_capture_binding: MISSING_BLOCKER
  measured_holdover_limit: EVT_REQUIRED
lora_ru868:
  candidate_channels_hz: [864100000, 864300000, 864500000, 864700000, 864900000, 868900000, 869100000]
  legacy_868_1_to_868_7_plan: REMOVED_REJECTED_BY_FIRMWARE
  tx_enabled: false
  signed_profile_loader: MISSING_BLOCKER
  regulatory_and_rf_validation: REQUIRED
pinmap:
  source: hardware/EVT_PRE_20_PIN_MAP_REV_A.csv
  addenda: [hardware/AAD_CFG_PIN_ADDENDUM_REV_A.csv]
  status: SOURCE_AND_GENERATED_IOC_QG1_QG2_PASS_CUBEMX_OPEN_PENDING
  forbidden_absent_gpio: [PB12, PE1, PC4, PC5]
  notes: exact Q-package mapping; PA8 pin67/EXTI8 aggregated T5838 WAKE; PC2 pin17/EXTI2 LoRa DIO1 per DEC-022; PB15 pin54 LORA_TXEN and PD8 pin55 LORA_RXEN fail closed LOW per DEC-023; cellular PWRKEY RESET DTR EN_MODEM SIM_MUX_SEL and SIM_MUX_EN initialize LOW per DEC-033; PA15 pin77 shared THSEL/AAD_CFG output
  exti_unique_sources: [PC2_EXTI2_LORA_DIO1, PC6_EXTI6_ACCEL_INT, PC7_EXTI7_TAMPER_IN, PA8_EXTI8_MIC_WAKE]
target_contract:
  status: GENERATED_SOURCE_CONTRACT_QG1_QG2_PASS
  generator: tools/generate_evt_pre_20_target_contract.py
  board_header: firmware/targets/evt_pre_20/include/evt_pre_20_board_pins.h
  clock_header: firmware/targets/evt_pre_20/include/evt_pre_20_clock_policy.h
  manifest: firmware/targets/evt_pre_20/target_contract_manifest.json
  qg1_completeness: tools/validate_evt_pre_20_target_contract.py
  qg2_technical: tools/audit_evt_pre_20_target_technical.py
  release_effect: NONE_TARGET_PORT_STILL_REQUIRED
stm32_scaffold:
  status: PINNED_STARTUP_ENGINEERING_LINKER_QG1_QG2_PASS
  manifest: firmware/targets/evt_pre_20/stm32_scaffold_manifest.json
  stm32cubeu5_release: v1.9.0
  stm32cubeu5_commit: d88042df24f16799957c24f00c2b234c9e306188
  cmsis_device_u5_commit: 624374fa1e21ca195d6f2102ac0caaa50d0ea4c8
  startup: firmware/targets/evt_pre_20/vendor/cmsis_device_u5/startup_stm32u585xx.s
  system: firmware/targets/evt_pre_20/vendor/cmsis_device_u5/system_stm32u5xx.c
  linker: firmware/targets/evt_pre_20/ld/STM32U585VITXQ_ENGINEERING_FLASH.ld
  security_scope: TRUSTZONE_DISABLED_ENGINEERING_BRINGUP_ONLY
  qg1_completeness: tools/validate_evt_pre_20_stm32_scaffold.py
  qg2_technical: tools/audit_evt_pre_20_stm32_scaffold_technical.py
cubemx_preflight:
  status: GENERATED_PINOUT_IOC_CELLULAR_SAFE_DEFAULTS_QG1_QG2_PASS_CUBEMX_OPEN_REGENERATE_REQUIRED
  tool_version: 6.12.0
  database_tag: STM32CubeMX-DB.6.0.120
  database_commit: f4ec11f00e762e37ffc4020f6d4f20d225bc061d
  contract: firmware/targets/evt_pre_20/cubemx_generation_contract.json
  exact_ioc: firmware/targets/evt_pre_20/dioneya_evt_pre_20_rev_a.ioc
  qg1_completeness: tools/validate_evt_pre_20_cubemx_ioc.py
  qg2_technical: tools/audit_evt_pre_20_cubemx_ioc_technical.py
  release_effect: NONE_UNTIL_OPENED_AND_REGENERATED_WITH_LOCKED_CUBEMX
required_target_files:
  cubemx_ioc: GENERATED_FROM_LOCKED_CONTRACT_CUBEMX_OPEN_REGENERATE_BLOCKER
  startup: PINNED_OFFICIAL_CMSIS_QG1_QG2_PASS
  linker_script: ENGINEERING_FULL_FLASH_QG1_QG2_PASS_PRODUCTION_PARTITION_BLOCKER
  hal_ll_bindings: MISSING_BLOCKER
  dual_sim_gpio_power_binding: PORTABLE_EXACT_REV_A_GPIO_POLARITY_INTERLOCK_AND_OPTIONAL_FIXTURE_READBACK_INTERFACE_QG1_QG2_PASS_TARGET_HAL_U13_PHYSICAL_3V8_MODEM_PROVISIONED_CATALOG_AUDIT_AND_100_CYCLE_BLOCKER
  installation_position_flash_binding: MISSING_BLOCKER
  command_journal_flash_binding: PORTABLE_NOR_ERASE_ISOLATED_SHARED_NONOVERLAP_QG1_QG2_PASS_TARGET_SLOT_COUNT_OCTOSPI_ENDURANCE_BLOCKER
  event_outbox_storage_binding: PORTABLE_SHARED_THREE_CONSUMER_BINDING_PASS_EXACT_SLOT_COUNTS_OCTOSPI_ENDURANCE_BLOCKER
  event_outbox_nor_partition: PORTABLE_ARCHIVE_COMMAND_OUTBOX_NONOVERLAP_QG1_QG2_PASS_EXACT_SLOT_COUNTS_AND_TARGET_BINDING_BLOCKER
  command_journal_slot_count: MISSING_BLOCKER
  event_outbox_slot_count: MISSING_BLOCKER
  nor_octospi_binding: PORTABLE_W25Q512JV_PROBE_QG1_QG2_PASS_TARGET_OCTOSPI_AND_SAMPLE_BLOCKER
  mqtt_uart_session_binding: PORTABLE_BOUNDED_RAW_UART_FRAMER_SINGLE_TX_OWNER_QG1_QG2_PASS_TARGET_USART_DMA_ISR_CACHE_AND_MODEM_BLOCKER
  event_receipt_mqtt_binding: PORTABLE_LENGTH_ENABLED_BINARY_QMTRECV_SESSION_ROUTED_QG1_QG2_PASS_TARGET_USART_DMA_RETAIN_POLICY_AND_HARDWARE_BLOCKER
  event_mqtt_uplink_binding: PORTABLE_FIXED_LENGTH_BINARY_QMTPUB_SESSION_SERIALIZED_QG1_QG2_PASS_TARGET_USART_DMA_AND_HARDWARE_BLOCKER
  command_ed25519_backend: MISSING_BLOCKER
  command_mqtt_subscription_ack_binding: PORTABLE_BG95_SESSION_FRAMED_SERIALIZED_QG1_QG2_PASS_TARGET_USART_DMA_RETAIN_POLICY_AND_HARDWARE_BLOCKER
  board_pins: GENERATED_EXACT_REV_A_CONTRACT_QG1_QG2_PASS_CUBEMX_OPEN_PENDING
  secure_boot: MISSING_BLOCKER
  ota_ab: MISSING_BLOCKER
  production_build_manifest: MISSING_BLOCKER
release_outputs:
  elf: NOT_BUILT
  map: NOT_BUILT
  bin: NOT_BUILT
  hex: NOT_BUILT
  sha256: NOT_BUILT
  signature: NOT_BUILT
do_not_release: true
