skif-ops/rs-zs-bpla/tools/audit_pcb_main_capture_authority_rev_a.py

#!/usr/bin/env python3
"""Independent capture-input authority audit for EVT-PRE-20 PCB-MAIN Rev.A.

This gate proves that the complete pre-schematic capture inputs are internally
consistent. It does not claim
that Review A, Review B or the production BOM has passed.
"""
from __future__ import annotations

import argparse
import csv
import hashlib
import json
from pathlib import Path


ROOT = Path(__file__).resolve().parents[1]
STATUS_PATH = ROOT / "hardware/PCB_MAIN_CAPTURE_STATUS_REV_A.json"
PIN_MAP_PATH = ROOT / "hardware/EVT_PRE_20_PIN_MAP_REV_A.csv"
ADDENDUM_PATH = ROOT / "hardware/AAD_CFG_PIN_ADDENDUM_REV_A.csv"
HARNESS_PATH = ROOT / "hardware/HARNESS_LOGICAL_PINOUT_REV_A.csv"
MAIN_FREEZE_PATH = ROOT / "hardware/MAIN_COMPONENT_FREEZE_REV_A.csv"
CONNECTOR_FREEZE_PATH = ROOT / "hardware/CONNECTOR_FREEZE_REV_A.csv"
CAPTURE_SPEC_PATH = ROOT / "hardware/kicad/REV_A_CAPTURE_SPEC.md"
MCU_PIN_AUTHORITY_PATH = ROOT / "hardware/PCB_MAIN_MCU_PIN_AUTHORITY_REV_A.csv"
MCU_PIN_REVIEW_PATH = ROOT / "hardware/PCB_MAIN_MCU_PIN_AUTHORITY_REV_A.md"
STORAGE_SENSOR_PIN_AUTHORITY_PATH = ROOT / "hardware/PCB_MAIN_STORAGE_SENSOR_PIN_AUTHORITY_REV_A.csv"
STORAGE_SENSOR_REVIEW_PATH = ROOT / "hardware/PCB_MAIN_STORAGE_SENSOR_AUTHORITY_REV_A.md"
AUDIO_LOGIC_PIN_AUTHORITY_PATH = ROOT / "hardware/PCB_MAIN_AUDIO_LOGIC_PIN_AUTHORITY_REV_A.csv"
AUDIO_LOGIC_REVIEW_PATH = ROOT / "hardware/PCB_MAIN_AUDIO_LOGIC_AUTHORITY_REV_A.md"
CELLULAR_PIN_AUTHORITY_PATH = ROOT / "hardware/PCB_MAIN_CELLULAR_PIN_AUTHORITY_REV_A.csv"
CELLULAR_REVIEW_PATH = ROOT / "hardware/PCB_MAIN_CELLULAR_AUTHORITY_REV_A.md"
DUAL_SIM_PIN_AUTHORITY_PATH = ROOT / "hardware/PCB_MAIN_DUAL_SIM_PIN_AUTHORITY_REV_A.csv"
DUAL_SIM_REVIEW_PATH = ROOT / "hardware/PCB_MAIN_DUAL_SIM_AUTHORITY_REV_A.md"
GNSS_PIN_AUTHORITY_PATH = ROOT / "hardware/PCB_MAIN_GNSS_PIN_AUTHORITY_REV_A.csv"
GNSS_REVIEW_PATH = ROOT / "hardware/PCB_MAIN_GNSS_AUTHORITY_REV_A.md"
LORA_PIN_AUTHORITY_PATH = ROOT / "hardware/PCB_MAIN_LORA_PIN_AUTHORITY_REV_A.csv"
LORA_REVIEW_PATH = ROOT / "hardware/PCB_MAIN_LORA_AUTHORITY_REV_A.md"
BLE_PIN_AUTHORITY_PATH = ROOT / "hardware/PCB_MAIN_BLE_PIN_AUTHORITY_REV_A.csv"
BLE_REVIEW_PATH = ROOT / "hardware/PCB_MAIN_BLE_AUTHORITY_REV_A.md"
CONNECTOR_FIXTURE_PIN_AUTHORITY_PATH = ROOT / "hardware/PCB_MAIN_CONNECTOR_FIXTURE_PIN_AUTHORITY_REV_A.csv"
CONNECTOR_FIXTURE_REVIEW_PATH = ROOT / "hardware/PCB_MAIN_CONNECTOR_FIXTURE_AUTHORITY_REV_A.md"
PASSIVE_SUPPORT_AUTHORITY_PATH = ROOT / "hardware/PCB_MAIN_PASSIVE_SUPPORT_AUTHORITY_REV_A.csv"
PASSIVE_SUPPORT_REVIEW_PATH = ROOT / "hardware/PCB_MAIN_PASSIVE_SUPPORT_AUTHORITY_REV_A.md"
MECHANICAL_PLACEMENT_AUTHORITY_PATH = ROOT / "hardware/PCB_MAIN_MECHANICAL_PLACEMENT_AUTHORITY_REV_A.csv"
MECHANICAL_PLACEMENT_REVIEW_PATH = ROOT / "hardware/PCB_MAIN_MECHANICAL_PLACEMENT_AUTHORITY_REV_A.md"
DUAL_SIM_POLICY_PATH = ROOT / "hardware/DUAL_SIM_SINGLE_STANDBY.md"
AUDIO_INTERFACE_PATH = ROOT / "hardware/T5838_AAD_INTERFACE_REV_A.md"
POWER_ARCHITECTURE_PATH = ROOT / "hardware/EVT_PRE_20_POWER_ARCHITECTURE.md"
GROUND_DOMAIN_AUTHORITY_PATH = ROOT / "hardware/PCB_MAIN_GROUND_DOMAIN_AUTHORITY_REV_A.csv"
GROUND_DOMAIN_REVIEW_PATH = ROOT / "hardware/PCB_MAIN_GROUND_DOMAIN_AUTHORITY_REV_A.md"
NATIVE_NET_OVERLAY_PATH = ROOT / "hardware/PCB_MAIN_NATIVE_NET_OVERLAY_REV_A.csv"

EXPECTED_AUTHORITATIVE_INPUTS = {
    "config/EVT_PRE_20_BASELINE.yaml",
    "hardware/EVT_PRE_20_PIN_MAP_REV_A.csv",
    "hardware/AAD_CFG_PIN_ADDENDUM_REV_A.csv",
    "hardware/PCB_MAIN_MCU_PIN_AUTHORITY_REV_A.csv",
    "hardware/PCB_MAIN_MCU_PIN_AUTHORITY_REV_A.md",
    "hardware/PCB_MAIN_STORAGE_SENSOR_PIN_AUTHORITY_REV_A.csv",
    "hardware/PCB_MAIN_STORAGE_SENSOR_AUTHORITY_REV_A.md",
    "hardware/PCB_MAIN_AUDIO_LOGIC_PIN_AUTHORITY_REV_A.csv",
    "hardware/PCB_MAIN_AUDIO_LOGIC_AUTHORITY_REV_A.md",
    "hardware/PCB_MAIN_CELLULAR_PIN_AUTHORITY_REV_A.csv",
    "hardware/PCB_MAIN_CELLULAR_AUTHORITY_REV_A.md",
    "hardware/PCB_MAIN_DUAL_SIM_PIN_AUTHORITY_REV_A.csv",
    "hardware/PCB_MAIN_DUAL_SIM_AUTHORITY_REV_A.md",
    "hardware/PCB_MAIN_GNSS_PIN_AUTHORITY_REV_A.csv",
    "hardware/PCB_MAIN_GNSS_AUTHORITY_REV_A.md",
    "hardware/PCB_MAIN_LORA_PIN_AUTHORITY_REV_A.csv",
    "hardware/PCB_MAIN_LORA_AUTHORITY_REV_A.md",
    "hardware/PCB_MAIN_BLE_PIN_AUTHORITY_REV_A.csv",
    "hardware/PCB_MAIN_BLE_AUTHORITY_REV_A.md",
    "hardware/PCB_MAIN_CONNECTOR_FIXTURE_PIN_AUTHORITY_REV_A.csv",
    "hardware/PCB_MAIN_CONNECTOR_FIXTURE_AUTHORITY_REV_A.md",
    "hardware/PCB_MAIN_PASSIVE_SUPPORT_AUTHORITY_REV_A.csv",
    "hardware/PCB_MAIN_PASSIVE_SUPPORT_AUTHORITY_REV_A.md",
    "hardware/PCB_MAIN_MECHANICAL_PLACEMENT_AUTHORITY_REV_A.csv",
    "hardware/PCB_MAIN_MECHANICAL_PLACEMENT_AUTHORITY_REV_A.md",
    "hardware/PCB_MAIN_GROUND_DOMAIN_AUTHORITY_REV_A.csv",
    "hardware/PCB_MAIN_GROUND_DOMAIN_AUTHORITY_REV_A.md",
    "hardware/PCB_MAIN_IPC_CANDIDATE_FOOTPRINTS_REV_A.md",
    "hardware/PCB_MAIN_NATIVE_NET_OVERLAY_REV_A.csv",
    "hardware/HARNESS_LOGICAL_PINOUT_REV_A.csv",
    "hardware/MAIN_COMPONENT_FREEZE_REV_A.csv",
    "hardware/CONNECTOR_FREEZE_REV_A.csv",
    "hardware/CLOCKING_REV_A.md",
    "hardware/kicad/REV_A_CAPTURE_SPEC.md",
    "firmware/targets/evt_pre_20/dioneya_evt_pre_20_rev_a.ioc",
}
SUPERSEDED_INPUTS = {
    "hardware/kicad/components.csv",
    "hardware/kicad/nets.csv",
}
EXPECTED_MAIN_MPNS = {
    "U1": "STM32U585VIT6Q",
    "U2": "W25Q512JVFIQ",
    "U3": "LIS2DW12TR",
    "U4": "STTS22HTR",
    "U7": "SN74AXC8T245PWR",
    "U8": "BG95-M3",
    "U9": "MAX-M10S-00B",
    "U10": "E22-900M22S",
    "U11": "MDBT50Q-P1MV2",
    "U12": "SDCIT2/32GB",
    "U13": "TS3A27518EPWR",
    "U14": "ESDALC6V1-5P6",
    "U15": "ESDALC6V1-5P6",
    "U16": "SN74AXC8T245PWR",
    "U17": "SN74LVC32APWR",
    "U18": "SN74AXC1T45DRLR",
    "Q1": "MMBT3904,215",
    "Q2": "MMBT3904,215",
    "Q3": "MMBT3904,215",
    "X1": "SiT1552AI-JE-DCC-32.768D",
}
EXPECTED_MAIN_POWER = {
    "1": "3V8_MODEM",
    "2": "GND_MODEM",
    "3": "3V3_DIGITAL",
    "4": "GND_DIGITAL",
    "5": "1V8_MIC",
    "6": "GND_MIC",
    "7": "PWR_GOOD",
    "8": "FAULT",
    "9": "EN_MODEM",
    "10": "EN_AUX",
    "11": "I2C2_SCL",
    "12": "I2C2_SDA",
}
EXPECTED_SWD = {
    "1": "VTREF",
    "2": "SWDIO",
    "3": "SWCLK",
    "4": "NRST",
    "5": "GND",
}
EXPECTED_OPEN_AUTHORITY_IDS: set[str] = set()
EXPECTED_CLOSED_AUTHORITY_IDS = {f"MAIN-AUTH-{index:03d}" for index in range(1, 12)}
EXPECTED_DEVICE_METADATA = {
    "U2": ("W25Q512JVFIQ", "SOIC-16_300mil_F"),
    "U3": ("LIS2DW12TR", "LGA-12_2x2mm"),
    "U4": ("STTS22HTR", "UDFN-6L_2x2mm"),
}
EXPECTED_DEVICE_PIN_MAP = {
    "U2": {
        "1": ("/HOLD or /RESET (IO3)", "NOR_IO3", "FUNCTION_LOCKED"),
        "2": ("VCC", "3V3_DIGITAL", "SUPPLY_LOCKED"),
        "3": ("/RESET", "3V3_DIGITAL", "STRAP_DIRECT_HIGH"),
        "4": ("N/C", "NC", "DNU_NO_CONNECT"),
        "5": ("N/C", "NC", "DNU_NO_CONNECT"),
        "6": ("N/C", "NC", "DNU_NO_CONNECT"),
        "7": ("/CS", "NOR_NCS", "FUNCTION_LOCKED"),
        "8": ("DO (IO1)", "NOR_IO1", "FUNCTION_LOCKED"),
        "9": ("/WP (IO2)", "NOR_IO2", "FUNCTION_LOCKED"),
        "10": ("GND", "GND", "GROUND_LOCKED"),
        "11": ("N/C", "NC", "DNU_NO_CONNECT"),
        "12": ("N/C", "NC", "DNU_NO_CONNECT"),
        "13": ("N/C", "NC", "DNU_NO_CONNECT"),
        "14": ("N/C", "NC", "DNU_NO_CONNECT"),
        "15": ("DI (IO0)", "NOR_IO0", "FUNCTION_LOCKED"),
        "16": ("CLK", "NOR_CLK", "FUNCTION_LOCKED"),
    },
    "U3": {
        "1": ("SCL/SPC", "I2C2_SCL", "FUNCTION_LOCKED"),
        "2": ("CS", "3V3_DIGITAL", "STRAP_DIRECT_HIGH"),
        "3": ("SDO/SA0", "GND", "STRAP_DIRECT_LOW"),
        "4": ("SDA/SDI/SDO", "I2C2_SDA", "FUNCTION_LOCKED"),
        "5": ("NC", "NC", "NO_CONNECT"),
        "6": ("GND", "GND", "GROUND_LOCKED"),
        "7": ("RES", "GND", "RESERVED_DIRECT_LOW"),
        "8": ("GND", "GND", "GROUND_LOCKED"),
        "9": ("VDD", "3V3_DIGITAL", "SUPPLY_LOCKED"),
        "10": ("VDD_IO", "3V3_DIGITAL", "SUPPLY_LOCKED"),
        "11": ("INT2", "NC", "UNUSED_OUTPUT_NC"),
        "12": ("INT1", "ACCEL_INT", "FUNCTION_LOCKED"),
    },
    "U4": {
        "1": ("SCL", "I2C2_SCL", "FUNCTION_LOCKED"),
        "2": ("ALERT / INT", "NC", "UNUSED_OUTPUT_NC"),
        "3": ("VDD", "3V3_DIGITAL", "SUPPLY_LOCKED"),
        "4": ("Addr", "GND", "STRAP_DIRECT_LOW"),
        "5": ("GND", "GND", "GROUND_LOCKED"),
        "6": ("SDA", "I2C2_SDA", "FUNCTION_LOCKED"),
        "EP": ("Exposed pad", "NC", "MECHANICAL_PAD_NO_NET"),
    },
}
EXPECTED_AUDIO_METADATA = {
    "U7": ("SN74AXC8T245PWR", "TSSOP-24_PW"),
    "U17": ("SN74LVC32APWR", "TSSOP-14_PW"),
    "U18": ("SN74AXC1T45DRLR", "SOT-5X3-6_DRL"),
}
EXPECTED_AUDIO_PIN_MAP = {
    "U7": {
        "1": ("VCCA", "POWER", "1V8_MIC", "SUPPLY_LOCKED"),
        "2": ("DIR1", "INPUT", "1V8_MIC", "STRAP_DIRECT_HIGH"),
        "3": ("A1", "INPUT", "PDM_DATA1_1V8", "FUNCTION_LOCKED"),
        "4": ("A2", "INPUT", "PDM_DATA2_1V8", "FUNCTION_LOCKED"),
        "5": ("A3", "INPUT", "PDM_DATA3_1V8", "FUNCTION_LOCKED"),
        "6": ("A4", "INPUT", "PDM_DATA4_1V8", "FUNCTION_LOCKED"),
        "7": ("A5", "OUTPUT", "PDM_CLK_1V8", "FUNCTION_LOCKED"),
        "8": ("A6", "OUTPUT", "AAD_CFG_1V8", "FUNCTION_LOCKED"),
        "9": ("A7", "OUTPUT", "NC", "UNUSED_OUTPUT_NC"),
        "10": ("A8", "OUTPUT", "NC", "UNUSED_OUTPUT_NC"),
        "11": ("DIR2", "INPUT", "GND", "STRAP_DIRECT_LOW"),
        "12": ("GND", "POWER", "GND", "GROUND_LOCKED"),
        "13": ("GND", "POWER", "GND", "GROUND_LOCKED"),
        "14": ("B8", "INPUT", "GND", "UNUSED_INPUT_DIRECT_LOW"),
        "15": ("B7", "INPUT", "GND", "UNUSED_INPUT_DIRECT_LOW"),
        "16": ("B6", "INPUT", "AAD_CFG", "FUNCTION_LOCKED"),
        "17": ("B5", "INPUT", "PDM_CLK", "FUNCTION_LOCKED"),
        "18": ("B4", "OUTPUT", "PDM_DATA4", "FUNCTION_LOCKED"),
        "19": ("B3", "OUTPUT", "PDM_DATA3", "FUNCTION_LOCKED"),
        "20": ("B2", "OUTPUT", "PDM_DATA2", "FUNCTION_LOCKED"),
        "21": ("B1", "OUTPUT", "PDM_DATA1", "FUNCTION_LOCKED"),
        "22": ("OE", "INPUT", "GND", "STRAP_DIRECT_LOW"),
        "23": ("VCCB", "POWER", "3V3_DIGITAL", "SUPPLY_LOCKED"),
        "24": ("VCCB", "POWER", "3V3_DIGITAL", "SUPPLY_LOCKED"),
    },
    "U17": {
        "1": ("1A", "INPUT", "MIC_WAKE1", "FUNCTION_LOCKED"),
        "2": ("1B", "INPUT", "MIC_WAKE2", "FUNCTION_LOCKED"),
        "3": ("1Y", "OUTPUT", "MIC_WAKE12_OR_1V8", "FUNCTION_LOCKED"),
        "4": ("2A", "INPUT", "MIC_WAKE3", "FUNCTION_LOCKED"),
        "5": ("2B", "INPUT", "MIC_WAKE4", "FUNCTION_LOCKED"),
        "6": ("2Y", "OUTPUT", "MIC_WAKE34_OR_1V8", "FUNCTION_LOCKED"),
        "7": ("GND", "POWER", "GND", "GROUND_LOCKED"),
        "8": ("3Y", "OUTPUT", "MIC_WAKE_OR_1V8", "FUNCTION_LOCKED"),
        "9": ("3A", "INPUT", "MIC_WAKE12_OR_1V8", "FUNCTION_LOCKED"),
        "10": ("3B", "INPUT", "MIC_WAKE34_OR_1V8", "FUNCTION_LOCKED"),
        "11": ("4Y", "OUTPUT", "NC", "UNUSED_OUTPUT_NC"),
        "12": ("4A", "INPUT", "GND", "UNUSED_INPUT_DIRECT_LOW"),
        "13": ("4B", "INPUT", "GND", "UNUSED_INPUT_DIRECT_LOW"),
        "14": ("VCC", "POWER", "1V8_MIC", "SUPPLY_LOCKED"),
    },
    "U18": {
        "1": ("VCCA", "POWER", "1V8_MIC", "SUPPLY_LOCKED"),
        "2": ("GND", "POWER", "GND", "GROUND_LOCKED"),
        "3": ("A", "INPUT", "MIC_WAKE_OR_1V8", "FUNCTION_LOCKED"),
        "4": ("B", "OUTPUT", "MIC_WAKE", "FUNCTION_LOCKED"),
        "5": ("DIR", "INPUT", "1V8_MIC", "STRAP_DIRECT_HIGH"),
        "6": ("VCCB", "POWER", "3V3_DIGITAL", "SUPPLY_LOCKED"),
    },
}

EXPECTED_PACKAGE_PIN_NAMES = {
    index: name
    for index, name in enumerate(
        """PE2
PE3
PE4
PE5
PE6
VBAT
PC13
PC14-OSC32_IN (PC14)
PC15-OSC32_OUT (PC15)
VSS
VDD
PH0-OSC_IN (PH0)
PH1-OSC_OUT (PH1)
NRST
PC0
PC1
PC2
PC3
VSSA
VREF+
VDDA
PA0
PA1
PA2
PA3
VSS
VDD
PA4
PA5
PA6
PA7
PB0
PB1
PB2
PE7
PE8
PE9
PE10
PE11
PE12
PE13
PE14
PE15
PB10
PB11
VLXSMPS
VDDSMPS
VSSSMPS
VDD11
VSS
VDD
PB13
PB14
PB15
PD8
PD9
PD10
PD11
PD12
PD13
PD14
PD15
PC6
PC7
PC8
PC9
PA8
PA9
PA10
PA11
PA12
PA13 (JTMS/SWDIO)
VDDUSB
VSS
VDD
PA14 (JTCK/SWCLK)
PA15 (JTDI)
PC10
PC11
PC12
PD0
PD1
PD2
PD3
PD4
PD5
PD6
PD7
PB3 (JTDO/TRACESWO)
PB4 (NJTRST)
PB5
PB6
PB7
PH3-BOOT0
PB8
PB9
PE0
VDD11
VSS
VDD""".splitlines(),
        start=1,
    )
}
EXPECTED_POWER_PINS = {
    6: ("POWER_IN", "3V3_DIGITAL", "SUPPLY_LOCKED"),
    10: ("GROUND", "GND", "GROUND_LOCKED"),
    11: ("POWER_IN", "3V3_DIGITAL", "SUPPLY_LOCKED"),
    19: ("GROUND", "GND", "GROUND_LOCKED"),
    20: ("REFERENCE_IN", "3V3_DIGITAL", "REFERENCE_LOCKED"),
    21: ("POWER_IN", "3V3_DIGITAL", "SUPPLY_LOCKED"),
    26: ("GROUND", "GND", "GROUND_LOCKED"),
    27: ("POWER_IN", "3V3_DIGITAL", "SUPPLY_LOCKED"),
    46: ("POWER_SWITCH", "SMPS_SW", "SMPS_LOCKED"),
    47: ("POWER_IN", "3V3_DIGITAL", "SMPS_LOCKED"),
    48: ("GROUND", "GND", "GROUND_LOCKED"),
    49: ("POWER_OUT", "VCORE_1V1", "SMPS_LOCKED"),
    50: ("GROUND", "GND", "GROUND_LOCKED"),
    51: ("POWER_IN", "3V3_DIGITAL", "SUPPLY_LOCKED"),
    73: ("POWER_IN", "3V3_DIGITAL", "SUPPLY_LOCKED"),
    74: ("GROUND", "GND", "GROUND_LOCKED"),
    75: ("POWER_IN", "3V3_DIGITAL", "SUPPLY_LOCKED"),
    98: ("POWER_OUT", "VCORE_1V1", "SMPS_LOCKED"),
    99: ("GROUND", "GND", "GROUND_LOCKED"),
    100: ("POWER_IN", "3V3_DIGITAL", "SUPPLY_LOCKED"),
}
EXPECTED_UNUSED_IO = {
    12: "HSE_FORBIDDEN_NC",
    13: "HSE_FORBIDDEN_NC",
    18: "UNUSED_GPIO_NC",
    23: "UNUSED_GPIO_NC",
    32: "UNUSED_GPIO_NC",
    36: "UNUSED_GPIO_NC",
    69: "UNUSED_GPIO_NC",
    84: "UNUSED_GPIO_NC",
    88: "UNUSED_GPIO_NC",
    89: "JTAG_TRACE_UNUSED_NC",
    90: "JTAG_UNUSED_NC",
    91: "UNUSED_GPIO_NC",
}


def rows(path: Path) -> list[dict[str, str]]:
    with path.open(encoding="utf-8-sig", newline="") as source:
        return list(csv.DictReader(source))


def require(condition: bool, message: str) -> None:
    if not condition:
        raise AssertionError(message)


def interface(rows_: list[dict[str, str]], name: str) -> list[dict[str, str]]:
    return [row for row in rows_ if row["Interface"] == name]


def pin_contract(rows_: list[dict[str, str]]) -> dict[str, str]:
    return {row["Pin"]: row["Net"] for row in rows_}


def main() -> None:
    parser = argparse.ArgumentParser()
    parser.add_argument(
        "--output",
        type=Path,
        default=ROOT / "artifacts/pcb_main_capture_authority_rev_a.json",
    )
    args = parser.parse_args()

    status = json.loads(STATUS_PATH.read_text(encoding="utf-8"))
    require(status["schema_version"] == 1, "PCB-MAIN status schema mismatch")
    require(status["configuration"] == "EVT-PRE-20 Rev.A", "configuration mismatch")
    require(status["assembly"] == "PCB-MAIN", "assembly mismatch")
    require(status["release_state"] in {"CAPTURE_INPUT", "SCHEMATIC_REVIEW", "REVIEW_A_PASS"},
            "invalid PCB-MAIN capture/review state")
    require(status["manufacturing_release"] is False, "PCB-MAIN must remain blocked")

    source_control = status["source_control"]
    authoritative = set(source_control["authoritative_inputs"])
    superseded = set(source_control["superseded_do_not_use"])
    require(authoritative == EXPECTED_AUTHORITATIVE_INPUTS, "PCB-MAIN authoritative input set drift")
    require(superseded == SUPERSEDED_INPUTS, "PCB-MAIN superseded input set drift")
    require(authoritative.isdisjoint(superseded), "superseded input marked authoritative")
    for relative in authoritative | superseded:
        require((ROOT / relative).is_file(), f"registered source file missing: {relative}")

    capture_spec = CAPTURE_SPEC_PATH.read_text(encoding="utf-8")
    for relative in sorted(SUPERSEDED_INPUTS):
        require(relative in capture_spec, f"capture spec does not identify superseded source: {relative}")
    require("must not be used" in capture_spec, "capture spec lacks explicit stale-source prohibition")
    workflow_text = (ROOT / ".github/workflows/pcb-native.yml").read_text(encoding="utf-8")
    pcb_main_generators = list((ROOT / "tools").glob("generate_pcb_main*.py"))
    live_capture_implementation = workflow_text + "\n".join(
        path.read_text(encoding="utf-8") for path in pcb_main_generators
    )
    for relative in sorted(SUPERSEDED_INPUTS):
        require(relative not in live_capture_implementation, f"live PCB-MAIN capture implementation references superseded source: {relative}")

    freeze = rows(MAIN_FREEZE_PATH)
    by_ref = {row["RefDes"]: row for row in freeze}
    require(len(by_ref) == len(freeze), "duplicate PCB-MAIN freeze RefDes")
    require(set(by_ref) == set(EXPECTED_MAIN_MPNS), "PCB-MAIN active RefDes set drift")
    for ref, mpn in EXPECTED_MAIN_MPNS.items():
        require(by_ref[ref]["Assembly"] == "PCB-MAIN", f"{ref} assembly mismatch")
        require(by_ref[ref]["MPN"] == mpn, f"{ref} MPN mismatch")
        require(by_ref[ref]["Package_or_Module"], f"{ref} package is empty")
        require(by_ref[ref]["Status"], f"{ref} selection status is empty")

    base = rows(PIN_MAP_PATH)
    addendum = rows(ADDENDUM_PATH)
    require(len(base) == 66, f"expected 66 base MCU assignments, got {len(base)}")
    require(len(addendum) == 1 and addendum[0]["Net"] == "AAD_CFG", "AAD_CFG addendum mismatch")
    mcu_pins = base + addendum
    require(len(mcu_pins) == status["mcu_contract"]["functional_assignment_count"] == 67, "MCU assignment count mismatch")
    for field in ("Net", "MCU_Pin", "LQFP100_Pin"):
        values = [row[field] for row in mcu_pins]
        require(len(values) == len(set(values)), f"MCU pin authority has duplicate {field}")
    by_net = {row["Net"]: row for row in mcu_pins}
    critical = {
        "PDM_CLK": ("PE9", "37"),
        "MIC_WAKE": ("PA8", "67"),
        "AAD_CFG": ("PA15", "77"),
        "LORA_DIO1": ("PC2", "17"),
        "LORA_TXEN": ("PB15", "54"),
        "LORA_RXEN": ("PD8", "55"),
        "BLE_TX": ("PB10", "44"),
        "BLE_RX": ("PB11", "45"),
        "BLE_EN": ("PE6", "5"),
        "BLE_DFU_REQ": ("PB2", "34"),
        "I2C2_SCL": ("PB13", "52"),
        "I2C2_SDA": ("PB14", "53"),
        "USB_DM": ("PA11", "70"),
        "USB_DP": ("PA12", "71"),
        "LSE_IN": ("PC14", "8"),
        "LSE_OUT": ("PC15", "9"),
    }
    for net, expected in critical.items():
        require(net in by_net, f"critical MCU net missing: {net}")
        require((by_net[net]["MCU_Pin"], by_net[net]["LQFP100_Pin"]) == expected, f"{net} pin mismatch")
    require({by_net[f"PDM_DATA{i}"]["MCU_Pin"] for i in range(1, 5)} == {"PB1", "PD6", "PE7", "PE4"}, "four-channel PDM map mismatch")
    require({"PB12", "PE1", "PC4", "PC5"}.isdisjoint(row["MCU_Pin"] for row in mcu_pins), "absent Q-package pin used")

    # Independent full-package control. The expected package list is copied from
    # the pinned ST CubeMX STM32U585VITxQ LQFP100_SMPS definition rather than
    # derived from this CSV, so a shifted or omitted position is detectable.
    authority_rows = rows(MCU_PIN_AUTHORITY_PATH)
    expected_columns = {
        "LQFP100_Pin", "Pin_Name", "Pin_Type", "RevA_Net",
        "Disposition", "Authority", "Notes",
    }
    require(len(authority_rows) == 100, f"expected 100 U1 package positions, got {len(authority_rows)}")
    require(all(set(row) == expected_columns for row in authority_rows), "U1 pin-authority schema drift")
    authority_by_pin: dict[int, dict[str, str]] = {}
    for row in authority_rows:
        try:
            position = int(row["LQFP100_Pin"])
        except ValueError as exc:
            raise AssertionError(f"non-numeric U1 package position: {row['LQFP100_Pin']}") from exc
        require(position not in authority_by_pin, f"duplicate U1 package position: {position}")
        authority_by_pin[position] = row
    require(set(authority_by_pin) == set(range(1, 101)), "U1 package positions are not exactly 1..100")
    for position, expected_name in EXPECTED_PACKAGE_PIN_NAMES.items():
        row = authority_by_pin[position]
        require(row["Pin_Name"] == expected_name, f"U1 position {position} pin-name mismatch")
        expected_type = EXPECTED_POWER_PINS.get(position, ("RESET" if position == 14 else "IO", "", ""))[0]
        require(row["Pin_Type"] == expected_type, f"U1 position {position} pin-type mismatch")

    functional_by_position = {int(row["LQFP100_Pin"]): row for row in mcu_pins}
    require(len(functional_by_position) == 67, "functional U1 position count mismatch")
    for position, source_row in functional_by_position.items():
        authority_row = authority_by_pin[position]
        if position == 9:
            require(source_row["Net"] == "LSE_OUT", "source PC15 role drift")
            require(
                authority_row["RevA_Net"] == "NC"
                and authority_row["Disposition"] == "FUNCTION_RESERVED_EXTERNAL_NC",
                "PC15 must be reserved by RCC but externally NC",
            )
        else:
            require(authority_row["RevA_Net"] == source_row["Net"], f"U1 position {position} functional-net mismatch")
            require(authority_row["Disposition"] == "FUNCTION_LOCKED", f"U1 position {position} functional disposition mismatch")

    actual_unused = {
        position: row["Disposition"]
        for position, row in authority_by_pin.items()
        if row["RevA_Net"] == "NC" and position != 9
    }
    require(actual_unused == EXPECTED_UNUSED_IO, "U1 explicit unused-I/O disposition mismatch")
    for position, expected in EXPECTED_POWER_PINS.items():
        row = authority_by_pin[position]
        require(
            (row["Pin_Type"], row["RevA_Net"], row["Disposition"]) == expected,
            f"U1 position {position} power/reference disposition mismatch",
        )
    require(
        (authority_by_pin[14]["RevA_Net"], authority_by_pin[14]["Disposition"])
        == ("NRST", "RESET_LOCKED"),
        "U1 NRST disposition mismatch",
    )
    covered_positions = set(functional_by_position) | set(EXPECTED_UNUSED_IO) | {14} | set(EXPECTED_POWER_PINS)
    require(covered_positions == set(range(1, 101)), "U1 package-accounting categories do not cover exactly 100 positions")
    require(sum(row["Pin_Name"] == "VDD" for row in authority_rows) == 5, "U1 VDD pin count mismatch")
    require(sum(row["Pin_Name"] == "VSS" for row in authority_rows) == 5, "U1 VSS pin count mismatch")
    require(sum(row["Pin_Name"] == "VDD11" for row in authority_rows) == 2, "U1 VDD11 pin count mismatch")

    pin_review = MCU_PIN_REVIEW_PATH.read_text(encoding="utf-8")
    review_markers = {
        "PIN_AUTHORITY_PASS / PCB REVIEW A NOT STARTED / NOT FOR MANUFACTURE",
        "f4ec11f00e762e37ffc4020f6d4f20d225bc061d",
        "4349055dfd06e6eb2dce1a440c44a995ad7c924e28435ede119a7d4bb10f556d",
        "6483871075d4889d39356648a9c1f1fb34f48dce2ce3e8c5a8d73a73f7e935e3",
        "No HSE is fitted",
        "VREFBUF disabled",
        "67 locked functional assignments",
        "PB15 / package pin 54",
        "PD8 / package pin 55",
        "2.2 uH",
        "2 x 2.2 uF",
        "10 uF",
        "does not release the native PCB-MAIN schematic",
    }
    for marker in review_markers:
        require(marker in pin_review, f"U1 pin-authority review record missing marker: {marker}")

    device_rows = rows(STORAGE_SENSOR_PIN_AUTHORITY_PATH)
    device_columns = {
        "RefDes", "MPN", "Package", "Pin", "Pin_Name", "Direction",
        "RevA_Net", "Disposition", "Required_Network", "Authority", "Notes",
    }
    require(len(device_rows) == 35, f"expected 35 U2/U3/U4 physical pin or pad rows, got {len(device_rows)}")
    require(all(set(row) == device_columns for row in device_rows), "U2/U3/U4 pin-authority schema drift")
    require(
        all(all(row[column] is not None and row[column] != "" for column in device_columns) for row in device_rows),
        "U2/U3/U4 pin-authority row contains an empty field",
    )
    device_by_key: dict[tuple[str, str], dict[str, str]] = {}
    for row in device_rows:
        key = (row["RefDes"], row["Pin"])
        require(key not in device_by_key, f"duplicate device pin-authority row: {key[0]}.{key[1]}")
        device_by_key[key] = row
    expected_device_keys = {
        (ref, pin)
        for ref, pin_map in EXPECTED_DEVICE_PIN_MAP.items()
        for pin in pin_map
    }
    require(set(device_by_key) == expected_device_keys, "U2/U3/U4 physical pin set drift")
    for ref, expected_pin_map in EXPECTED_DEVICE_PIN_MAP.items():
        expected_mpn, expected_package = EXPECTED_DEVICE_METADATA[ref]
        for pin, expected in expected_pin_map.items():
            row = device_by_key[(ref, pin)]
            require((row["MPN"], row["Package"]) == (expected_mpn, expected_package), f"{ref}.{pin} identity/package mismatch")
            require((row["Pin_Name"], row["RevA_Net"], row["Disposition"]) == expected, f"{ref}.{pin} pin/net/disposition mismatch")

    required_nor_nets = {"NOR_CLK", "NOR_NCS", "NOR_IO0", "NOR_IO1", "NOR_IO2", "NOR_IO3"}
    require(required_nor_nets.issubset(by_net), "MCU functional map lacks the complete U2 OCTOSPI bus")
    require(
        {row["RevA_Net"] for row in device_rows if row["RefDes"] == "U2"} - {"NC", "3V3_DIGITAL", "GND"}
        == required_nor_nets,
        "U2 OCTOSPI endpoint set mismatch",
    )
    require(device_by_key[("U2", "2")]["Required_Network"] == "100 nF plus 1 uF local decoupling", "U2 decoupling contract mismatch")
    require("10 kOhm pull-up" in device_by_key[("U2", "7")]["Required_Network"], "U2 chip-select power-transition pull-up missing")
    require(device_by_key[("U2", "3")]["Required_Network"] == "Direct tie to 3V3_DIGITAL", "U2 dedicated reset strap mismatch")

    require({"I2C2_SCL", "I2C2_SDA", "ACCEL_INT"}.issubset(by_net), "MCU functional map lacks sensor endpoints")
    require("0x18" in device_by_key[("U3", "3")]["Notes"], "U3 address 0x18 evidence missing")
    require(device_by_key[("U3", "2")]["RevA_Net"] == "3V3_DIGITAL", "U3 is not hard-strapped to I2C mode")
    require(device_by_key[("U3", "7")]["RevA_Net"] == "GND", "U3 reserved pin is not grounded")
    require("100 nF plus 10 uF" in device_by_key[("U3", "9")]["Required_Network"], "U3 VDD decoupling mismatch")
    require("100 nF" in device_by_key[("U3", "10")]["Required_Network"], "U3 VDD_IO decoupling mismatch")
    require("0x3F" in device_by_key[("U4", "4")]["Notes"], "U4 address 0x3F evidence missing")
    require("100 nF" in device_by_key[("U4", "3")]["Required_Network"], "U4 VDD decoupling mismatch")
    require(device_by_key[("U4", "EP")]["RevA_Net"] == "NC", "U4 unnumbered exposed pad unexpectedly has an electrical net")
    i2c_addresses = {"LIS2DW12": 0x18, "STTS22H": 0x3F, "INA226": 0x40}
    require(len(i2c_addresses.values()) == len(set(i2c_addresses.values())), "Rev.A I2C2 address collision")

    device_review = STORAGE_SENSOR_REVIEW_PATH.read_text(encoding="utf-8")
    device_review_markers = {
        "DEVICE_AUTHORITY_PASS / PCB REVIEW A NOT STARTED / NOT FOR MANUFACTURE",
        "a898962af314ca90719eadba732e7f5fd42a1c48c4bfd283062c403d1c27bfd0",
        "5208623aa91c63a33be0e930518c20f5210c4eb76932350f35369687ae1d0dd5",
        "4dc419fabe93f7f0b1ee5730967ed74573aa0dc91188cf88749ce10d5ab4a34e",
        "3f6937595517c4f738021037942e7d19d5b7c84cfe4e9b7e8635fcc06ff783fe",
        "factory default `QE=1`",
        "exact 4-byte geometry",
        "0x18",
        "0x3F",
        "0x40",
        "2.2 kOhm, 1%",
        "0.746 us",
        "1.32 mA",
        "22 Ohm series-damping",
        "Initial bus speed is 100 kHz",
        "does not release the native PCB-MAIN schematic",
    }
    for marker in device_review_markers:
        require(marker in device_review, f"U2/U3/U4 authority review record missing marker: {marker}")

    audio_rows = rows(AUDIO_LOGIC_PIN_AUTHORITY_PATH)
    audio_columns = {
        "RefDes", "MPN", "Package", "Pin", "Pin_Name", "Direction",
        "RevA_Net", "Disposition", "Required_Network", "Authority", "Notes",
    }
    require(len(audio_rows) == 44, f"expected 44 U7/U17/U18 physical pins, got {len(audio_rows)}")
    require(all(set(row) == audio_columns for row in audio_rows), "U7/U17/U18 pin-authority schema drift")
    require(
        all(all(row[column] is not None and row[column] != "" for column in audio_columns) for row in audio_rows),
        "U7/U17/U18 pin-authority row contains an empty field",
    )
    audio_by_key: dict[tuple[str, str], dict[str, str]] = {}
    for row in audio_rows:
        key = (row["RefDes"], row["Pin"])
        require(key not in audio_by_key, f"duplicate audio pin-authority row: {key[0]}.{key[1]}")
        audio_by_key[key] = row
    expected_audio_keys = {
        (ref, pin)
        for ref, pin_map in EXPECTED_AUDIO_PIN_MAP.items()
        for pin in pin_map
    }
    require(set(audio_by_key) == expected_audio_keys, "U7/U17/U18 physical pin set drift")
    for ref, expected_pin_map in EXPECTED_AUDIO_PIN_MAP.items():
        expected_mpn, expected_package = EXPECTED_AUDIO_METADATA[ref]
        for pin, expected in expected_pin_map.items():
            row = audio_by_key[(ref, pin)]
            require((row["MPN"], row["Package"]) == (expected_mpn, expected_package), f"{ref}.{pin} identity/package mismatch")
            actual = (row["Pin_Name"], row["Direction"], row["RevA_Net"], row["Disposition"])
            require(actual == expected, f"{ref}.{pin} pin/direction/net/disposition mismatch")

    for index, a_pin, b_pin in ((1, "3", "21"), (2, "4", "20"), (3, "5", "19"), (4, "6", "18")):
        require(audio_by_key[("U7", a_pin)]["RevA_Net"] == f"PDM_DATA{index}_1V8", f"U7 PDM data {index} A-port mismatch")
        require(audio_by_key[("U7", b_pin)]["RevA_Net"] == f"PDM_DATA{index}", f"U7 PDM data {index} B-port mismatch")
        require("no external pull" in audio_by_key[("U7", a_pin)]["Required_Network"], f"U7 PDM data {index} external-pull prohibition missing")
    require(audio_by_key[("U7", "2")]["Required_Network"] == "Direct tie to 1V8_MIC", "U7 DIR1 strap mismatch")
    require(audio_by_key[("U7", "11")]["Required_Network"] == "Direct tie to GND", "U7 DIR2 strap mismatch")
    require(audio_by_key[("U7", "22")]["Required_Network"] == "Direct tie to GND", "U7 OE strap mismatch")
    require({audio_by_key[("U7", pin)]["RevA_Net"] for pin in ("14", "15")} == {"GND"}, "U7 unused input state mismatch")
    require({audio_by_key[("U7", pin)]["RevA_Net"] for pin in ("9", "10")} == {"NC"}, "U7 unused output state mismatch")
    for ref, pin in (("U7", "1"), ("U7", "23"), ("U7", "24"), ("U17", "14"), ("U18", "1"), ("U18", "6")):
        require("100 nF" in audio_by_key[(ref, pin)]["Required_Network"], f"{ref}.{pin} local bypass contract missing")

    wake_inputs = {"1": "MIC_WAKE1", "2": "MIC_WAKE2", "4": "MIC_WAKE3", "5": "MIC_WAKE4"}
    for pin, net in wake_inputs.items():
        row = audio_by_key[("U17", pin)]
        require(row["RevA_Net"] == net, f"U17 input {pin} wake-net mismatch")
        require("100 kOhm pull-down" in row["Required_Network"] and "test point" in row["Required_Network"], f"U17 input {pin} safe-state/test-point network mismatch")
    require(
        audio_by_key[("U17", "3")]["RevA_Net"] == audio_by_key[("U17", "9")]["RevA_Net"] == "MIC_WAKE12_OR_1V8",
        "U17 first pair OR interconnect mismatch",
    )
    require(
        audio_by_key[("U17", "6")]["RevA_Net"] == audio_by_key[("U17", "10")]["RevA_Net"] == "MIC_WAKE34_OR_1V8",
        "U17 second pair OR interconnect mismatch",
    )
    require(
        audio_by_key[("U17", "8")]["RevA_Net"] == audio_by_key[("U18", "3")]["RevA_Net"] == "MIC_WAKE_OR_1V8",
        "U17-to-U18 aggregate wake interconnect mismatch",
    )
    require({audio_by_key[("U17", pin)]["RevA_Net"] for pin in ("12", "13")} == {"GND"}, "U17 unused inputs are not grounded")
    require(audio_by_key[("U17", "11")]["RevA_Net"] == "NC", "U17 unused output is not NC")
    require(audio_by_key[("U18", "5")]["Required_Network"] == "Direct tie to 1V8_MIC", "U18 DIR strap mismatch")
    require("100 kOhm pull-down" in audio_by_key[("U18", "4")]["Required_Network"], "U18 MCU-side wake pull-down missing")
    require(
        {audio_by_key[("U7", pin)]["RevA_Net"] for pin in ("16", "17", "18", "19", "20", "21")}
        == {"AAD_CFG", "PDM_CLK", "PDM_DATA1", "PDM_DATA2", "PDM_DATA3", "PDM_DATA4"},
        "U7 MCU-side endpoint set mismatch",
    )
    require(audio_by_key[("U18", "4")]["RevA_Net"] == "MIC_WAKE", "U18 MCU-side wake endpoint mismatch")

    audio_review = AUDIO_LOGIC_REVIEW_PATH.read_text(encoding="utf-8")
    authority_sha256 = hashlib.sha256(AUDIO_LOGIC_PIN_AUTHORITY_PATH.read_bytes()).hexdigest()
    audio_review_markers = {
        "AUDIO_LOGIC_AUTHORITY_PASS / PCB REVIEW A NOT STARTED / NOT FOR MANUFACTURE",
        authority_sha256,
        "6cf4003c438c0546fb86f0932613896197dd19a75bdb307f385eb6e75535126e",
        "807f6fff7977736035c2a3144d530be7ad737a163b2f0fd11002a45953b47230",
        "41e03bd8f0740ae8bbdf92309e7c82bac1359a768556cbe68de41b0273e49f12",
        "5befb710bfe7a415cdc1aba41ebc18b484d7f9fc320ce15a7481507531cf58a4",
        "DIR1=HIGH",
        "DIR2=LOW",
        "OE=LOW",
        "288 kOhm",
        "No external pull-up or pull-down",
        "100 kOhm pull-down",
        "does not release native PCB-MAIN capture",
    }
    for marker in audio_review_markers:
        require(marker in audio_review, f"U7/U17/U18 authority review record missing marker: {marker}")
    audio_interface = AUDIO_INTERFACE_PATH.read_text(encoding="utf-8")
    power_architecture = POWER_ARCHITECTURE_PATH.read_text(encoding="utf-8")
    for marker in ("DIR1=HIGH", "DIR2=LOW", "OE=LOW", "44-pin", "no external pull-up or pull-down"):
        require(marker in audio_interface, f"T5838 interface document missing frozen audio-logic marker: {marker}")
    require("disabled/high-Z state" not in power_architecture, "power architecture still requires U7 disable in S0")
    require("фиксированном `OE=LOW`" in power_architecture, "power architecture lacks frozen U7 S0 state")

    cellular_rows = rows(CELLULAR_PIN_AUTHORITY_PATH)
    cellular_columns = {
        "RefDes", "MPN", "Package", "Pin", "Pin_Name", "Direction",
        "RevA_Net", "Disposition", "Required_Network", "Authority", "Notes",
    }
    require(len(cellular_rows) == 132, f"expected 132 U8/U16/Q1/Q2 physical pins, got {len(cellular_rows)}")
    require(all(set(row) == cellular_columns for row in cellular_rows), "cellular pin-authority schema drift")
    require(
        all(all(row[column] is not None and row[column] != "" for column in cellular_columns) for row in cellular_rows),
        "cellular pin-authority row contains an empty field",
    )
    cellular_by_key: dict[tuple[str, str], dict[str, str]] = {}
    for row in cellular_rows:
        key = (row["RefDes"], row["Pin"])
        require(key not in cellular_by_key, f"duplicate cellular pin-authority row: {key[0]}.{key[1]}")
        cellular_by_key[key] = row
    cellular_identity = {
        "U8": ("BG95-M3", "LGA-102_23.6x19.9mm", {str(index) for index in range(1, 103)}),
        "U16": ("SN74AXC8T245PWR", "TSSOP-24_PW", {str(index) for index in range(1, 25)}),
        "Q1": ("MMBT3904,215", "SOT23", {"1", "2", "3"}),
        "Q2": ("MMBT3904,215", "SOT23", {"1", "2", "3"}),
    }
    for ref, (mpn, package, expected_pins) in cellular_identity.items():
        actual = [row for row in cellular_rows if row["RefDes"] == ref]
        require({row["Pin"] for row in actual} == expected_pins, f"{ref} cellular package-position set drift")
        require(all((row["MPN"], row["Package"]) == (mpn, package) for row in actual), f"{ref} cellular identity/package mismatch")

    u8 = {index: cellular_by_key[("U8", str(index))] for index in range(1, 103)}
    expected_u8_ground_pins = {
        3, 31, 48, 50, 54, 55, 58, 59, 61, 62,
        *range(67, 75), *range(79, 83), *range(89, 92), *range(100, 103),
    }
    require({index for index, row in u8.items() if row["Pin_Name"] == "GND"} == expected_u8_ground_pins, "U8 ground-pad set drift")
    require(
        all((u8[index]["RevA_Net"], u8[index]["Disposition"]) == ("GND_MODEM", "GROUND_LOCKED") for index in expected_u8_ground_pins),
        "U8 ground-pad net/disposition mismatch",
    )
    expected_u8_critical = {
        15: ("PWRKEY", "U8_PWRKEY_N", "FUNCTION_LOCKED"),
        17: ("RESET_N", "U8_RESET_N", "FUNCTION_LOCKED"),
        20: ("STATUS", "U8_STATUS_1V8", "FUNCTION_LOCKED"),
        29: ("VDD_EXT", "U8_VDD_EXT_1V8", "SUPPLY_OUTPUT_LOCKED"),
        30: ("MAIN_DTR", "U8_MAIN_DTR_1V8", "FUNCTION_LOCKED"),
        32: ("VBAT_BB", "3V8_MODEM_BB", "SUPPLY_LOCKED"),
        33: ("VBAT_BB", "3V8_MODEM_BB", "SUPPLY_LOCKED"),
        34: ("MAIN_RXD", "U8_MAIN_RXD_1V8", "FUNCTION_LOCKED"),
        35: ("MAIN_TXD", "U8_MAIN_TXD_1V8", "FUNCTION_LOCKED"),
        39: ("MAIN_RI", "U8_MAIN_RI_1V8", "FUNCTION_LOCKED"),
        43: ("USIM_VDD", "CELL_USIM_VDD_1V8", "FUNCTION_LOCKED"),
        44: ("USIM_RST", "CELL_USIM_RST_1V8", "FUNCTION_LOCKED"),
        45: ("USIM_DATA", "CELL_USIM_DATA_1V8", "FUNCTION_LOCKED"),
        46: ("USIM_CLK", "CELL_USIM_CLK_1V8", "FUNCTION_LOCKED"),
        47: ("USIM_GND", "GND_MODEM", "GROUND_LOCKED"),
        52: ("VBAT_RF", "3V8_MODEM_RF", "SUPPLY_LOCKED"),
        53: ("VBAT_RF", "3V8_MODEM_RF", "SUPPLY_LOCKED"),
    }
    for pin, expected in expected_u8_critical.items():
        require((u8[pin]["Pin_Name"], u8[pin]["RevA_Net"], u8[pin]["Disposition"]) == expected, f"U8 pad {pin} critical mapping mismatch")
    for pin in (11, 12, 13, 14, 16, 57, 63, 76, 77, 78, 92, 93, 94, 95, 97, 98, 99):
        require((u8[pin]["RevA_Net"], u8[pin]["Disposition"]) == ("NC", "RESERVED_DNU_NC"), f"U8 reserved pad {pin} is not DNU/NC")
    require((u8[42]["RevA_Net"], u8[42]["Disposition"]) == ("NC", "UNUSED_INPUT_NC"), "U8 module-level USIM_DET must remain NC")
    for pin in (8, 9, 10, 22, 23, 75):
        require(u8[pin]["Disposition"] == "FIXTURE_ENDPOINT_LOCKED", f"U8 recovery pad {pin} endpoint mismatch")
    require(u8[60]["Disposition"] == "RF_ENDPOINT_LOCKED", "U8 cellular RF endpoint mismatch")
    for token in ("100 uF", "220 nF", "47 nF", "150 pF", "68 pF", "33 pF", "10 pF", "ferrite bead"):
        require(token in u8[32]["Required_Network"], f"U8 VBAT_BB authority lacks {token}")
    for token in ("100 uF", "100 nF", "33 pF", "10 pF", "0 Ohm link"):
        require(token in u8[52]["Required_Network"], f"U8 VBAT_RF authority lacks {token}")

    u16 = {index: cellular_by_key[("U16", str(index))] for index in range(1, 25)}
    expected_u16 = {
        1: ("U8_VDD_EXT_1V8", "SUPPLY_LOCKED"), 2: ("U8_VDD_EXT_1V8", "STRAP_DIRECT_HIGH"),
        3: ("U8_MAIN_TXD_1V8", "FUNCTION_LOCKED"), 4: ("U8_STATUS_1V8", "FUNCTION_LOCKED"),
        5: ("U8_MAIN_RI_1V8", "FUNCTION_LOCKED"), 6: ("GND_MODEM", "UNUSED_INPUT_DIRECT_LOW"),
        7: ("U8_MAIN_RXD_1V8", "FUNCTION_LOCKED"), 8: ("U8_MAIN_DTR_1V8", "FUNCTION_LOCKED"),
        9: ("NC", "UNUSED_OUTPUT_NC"), 10: ("NC", "UNUSED_OUTPUT_NC"),
        11: ("GND_MODEM", "STRAP_DIRECT_LOW"), 12: ("GND_MODEM", "GROUND_LOCKED"),
        13: ("GND_MODEM", "GROUND_LOCKED"), 14: ("GND_MODEM", "UNUSED_INPUT_DIRECT_LOW"),
        15: ("GND_MODEM", "UNUSED_INPUT_DIRECT_LOW"), 16: ("CELL_DTR", "FUNCTION_LOCKED"),
        17: ("CELL_TX", "FUNCTION_LOCKED"), 18: ("NC", "UNUSED_OUTPUT_NC"),
        19: ("CELL_RI", "FUNCTION_LOCKED"), 20: ("CELL_STATUS", "FUNCTION_LOCKED"),
        21: ("CELL_RX", "FUNCTION_LOCKED"), 22: ("GND_MODEM", "STRAP_DIRECT_LOW"),
        23: ("3V3_DIGITAL", "SUPPLY_LOCKED"), 24: ("3V3_DIGITAL", "SUPPLY_LOCKED"),
    }
    for pin, expected in expected_u16.items():
        require((u16[pin]["RevA_Net"], u16[pin]["Disposition"]) == expected, f"U16 pin {pin} net/disposition mismatch")
    require(all("100 nF" in u16[pin]["Required_Network"] for pin in (1, 23, 24)), "U16 bypass contract incomplete")

    for ref, command, collector in (("Q1", "CELL_PWRKEY_CMD", "U8_PWRKEY_N"), ("Q2", "CELL_RESET_N_CMD", "U8_RESET_N")):
        q = {pin: cellular_by_key[(ref, str(pin))] for pin in range(1, 4)}
        require((q[1]["Pin_Name"], q[2]["Pin_Name"], q[3]["Pin_Name"]) == ("B", "E", "C"), f"{ref} SOT23 pin order mismatch")
        require(command in q[1]["Required_Network"] and "4.7 kOhm" in q[1]["Required_Network"] and "47 kOhm" in q[1]["Required_Network"], f"{ref} base-drive network mismatch")
        require(q[2]["RevA_Net"] == "GND_MODEM" and q[3]["RevA_Net"] == collector, f"{ref} open-collector mapping mismatch")

    cellular_review = CELLULAR_REVIEW_PATH.read_text(encoding="utf-8")
    cellular_authority_sha256 = hashlib.sha256(CELLULAR_PIN_AUTHORITY_PATH.read_bytes()).hexdigest()
    for marker in {
        "CELLULAR_AUTHORITY_PASS / PCB REVIEW A NOT STARTED / NOT FOR MANUFACTURE",
        cellular_authority_sha256,
        "6ff03aa31577971d02dc15eac11adee4d52b80077ae3fa3503978c1b12496e81",
        "6cf4003c438c0546fb86f0932613896197dd19a75bdb307f385eb6e75535126e",
        "500-1000 ms", "650-1500 ms", "2-3.8 s", "AT+QPOWD", "150 mV", "below 75 mV",
        "controlled separately by `PCB_MAIN_DUAL_SIM_PIN_AUTHORITY_REV_A.csv`",
    }:
        require(marker in cellular_review, f"cellular authority review record missing marker: {marker}")

    dual_sim_rows = rows(DUAL_SIM_PIN_AUTHORITY_PATH)
    require(len(dual_sim_rows) == 55, f"expected 55 U13/U14/U15/J6/J7/Q3 authority rows, got {len(dual_sim_rows)}")
    require(all(set(row) == cellular_columns for row in dual_sim_rows), "dual-SIM pin-authority schema drift")
    require(
        all(all(row[column] is not None and row[column] != "" for column in cellular_columns) for row in dual_sim_rows),
        "dual-SIM pin-authority row contains an empty field",
    )
    dual_sim_by_key: dict[tuple[str, str], dict[str, str]] = {}
    for row in dual_sim_rows:
        key = (row["RefDes"], row["Pin"])
        require(key not in dual_sim_by_key, f"duplicate dual-SIM pin-authority row: {key[0]}.{key[1]}")
        dual_sim_by_key[key] = row
    dual_sim_identity = {
        "U13": ("TS3A27518EPWR", "TSSOP-24_PW", {str(index) for index in range(1, 25)}),
        "U14": ("ESDALC6V1-5P6", "SOT666_1.6x1.6mm", {str(index) for index in range(1, 7)}),
        "U15": ("ESDALC6V1-5P6", "SOT666_1.6x1.6mm", {str(index) for index in range(1, 7)}),
        "J6": ("2336582-1", "TE_NanoSIM_H1.37", {str(index) for index in range(1, 8)} | {"SHIELD"}),
        "J7": ("2336582-1", "TE_NanoSIM_H1.37", {str(index) for index in range(1, 8)} | {"SHIELD"}),
        "Q3": ("MMBT3904,215", "SOT23", {"1", "2", "3"}),
    }
    for ref, (mpn, package, expected_pins) in dual_sim_identity.items():
        actual = [row for row in dual_sim_rows if row["RefDes"] == ref]
        require({row["Pin"] for row in actual} == expected_pins, f"{ref} dual-SIM package-position set drift")
        require(all((row["MPN"], row["Package"]) == (mpn, package) for row in actual), f"{ref} dual-SIM identity/package mismatch")
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
